thebardchat/TrojanHorseAreana/blueprints/phase2/out/pdf/P2-A-301_RevD.pdf

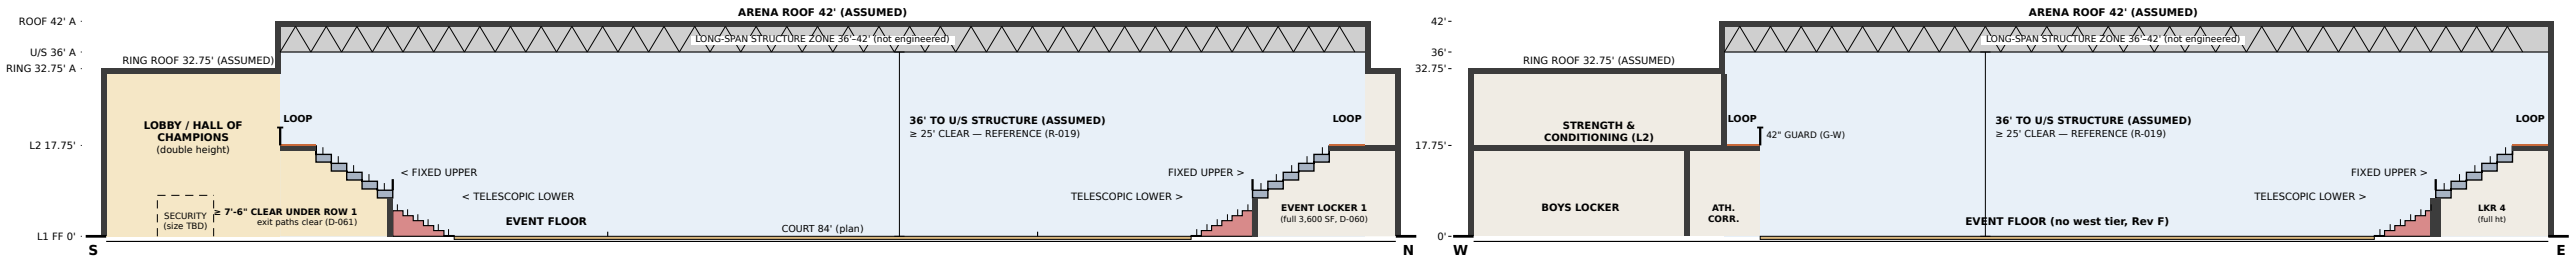
[picture p2: figure]
COURT 84' (plan) EVENT FLOOR; LOBBY / HALL OF CHAMPIONS (double height); SECURITY (size TBD); < TELESCOPIC LOWER; < FIXED UPPER; TELESCOPIC LOWER >; FIXED UPPER >; LOOP; EVENT LOCKER 1 (full 3,600 SF, D-060); ≥ 7'-6" CLEAR; UNDER ROW 1; exit paths clear (D-061); ARENA ROOF 42' (ASSUMED); RING ROOF 32.75' (ASSUMED); 36' TO U/S STRUCTURE (ASSUMED) ≥ 25' CLEAR — REFERENCE (R-019); RING 32.75' A; ROOF 42' A; EVENT FLOOR (no west tier, Rev F); BOYS LOCKER; ATH.; CORR.; STRENGTH & CONDITIONING (L2); LKR 4 (full ht); 42" GUARD (G-W)

# PRELIMINARY — CONCEPTUAL DESIGN — NOT FOR CONSTRUCTION

PROJECT

# Hazel Green Regional Athletic Complex Trojan Horse Arena · Hazel Green area, Madison County, Alabama (site TBD, D-006)

PHASE

# PHASE 2

SHEET TITLE

# BUILDING SECTIONS SCHEMATIC · COLOR

SCALE
AS

# NOTED

DATE

# October

2026

REV
D

DRAWN BY

## Drawn by KEYSTONE (AI) for Shane Brazelton

SHEET
P2-A-301

LONG-SPAN STRUCTURE ZONE 36'–42' (not engineered)

### 1 SECTION A-A (NORTH-SOUTH) — looking west

1/32" = 1'-0" · x = 100 (see key plan)

LONG-SPAN STRUCTURE ZONE 36'–42' (not engineered)

### 2 SECTION B-B (EAST-WEST) — looking north

1/32" = 1'-0" · y = 150 (see key plan)

L1 FF 0'

L2 17.75'

RING 32.75' A

U/S 36' A

ROOF 42' A

TELESCOPIC LOWER TIER (extended)

6 rows × 24" = 12' band (R-008 / plan)
rise 11⅝"/row — Hussey MAXAM option (CITED); choice of 11⅝" ASSUMED

top seat 6'-3⅛" (Hussey, 6 rows @ 11⅝")

closed 3'-6" (Hussey, 6 rows)

FIXED UPPER TIER (ASSUMED rake)

5 rows × 36" = 15' band (plan)
21"/row = 3 aisle risers × 7", 12" treads (IBC 1030.14.2: 4–8" risers, ≥ 11" treads) steps DOWN from the loop; front row 9.00'

≥ 26" fascia (1030.17.3)

LOOP 7'

2 × 42" lanes

top cross aisle

STRETCH
6' (L2)

NO LOW BAND (D-061, Option B): row 1 clear 7.5' = 7'-6" (1003.2,
no margin; 1.5' structure A)
rows 2–5 9.25'–14.5'

EVENT LOCKER 1 (full, D-060) from y 224 (tier line), A-101 Rev F

SIGHT LINES: P2-A-302 Rev C — 21"/row, L2 17'-9"

seated C min 149 mm N/S, 101 mm E (≥ 90 target)

EXIT (N) x 123.85–131.85: clear ≥ 7'-6" under row 1 (D-061)

1030.6.2.2 (only if smoke-protected): roof ≥ 15' above

highest aisle (loop 17.75') → ≥ 32.75'; 36' drawn

### 3 NORTH BOWL EDGE (ENLARGED PART OF A-A)

3/32" = 1'-0" · y 196–252 at x = 100

16 R @ 6.87" = 9.16'
15 T @ 11" = 13.75'

76" mid
landing

= width

(1011.6)

48" floor

landing

INTERMEDIATE HANDRAIL (C-7)

on the 76" centerline, 1014.9

— architect to confirm

L2 FF 17'-9"

+ flight 2: 15 R

L1 FF 0'

flight 2 beyond

(dashed)

31 risers total

76" clear width

(not visible in section)

### 4 TYPICAL EXIT STAIR — 76" CLEAR, 31 R

3/32" = 1'-0" · 76" mid landing · 12.67' × 24.08' plan (D-061)

A

A

B B

N

### 5 KEY PLAN — CUTS

1" = 128' · north up

CUT: slab / wall / roof (graphic) | ARENA VOLUME | EVENT FLOOR
TELESCOPIC LOWER TIER | FIXED UPPER TIER | LOOP (L2)
LOBBY | ROOMS / SUPPORT | LONG-SPAN STRUCTURE ZONE

HEIGHTS USED (ft above L1 FF 0'-0")
- L2 FF 17'-9" (D-061 DECIDED, Option B). Ring roof 32.75' = L2 + 15' — ASSUMED. Arena structure underside 36', roof 42' — ASSUMED (court clear unchanged).
- Arena clear ≥ 25' — REFERENCE (NFHS court specs via Draper; LA RAP gym standard; R-019), not a code minimum (C-5). 36' drawn = 11' over it.
- Slabs, walls, roof graphic only. Upper-tier deck structure 1.5' under each tread — ASSUMED.
SEATING (P2-A-101 Rev F)
- Lower: telescopic, 6 rows × 24", 11⅝" rise (Hussey MAXAM option, CITED; choice ASSUMED); east front 16' from the nearest mat (D-053); building 210' wide.
- Upper: fixed, 15' band, 5 rows × 36", 21"/row (D-061) = 3 aisle risers × 7", 12" treads (1030.14.2: 4–8", ≥ 11"); steps DOWN from the loop (D-049) to a 9.0' front row.
- UNDER THE UPPER TIER: row 1 clear 7.5' = 7'-6" (1003.2 minimum, no margin), rows 2–5 9.25'–14.5'. No low band: EXIT (N), EXIT (E), SE concourse, lobby / portal / athlete route are clear. Event lockers run to the tier line (3,600 SF, D-060).
- SIGHT LINES: P2-A-302 Rev C (21"/row, L2 17'-9"): seated C min 149 mm N/S, 101 mm E; standing 127 / 72 mm (lower tier governs).

GUARDS
- Loop open edges G-W (x = 56) and G-S (y = 34): 42" (IBC 2021 1015.2 / 1015.3). Upper-tier front fascia ≥ 26" (1030.17.3), 36" at aisle feet (1030.17.4).
STAIRS (ST-1..ST-4)
- 76" clear (D-052). 31 R @ 6.87" (213" ÷ 31, ≤ 7", 1011.5.2), flights 16 + 15, 15 treads × 11" = 13.75'; 76" intermediate landing = width (1011.6, D-051); 48" floor landings. Per stair 12.67' × 24.08' = 305.1 SF per level (Rev C 270.2).
- Intermediate handrail on the centerline of each 76" stair so all width is within 30" of a rail (IBC 2021 1014.9; D-052 'with intermediate handrails') — shown in detail 4; architect to confirm (C-7).
ROOF HEIGHT (1030.6.2.2, if smoke-protected)
- Lowest roof deck ≥ 15' above the highest aisle: loop 17.75' → ≥ 32.75'. Arena U/S structure 36' drawn = 3.25' margin (deck higher). Ring roof 32.75' is over the perimeter rooms, not the seating.
ELEVATOR
- EL-1 travel 17'-9" (was 15'); hoistway / pit / overrun by the elevator supplier (not drawn).
CUTS
- A-A: x = 100, looking west. B-B: y = 150, looking north. Geometry from P2-A-101/102 Rev F. Colors graphic only; 'A' = ASSUMED.
