thebardchat/TrojanHorseAreana/blueprints/DECISIONS.md

# DECISIONS — KEYSTONE

Status values: **OPEN** / **DECIDED** / **PARKED**.
When Shane answers, KEYSTONE records `DECIDED 2026-MM-DD — <answer> — "Shane, <channel>"` and updates the params file first.
Source for D-001…D-012: KEYSTONE_ARCHITECT_PROMPT.md v1.1 Section 5. D-013…D-015 logged by KEYSTONE at bootstrap, 2026-10-03. D-016…D-017 logged at the reference plan intake, 2026-10-03. D-009 DECIDED 2026-10-04 4:30 AM CT (Shane review of P2-A-101/102 Rev A).

## Phase 1 — existing wrestling room remodel

| ID | Question | Status | Notes / feeds |
|---|---|---|---|
| D-001 | Existing room dimensions, ceiling height, door locations, wall material (needs Shane's tape measure + photos) | OPEN | phase1.yaml `existing.*`. Checklist: phase1/MEASUREMENT_CHECKLIST.md. **Partial 2026-10-03:** wrestling room MEASURED: 55'-0" N-S × 45'-0" E-W inside, wall to wall, rectangle ("Shane tape, inside wall-to-wall, 2026-10-03") → `existing.wrestling_room.length_ft/width_ft`, drawn on P1-A-101 Rev A. The aerial estimate (≈55.1 × 46.9 ft exterior) agreed and stays a cross-check only. Door locations are APPROX. from the sketch only. **Still TBD:** support wing dims, door positions/widths, ceiling, wall material/thickness, photos. **10:12 PM CT (Shane):** ceiling 10'-0"; CMU building (8" walls ASSUMED unless noted); 4 doors ASSUMED standard 3'-0" × 7'-0" single HM, VERIFY (locations still APPROX.; south exit may be a pair). Dr. Headen has taken photos (copies requested) |
| D-002 | Where the plumbing fails, what fixtures exist, where water/drain lines run | OPEN | phase1.yaml `existing.plumbing`, work item W2. **Update 2026-10-03 (Shane, firsthand):** no running water to the area; all fixtures out of service; cause unknown. Still needed: plumber visit to diagnose (shutoff, supply line, or other), plus photos. **10:06 PM CT (Shane):** fixtures = 2 showers, 1 private toilet, 2 toilets, 1 urinal, sinks (count TBD), water fountain/sink, all out of service; problem spots = entire support wing (showers broken before the water loss); where = support wing east of the wrestling room, along the open hallway. Still TBD: cause, sink count, water/drain lines. **2026-10-04:** P1-P-001 Rev A shipped (scope narrative + fixture list only); does not close D-002 |
| D-003 | Which walls get pads, pad height, and whether pads are bought by the school, donated, or fundraised | DECIDED | DECIDED 2026-10-03 — Pad height 6 ft — "Shane, chat". This matches the R-001 guidance. Applied in phase1.yaml W1 `pad_height: 6 ft`. Earlier the same day the template came back unfilled, so 6 ft had only been proposed. **Which walls and who supplies the pads are not decided; they moved to D-021 (OPEN)** |
| D-004 | Who must approve work on school property (principal → district facilities → anyone else) | OPEN | phase1.yaml `approvals`. Legal/procurement advice is out of scope for KEYSTONE. **2026-10-03: R-002 + R-004 done.** Sources point to principal → MCSS Operations & Facilities → Board of Education (building/land improvements) → Alabama DCM review + inspections (any cost, any funding). Donated work: bid law may not apply to entirely private funds (AG opinions, via Examiners), but DCM review still does. **Needs district confirmation** before DECIDED |
| D-005 | Principal's name spelling (Headen or Hedden) | DECIDED | DECIDED 2026-10-03 — "Dr. Headen" — "Shane, firsthand 2026-10-03 10:12 PM CT". Stored in phase1.yaml `contacts.principal` (name, display_name). Used on P1-G-001 Rev D. Frozen Revs A/B/C unchanged |

## Phase 2 — new building + campus

| ID | Question | Status | Notes / feeds |
|---|---|---|---|
| D-006 | Site / parcel / address | OPEN | Campus drawn as SITE TBD diagram until decided |
| D-007 | Owner of record for the new building: Shane / Hazel Green Trojan Youth Wrestling / partnership | OPEN | Drives D-008 and R-006. **Updated 2026-10-03 10:45 PM CT (Shane):** Phase 2 is Shane's build, not a school project (D-028), so the school-system/county/town options were dropped from this question. phase2.yaml `open_items.owner_of_record` |
| D-008 | Authority Having Jurisdiction for permitting | OPEN | R-006. **R-006 done 2026-10-04 7:44 AM CT:** Hazel Green is unincorporated → Madison County Inspection Department (if the parcel stays outside city limits); county enforces 2018 IBC / IFC / NFPA 101 (no change planned within 12 months), State Fire Marshal 2021 IFC; DCM (State Building Code, 2021 IBC) covers private buildings only if 25+ persons regularly gather "for instruction" — ask DCM / county; assembly needs a registered architect. Still OPEN (site D-006 + pre-application meeting). **Note 2026-10-03 (P2-T-003b):** Madison County's Building Codes page lists the 2018 IBC/IPC (effective Jan 2021) for county permits; Shane said 2021. The test-fit used 2021; its fixture table reads the same in 2018. Depends on the site (D-006). **10:15 AM CT (reviewer C-6):** edition conflict still OPEN — county on 2018 codes vs State Fire Marshal 2021 (R-006). P1-G-001 Rev E prints '2021 ASSUMED, verify with AHJ' (plain words, no codes); Phase 2 sheets keep 2021 as ASSUMED until the AHJ answers |
| D-009 | Seating type (fixed, telescopic) and final count | DECIDED | DECIDED 2026-10-04 — MIX: telescopic lower tier, fixed upper tier — "Shane, firsthand, 4:30 AM CT". Total stays 2,200 (locked; D-016 label question still OPEN), seats on N, S, E only (west = lockers + athlete corridor), 50/50 tier split ASSUMED (1,100 + 1,100). phase2.yaml `spaces.seating.type` MIX, `lower_tier_type: telescopic`, `upper_tier_type: fixed` (locked in validate.py). P2-G-003 Rev E (Rev D frozen): telescopic 3.38 SF/seat lower, fixed 6.0 SF/seat upper, same 1.25 gross-up → L1 gross 51,108, L2 gross 25,981, footprint 51,130 (arena volume + L2 governs) = 3,870 SF under 55,000 (target ≥ 2,000 met); 77,089 GSF. Block box shrinks 250 × 220 → 204 × 252 ft = 51,408 SF (3,592 under the cap). Seats by side: N 353 + 308 = 661, S 341 + 308 = 649, E 406 + 484 = 890 (lower 1,100 + upper 1,100 = 2,200). Earlier note: concept sheet shows 2,200; diorama text "Permanent stadium seating" not treated as a decision; Rev D compared fixed 54,949 vs telescopic 50,868 |
| D-010 | Locker room parity (equal SF?) | OPEN | See D-013 |
| D-011 | Concessions scope | OPEN | |
| D-012 | Any budget target for Phase 2 | OPEN | Do not reuse the superseded Feb 2026 concept budget |

## Logged at bootstrap (2026-10-03)

| ID | Question | Status | Notes / feeds |
|---|---|---|---|
| D-013 | Girls locker 3,503 SF vs boys 3,500 SF. Real difference, or a drawing-tag slip? | OPEN | Prompt §3 says this is likely a tag slip. **Draw both lockers equal until Shane decides.** Also, the intake says AI renders show girls as 3,500 |
| D-014 | Mat size check: concept notes say "four 42-foot mats ≈ 7,000 SF." Check against current NFHS rules (mat, circle, safety area, spacing) before laying out mats | DECIDED | DECIDED 2026-10-03 — mats are 42' × 42' — "Shane, 10:45 PM CT". R-005: meets the NFHS 28 ft minimum circle + ~5 ft safety area. Applied in phase2.yaml `spaces.arena.mat_size`. Design events → D-029 |
| D-015 | The intake file `KEYSTONE_INTAKE_2026-10-03.md` starts with "MOVIE MAKER INTAKE," but everything in it is for KEYSTONE. Label slip? | OPEN | KEYSTONE treated the content as its own intake. Shane, please confirm |

## Logged at reference plan intake (2026-10-03)

| ID | Question | Status | Notes / feeds |
|---|---|---|---|
| D-016 | Reference plan seating labels: north bank 3,200, south bank 2,200. Locked: 2,200 total (Shane 2026-10-03). Which label is wrong, and is 2,200 the total or per bank? | OPEN | phase2.yaml `spaces.seating`. The reference plan legend also says "Arena Capacity: 2,200 Spectators." The tabletop render swaps the two labels. Keep 2,200 total until Shane answers |
| D-017 | Which image is the Phase 2 reference plan, and what may be taken from it? | DECIDED | DECIDED 2026-10-03 — Phase 2 reference plan = Phase2-floor-plan-flat.png; use zones, adjacencies, 5 SF tags, room list; ignore dimension strings, scale bar, garbled text, green/gold legend — "Shane, chat". Diorama demoted to secondary; `Phase2-floor-plan.jpeg` is presentation only, not a source |
| D-018 | Promote rooftop solar + stormwater storage into Phase 2? Retractable roof? | DECIDED | DECIDED 2026-10-03 — Solar + stormwater storage promoted to Phase 2 as design intent only (no sizes, panel counts, or gallons until a cited R-file sizes them for this building). Retractable roof CUT. — "CHANGE APPROVED", Shane, chat. Applied in phase2.yaml `sustainability` |

## Logged at R-001/R-003 approval (2026-10-03)

| ID | Question | Status | Notes / feeds |
|---|---|---|---|
| D-019 | Must both new athlete restrooms (1 male + 1 female, single-user) meet full 2010 ADA, or only some (2010 ADA 213.2 Exception 4)? | DECIDED | DECIDED 2026-10-03 — Full 2010 ADA compliance on BOTH new restrooms — "Shane, chat". Resolves the R-003 Exception 4 question. Applied in phase1.yaml W3 + `standards.ada_single_user_restroom.both_rooms_comply` |
| D-020 | Wall pad fire-test wording on the scope sheet | DECIDED | DECIDED 2026-10-03 — Scope sheet must include, verbatim: "Wall pads must have an NFPA 286 assembly test report — not a foam-only rating. Ask the vendor before purchase." — "Shane, chat". Applied in phase1.yaml W1 `purchase_note` (basis: R-001) |
| D-021 | Which walls get pads, and whether pads are bought by the school, donated, or fundraised (the rest of D-003 after pad height was decided) | OPEN | Split from D-003 on 2026-10-03. phase1.yaml W1 `walls`, `supplied_by`, `funding.pad_funding`. Walls need Shane's measurements + photos (D-001). 2026-10-03: Shane's pad estimate (revised 10:12 PM CT: ~188 LF after 4 doors, ~94 panels at 2×6 ft) assumes all 4 walls; which walls is still OPEN |
| D-022 | Split Phase 1 into 1A (wall pads — may be maintenance, ask facilities) and 1B (plumbing + restrooms — licensed designer + DCM review likely)? | OPEN | Logged 2026-10-03 at Shane's request ("Shane, chat"). Do NOT restructure backlog, params, or sheets until Shane decides. Feeds from R-002/R-004 |
| D-023 | Is P1-G-001 Rev B approved for the principal, and does Shane's contact info stay on it in the public repo? | DECIDED | DECIDED 2026-10-03 — Rev B approved as-is; contact info stays (already public); no history rewrite — "Shane, chat" |
| D-024 | Priority order of the three Phase 1 work items | DECIDED | DECIDED 2026-10-03 — W2 (restore water) first → W3 (restroom split) second → W1 (wall pads) third; W1 can run in parallel because it doesn't depend on water — "Shane, firsthand 2026-10-03". Applied as phase1.yaml `work_items[].priority` and on P1-G-001 Rev C. Does not decide D-022 (1A/1B split) |
| D-025 | Is P1-G-001 Rev D (principal version) approved? | DECIDED | DECIDED 2026-10-03 — Rev D approved — "Shane, 10:29 PM CT". Frozen (`frozen: true`); committed PDF/DXF unchanged. Bundled first in Phase1_Package_for_Dr_Headen.pdf |
| D-026 | Is P1-A-101 Rev A (existing conditions, room outline) approved, and are the door marks right? | DECIDED | DECIDED 2026-10-03 — Rev A approved; door locations match Shane's markup; exits swing out (correct) — "Shane, 10:29 PM CT". Hallway door swing and south exit single/pair were left unfilled → stay "assumed, verify" (no sheet change). Frozen; committed PDF/DXF unchanged |

## Logged 2026-10-03 10:45 PM CT (Phase 2 active)

| ID | Question | Status | Notes / feeds |
|---|---|---|---|
| D-027 | Does Phase 2 wait for Phase 1 to finish? | DECIDED | DECIDED 2026-10-03 — Phase 2 is ACTIVE now, in parallel with Phase 1. Phase 1 package delivered; Phase 1 waits on Dr. Headen. When Shane brings Phase 1 data, Phase 1 tickets jump the line (Phase 1 still outranks when its data exists) — "Shane, 10:45 PM CT". Applied in BACKLOG priority note, STATUS, README, phase2.yaml meta |
| D-028 | Is Phase 2 a school project? | DECIDED | DECIDED 2026-10-03 — No. Phase 2 is Shane's build; it may not involve Dr. Headen. No school ownership, district approval, school review or school bidding is assumed for Phase 2 — "Shane, 10:45 PM CT". Owner of record stays OPEN (D-007). phase2.yaml had no school-derived entries to remove; locked facts kept |
| D-029 | What events is the Phase 2 arena designed for? | DECIDED | DECIDED 2026-10-03 — home duals + AHSAA / regional tournaments — "Shane, 10:45 PM CT". phase2.yaml `spaces.arena.design_events` |
| D-030 | Program direction (two levels, footprint cap D-031). Shane's direction under study (11:26 PM CT): keep ≈ 2,200 spectators with rentable suites just above the top seats. P2-G-003 Rev C (base inputs): at the locked 22,000 SF floor, suites cannot reach 2,200 inside 55,000 (most that fits ≈ 1,640 = 1,180 bowl + 23 suites × 20); an 18,000 SF floor fits 1,940 bowl + 13-22 suites (12-20 guests) ≈ 2,200, footprint ≈ 54,994, ≈ 92,300-92,900 GSF, 3 levels (suite level). Which way: a) 18,000 SF floor + suites (3 levels), b) 16,400 SF floor, all 2,200 in the bowl, no suites (2 levels), c) keep 22,000 SF on lean inputs (telescopic lower tier), no suites (2 levels), or d) another mix? | DECIDED | DECIDED 2026-10-03 — 16,400 SF event floor, all 2,200 seats in the bowl, 2 levels, no suites — "Shane, firsthand, 11:39 PM CT". Suites → PARKING_LOT (future add-on, study after attendance is proven). Seating type (fixed vs telescopic) stays OPEN (D-009); plans show both as an overlay. phase2.yaml locked: `spaces.arena.event_floor_sf: 16400` (drawn 114 × 144 ft = 16,416), 4 × 42 ft mats 2 × 2 (`mat_ft`, `mat_layout`), `seating.bowl: 2200`, `building.levels: 2`, S&C + cross-training `level: 2` over the lockers; the 22,000 SF tag is SUPERSEDED for the event floor and kept as history (`sf_tagged_superseded`). P2-G-003 Rev D = LOCKED PROGRAM sheet (Rev C frozen). Feeds P2-T-004 (P2-A-101 Level 1, P2-A-102 Level 2) |

## Logged 2026-10-03 11:09 PM CT

| ID | Question | Status | Notes / feeds |
|---|---|---|---|
| D-031 | Is the 55,000 SF a cap on total floor area or on the building footprint? | SUPERSEDED | **RETIRED 2026-10-04 by D-056 — there is NO 55,000 SF cap (footprint or total); 55,000 SF was an early rough estimate, not a limit ("Shane, Grok chat", 8:36 AM CT).** History: DECIDED 2026-10-03 — 55,000 SF is a FOOTPRINT cap that could allow two levels; it is not a total floor area cap — "Shane, firsthand, 11:09 PM CT". phase2.yaml `building.footprint_cap_sf: 55000`, `levels: up to 2`, `total_gsf_cap: none` (locked `total_sf: 55000` kept, meaning noted). Test-fit redone as P2-G-003 Rev B; Rev A frozen. D-030 stays OPEN |

## Logged 2026-10-03 11:26 PM CT

| ID | Question | Status | Notes / feeds |
|---|---|---|---|
| D-032 | Keep the 22,000 SF floor and drop to ≈ 1,370 seats (P2-G-003 Rev B option)? | DECIDED | DECIDED 2026-10-03 — No. Shane rejects the ≈ 1,370-seat option ("not enough") — "Shane, firsthand, 11:26 PM CT". His direction (suites just above the top seats to keep ≈ 2,200 spectators) is recorded under D-030, which stays OPEN until he picks. phase2.yaml `spaces.seating.rejected_option`, `suites_direction` |

## Logged 2026-10-04 4:43 AM CT

| ID | Question | Status | Notes / feeds |
|---|---|---|---|
| D-033 | Access control: how do people (public, teams, staff) enter the arena? | DECIDED | DECIDED 2026-10-04 — single controlled entry point for all people (public, teams, staff): "Everyone passes through the grand entrance; it will serve as a checkpoint, a security feature." — "Shane, firsthand, 4:43 AM CT". phase2.yaml `spaces.entry.access_control` (v7). P2-A-101/102 Rev C (Rev B frozen): SW team / service entry removed; SECURITY CHECKPOINT (size TBD, ASSUMED) between the vestibule and lobby; CD-1 controlled door off the lobby → athlete route → team assembly / athlete corridor / lockers; all other perimeter doors X1-X10 EXIT ONLY — alarmed, no exterior entry hardware (IBC 2021 1010.2, 1010.2.7 exc. 1, 1010.2.9; 2018 1010.1.9, 1010.1.10; no delayed egress in Group A, 1010.2.13). Exits kept per R-015 / R-015.6: 4 per story (T1006.3.3), main exit ≥ 1/2 occupant load (1030.2), other exits ≥ 1/2 (1030.3); checkpoint may not narrow the main exit (1003.6, 1010.5). Program unchanged (P2-G-003 Rev E stands) |
| D-034 | Deliveries and team buses under the single-entry rule (D-033): where do trucks unload mats / equipment and concessions, and where do team buses drop athletes and gear? Rev C shows S1 SERVICE / LOADING at equipment storage (north wall) — staff-controlled, not a people entrance — and teams walking in through the grand entrance. Options: a) staff-only service door as drawn, deliveries scheduled outside event hours; b) a screened service / loading entrance with its own checkpoint; c) other | DECIDED | **DECIDED 2026-10-04 (default, refine on the site plan)** — service / deliveries at the **north door S1** (staff-controlled service door, option a); **team / bus drop loop on the SOUTH**, offset **east or west** of the entry axis so it does not block the view of the Grand Entrance Portal — "Shane, firsthand, 6:45 AM CT". Side (E or W), loop size and lanes TBD on the site plan (C-101, P2-T-006; site TBD, D-006). Logged in `phase2.yaml approach.site_access`. Earlier note: no sizes set (dock, door, apron, bus lane all TBD; site TBD, D-006). Feeds P2-A-101 (S1), C-101 campus diagram (P2-T-006), D-011 concessions scope |

## Logged 2026-10-04 4:55 AM CT

| ID | Question | Status | Notes / feeds |
|---|---|---|---|
| D-035 | Should Level 2 have a complete, continuous walkway / running-training loop around the top, and what gives up space for it? | DECIDED | DECIDED 2026-10-04 — continuous L2 running / training loop joining the rear walkway (N), walkway (E) and upper concourse / hall of champions balcony (S); S&C and cross-training reduced to fit — "Shane, firsthand, 4:55 AM CT". Shane wrote "eastside", but rooms 17 and 18 sit on the west, so the new leg runs along their arena-side (east) edge. phase2.yaml v8: `spaces.strength_conditioning.sf` 6,000 → **5,224**, `spaces.cross_training.sf` 4,000 → **3,500** (old values kept as `sf_tagged_superseded` for frozen revisions), new `spaces.training_loop`. Loop = 2 lanes x 42 in = 7 ft all around (lane width UFC 4-740-02N 4.1.7 / Athletic Business, R-017; 2 lanes ASSUMED, guides prefer 3), squared corners, 706 ft centerline, 7.48 laps/mile, 4,942 SF. 42 in guards at open edges (IBC 2021 1015.2, 1015.3). Event days: upper concourse (spectators cross at tier entries). P2-A-101/102 Rev D (ST-1 3.55 ft W, ST-2 into a 19 x 5 ft NE stair tower, elevator 1 ft S); P2-G-003 Rev F footprint 52,738, margin 2,262, 78,784 GSF |

## Logged 2026-10-04 5:27 AM CT

| ID | Question | Status | Notes / feeds |
|---|---|---|---|
| D-036 | Are P2-A-101/102 Rev D and P2-G-003 Rev F approved as the Phase 2 schematic baseline? | DECIDED | DECIDED 2026-10-04 — "P2-A-101/102 Rev D + P2-G-003 Rev F approved. Entry south-center, mech off the public side, mixed seating, 2,262 margin — all good." — "Shane, firsthand, 5:27 AM CT". Frozen as **Phase 2 Schematic Set Rev A** (phase2.yaml `sets.phase2_schematic_set_rev_a`; bundle `phase2/out/pdf/Phase2_Schematic_Set_RevA.pdf`, `p2_set.py`; git tag `p2-schematic-revA`). P2-A-101 Rev D was re-issued label-only for D-039 before the freeze. Confirms D-009 (MIX), D-033 (south-center entry), footprint margin 2,262 SF (P2-G-003 Rev F). |
| D-037 | Level 2 running / training loop width | DECIDED | DECIDED 2026-10-04 "for now" — 2 lanes x 42 in = 7 ft (D-035 geometry unchanged) — "Shane, firsthand, 5:27 AM CT". Revisit only through D-038. |
| D-038 | Upper concourse width vs egress calc — if code requires wider, go to 3 lanes (10.5 ft). | DECIDED | **CLOSED 2026-10-04 — exit stairs 70 in clear** (each of ST-1..ST-4) — "Shane, firsthand, 6:45 AM CT". R-018.8 recheck at 70 in: 4 x 70 = 280 in vs 255.8 in base (+24.2), 275.6 in with the loop counted (+4.4), 272.6 in with rail standing (+7.4); both together 292.4 in (12.4 in short — AHJ / architect). Loop stays 7 ft (2 lanes, D-037). Affects **P2-A-101 / P2-A-102 at their next revision** (stair ≈ 11.67 x 19 ft, ≈ +16.5 SF per stair per level); the frozen Phase 2 Schematic Set Rev A stays frozen. Shown on P2-A-301 Rev A (typical stair). Earlier note: opened by Shane 2026-10-04 5:27 AM CT. R-018 (IBC 2021 Ch. 10 via UpCodes; 2018 = 1029.x, UNVERIFIED): L2 load 1,279; loop at 0.2 in/occupant needs 64 in (balanced, 1030.9.2) / 79.2 in (unbalanced check) vs 84 in drawn → **code does not require > 7 ft on KEYSTONE's calc**; 10.5 ft (126 in) would also satisfy it. Thin margin: keep the 7 ft clear, recess room doors. Stairs 4 x 64 in = zero slack (≈ 68-69 in if the AHJ counts the loop or rail standing). Needs architect egress model + AHJ (D-008). Frozen set unchanged. |
| D-039 | West unprogrammed space on Level 1 (team assembly ≈ 2,072 SF, storage SW 1,011 SF): keep or change? | DECIDED | DECIDED 2026-10-04 — keep as-is, labeled FLEX — "Shane, 5:27 AM CT". His message left the template bracket "keep as-is, labeled flex — [or: change to ___]"; KEYSTONE took the stated default (KEEP AS-IS) and did not invent a change. Labels: "FLEX / TEAM ASSEMBLY", "FLEX / STORAGE" (P2-A-101 Rev D label-only re-issue before the freeze; geometry, areas and DXF non-text entities unchanged). |
| D-040 | Brand / signage on the south portal and arena faces: does the Hazel Green High School (HGHS) badge belong, or Shane's own complex brand? | DECIDED | Opened by KEYSTONE 2026-10-04 for P2-A-201. Phase 2 is Shane's build, not a school project (D-028), so no school logo is drawn; placeholder "BRAND / SIGNAGE — TBD" in brand red / black. Portal look (limestone arch, crimson inside the arch, gold soffit) from Shane's MOVIE MAKER arch render (`/workspace/trojan-horse-arena/assets/arch_src.png`, box only). Needs Shane. **CLOSED 2026-10-04 6:16 AM CT by D-041:** the portal carries the official Trojan Horse Arena mark, not the HGHS badge (Shane, firsthand). |

## Logged 2026-10-04 6:16 AM CT

| ID | Question | Status | Notes / feeds |
|---|---|---|---|
| D-041 | What is the official Trojan Horse Arena mark? | DECIDED | DECIDED 2026-10-04 — "OFFICIAL MARK — circular horse-head badge with Greek key border." — "Shane, firsthand, 6:16 AM CT". Files: `brand/THA_logo_black.svg` (#1A1A1A), `brand/THA_logo_red.svg` (#CC0000), `brand/THA_logo_white.svg` (#FFFFFF) — copies of his Desktop\ARENA THA_logo_*.svg, colour identified by fill; sha256 in ASSETS. **Supersedes logo Concepts 01 / 02** (kept as history, marked SUPERSEDED, nothing deleted; those concept files are not in the repo or on the KEYSTONE box). Closes D-040: the portal carries this mark, not the HGHS badge. phase2.yaml `brand.official_mark` (v10). P2-A-201 Rev B (Rev A frozen): mark Ø 6 ft above the arch + TROJAN HORSE ARENA wordmark + side panel "Hazel Green Regional Athletic Complex" (sizes ASSUMED). |
| D-042 | Trademark search before signage / apparel. | OPEN | Opened by Shane 2026-10-04 6:16 AM CT. Clearance search for the Trojan Horse Arena name and mark before any signage, apparel or merchandise is produced (Shane / his attorney; KEYSTONE gives no legal advice). Feeds P2-A-201 signage, any brand use. |

## Logged 2026-10-04 6:22 AM CT

| ID | Question | Status | Notes / feeds |
|---|---|---|---|
| D-043 | Is the Grand Entrance Portal attached to the building, and what is the approach? | DECIDED | DECIDED 2026-10-04 — the Grand Entrance Portal is a **FREESTANDING** structure, not attached to the building; it sits just before the south entrance, on the way in, straddling the **Champion Walk** walkway; the walkway is **brick** so sponsors / donors can have their names on engraved bricks — "Shane, firsthand, 6:22 AM CT". Reference photo `references/portal_freestanding_champion_walk_ref.png` (freestanding limestone arch, crimson soffit, paved promenade, low walls / planters; sha256 in ASSETS). P2-A-201 Rev B: portal drawn free in front of the south entrance (gap 30 ft and depth 6 ft ASSUMED, labeled), Champion Walk brick paving + key plan, note "Engraved donor / sponsor bricks". **Next A-101 revision must add the portal + Champion Walk to the site / Level 1 plan** — not done now: P2-A-101 Rev D stays frozen in Phase 2 Schematic Set Rev A. |
| D-044 | Champion Walk: length, width, and donor-brick program details (brick sizes, engraving, pricing tiers, who administers, layout). | OPEN | **Narrowed 2026-10-04 6:45 AM CT to PRICING (and who administers / engraving):** dimensions and brick tiers are DECIDED in D-046 (28 x 30 ft, 4x8 single name / 8x8 family-business). Pricing TBD (Shane). Earlier note: opened 2026-10-04 6:22 AM CT (Shane's instruction). Drawn width 28 ft (= arch opening) is ASSUMED; length TBD; portal setback TBD (30 ft ASSUMED on P2-A-201 Rev B). Needs Shane; then the site plan (next A-101 revision). **Input 2026-10-04 7:24 AM CT:** Shane's vendor cost sheet (PDF "Champion_Walk_Brick_Pricing", 2026 prices incl. engraving + shipping, pulled 2026-10-04; not re-verified by KEYSTONE): average **$19.17 per 4x8** (Fundraising Brick $19.00, Polar Engraving $19.50, That's My Brick $19.00 at 101+) and **$29.50 per 8x8** ($30.00 / $27.50 / $31.00); logo +$6. KEYSTONE arithmetic: ~3,700 x $19.17 ≈ **$70.9k** vendor cost if all 4x8 — excludes install and the sand / concrete base (Phase 2 site work). Donor pricing still OPEN. **10:18 AM CT: R-023** vendor cost only (Shane's sheet, REFERENCE): all 4x8 3,780 = $71,820–$73,710; all 8x8 1,890 = $51,975–$58,590; 80/20 by area (ASSUMED) 3,402 = $68,796–$69,363; logo +$6 each. Break-even 4x8 $19.00–$19.50, 8x8 $27.50–$31.00 (vendor cost only). Install, base, border not included / not estimated. Pricing stays OPEN |

## Logged 2026-10-04 6:45 AM CT

| ID | Question | Status | Notes / feeds |
|---|---|---|---|
| D-045 | Grand Entrance Portal arch underside: crimson or gold? | DECIDED | DECIDED 2026-10-04 — **arch underside crimson + gold trim, as drawn** on P2-A-201 Rev B — "Shane, firsthand, 6:45 AM CT". Kept on Rev C. Finish / material TBD. |
| D-046 | Champion Walk size and brick tiers | DECIDED | DECIDED 2026-10-04 "for now" — **28 ft wide x 30 ft long (portal to the E1 doors) = 840 SF**; brick tiers **4x8 = single name**, **8x8 = family / business**; pricing TBD (D-044) — "Shane, firsthand, 6:45 AM CT". Capacity ≈ **3,700 4x8 bricks**: basis 840 SF ÷ 0.222 SF (4 x 8 in = 32 sq in) = 3,780 gross, less border / edging and joints (nominal face size; no border width set — about 2 % off gives ~3,700; ASSUMED). Any 8x8 brick takes the place of two 4x8. Option to **extend the walk to the parking later** (dashed on the key plan). Portal stands 30 ft in front of the doors (= walk length). Shown on P2-A-201 Rev C key plan + notes. **Next A-101 revision adds the walk + portal to the site / Level 1 plan.** |
| D-047 | Portal badge size (Shane picked from the 10-12 ft range) | DECIDED | DECIDED 2026-10-04 — **official mark 11 ft diameter** on the portal, wordmark to match, nothing may overflow — "Shane, firsthand, 6:45 AM CT". KEYSTONE fit (P2-A-201 Rev C): badge 40.4-51.4 ft above grade; to fit it with the wordmark above it inside the 44 ft wide portal, the **portal / attic was raised 50 → 56 ft (ASSUMED)** [superseded 7:24 AM CT by D-050: portal ≤ 50 ft, crown lowered to 34 ft] (attic band 42-56 ft; width 44, opening 28, springline 26, crown 40 unchanged). Wordmark caps 27 in (was 18 in): proportional scaling (2.75 ft caps) would make the line 47.9 ft, wider than the 44 ft portal, so caps are held at 27 in (39.1 ft line). Confirm the 56 ft height. |
| D-048 | Arch reference photo (`portal_freestanding_champion_walk_ref.png`): AI-made (keep in the repo) or from the internet (remove)? | DECIDED | **CLOSED 2026-10-04 7:24 AM CT — Shane made the image himself (rights clear); the removal stands, no history rewrite; kept off-repo by choice** — "Shane, firsthand, 7:24 AM CT". ASSETS: "Shane's own image; held off-repo by choice" (box copy unchanged, same sha256). Earlier note: Opened 2026-10-04 6:45 AM CT — Shane's answer came back as the unfilled template bracket. Safe default applied: **removed from the repo** (`git rm`, history not rewritten — the file stays in earlier commits of this public repo) and **held off-repo pending rights confirmation from Shane** (box copy `/workspace/keystone_previews/refs/`, sha256 in ASSETS). If AI-made → restore to `references/`; if from the internet → stays off-repo (rights / licence needed before any use). |

## Logged 2026-10-04 7:24 AM CT

| ID | Question | Status | Notes / feeds |
|---|---|---|---|
| D-049 | Upper tier rake direction and the use of the space under it | DECIDED | DECIDED 2026-10-04 — **the upper tier steps DOWN from the L2 loop toward the court, as drawn** (P2-A-301). **Under its low front edge: telescopic stack, storage, mechanical. Lockers only where headroom is full** — "Shane, firsthand, 7:24 AM CT". KEYSTONE reading (ASSUMED): "full headroom" = under the flat L2 slab behind the tier back line. Frozen Rev D plan overlaps under the tier (SF under tier / full-height SF): Event Lockers 1–2 482 / 418 each, 3–4 614 / 286 each; Mech E 1,173, Mech N 315, Equip storage 375, Equip room 161 (fine); lobby 870, concession 225, women's RR 207, athlete route 224, Conc W 196, Conc E 480; EXIT N and EXIT E passages 120 each (need ≥ 7'-6", 1003.2 → front structure ≤ 20 in at 9.17 ft, or a local raise). **Event lockers re-planned at the next A-101/A-102 revision.** Stack check (P2-A-302, R-020): a closed stack recessed under the front fits only if the structure is ≤ 32.6 in, and when open its rear rows sit under the overhang with < 7'-6" → **keep the stack in front of the tier face**; the low zone = storage / mech. |
| D-050 | Portal height cap and arch | DECIDED | DECIDED 2026-10-04 — **portal must NOT exceed 50 ft** (arena roof 42 ft); lower the arch crown 40 → ~34 ft, springline proportional (ASSUMED) so the 11 ft badge + wordmark fit — "Shane, firsthand, 7:24 AM CT". Supersedes D-047's 56 ft raise (badge stays 11 ft). P2-A-201 Rev D: **portal 50 ft**, crown **34 ft**, springline **22.1 ft** (26 x 34/40), semi-elliptical arch rise 11.9 ft over the 28 ft opening (ASSUMED; a semicircle with a 34 ft crown would need a 20 ft springline), attic band 36–50 ft, **badge 34.4–45.4 ft**, wordmark 27 in caps **baseline 46.1 ft, caps top 48.35 ft**, under the 48.8–50 ft cornice. |
| D-051 | Switchback stair intermediate landing depth | DECIDED | DECIDED 2026-10-04 — **intermediate landing ≥ stair width = 70 in** (IBC 2021 1011.6) — "Shane, firsthand, 7:24 AM CT". Floor landings 48 in. Per stair per level (clear): **11.67 ft x 20.83 ft = 243.1 SF** (2 x 70 in by 48 + 132 + 70 in; Shane's estimate ~11.67 x ~21 ft) vs **205.2 SF** in the frozen A-101/A-102 (10.8 x 19 ft) → **+37.9 SF per stair per level, +151.4 SF per level, ≈ +303 GSF** (4 stairs x 2 levels) — **apply at the next A-101/A-102 revision**. P2-A-301 Rev B detail 4. Supersedes the 221.7 SF estimate in R-018.8 (48 in landing). |
| D-052 | Egress worst case (loop counted + rail standing, 1,462 occupants → 292.4 in at 0.2 in/occ., IBC 2021 1005.3.1 exc. 1): how to add 12.4 in? | DECIDED | **DECIDED 2026-10-04 7:49 AM CT — 4 exit stairs at 76 in clear with intermediate handrails** (worst case passes: 304 in vs 292.4, ≈ 11.6 in spare; ≈ 12.67 x 21.33 ft per stair per level) — "Shane, firsthand, 7:49 AM CT". **Applies at the next A-101/A-102/A-301 revision** (frozen sheets stay frozen); shown on P2-C-101 Rev A. Earlier note: **PROPOSED by KEYSTONE 2026-10-04 7:24 AM CT (Shane asked for a recommendation, R-018.9): four stairs at 76 in clear** with intermediate handrails (1014.9) → 304 in (+11.6 in spare, serves 1,520); each ≈ 12.67 x 21.33 ft = 270.2 SF per level, **+217.8 GSF vs 70 in** (≈ +520 GSF vs the frozen plan). Alternatives: 74 in (296 in, +3.6 in, +144 GSF); 78 in (312 in, +291 GSF); a **5th stair** at 44 in (324 in, +273.8 GSF plus a new core, exit door, discharge, separation / travel checks; at 70 in +486 GSF); operational (no rail standing: 275.6 in, passes by 4.4 in — not worst case). Plans not redrawn. Needs Shane; architect / AHJ confirm. |
| D-053 | Sight lines: upper tier fails (14 in risers) and the east side fails (10 ft focal) — which fix? | DECIDED | **DECIDED 2026-10-04 7:44 AM CT — APPROVED: upper-tier risers 19 in (front row 7.08 ft) AND east seats moved 6 ft further from the mats (+≈1,512 SF)** — "Shane, firsthand, 7:44 AM CT". **Applies at the next A-101/A-102/A-301 revision** (frozen sheets stay frozen). Size with the shift + 76 in stairs (D-052), drawn basis: **L1 footprint 53,026.7 / L2 28,878.7 / TOTAL GSF 81,905.3 SF** (R-021); program-basis estimate 54,588.9 SF footprint. (Margin language retired by D-056.) Earlier note: **PROPOSED by KEYSTONE 2026-10-04 7:24 AM CT (P2-A-302 Rev A, R-020): upper riser 19 in per row** (3 aisle risers of 6⅓ in; front row drops 9.17 → 7.08 ft, back stays at the loop) **+ move the east tier 6 ft further from the mats (10 → 16 ft clear)** → every seated row ≥ 101 mm (PASS ≥ 90), standing ≥ 72 (east marginal). As drawn: upper seated 40–49 mm N/S, negative east; east lower 46–74 seated. Cost: +6 ft east-west ≈ +1,512 SF footprint (still < 55,000) or take 6 ft from the east support zone; the lower front makes exits under the tier front harder (7'-6", D-049). Alternatives: accept lower C on the east side; 16 in upper (passes N/S only). Needs Shane before more seating detail. |

## Logged 2026-10-04 7:44 AM CT

| ID | Question | Status | Notes / feeds |
|---|---|---|---|
| D-054 | Event floor uses beyond sports (concerts, graduations, expos with floor chairs or standing)? | DECIDED | Opened by KEYSTONE 2026-10-04 (R-007.2). The floor (114 x 144 ft = 16,416 SF) is counted at 50 gross ("exercise rooms", ASSUMED) → 329 occupants. IBC 2021 Table 1004.5 if used otherwise: unconcentrated 15 net → 1,095; chairs only 7 net → 2,346; standing 5 net → 3,284. Changes Level 1 exits / main exit (1030.2) and fixtures, not the L2 stairs (D-052). Needs Shane (intended uses); the building official assigns the load. **2026-10-04 10:48 AM CT (Shane): design L1 exits to PASS the worst case (standing), other cases shown alongside.** P2-G-002 Rev A finding: with door widths ASSUMED (11 pairs × 64 in = 704 in), the worst case is SHORT (total 933.0 in, main exit E1 466.5 in vs 64 in). Options 1 (E1 bank of 8 pairs) / 2 (distributed exits, +4 pairs) in G-002 §10. L1 fixtures in the standing case: 26 men's / 50 women's WC (vs 10 / 18). Still OPEN. **2026-10-04 11:07 AM CT (Shane): DECIDED — Level 1 exits Option 1: an 8-pair door bank at E1 across the lobby's 58 ft south wall (512 in clear, 64 in per pair ASSUMED); keep the single controlled entry (D-033).** Exits are sized for the standing worst case: P2-A-111 Rev A — total 1,152 in vs 933.0 needed, E1 512 vs 466.5 (1030.2), other L1 exits 420.7 vs 356.8 (1030.3), lose E1 640 vs 466.5 (1005.5): all PASS; whole drawn floor zone 17,280 SF standing also passes (E1 479.4). Drawn on P2-A-101 Rev G (vestibule widened, first aid moved, ASSUMED). Floor use itself stays OPEN; findings D-064 (restrooms) and D-065 (checkpoint). **2026-10-04 1:22 PM CT (Shane): DECIDED — event floor = CHAIRS-ONLY (7 net, 16,416 SF → 2,346 on the floor): graduations, banquets, expos yes; no standing-concert design. Keep the L1 exits as drawn for standing (extra margin, no change).** Design case = chairs (L1 3,827 incl. the 7-occupant storage annex + L2 1,462 = 5,289; E1 needs 396.7 in vs 512; standing margin case 6,227 → 467.0 in). Post the occupant load per configuration (IBC 2021 1004.9): sports 329 / tables 1,095 / chairs 2,346 on the floor. P2-G-002 Rev B, P2-A-111 Rev B, P2-A-103 Rev B. |

## Logged 2026-10-04 8:14 AM CT

| ID | Question | Status | Notes / feeds |
|---|---|---|---|
| D-055 | KEYSTONE prompt v1.3 (8:13 AM CT) text vs today's decisions — which wins? | DECIDED | **DECIDED 2026-10-04 — "Shane, Grok chat" (CHANGE APPROVED 8:14 AM CT): today's decisions win over v1.3 text:** 76 in stairs (D-052); 50 ft portal (D-050); upper tier steps down (D-049); D-048 closed; D-053 applied; ~~the 55,000 SF cap applies to the footprint only, total GSF uncapped (D-031)~~ **[clause superseded 8:36 AM CT by D-056: there is no 55,000 SF cap at all]**. Also under v1.3: ARENA (`C:\Users\Hubby\Desktop\ARENA`) is the master, repo `blueprints/` mirrors it; reviewer correction orders C-0..C-12 come first; stop after each report for Shane's GO + option number. |

## Logged 2026-10-04 8:36 AM CT

| ID | Question | Status | Notes / feeds |
|---|---|---|---|
| D-056 | Is 55,000 SF a limit? | DECIDED | **DECIDED 2026-10-04 — "Shane, Grok chat" (8:36 AM CT correction, supersedes his 8:35 message): "55,000 SF = early rough estimate, not a limit."** There is NO 55,000 SF cap — not footprint, not total. **D-031 retired**; D-055's "cap is footprint only" clause superseded. The ≥ 2,000 SF margin target is gone with it. Margin language removed from params / STATUS / notes; frozen sheets are not edited (they still show margins as history); future revisions drop it. Params keys `building.total_sf`, `building.footprint_cap_sf`, `locked_program.target_margin_sf` and `phase2_site.yaml footprint_check.cap_sf` stay only so frozen / issued sheets regenerate byte-identical (marked RETIRED). |
| D-057 | What does every area table report? | DECIDED | **DECIDED 2026-10-04 — "Shane, Grok chat" (8:36 AM CT): every area table reports L1 footprint, L2 area, TOTAL GSF, and change vs the last revision. Size is controlled by budget and parcel** (D-012 budget, D-006 site). First table in this form: R-021. |

## Logged 2026-10-04 9:10 AM CT

| ID | Question | Status | Notes / feeds |
|---|---|---|---|
| D-058 | Keep stopping for Shane's GO + "next build options" after each report (v1.3 §11 / §14)? | DECIDED | **DECIDED 2026-10-04 — "Shane, Grok chat" (9:10 AM CT): no more "next build options" or waiting for GO — proceed with the standard next step and keep going. Overrides the v1.3 §11 / §14 GO rule.** Same repo / ARENA rules otherwise. Same message: the **v1.3.1 ERRATA block (E-1..E-11) is ACCEPTED** as drafted and saved as a NEW file `ARENA\_KEYSTONE\KEYSTONE_PROMPT_v1.3.1_ERRATA.md` (repo mirror `blueprints/KEYSTONE_PROMPT_v1.3.1_ERRATA.md`); Shane's prompt files are never overwritten. New sheet revisions go to the ARENA root as NEW files `<sheet>_Rev<X>.pdf` — naming **ASSUMED**, Shane to confirm (STATUS). |
| D-060 | D-049 "lockers only where headroom is full": which reading? | DECIDED | **SETTLED 2026-10-04 — "Shane, Grok chat" (10:27 AM CT): "event lockers back to full 3,600 SF behind the tier."** With D-061 Option B there is no low band, so event lockers 1-4 run to the tier lines = 4 x 900 = 3,600 SF on P2-A-101 Rev F. History: Opened by KEYSTONE 2026-10-04 (P2-A-101 Rev E). The D-049 note recorded "full headroom = under the flat L2 slab behind the tier back line" (ASSUMED); that would leave event lockers 1-2 at 418 SF and 3-4 at 286 SF each. **Rev E draws the code-headroom reading (ASSUMED):** upper-tier rows 1-2 (front 6 ft; treads 7.08 / 8.67 ft less ≈ 1'-6" structure) leave < 7'-6" clear (IBC 2021 1003.2) → storage / mech only (hatched); rows 3-5 clear ≥ 8.7 ft → lockers OK. Event lockers 1-4 start behind the 6 ft band: 707 / 707 / 655 / 655 = 2,723 SF vs 3,600 program (−877 SF). Also found: EXIT (N), EXIT (E), the SE concourse and the lobby / portal / athlete-route edge pass under rows 1-2 → need ≥ 7'-6" (omit or raise rows 1-2 there). Needs Shane: confirm the reading, and whether to win back the 877 SF (e.g. lockers 3-4 longer into Mech E). |

## Logged 2026-10-04 9:35 AM CT

| ID | Question | Status | Notes / feeds |
|---|---|---|---|
| D-059 | How is the ARENA master folder backed up? | DECIDED | **DECIDED 2026-10-04 — "Shane, Grok chat" (9:35 AM CT): ARENA backup is LIVE.** `C:\Users\Hubby\Desktop\ARENA` → `shanebrain:/tank/backups/ARENA` nightly at 11:00 PM CT (pulsar Task Scheduler, scp; test run Last Result 0) + ZFS snapshot 11:30 PM CT, 30-day retention. First snapshot `tank/backups@first` verified by Shane. Clears the 8:45 AM CT "no backup found" flag (ASSETS). **bullfrog is RETIRED; tank now lives on the shanebrain Pi.** KEYSTONE did not set up or test the job (Shane's report). |

## Logged 2026-10-04 9:47 AM CT

| ID | Question | Status | Notes / feeds |
|---|---|---|---|
| D-061 | Exit paths under the upper tier's 6 ft low band (clear 5.6' / 7.2' < 7'-6", IBC 2021 1003.2): Option A (omit rows 1-2 over the paths) or Option B (raise L2 / upper tier)? | DECIDED | **DECIDED 2026-10-04 — "Shane, Grok chat" (10:27 AM CT): "OPTION B: raise Level 2 to 17'-9\" with 21 in upper risers. No seats lost; upper-tier front row ≥ 7'-6\" clear over ALL exit paths."** Drawn on P2-A-101/102 Rev F, A-301 Rev D, A-302 Rev C, A-201 Rev G, C-101 Rev C, G-003 Rev I. History: Opened by KEYSTONE 2026-10-04 (Shane 9:47 AM CT: do not redesign silently; two options with numbers). Paths under rows 1-2 on P2-A-101 Rev E: Exit N 8 ft, Exit E 8 ft, SE concourse 38 ft (23 S + 15 E), lobby / portal / athlete-route edge 71 ft (x 56-127) = 125 ft. **A:** omit rows 1-2 over them = −125 upper seats (1,155 → 1,030, 70 short of 1,100); A-min with rails on the non-path strips = −56 (Exit N 8, Exit E 8, portal 12, athlete route 28) → 1,099 (1 short). **B:** L2 FF 15'-0" → 17'-9" with 21 in upper risers (front row 9.0', 7'-6" clear): 0 seats lost, lockers back to 3,600 SF (D-060 moot), stairs 31 risers +34.8 SF each per level (≈ +279 SF, +0.13 SF/seat), ring roof 32.75', sight lines unchanged (C min 149 / 101 seated). Shown red on P2-A-301 Rev C; details research/R-022. Feeds P2-A-101/102/201/301 next revisions. |

## Logged 2026-10-04 10:27 AM CT

| ID | Question | Status | Notes / feeds |
|---|---|---|---|
| D-062 | Are P2-A-201 Rev F, P2-G-003 Rev H, P1-G-001 Rev E and R-023 approved? | DECIDED | **DECIDED 2026-10-04 — "Shane, Grok chat" (10:27 AM CT): "APPROVED: A-201 Rev F, G-003 Rev H, P1-G-001 Rev E, R-023 (log approvals; freeze those revs)."** Frozen (phase2.yaml / phase1.yaml `frozen: true` + `approved`); PDFs stay byte-identical. R-023 (Champion Walk brick budget, D-044) approved as research; no sheet. Same message decided D-061 (Option B) and settled D-060. |

## Logged 2026-10-04 10:48 AM CT

| ID | Question | Status | Notes / feeds |
|---|---|---|---|
| D-063 | RULE (reviewer C-12, prompt v1.3 §15): may the distance labels on Shane's Google measure markup be used as dimensions? | DECIDED | **DECIDED 2026-10-04 — "Shane, Grok chat" (10:48 AM CT), quoting v1.3 §15: "Ignore the 250 / 150 / 50 / 276.85 ft labels on Shane's Google measure markup; never use them as dimensions."** Applies to `wrestle-room-measure.png` (ASSETS #11, §1c). Phase 1 dimensions come only from Shane's tape (inside 55'-0" x 45'-0", D-001 inputs). phase1.yaml `existing.wrestling_room.estimate_aerial` is kept as history / cross-check only and is marked with the rule. `shared/validate.py` check 8 fails if 276.85 appears as a numeric params value, or if 250 / 150 / 50 / 276.85 appear as a dimension value under phase1.yaml `existing`. **C-12 CLOSED.** |

## Logged 2026-10-04 11:07 AM CT

| ID | Question | Status | Notes / feeds |
|---|---|---|---|
| D-064 | FINDING (Shane 11:07 AM CT): L1 restrooms at the worst case (standing floor) — size for it, or limit the events? | DECIDED | Standing floor 3,284 + lower seats 1,100 = 4,384 → IBC 2021 T2902.1 (R-009): 26 men's / 50 women's WC, lav 11 / 15, DF 5 vs 10 / 18 WC (lav 4 / 5, DF 2) drawn on P2-A-101 Rev G (P2-G-003 Rev I basis 1,428). Shortfall +16 M / +32 W WC, +7 / +10 lav. **Option 1:** size the L1 restrooms for the worst case (about +65 fixtures ≈ +3,250 SF at 50 SF per fixture, phase2_program.yaml ASSUMED). **Option 2:** limit standing / large floor events by a posted occupant load, or bring temporary facilities for them (AHJ acceptance NOT researched). Not redesigned. Follows D-054. Shown on P2-A-111 Rev A. **2026-10-04 1:22 PM CT (Shane): DECIDED — Option 2: size the L1 restrooms to the CHAIRS-ONLY case; post the occupant load per configuration (IBC 1004.9); temporary units for anything larger.** Chairs-only L1 restroom load = 2,346 floor + 1,100 lower seats = 3,446 → IBC 2021 Table 2902.1 (same table as IPC 2021 Table 403.1; R-009): 22 men's / 42 women's WC, lav 9 / 12, DF 4 vs 10 / 18 WC, lav 4 / 5, DF 2 drawn → SHORT +12 M / +24 W WC, +5 / +7 lav, +2 DF (+48 fixtures in rooms ≈ +2,400 SF at 50 SF per fixture, phase2_program.yaml ASSUMED). Where the space comes from is finding **D-069** (options; not redesigned). Fixture set drawn as a core test-fit on P2-A-401 Rev B. |
| D-065 | FINDING (Shane 11:07 AM CT): security checkpoint vs main-exit egress — where does screening go? | DECIDED | Plan Rev G: the 32 ft checkpoint zone [97-129 ft] stands directly inside the E1 bank; clear lobby width beside it 58 − 32 = 26 ft = 312 in < 466.5 in the main exit needs. Exits must not pass through the checkpoint in the egress direction; the required width may not be obstructed or narrowed (IBC 2021 1003.6, 1010.5, 1030.2). **Option 1:** move screening into a side bay of the lobby (e.g. west side by CD-1), off the egress path, keeping ≥ 466.5 in (38.9 ft) clear from the portal / lobby to the bank, free of lanes, stanchions and queues. **Option 2:** screen outdoors on the entry plaza with temporary lanes beside a clear discharge path ≥ 466.5 in to the public way; plaza paving wider than the 28 ft Champion Walk (site D-006, P2-C-101). Related TBD: exit discharge width from E1 ≥ 466.5 in (1028.3); the 28 ft walk / portal opening alone is 336 in. Flagged on P2-A-101 Rev G and P2-A-111 Rev A; not redesigned. **2026-10-04 1:21 PM CT (Shane): DECIDED — Option 1: security screening in a side bay of the lobby, off the egress path, keeping ≥ 466.5 in (38.9 ft) clear to the E1 bank.** Drawn on P2-A-101 Rev H (ASSUMED layout): bay [123, 24, 142, 50] = 19 x 26 ft on the lobby's east side, 3 lanes ASSUMED (CEIA HI-PE wide WTMD 935 mm wide x 660 mm deep, 820 mm passage, vendor brochure); clear lobby beside it 84 → 123 = 39 ft = 468 in ≥ 466.5 in (Rev G standing basis; 467.0 with the annex) and ≥ 396.7 (chairs design case); 14 ft cross aisle kept in front of the inner bank. First aid and concession moved off the lobby's east side into the east concourse (areas unchanged). Checked on P2-A-111 Rev B. |

## Logged 2026-10-04 11:24 AM CT

| ID | Question | Status | Notes / feeds |
|---|---|---|---|
| D-066 | FINDING (Shane 11:24 AM CT): exit discharge from E1 is narrower than the main exit's required capacity — widen the walk / plaza, or add a parallel discharge path? | DECIDED | IBC 2021 1028.3: "The minimum width or required capacity of the exit discharge shall be not less than the minimum width or required capacity of the exits being served." E1 needs 466.5 in (38.9 ft) at the standing worst case (P2-A-111 Rev A; 1030.2). The Champion Walk is 28 ft = 336 in (D-046), short by 130.5 in. The freestanding portal's arch opening is also 28 ft (D-043, D-050), so the discharge has to bypass the arch as well (1028.5: direct and unobstructed access to a public way). **Option 1:** widen the walk / plaza to ≥ 39 ft clear at the discharge, from the E1 bank to the public way, with the portal piers outside that width. **Option 2:** keep the 28 ft walk and add a parallel paved discharge path (or paths) beside the walk / portal, ≥ 130.5 in (≈ 11 ft) combined, running past the portal to the public way. No redesign. Site TBD (D-006); drawn later on P2-C-101 / P2-A-201. Related: D-065 Option 2 (outdoor screening) would also sit on this plaza. **2026-10-04 1:22 PM CT (Shane): DECIDED — walk widened to 40 ft at the doors = 28 ft brick center + 6 ft paved bands each side; egress flows around both portal piers.** Note: the side bands could be brick later for more donor bricks (pricing OPEN, D-044). Check (KEYSTONE geometry, portal 44 ft wide / 28 ft arch → piers 8 ft each, ASSUMED): at the doors 40 ft = 480 in ≥ 466.5; at the portal the bands jog out around the piers (6 ft clear outside each pier) → 28 + 6 + 6 = 40 ft = 480 in ≥ 466.5 (IBC 2021 1028.3); south of the portal to the public way 40 ft (site TBD, D-006). P2-C-101 Rev D, P2-A-901 Rev B. |

## Logged 2026-10-04 1:21 PM CT

| ID | Question | Status | Notes / feeds |
|---|---|---|---|
| D-067 | NEW PROGRAM ITEM (Shane 1:22 PM CT): chair / table / stage storage room for about 2,350 stacked chairs, tables and a portable stage, near the event floor and S1 — how big and where? | DECIDED | **DECIDED 2026-10-04 — "Shane, Grok chat" (1:22 PM CT): add the room, sized for ~2,350 chairs, tables, portable stage, near the event floor + S1.** Sizing basis (KEYSTONE, ASSUMED except the cart data): National Public Seating 42-8 chair / table truck holds 42 folding chairs + 8-10 folding tables, 67 x 33.25 in (vendor listing, Home Depot / GovernmentFurniture2Go, retrieved 2026-10-04) → 2,350 / 42 = 56 trucks (holds up to 448 tables; banquet case 1,095 at 8 per table ≈ 137) = 866 SF; portable stage 24 decks 4 x 8 ft on 5 carts ≈ 170 SF (ASSUMED, vendor TBD); net 1,036 SF x 2.0 for aisles / turning (ASSUMED) = 2,072 SF → drawn 70 x 30 ft = 2,100 SF one-storey annex on the north wall between X4 and X5, opening to equipment storage and the athlete corridor (floor), S1 moved to the annex north wall (ASSUMED). +2,100 SF L1 footprint / GSF. P2-A-101 Rev H, P2-G-003 Rev J, P2-C-101 Rev D, P2-A-901 Rev B; north elevation (P2-A-201) not yet revised (follow-up). |
| D-068 | Are P2-A-111 Rev A, P2-A-401 Rev A, P2-A-103 Rev A and P2-G-002 Rev A approved? | DECIDED | **DECIDED 2026-10-04 — "Shane, Grok chat" (1:22 PM CT): "Approved: A-111 Rev A, A-401 Rev A, A-103 Rev A, G-002 Rev A (log approvals)."** Frozen (phase2.yaml `frozen: true` + `approved`); PDFs stay byte-identical. New revisions G-002 Rev B, A-111 Rev B, A-401 Rev B, A-103 Rev B carry the 1:21-1:22 PM CT decisions. |
| D-069 | FINDING (from D-064, 1:22 PM CT): the chairs-only L1 restrooms need +48 fixtures and about +535 to +2,400 SF that the Rev H plan does not have — where does it come from? | DECIDED | Chairs-only L1 restroom load 3,446 → 22 M / 42 W WC, lav 9 / 12, DF 4 (IBC 2021 T2902.1 = IPC T403.1, R-009) vs 10 / 18, lav 4 / 5, DF 2 drawn; men's room 700 SF → about 1,550; women's 1,150 → about 2,700 (50 SF per fixture, ASSUMED). Tight test-fit on P2-A-401 Rev B (stalls 36 x 60 in, 6 ft aisles, +10 % walls / chases, ASSUMED): men 34 x 23 ft = 782 net / 860 SF, women 41 x 33 ft = 1,353 net / 1,488 SF, + 2 fountain alcoves 36 SF → about +535 SF; the architect's layout lands between +535 and +2,400; rooms NOT redrawn on P2-A-101 Rev H (Shane: report with options, no silent redesign). **Option 1:** grow inside the building — women east into the east concourse (about +340 to +1,550 SF; X8 kept reachable), men west into the SW FLEX / STORAGE (about +160 to +850 SF of its 975; changes D-039 flex). **Option 2:** a second L1 restroom pair in a one-storey bump-out (about +535 to +2,400 SF GSF; location TBD, east side by the concourse is the closest). **Option 3:** Option 1 for the men's room + Option 2 for the women's. Until decided, chairs-only events beyond the drawn fixtures need temporary units (D-064 Option 2 rule). **DECIDED 2026-10-04 — Shane 3:31 PM CT: Option 2 (he wrote 'Option B') — second restroom pair (core 2) in a one-storey bump-out opposite the lobby core; east concourse width and SW FLEX unchanged (D-039 unchanged).** KEYSTONE placed it EAST, centred on V2 / EXIT (E): bump-out x 210-240, y 161.09-217.09 = 30 x 56 ft = 1,680 SF, 16 ft ASSUMED; the 8 ft EXIT (E) passage continues 30 ft east as the core corridor, X7 moves to the bump-out east face (x 240). Why east, not north: the north side is the back-of-house yard (service drive, S1 apron, storage annex x 52-122, X4 / X5 / ST-2 discharges), so public restrooms there would sit in the loading zone; the east side is open, and the public reaches it straight from the floor and east lower tier through V2 and EXIT (E). Fixtures (chairs-only, load 3,446): lobby core 10 M / 18 W WC, lav 4 / 5, DF 2 (as drawn) + core 2 men 5 WC + 7 urinals (12; urinals ≤ 67 % of the required WC, IPC 2021 424.2, R-009), lav 5; women 24 WC, lav 7; DF 2 (hi-lo, ADA 211.2) = 22 / 42, 9 / 12, 4. Areas: L1 55,181 → 56,861, L2 28,933, total 84,113 → 85,793 (+1,680). Sheets: G-003 K, A-101 I, A-111 C, A-401 C, C-101 E, A-901 C, A-201 H. |
