thebardchat/TrojanHorseAreana/blueprints/STATUS.md

# KEYSTONE — 2026-10-05 6:12 AM CT
HEALTH: YELLOW · P1 50% · P2 85% · Ticket P2-T-012
WHAT CHANGED: Daily 6 AM check: no new answers or data since Oct 4 4:03 PM. Nothing drawn (work PAUSED per Shane). Validate PASSED. Pulsar00100 offline, so _KEYSTONE copy skipped; GitHub mirror refreshed.
WHAT TO VERIFY: East location (vs north) and 16 ft height ASSUMED; X7 moved 30 ft east, discharge to a public way TBD (D-006); floor chair layouts keep an aisle to V2; core-2 plumbing = MEP; G-002 Rev B still shows D-069 open. ARENA naming ASSUMED.
NEXT ACTION: PAUSED per Shane. Waiting on his review of the 7 Oct 4 revisions; then P2-T-012 G-001 cover + combined set + draft PR when he says go. P1-T-005 to 007 jump the line when Dr. Headen's support-wing data arrives.
QUESTION FOR SHANE: Core 2 on the EAST wall at V2 (30x56 ft, X7 moved to its east face) OK, or do you want it on the north side? And should G-002 get a Rev C so its D-069 note reads closed?
