thebardchat/TrojanHorseAreana/blueprints/research/R-003-ada-single-user-restroom.md

# R-003 — 2010 ADA Standards: single-user toilet room minimums (Phase 1, work item W3)

Researched by KEYSTONE 2026-10-03 for P1-T-003. All sources retrieved 2026-10-03.
Status: research note for drawing P1-A-102 later. **PRELIMINARY — CONCEPTUAL DESIGN — NOT FOR CONSTRUCTION.**

## Sources (primary)

- **S1** — U.S. Access Board, "ADA Accessibility Standards" (2010 ADA Standards + DOJ Title II/III regulation text, with 2004 ADAAG Chapters 1–10) — https://www.access-board.gov/ada/ — retrieved 2026-10-03
- **S2** — U.S. DOJ, "2010 ADA Standards for Accessible Design" — https://www.ada.gov/law-and-regs/design-standards/2010-stds/ — retrieved 2026-10-03. Spot-checked against S1 for 304.3.1, 404.2.3, 603.2.3, 604.3.1, 604.4, 606.3. The text is identical.
- **S3** — Alabama DCM, "State Building Code" — https://dcm.alabama.gov/bldg_code.aspx — retrieved 2026-10-03. It lists "2010 – ADA Standards for Accessible Design" (adopted April 18, 2011), noting "The requirements of the 2010 ADA Standards for Accessible Design supersede the accessibility requirements contained in the International Building Code and ANSI A117.1."

---

## R-003.1 — Which rules apply to the Phase 1 restroom split?

QUESTION: Does the 2010 ADA Standards govern new single-user restrooms built in an existing Madison County public high school?

ANSWER (one paragraph): **Yes, as an alteration by a public (Title II) entity.**
- 28 CFR 35.151(b)(1): an altered part of a facility must, "to the maximum extent feasible," be made readily accessible. Work starting on or after March 15, 2012 must comply with the 2010 Standards (35.151(c)(3)).
- 2010 Standards 202.3: each altered element or space must comply with Chapter 2. 213.2: "Where toilet rooms are provided, each toilet room shall comply with 603."
- In Alabama, DCM applies the 2010 ADA Standards to K-12 school work and says they supersede the IBC/A117.1 accessibility provisions (S3).
- Exceptions to watch:
  - **213.2 Exception 4:** in a cluster of single-user toilet rooms, "no more than 50 percent of the single user toilet rooms for each use at each cluster" must comply. With one male room and one female room, each "use" has only one room. **The conservative read is that both rooms must comply.** Needs confirmation.
  - **202.3 Exception 2:** technical infeasibility allows "maximum extent feasible."
- **Path of travel:** 35.151(b)(4) applies to alterations of a *primary function* area. Restrooms are not primary function areas by themselves. The wrestling room work (W1) could count as primary-function work, and that would bring in the path of travel and the restrooms serving it, subject to the 20% disproportionality rule (35.151(b)(4)(iii)).

SOURCE: S1 (28 CFR 35.151(b)(1), (b)(4), (c)(3); 2010 Standards 202.3, 202.4, 213.2, 213.2.1); S3.

EDITION / SECTION: 2010 ADA Standards (DOJ, eff. March 15, 2012); 28 CFR 35.151; Alabama DCM adoption April 18, 2011.

CONFIDENCE: HIGH that 2010 ADA/603 governs the new restrooms. MEDIUM on how Exception 4 and path of travel apply here.

NEEDS ARCHITECT CONFIRMATION: YES. That includes whether W1 is a primary-function alteration that triggers path-of-travel obligations.

---

## R-003.2 — Technical minimums for a single-user toilet room

QUESTION: What are the 2010 ADA Standards minimums for a single-user toilet room: turning space, water closet, grab bars, lavatory, door, mirror, accessories, signage?

ANSWER (one paragraph): The room needs:
- **Turning space:** a 60 in circle or a T-shape in a 60 in square (304.3, 603.2.1).
- **Water closet:** clearance of 60 in from the side wall by 56 in from the rear wall (604.3.1). Centerline 16–18 in from the side wall (604.2). Seat height 17–19 in to the top of the seat (604.4).
- **Grab bars:** side bar 42 in long minimum, starting 12 in max from the rear wall and extending to 54 in min from it (604.5.1). Rear bar 36 in min, extending 12 in to one side of the centerline and 24 in to the other (604.5.2). Both mounted horizontally, 33–36 in to the top of the gripping surface (609.4).
- **Lavatory:** rim 34 in max (606.3), forward approach with knee and toe clearance (606.2, 305, 306), insulated pipes (606.5).
- **Door:** 32 in min clear width (404.2.3), maneuvering clearances per Table 404.2.4.1, hardware 34–48 in AFF with no tight grasping (404.2.7, 309.4), 5 lbf max opening force (404.2.9).
- **Door swing:** the door may not swing into any fixture's clear floor space or clearance, but may swing into the turning space (603.2.3). Exception 2: a door to a room for individual use may swing over a fixture clearance if a 30 × 48 in clear floor space (305.3) is provided inside the room beyond the door swing.
- **Clearance overlaps** are allowed (603.2.2, 604.3.2), but no other fixture may sit inside the water closet clearance (604.3.2).
- **Mirror** over a lavatory: bottom edge of the reflecting surface 40 in max (603.3).
- **Toilet paper dispenser:** 7–9 in in front of the water closet, outlet 15–48 in AFF (604.7). Flush control on the open side (604.6). Coat hooks within reach range, shelves 40–48 in (603.4).
- **Signage:** room ID signs comply with 703.1/703.2/703.5 (216.2). Tactile characters 48–60 in AFF to baseline, on the latch side, with an 18 × 18 in clear floor space beyond the door swing (703.4.1, 703.4.2).
- If the rooms are designated unisex, 213.2.1 requires privacy latches.

SOURCE: S1 (2004 ADAAG chapters as adopted in the 2010 Standards), cross-checked with S2.

EDITION / SECTION: 2010 ADA Standards §§213.2, 213.2.1, 216.2, 304.3, 305.3, 306, 308.2.1, 309.4, 404.2.3, 404.2.4.1, 404.2.5, 404.2.7, 404.2.8.1, 404.2.9, 603.2.1–603.2.3, 603.3, 603.4, 604.2–604.7, 606.2–606.5, 609.2–609.8, 703.4.1, 703.4.2.

CONFIDENCE: HIGH. Read directly from the Access Board's 2010 Standards text and spot-checked against ada.gov.

NEEDS ARCHITECT CONFIRMATION: YES, for the final layout (normal practice). The numbers themselves are not in doubt.

### Key numbers table (drives P1-A-102)

| Item | Requirement | Section |
|---|---|---|
| Turning space | 60 in diameter circle min, OR T-shape within 60 in square (arms/base 36 in wide min) | 304.3.1 / 304.3.2; required in room by 603.2.1 |
| Door may swing into turning space | Permitted | 603.2.3, 304.4 |
| Door may NOT swing into fixture clear floor space/clearance | Except individual-use room with 30 × 48 in clear floor space beyond the door arc (Exc. 2) | 603.2.3 |
| Overlap of clearances | Clear floor spaces, fixture clearances, turning space may overlap | 603.2.2 |
| Water closet clearance | 60 in min (perpendicular from side wall) × 56 in min (perpendicular from rear wall) | 604.3.1 |
| Nothing else in WC clearance | No other fixtures/obstructions (grab bars, dispensers, hooks, shelves, accessible route, other fixtures' clear floor space, turning space may overlap) | 604.3.2 |
| WC centerline from side wall | 16 in min – 18 in max | 604.2 |
| WC seat height | 17 in min – 19 in max to top of seat; not sprung to lifted | 604.4 |
| Flush control | Hand-operated (per 309) or automatic; on open side | 604.6 |
| Side-wall grab bar | 42 in long min; 12 in max from rear wall; extends 54 in min from rear wall | 604.5.1 |
| Rear-wall grab bar | 36 in long min; 12 in min one side of WC centerline, 24 in min other side (24 in centered allowed only for recessed-fixture conflict) | 604.5.2 |
| Grab bar height | 33 in min – 36 in max AFF to top of gripping surface, horizontal | 609.4 |
| Grab bar size / spacing / strength | Round OD 1-1/4 in – 2 in; 1-1/2 in from wall; 12 in min clear above; 250 lbf | 609.2.1, 609.3, 609.8 |
| Toilet paper dispenser | 7 in – 9 in in front of WC (to dispenser centerline); outlet 15 in – 48 in AFF; not behind grab bars; continuous flow | 604.7 |
| Lavatory clear floor space | 30 in × 48 in min, forward approach, with knee/toe clearance | 606.2, 305.3, 306 |
| Knee clearance under lavatory | Zone 9 in – 27 in AFF; 11 in deep min at 9 in, 8 in deep min at 27 in; 30 in wide min | 306.3 |
| Toe clearance under lavatory | 0 in – 9 in AFF; 17 in deep min (25 in max counted); 30 in wide min | 306.2 |
| Lavatory height | Front of rim/counter 34 in max AFF | 606.3 |
| Faucets | Operable per 309 (one hand, no tight grasp/twist, 5 lbf max); metering faucets open 10 s min | 606.4, 309.4 |
| Pipes under lavatory | Insulated or configured to protect against contact; no sharp surfaces | 606.5 |
| Mirror over lavatory | Bottom of reflecting surface 40 in max AFF (35 in max if not over lav/counter) | 603.3 |
| Coat hooks / shelves | Hooks within reach range of 308 (unobstructed forward reach 15 in – 48 in, 308.2.1); shelves 40 in – 48 in AFF | 603.4, 308.2.1 |
| Door clear width | 32 in min (door open 90°, face of door to stop) | 404.2.3 |
| Door maneuvering clearance (manual swinging) | Front approach, pull side: 60 in perpendicular + 18 in beyond latch. Front approach, push side: 48 in perpendicular + 0 in (add 12 in beyond latch if closer AND latch). Other approaches per table | Table 404.2.4.1 |
| Threshold | 1/2 in max (3/4 in beveled allowed for existing/altered) | 404.2.5 |
| Door hardware | 34 in – 48 in AFF; operable one hand without tight grasp/pinch/twist | 404.2.7, 309.4 |
| Door opening force | Interior hinged: 5 lbf max (fire doors per AHJ) | 404.2.9 |
| Door closer speed | 90° → 12° in 5 s min | 404.2.8.1 |
| Unisex/single-use rooms | ≤1 lavatory; 2 WC (no urinal) or 1 WC + 1 urinal; privacy latch | 213.2.1 |
| Room ID sign | Comply with 703.1, 703.2, 703.5 (pictograms per 703.6 with text descriptors, if used) | 216.2 |
| Tactile sign height / location | 48 in min (lowest baseline) – 60 in max (highest baseline) AFF; latch side; 18 × 18 in clear floor space beyond door arc (closed → 45°) | 703.4.1, 703.4.2 |

---

## Could not verify / not researched

1. Section 703.6 (pictograms) and the 703.2/703.5 character details were not pulled. They will matter for the sign schedule, not the plan.
2. Whether the district or DCM applies 213.2 Exception 4 (50% of a cluster) to one male + one female room. The conservative assumption is that both rooms comply.
3. IPC 2021 (adopted by DCM) fixture-count requirements for the school were **not** researched here. That is plumbing (BY LICENSED PLUMBER / ENGINEER OF RECORD) and goes in the P1-P-001 narrative.

## Conflicts / flags

- **IBC Ch. 11 / ICC A117.1 vs 2010 ADA.** Alabama DCM says the 2010 ADA Standards **supersede** the IBC/A117.1 accessibility provisions (S3). KEYSTONE will use 2010 ADA numbers only. Other A117.1 editions may set different minimums. They were **not researched** and are not used.

## What this means for Phase 1 (scope notes; no design decided)

- Each new restroom must fit, at minimum: the 60 × 56 in water closet clearance, a lavatory with a 30 × 48 in forward-approach space outside that clearance, and a 60 in turning space (overlaps allowed). The door may not swing over fixture clearances unless Exception 2's 30 × 48 in space is met. **Room size can't be judged until the walk-through room is measured (D-001).** KEYSTONE will compute fit in `calcs.py` at P1-A-102, not guess it now.
- Plan for blocking in the walls for grab bars (250 lbf, 609.8), a 32 in clear door, and lever-type hardware.
- Path of travel to the restrooms (35.151(b)(4)) may become part of the scope review. The approval path (R-002) should ask the district.
