thebardchat/TrojanHorseAreana/blueprints/research/R-006-code-edition-and-ahj.md

# R-006 — Code edition and Authority Having Jurisdiction for a new building in Hazel Green / Madison County (Phase 2)

Researched by KEYSTONE 2026-10-04 (Shane 7:44 AM CT: "proceed with the queued R-006/R-007"). All sources retrieved 2026-10-04. Feeds D-006 (site), D-007 (owner), D-008 (AHJ).
Status: research note, not legal advice. The AHJ confirms at a pre-application meeting; the parcel (D-006) and the owner (D-007) can change the answer.

## Sources
- **S1** — Madison County, AL, Inspection Department, "Building Codes" — https://www.madisoncountyal.gov/departments/inspection/building-codes — PRIMARY (county).
- **S2** — Madison County Building Inspection Department, code-update notice (enforcement from 2021-01-01) — https://www.madisoncountyal.gov/home/showpublisheddocument/7358/637438987031630000 — PRIMARY.
- **S3** — Madison County, "Commercial Inspection FAQ" — https://www.madisoncountyal.gov/departments/commercial-inspection-faq — PRIMARY.
- **S4** — Madison County Inspection Department permit portal (Tyler eSuite): "permit … for parcels or projects within the unincorporated areas of Madison County" — https://esuite-madisonco-al.tylertech.com/nwprod/esuite.permits/ — PRIMARY.
- **S5** — CityRuleLookup, "Hazel Green, AL" (Hazel Green is unincorporated; county rules apply) — https://cityrulelookup.com/hazel-green-al — SECONDARY (not an official source; consistent with S4).
- **S6** — Alabama Administrative Code r. 482-2-101-.02, State Fire Marshal, "Adoption of International Fire Code (2021 Ed.); Exceptions" — https://admincode.legislature.state.al.us/api/filing/670000f339953c06d5abb830/filing — PRIMARY (state rule).
- **S7** — Alabama Division of Construction Management (DCM), "About" (State Building Code jurisdiction) — https://dcm.alabama.gov/about.aspx — and Ala. Admin. Code ch. 355-12-1 (State Building Code = 2021 IBC; 355-12-1-.04 applicability) — https://admincode.legislature.state.al.us/api/chapter/355-12-1 — PRIMARY.
- **S8** — Ala. Admin. Code r. 100-X-4-.03 (Board for Registration of Architects): assembly buildings need a registered architect regardless of size — https://admincode.legislature.state.al.us/administrative-code/100-X-4-.03 — PRIMARY.

## R-006.1 — Who is the AHJ?
QUESTION: Which office permits and inspects a privately built arena in Hazel Green?

ANSWER: Hazel Green is **unincorporated** (S5), and the county permit portal covers "the unincorporated areas of Madison County" (S4), so on a Hazel Green parcel outside any city limits the building AHJ is the **Madison County Inspection Department** (266-A Shields Road, Huntsville; commercial permits under the county's Commercial Construction Resolution, S1/S3). The county states there are **no zoning limits** on construction projects or signs, but the building, fire and trade codes apply (S3). If the parcel (D-006) falls inside a city (e.g. annexed land), that city becomes the AHJ — not researched. Separately: **DCM's State Building Code does not cover private commercial buildings** except hotels/motels, movie theaters and **schools**, and DCM's "schoolhouse" definition includes "any private building in which 25 or more persons are congregated regularly for the purpose of instruction in any branch of knowledge" (S7, 355-12-1-.04(1)(b)). Whether regular youth-wrestling practice / clinics count as "instruction" is **not settled here → ask DCM and the county** (it would add DCM plan review under the 2021 IBC). An assembly building also **requires a registered architect regardless of size** (S8).

SOURCE: S1, S3, S4, S5, S7, S8 — retrieved 2026-10-04
EDITION / SECTION: Ala. Admin. Code 355-12-1-.04; 100-X-4-.03.
CONFIDENCE: MEDIUM (unincorporated status from a secondary source + the county portal scope; DCM "instruction" reading untested)
NEEDS ARCHITECT CONFIRMATION: YES (pre-application meeting with Madison County; DCM inquiry on the schoolhouse definition)

## R-006.2 — Which code editions?
QUESTION: Which code editions apply to the Phase 2 building?

ANSWER: **Madison County enforces (since 2021-01-01): 2018 IBC, IRC, IEBC, IPC, IMC, IFGC, ISPSC; 2018 IFC; 2018 NFPA 101 Life Safety Code; 2017 NEC; 2015 IECC (state mandate)**, with local amendments in its resolution of 2020-09-02, and says **no code changes are planned in the next 12 months** (S1, S2, S3). The **State Fire Marshal** has adopted the **2021 IFC** (Appendices B, C, D, E, M; D107 and M recommended only) for projects whose architectural services contract is dated on or after the rule's effective date (S6) — so the fire code edition can differ from the county's building code edition. **KEYSTONE has been designing to IBC 2021 (Shane; UpCodes Alabama text).** Conflict flagged: county building code = 2018 IBC + 2018 NFPA 101; state fire code = 2021 IFC. Recommendation: keep designing to IBC 2021 (the newer text), check every egress / fixture / seating number against the 2018 IBC and NFPA 101 (2018) chapter 12 (new assembly) before the permit set, and confirm the editions at the pre-application meeting (D-008). Factors KEYSTONE has used so far (Table 1004.5, 1005.3.1, 1011, 1030) were read in the 2021 text only; 2018 equivalence is NOT verified, and NFPA 101 can be more restrictive for large assembly occupancies (not reviewed).

SOURCE: S1, S2, S3, S6 — retrieved 2026-10-04
EDITION / SECTION: Madison County resolution 2020-09-02 (not read in full); Ala. Admin. Code 482-2-101-.02.
CONFIDENCE: HIGH for the county list (two county pages agree) / MEDIUM for how the 2021 IFC and 2018 IBC interact on one project
NEEDS ARCHITECT CONFIRMATION: YES

## What changes for KEYSTONE
- D-008 (AHJ): Madison County Inspection Department if the parcel is unincorporated; editions as above; DCM question added. D-008 stays OPEN (needs the site, D-006, and a pre-application meeting).
- Phase 2 sheets keep citing IBC 2021; G-002 (code analysis) will carry a 2018 IBC / NFPA 101 column.
- Fire apparatus access and water supply: the state adopted IFC Appendices B, C and D (S6) — fire flow, hydrants and fire apparatus access roads apply to the site plan (P2-C-101 notes them as TBD).
- **2026-10-04 10:15 AM CT (reviewer C-6):** P1-G-001 Rev E (principal, Phase 1) prints "2021 ASSUMED, verify with AHJ" on its code lines and "Edition still open: county lists 2018 codes; State Fire Marshal uses 2021." The edition conflict stays OPEN under D-008.
