thebardchat/TrojanHorseAreana/blueprints/research/R-012-court-dimensions.md

# R-012 — Court dimensions and clearances: basketball (partial; volleyball not done) (Phase 2)

Researched by KEYSTONE 2026-10-03 for P2-T-003b option B (shrink the event floor). Retrieved 2026-10-03.
Status: **partial.** Basketball only. Volleyball and the "2nd court only after clear span" question stay open. **PRELIMINARY — CONCEPTUAL DESIGN — NOT FOR CONSTRUCTION.**

## Sources
- **S1** — NFHS Basketball Rules Book 2012-13, as hosted by the Iowa High School Athletic Association — https://ihsaa-static.s3.amazonaws.com/basketball/2012-13%20BKB%20Rules%20for%20IA.pdf — retrieved 2026-10-03 (search-index text). PRIMARY text, **old edition**.
- **S2** — IAABO Board 36, "Class 1 Court and Equipment" (training handout quoting Rule 1) — https://www.iaaboboard36.org/wp-content/uploads/2015/10/Class-1-Court-and-Equipment.pdf — retrieved 2026-10-03. SECONDARY.

## R-012.1 — High school basketball court size and runout

QUESTION: What court size and clear space does NFHS give?

ANSWER (one paragraph): NFHS Basketball Rule 1-1: "The playing court shall be a rectangular surface free from obstructions and with dimensions not greater than 94 feet in length by 50 feet in width. IDEAL MEASUREMENTS ARE: High School Age – **84 by 50 feet**." Rule 1-2-1: "There shall be at least **3 feet (and preferably 10 feet)** of unobstructed space outside boundaries." (S1; S2 agrees.) With the preferred 10 ft: (84 + 20) × (50 + 20) = **104 × 70 ft = 7,280 SF**; with the 3 ft minimum: 90 × 56 ft = 5,040 SF (arithmetic). Table 1-1 of the same book recommends planning "a court with ideal measurements … ample out-of-bounds area and necessary seating space."

SOURCE: S1, S2.

EDITION / SECTION: NFHS Basketball Rule 1-1, 1-2-1 (2012-13 text). **Current edition paywalled; UNVERIFIED** (court size rules have long been stable, but not checked).

CONFIDENCE: MEDIUM (old edition).

NEEDS ARCHITECT CONFIRMATION: YES.

## Not done
- Volleyball court count and clearances; 2nd basketball court; ceiling clear height for play.
