thebardchat/TrojanHorseAreana/blueprints/research/R-023-champion-walk-brick-budget.md

# R-023 — Champion Walk engraved-brick budget: vendor cost by scenario (Phase 2)

Written 2026-10-04 by KEYSTONE (Shane 10:17 AM CT: "Champion Walk brick budget R-file (v1.3 backlog)"). **APPROVED by Shane 2026-10-04 10:27 AM CT (D-062).** This note is arithmetic on Shane's vendor price sheet. **It is not a final cost estimate (prompt v1.3 §2).** It covers what the vendors charge for the engraved bricks only. Donor pricing stays OPEN (D-044).

## Sources

- **S1**: Shane's vendor price sheet, "Engraved Donor Brick — Vendor Cost (2026, engraving + shipping included)". It is a Google Sheets export: `ARENA\Champion_Walk_Brick_Pricing - Vendor Prices.pdf`, with a box copy at `/workspace/research_src/Champion_Walk_Brick_Pricing_Shane_2026-10-04.pdf` (sha256 `13fcc39c5fc6d5b3…`). Prices were pulled from the vendor sites on 2026-10-04. The sheet itself says: "Installation and the sand/concrete base are NOT included — budget those in the Phase 2 site work." **Vendor prices = REFERENCE.** KEYSTONE did not re-check the vendor sites.

  | Vendor (S1) | 4x8 | 8x8 | Terms (S1 notes) | URL (S1) |
  |---|---:|---:|---|---|
  | Fundraising Brick | $19.00 | $30.00 | price for 1–1,499 bricks; bulk discount at 1,500+ (amount not stated); price-match guarantee | https://www.fundraisingbrick.com/pricing/ |
  | Polar Engraving | $19.50 | $27.50 | 5-brick minimum per size; logo / clip art +$6 each | https://polarengraving.com/engraved-brick-tile-pricing/ |
  | That's My Brick (101+ tier) | $19.00 | $31.00 | tiered: 4x8 $27 / $22 / $19, 8x8 $47 / $35 / $31 (10 / 11–100 / 101+) | https://www.thatsmybrick.com/info/pricing.php |
  | Average (S1) | $19.17 | $29.50 | | |
  | Logo engraving add-on (each) | $6.00 | $6.00 | S1 lists it as a general add-on; the vendor note is Polar's | |

- **S2**: D-046 (DECIDED "for now", Shane 6:45 AM CT): walk **28 ft × 30 ft = 840 SF**. Tiers: 4x8 = single name, 8x8 = family / business. Capacity ≈ 3,700 4x8, based on 840 ÷ 0.222 = 3,780 less border and joints.
- **S3**: HomeGuide, "How Much Does a Brick Walkway Cost? (2026)", https://homeguide.com/costs/brick-walkway-cost, retrieved 2026-10-04. This is a residential cost guide. **REFERENCE, confidence LOW.**

## QUESTION

How many engraved bricks fit the 840 SF Champion Walk, and what would the vendors charge for them under a few size mixes, with and without the $6 logo?

## ANSWER

**Counting basis.** Bricks are counted at their nominal face size: 4x8 = 32 sq in = 0.2222 SF and 8x8 = 64 sq in = 0.4444 SF. That is the D-046 basis. The full 840 SF is engraved brick, with no deduction for a border course, joints, cuts or waste. These counts are therefore an **upper bound**. Shane's own allowance for border and joints is ≈ 3,700 4x8 (S2). The border width, layout and joint size are TBD.

**Scenarios.** Vendor cost includes engraving and shipping (S1).

| Scenario | 4x8 | 8x8 | Bricks | Fundraising Brick | Polar | That's My Brick | Average (S1) | Logo on every brick (+$6 each) | Average + logo on all |
|---|---:|---:|---:|---:|---:|---:|---:|---:|---:|
| **S1 all 4x8** | 3,780 | 0 | 3,780 | $71,820 | $73,710 | $71,820 | $72,450 | +$22,680 | $95,130 |
| **S2 all 8x8** | 0 | 1,890 | 1,890 | $56,700 | $51,975 | $58,590 | $55,755 | +$11,340 | $67,095 |
| **S3 mix 80/20 by area (ASSUMED)** | 3,024 | 378 | 3,402 | $68,796 | $69,363 | $69,174 | $69,111 | +$20,412 | $89,523 |

- S3 puts 80% of the area (672 SF) in 4x8 and 20% (168 SF) in 8x8. The **80/20 split is ASSUMED**, as an example only. By count it is 89% 4x8.
- The "Average" column uses S1's averages: $57.50 ÷ 3 = $19.1667 for 4x8 and $29.50 for 8x8. S1 rounds the 4x8 average to $19.17.
- Range per scenario, across the three vendors:
  - S1: $71,820–$73,710
  - S2: $51,975–$58,590
  - S3: $68,796–$69,363
- Logo: the true share of bricks with a logo is unknown. Each logo adds $6.00. The "logo on every brick" column is the most it can add.
- Tier and minimum effects are not applied:
  - Fundraising Brick has a bulk discount at 1,500+ bricks, amount not stated. Every scenario passes 1,500 bricks, so its real price may be lower.
  - That's My Brick's 101+ tier applies to all scenarios.
  - Polar's 5-brick minimum per size does not bind.
  - Taxes and price changes after 2026-10-04 are not included.

**Break-even donor price per brick (vendor cost only).** This is what a donation must at least cover so the bricks pay for themselves. It is not a recommended price; donor pricing stays **OPEN (D-044)**.

| Brick | No logo | With logo (+$6) |
|---|---:|---:|
| 4x8 | $19.00–$19.50 (avg $19.17) | $25.00–$25.50 (avg $25.17) |
| 8x8 | $27.50–$31.00 (avg $29.50) | $33.50–$37.00 (avg $35.50) |
| S3 blended (per brick, avg vendor) | $20.31 | $26.31 |

These break-even figures cover the vendor cost only. They do not cover installation, base, border, admin or payment-processing fees, or unsold-brick risk.

**NOT included, and NOT estimated here:**
- **Installation labor** (layout, setting, cutting, compaction, joint sand): TBD. For scale only, S3 publishes residential brick-walkway labor of "$8 to $16 per square foot" (includes light site prep). Applied to 840 SF that is $6,720–$13,440. This is **REFERENCE, confidence LOW**: residential, not a commercial plaza, not local, not a quote. It is not added to any total above.
- **Base / sub-base** (excavation, compacted aggregate, sand or concrete setting bed, drainage): TBD, sized by the civil / landscape designer for the site soils. S1 itself says to budget it in the Phase 2 site work. No number is given.
- **Border / edge restraint** (material and labor): TBD. Border width and material are not chosen. S3 lists residential "edging and borders" at $5–$25 per linear foot (REFERENCE, LOW). No total is given because the edge length and layout are TBD.
- **Engraving labor beyond the vendor price**: S1 says its vendor prices *include* engraving, so the standard engraving of each brick is in the table. Anything beyond that is not included and not estimated: extra lines or characters past a vendor's standard, on-site or replacement engraving, order handling and data entry, or a program administrator.
- Also not included: sales tax, contingency, permits, site lighting, sealing, maintenance, replacement bricks, and the cost of running the donor program.

## EDITION

Vendor prices as listed in S1, pulled 2026-10-04 (2026 price lists). S3 is HomeGuide's 2026 page, retrieved 2026-10-04 (page dated December 10, 2025).

## CONFIDENCE

- Brick counts: **MEDIUM** (simple area arithmetic). They are an upper bound until the border, joints and layout are set.
- Vendor costs: **MEDIUM** as REFERENCE (S1 values, not re-checked; tiers and discounts can change).
- Installation, base and border figures: **LOW / TBD** (residential guide only).

## NEEDS ARCHITECT CONFIRMATION

**YES.** The landscape architect or civil engineer must confirm:
- the paving section (base / sub-base, setting bed, drainage, slopes, accessible-route cross slope)
- the border and edge restraint
- the joint size and the brick layout, which sets the final engraved-brick count
- installation by a local contractor quote

The donor program (prices, who administers it, engraving rules) stays with Shane: **D-044 OPEN.**
