thebardchat/TrojanHorseAreana/blueprints/phase2/out/pdf/Phase2_Schematic_Set_RevD.pdf

# PRELIMINARY — CONCEPTUAL DESIGN — NOT FOR CONSTRUCTION

PROJECT

# Hazel Green Regional Athletic Complex Trojan Horse Arena · Hazel Green area, Madison County, Alabama (site TBD, D-006)

PHASE

# PHASE 2

SHEET TITLE

# COVER SHEET SHEET INDEX + DECISIONS

SCALE

# NTS

DATE

# October

2026

REV
C

DRAWN BY

## Drawn by Claude (AI) for Shane Brazelton

SHEET
P2-G-001

# TROJAN HORSE ARENA

# Hazel Green Regional Athletic Complex

## Hazel Green area, Madison County, Alabama (site TBD, D-006)

# PHASE 2 — SCHEMATIC DESIGN SET · REV D

### Program package for the Alabama-registered architect of record · October 2026

### PROJECT

Building | Indoor athletic arena, 2 levels; 210 x 252 ft + NE stair tower, + storage annex (north) + restroom bump-out (east)
Owner / client | Shane Brazelton (owner of record OPEN, D-007)
Site | TBD — unincorporated Hazel Green, Madison County, AL (D-006)
Code basis | IBC 2021 ASSUMED; county on 2018, State Fire Marshal on 2021 — AHJ to confirm (D-008)
Occupancy | A-4 main (arena), nonseparated mixed, fully sprinklered (ASSUMED, P2-G-002)
Construction type | TBD (architect)

### GENERAL NOTES

- PRELIMINARY — CONCEPTUAL DESIGN — NOT FOR CONSTRUCTION. Schematic program package only; not a code review, not sealed.
- Alabama requires a registered architect for this assembly building (Ala. Admin. Code 100-X-4-.03). This set is the program for that architect, who sets door widths, construction type, structure and MEP.
- Labels on every sheet: DECIDED = Shane's decision (D-###); ASSUMED = KEYSTONE / Claude placeholder; CITED = code or source reference.
- Drawn by AI (KEYSTONE / Claude) for Shane Brazelton. Older revisions are frozen history; new revisions are new files.

### SHEET INDEX — PHASE 2 SCHEMATIC SET REV D (sheet-number order)

SHEET | TITLE | REV STATUS
P2-G-001 | Cover sheet — sheet index + decisions | C | NEW (this sheet)
P2-G-002 | Code analysis (schematic) | D | IN REVIEW (last approved Rev C)
P2-G-003 | Program test-fit — program + loop + storage + | K | APPROVED
restrooms
P2-C-101 | Site plan — campus diagram (site TBD) | F | IN REVIEW (last approved Rev E)
P2-A-101 | Overall floor plan — Level 1 (block plan) | J | IN REVIEW (last approved Rev I)
P2-A-102 | Overall floor plan — Level 2 (block plan) | F | APPROVED
P2-A-103 | Floor overlays — mats, seating + conversions (V2 | D | IN REVIEW (last approved Rev A)
egress aisle)
P2-A-111 | Life safety plan — Levels 1 + 2 | D | IN REVIEW (last approved Rev C)
P2-A-201 | Exterior elevations | I | IN REVIEW (last approved Rev H)
P2-A-301 | Building sections | D | APPROVED
P2-A-302 | Sight-line study | C | APPROVED
P2-A-401 | Enlarged plans — locker rooms + core 2 + public | D | IN REVIEW (last approved Rev A)
corridor
P2-A-901 | 3D massing model — views | D | IN REVIEW (last approved Rev C)
D-071: Set Rev B approved (G-001 A, G-002 C, G-003 K, C-101 E, A-101 I, A-102 F, A-111 C, A-201 H, A-301 D,
A-302 C, A-901 C; frozen). Rev D sheets carry D-072 (core 2 off the public corridor (E), X11; GSF unchanged) and
are IN REVIEW. Set Rev A / B / C kept unchanged.

### SIZE — D-057 (drawn, R-021 method; no SF cap, D-056)

| SET REV D | REV H | CHANGE | SET REV A | CHANGE
Level 1 footprint | 56,861 | 55,181 | +1,680 | 51,503 | +5,358
Level 2 area | 28,933 | 28,933 | 0 | 28,363 | +570
TOTAL GSF | 85,793 | 84,113 | +1,680 | 79,866 | +5,927
Rev H = plan before the D-069 bump-out (+1,680 SF, L1 only). Set Rev A = plan Rev D (frozen baseline, D-036). Program total on P2-G-003 Rev K: 86,381 GSF (drawn − program = −588).

### KEY FACTS (as drawn)

- Event floor 120 x 144 ft drawn (16,400 SF program, D-030); 4 x 42 ft mats, 2 x 2 (D-014).
- 2,200 seats = 1,100 telescopic lower + 1,100 fixed upper; upper tier steps down from the L2 loop, 21 in risers (D-009, D-049, D-061); east seats 16 ft from the mats (D-053).
- Level 2 FF 17'-9" (D-061); 2-lane running / training loop (D-035, D-037); roofs: ring 32.75 ft, arena 42 ft, structure underside 36 ft (ASSUMED).
- Exits: E1 main = 8-pair door bank, 512 in clear, single controlled entry (D-033, Option 1 11:07 AM CT); 4 stairs x 76 in, 31 risers (D-051, D-052). 7'-6" clear under the upper-tier front, zero margin (structure ≤ 1'-6" ASSUMED).
- Restrooms (chairs-only case, load 3,446): lobby core + core 2 = 22 men's / 42 women's WC, 9 / 12 lav, 4 DF (D-064, D-069, D-070).
- Event lockers 4 x 900 = 3,600 SF (D-060); chair / table / stage storage annex 2,100 SF on the north wall with S1 (D-067).

### DECISIONS SUMMARY (DECIDED — Shane; full log: DECISIONS.md)

D-### | DECISION
D-030 | Two-level program around a 16,400 SF event floor; 2,200 seats (with D-009, D-032).
D-033 | Single controlled public entry at E1; E1 = 8-pair door bank (Option 1, 11:07 AM CT).
D-034 | Deliveries at north door S1 (staff only); bus loop south, offset from the portal view.
D-035/037 | Continuous Level 2 running / training loop, 2 lanes x 42 in.
D-039 | SW flex / storage and team assembly kept as drawn.
D-041 | Official mark = Shane's circular horse-head badge; red #CC0000 / black.
D-043/050 | Grand Entrance Portal freestanding over the Champion Walk; ≤ 50 ft, arch crown 34 ft (structural engineer required).
D-045/047 | Portal arch underside crimson, gold trim; badge 11 ft dia + 27 in wordmark.
D-046/066 | Champion Walk 28 ft brick, widened to 40 ft at the doors (6 ft paved bands); 4x8 / 8x8 donor bricks.
D-049/053/061 | Upper tier steps down from the L2 loop; east seats 16 ft from mats; L2 FF 17'-9", 21 in risers.
D-051/052 | 4 exit stairs x 76 in clear, intermediate handrails; landing ≥ stair width.
D-054 | Floor uses: sports + chairs-only events (graduations, banquets, expos). No standing-concert design.
D-056/057 | No SF cap — size set by budget + parcel; every area table shows L1, L2, total, change.
D-060 | Event lockers back to full 3,600 SF behind the tier.
D-064 | L1 restrooms sized to the chairs-only case; posted loads per configuration; temp units beyond.
D-065 | Security screening in a side bay of the lobby, off the egress path.
D-067 | Chair / table / stage storage (~2,350 chairs + tables + stage) near the floor and S1.
D-069/070 | Second restroom pair (core 2) in a one-storey 30 x 56 ft bump-out on the EAST wall.
D-072 | Bump-out south of EXIT (E); 8 ft public corridor from Concourse (E); X7 on the wall, X11 new; Mech
(E) 675 SF.

### OPEN — OWNER / ARCHITECT / ENGINEER

- D-006: Site / parcel (drives X7 discharge, bus loop, utilities, site work)
- D-007: Owner of record
- D-008: Code edition + AHJ pre-application (Madison County)
- D-012: Phase 2 budget target (ROM R-025: ~$39M mid, $28M-$57M, excl. land)
- D-042: Trademark search before signage / apparel
- D-044: Donor-brick program + pricing
- D-010/011/013: Locker parity, concessions scope, girls 3,503 SF tag
- Structural: Upper-tier structure depth ≤ 1'-6" (7'-6" clear, zero margin); portal + arch
- MEP: Total mech ≈ 4.1 % vs 5 % (D-072; annex can absorb ~800 SF); core-2 plumbing
- Architect: Door widths + hardware, construction type, allowable area, smoke-protected seating Red = owner decisions (Shane). Others go to the architect of record / engineers.

# PRELIMINARY — CONCEPTUAL DESIGN — NOT FOR CONSTRUCTION

PROJECT

# Hazel Green Regional Athletic Complex

PHASE

# PHASE 2

SHEET TITLE

# CODE ANALYSIS SCHEMATIC

SCALE

# NTS

DATE

# October

REV
D

DRAWN BY

## Drawn by Claude (AI) for

SHEET
P2-G-002

CODE ANALYSIS — SCHEMATIC (REV D) · P2-A-101 REV J / A-102 REV F · P2-G-003 REV K · D-072 PUBLIC CORRIDOR (E)

Design basis for the architect of record and the AHJ. Not a code review and no statement of approval: every line needs architect + AHJ confirmation (D-008). Values from KEYSTONE research notes; IBC 2021 text read on UpCodes (Alabama).

## 1 CODE BASIS + EDITIONS (R-006)

CODE | DESIGNED TO | COUNTY 2018 / STATE
Building | IBC 2021 (ASSUMED, Shane) | IBC 2018 (Madison County, since 2021-01-01)
Fire | IFC 2021 (State Fire Marshal; App. B, C, D) IFC 2018 (county)
Life safety | not reviewed | NFPA 101 2018 (county); ch. 12 new assembly
Plumbing | IPC 2021 / IBC 2021 ch. 29 (ASSUMED) | IPC 2018; arena row of T2902.1 reads the same
(R-009)
Assembly egress | IBC 2021 §1030.x | IBC 2018 §1029.x (same subsections; excerpts only,
UNVERIFIED)
Energy / electrical | not checked | IECC 2015 (state) / NEC 2017
STATUS of every edition line: 2021 ASSUMED (Shane) — verify with AHJ (D-008 OPEN). Factors read in the 2021 text only; 2018 / NFPA 101 equivalence NOT verified (R-006.2). AHJ: Madison County Inspection Department if the parcel is unincorporated (Hazel Green is; R-006.1, MEDIUM). DCM 'schoolhouse' review question OPEN. Assembly building needs a registered architect (Ala. Admin. Code 100-X-4-.03).

## 2 OCCUPANCY (R-007.1)

SPACE | GROUP | CITE (IBC 2021) / CONFIDENCE
Bowl + event floor | A-4 | 303.5 ('arenas'); HIGH
S&C, cross-training | A-3 or B | 303.4 / 304.1 (training); MEDIUM
Admin, first aid | B | 304.1
Storage, equipment, mech | S-1 | R-007.1 (likely group)
Locker rooms, event lockers | A-4 or B | R-007.1
Mixed occupancy: nonseparated (508.3.1) with A-4 as the main occupancy, fully sprinklered — KEYSTONE recommendation, architect chooses (accessory 508.2 or separated 508.4 also possible).

## 3 CONSTRUCTION TYPE

Construction type TBD (architect). Allowable height / area (IBC Tables 504.3, 504.4, 506.2) NOT checked. Inputs for that check: 2 stories, L2 FF 17'-9" (D-061), arena roof 42' ASSUMED, fully sprinklered. Drawn size (D-057, P2-A-101 Rev J incl. the 2,100 SF storage annex + 1,680 SF restroom bump-out (moved 42 ft south, D-072) / A-102 Rev F): L1 56,860.6 / L2 28,932.6 / TOTAL 85,793.1 GSF (R-021 method).

## 4 FIRE PROTECTION + SYSTEMS (ASSUMED)

- Automatic sprinklers throughout (903.3.1.1, ASSUMED): 903.2.1.4 triggers for A-4 — fire area > 12,000 SF, occupant load >= 300, floor other than exit discharge; all three met (R-015.5).
- Emergency voice/alarm (907.2.1.1: Group A, occupant load >= 1,000; 907.5.2.2) ASSUMED (R-015.5).
- Sprinklers + voice alarm allow 0.2 in/occupant for stairs (1005.3.1 exc. 1) and 0.15 in for doors and other components (1005.3.2 exc.) (R-018.2, R-015.6).
- Smoke-protected seating NOT assumed (1030.6.2 needs smoke control per 909 + a life safety evaluation; NFPA 101 not reviewed). If used: 1030.6.2.2 roof >= 15' above the highest aisle (loop 17.75') = 32.75'; arena U/S structure 36' drawn (R-022 §5).
- Group A: post the occupant load (1004.9); fire safety + evacuation plan with a seating plan (IFC 403.2.1); telescopic seating per ICC 300 (1030.1.1) (R-007.2).

## 5 TRAVEL DISTANCE + COMMON PATH

- Exit access travel (T1017.2, A sprinklered): 250 ft. L2 worst ≈ 141 ft (R-018.4). L1 (P2-A-111 Rev D, plan Rev J): event floor centre → V2 → EXIT (E) → X7 (back on the wall) ≈ 133 ft; women's room (2) far corner → public corridor → X11 ≈ 78 ft (rectilinear diagram measurements, UNVERIFIED).
- Common path (T1006.2.1, Group A, 75 ft): core 2 → public corridor (two ways: X11 / Concourse (E)) ≈ 61 ft; without X11 ≈ 130 ft (FAIL) — X11 added (D-072). Seats 30 ft (1030.8; rows TBD). Locker rooms 2 exits; event lockers one door if <= 75 ft (TBD).
- Stepped aisles, handrails, guards (1030.9, 1030.16, 1030.17): TBD with the seating layout (R-018.4-5).

## 6 OCCUPANT LOAD BY SPACE (IBC 2021 T1004.5 / 1004.6; R-007.2)

SPACE (drawn: A-101 Rev J, A-102 Rev F) | AREA SF | FACTOR | LOAD
LEVEL 1
Lower tier seats (telescopic) | seats | 1,100
Boys locker | 3,507 | 50 gross | 71
Girls locker | 3,507 | 50 gross | 71
Event lockers 1-4 | 3,600 | 50 gross | 72
Flex / team assembly | 2,008 | 15 net | 134
Flex / storage (SW) | 975 | 300 gross | 4
Equipment storage + room | 1,000 | 300 gross | 4
Mech / elec (5 rooms) | 3,496 | 300 gross | 15
First aid | 120 | 150 gross | 1
Concession | 275 | 200 gross | 2
Chair / table / stage storage (annex, D-067) | 2,100 | 300 gross | 7
L1 without the event floor | 1,481
Event floor — DESIGN: chairs only (D-054) | 16,416 | 7 net | 2,346
L1 TOTAL, design case (all cases: table 7) | 3,827
LEVEL 2
Upper tier seats (fixed) | seats | 1,100
Strength & conditioning | 5,124 | 50 gross | 103
Cross-training | 3,500 | 50 gross | 70
Admin | 470 | 150 gross | 4
L2 BASE | 1,277
+ loop counted as exercise (R-018 a) | 5,026 | 50 gross | 101
+ standing at the W rail (R-018 b) | 420 | 5 net | 84
L2 WORST CASE (design, D-052) | 1,462
Not added (same occupants moving through; R-018.1 method): lobby, concourses, athlete corridor /
route, vestibule, restrooms, stairs. The AHJ may count waiting / standing space. Telescopic tier: number
of seats (1004.6); if benches: 1 per 18 in of seat length (row lengths not drawn — may raise the count). Higher posted load by approval up to 1 per 7 SF with a seating diagram (1004.5.1). Event floor area 114 x 144 ft (R-007.2 / D-054; the locked program value is 16,400 SF, D-030).

## 7 FLOOR CASES — CHAIRS-ONLY (D-054) · POSTED (1004.9)

CASE (T1004.5) | FLOOR | L1 | BLDG | POSTED SIGN
Sports (exercise 50 gross, | 329 | 1,810 | 3,272 | POST
ASSUMED)
Tables + chairs (15 net) | 1,095 | 2,576 | 4,038 | POST
Chairs only (7 net) | 2,346 | 3,827 | 5,289 | POST (design)
Standing (5 net) | 3,284 | 4,765 | 6,227 | not a use (exit margin)
D-054 DECIDED (Shane 1:22 PM CT): event floor = CHAIRS-ONLY (7 net): graduations, banquets, expos; no standing-concert design. L1 exits stay as drawn for standing (extra margin, no change). IBC 2021 1004.9: the occupant load of a Group A room or space shall be posted in a conspicuous place near the main exit or exit access doorway; one sign per configuration (D-064 Option 2). Not permitted: standing (not a design use, D-054); anything larger than chairs-only needs temporary restroom units (D-064). L2 at its worst case (1,462, D-052).

## 8 PLUMBING FIXTURE BASIS (R-009)

IPC 2021 ASSUMED (IBC 2021 T2902.1 assembly — arenas; 50/50 split 2902.1.1; urinals <= 67% of
male WC, IPC 424.2). 2018 arena row reads the same (R-009). Fixture loads = P2-G-003 Rev I (seats
+ event floor at 50 gross).
LEVEL (FIXTURE LOAD) | WC M | WC F | LAV M | LAV F | DF | SS
L1 lobby core (rooms 4 + 5) | 10 | 18 | 4 | 5 | 2 | 1
L1 core 2, east (incl. 7 urinals) | 12 | 24 | 5 | 7 | 2 | 1
L1 REQUIRED, chairs (3,446) | 22 | 42 | 9 | 12 | 4 | 1
L1 DRAWN — MEETS (D-069) | 22 | 42 | 9 | 12 | 4 | 2
L2 drawn (upper seats 1,100) | 8 | 14 | 3 | 4 | 2 | 1
Core 2 (D-069 / D-070 / D-072): one-storey 30 x 56 ft bump-out on the east wall, south of EXIT (E);
reached by the 8 ft public corridor from Concourse (E), never through EXIT (E). Urinals 7 ≤ 14 (IPC
424.2). Larger events: temporary units (D-064).

## 9 LEVEL 1 EXIT CAPACITY — E1 BANK 512 in (doors 0.15 in/occ.)

Doors and other components 0.15 in per occupant (1005.3.2 exc.: sprinklers 903.3.1.1 + voice alarm 907.5.2.2). E1 = 8-pair bank, 512 in clear (Option 1 DECIDED, 64 in per pair ASSUMED); X1–X11 = 11 x
64 in. Provided 1,216 in. Stair discharge doors carry the L2 worst case first (54.8 in each).
CHECK (in) | 329 | 1,095 | 2,346 | | 3,284 | PROV.
Total at grade (L1 + L2) | 490.8 | 605.7 | 793.4 | | 934.0 | 1,216.0
Main exit E1 >= 1/2 (1030.2) | 245.4 | 302.8 | 396.7 | | 467.0 | 512.0
Other L1 exits >= 1/2 L1 (1030.3) | 135.8 | 193.2 | 287.0 | | 357.4 | 484.7
Lose E1 >= 50% (1005.5) | 245.4 | 302.8 | 396.7 | | 467.0 | 704.0
Design case = chairs (2,346 on the floor; building 5,289): E1 needs 396.7 in vs 512 (PASS). Standing (6,227) is kept as margin only: E1 467.0 in, total 934.0 vs 1,216 in (PASS). Exits
stay as drawn (D-054).

## 10 SCREENING BAY + DISCHARGE (D-065, D-066 DECIDED)

- Screening in a side bay of the lobby (P2-A-101 Rev J): clear lobby beside it 39 ft = 468 in ≥ 396.7 (chairs) and ≥ 467.0 (standing margin): PASS; lanes, tables and queues stay in the bay (1003.6, 1010.5). Accessible screening by wand beside the lanes (WTMD passage 32.3 in x 26 in deep vs ADA 403.5.1).
- Exit discharge (1028.3): walk 40 ft at the doors = 28 ft brick + 2 x 6 ft = 480 in ≥ 467.0; bands pass outside both portal piers (28 + 6 + 6 = 40 ft at the portal). P2-C-101 Rev F; public way TBD (site, D-006).

## 11 LEVEL 2 EGRESS (R-018, D-052)

Stairs 0.2 in per occupant (1005.3.1 exc. 1): 4 stairs x 76 in = 304 in. Worst 1,462 x 0.2 = 292.4 in → spare 11.6 in. Lose one stair: 228 in ≥ 146.2 in (1005.5). 4 exits (T1006.3.3). Unchanged from Rev A.

## 12 OPEN ITEMS FOR THE ARCHITECT / AHJ

- Code editions + AHJ (D-008): 2021 vs 2018 / NFPA 101 — pre-application meeting with Madison County.
- Core 2 (D-072): total mech ≈ 4.1 % of GSF vs 5 % planning (MEP engineer; annex can absorb ~800 SF later); plumbing + 16 ft bump-out ASSUMED; X7 / X11 discharge TBD (1028, D-006).
- Door widths, hardware, main-exit frontage (1030.2: street or 10 ft open space) — architect.
- Construction type + allowable area (ch. 5 / 6) — architect.
- Smoke-protected seating or not (1030.6.2) — architect / AHJ.
- Upper-tier structure 1'-6" ASSUMED (structural engineer): front-row clear is exactly 7'-6" (1003.2), zero margin.
- Seat type on the telescopic tier (benches: 1 per 18 in) and the seating layout (aisles, rails, guards).

# PRELIMINARY — CONCEPTUAL DESIGN — NOT FOR CONSTRUCTION

PROJECT

# Hazel Green Regional Athletic Complex

PHASE

# PHASE 2

SHEET TITLE

# PROGRAM + LOOP + STORAGE + RESTROOMS REV I PLAN · D-069 · D-057

SCALE

# NTS

DATE

# October

REV
K

DRAWN BY

## Drawn by KEYSTONE (AI) for

SHEET
P2-G-003

# 1 AREA BY LEVEL — 2,200 SEATS, L2 LOOP, ANNEX + BUMP-OUT (D-069)

SPACE | REV K | REV J | BASIS

### LEVEL 1 (net SF)

Event floor 16,400 + 864 east clear zone | 17,264 | 17,264 | D-030 · D-053 east tier 16 ft
Lower tier seats (1,100), TELESCOPIC | 3,719 | 3,719 | 3.38 SF/seat (R-008) · fixed col. 6.0
Boys Locker Room | 3,500 | 3,500 | phase2.yaml tag
Girls Locker Room (D-013) | 3,503 | 3,503 | phase2.yaml tag; D-013 open
Event / visitor locker rooms | 3,600 | 3,600 | 4 x (14 wrestlers + 4 staff) x 50 SF
Foyer / trophy lobby (hall of champions) | 800 | 800 | 200 + 400 + 200 (Loudoun 2014)
Lower concourse | 1,375 | 1,375 | 25% of seats x 5 SF standing (T1004.5)
Public restrooms L1 (37 WC + lav) | 1,850 | 1,850 | T2902.1 WC+lav x 50 SF (R-009)
Concession stand | 275 | 275 | Loudoun kitchen proxy; D-011
First aid | 120 | 120 | Loudoun 2014; 1 room counted
Equipment storage (mats + floor covers) | 700 | 700 | Loudoun gym storage proxy
Equipment room | 300 | 300 | Loudoun equip./maint. proxy
Stairs (4 x 76 in, 31 risers) + elevator | 1,284 | 1,284 | D-061 17'-9" · D-052 · D-051
L1 net | | | 38,290 | | 38,290
Mechanical (5% of total gross, at grade) | 4,056 | 4,056 | R-014 · LOW
L1 GROSS (x 1.25) | 52,933 | 52,933 | R-014 gross-up
+ Chair / table / stage storage annex (gross) | 2,100 | 2,100 | D-067 · 2.0 aisle factor, no x1.25
+ Restroom bump-out, core 2 (gross) | 1,680 | — | D-069 · drawn 30 x 56 ft, no x1.25
L1 GROSS incl. annex + bump-out | 56,713 | 55,033 | both one storey (A-101 I)

### LEVEL 2 (net SF)

Upper tier seats (1,100), FIXED | 6,600 | 6,600 | 6.0 SF/seat (R-008)
Strength & Conditioning | 5,224 | 5,224 | D-035 (as Rev F)
Cross-Training Mat Area | 3,500 | 3,500 | D-035 (as Rev F)
Administrative office | 470 | 470 | 150 + 120 + 200 (Loudoun 2014)
Upper concourse / balcony | — | — | the loop replaces it (D-035)
Public restrooms L2 (29 WC + lav) | 1,450 | 1,450 | T2902.1 WC+lav x 50 SF (R-009)
Stairs (4 x 76 in, 31 risers) + elevator | 1,284 | 1,284 | D-061 17'-9" · D-052 · D-051
L2 net rooms (without the loop) | 18,528 | 18,528
Running / training loop (drawn, not grossed up) | 5,026 | 5,026 | A-102 Rev F (= Rev E) · no x1.25
L2 GROSS (x 1.25 rooms + loop) | 28,186 | 28,186
Arena volume gross (floor + east zone + lower tier) | 26,229 | 26,229
Arena volume + L2 gross | 54,415 | 54,415 | L2 sits over the L1 ring
PROGRAM FOOTPRINT = max + annex + bump-out | 58,195 | 56,515 | max(L1, AV + L2): arena volume + L2 + 2,…
PROGRAM TOTAL GSF (L1 gross + L2 gross) | 84,899 | 83,219 | no cap (D-056)

### SIZE — D-057: L1 FOOTPRINT · L2 AREA · TOTAL GSF · CHANGE vs LAST REV (no cap, no margin)

| DRAWN | REV H | CHANGE | PROGRAM | REV J | CHANGE | DRAWN − PROG.
| A-101 I / 102 F | drawn | vs Rev H | G-003 K | program | vs Rev J | (C-3)
L1 FOOTPRINT | 56,861 | 55,181 | +1,680 | 58,195 | 56,515 | +1,680 | −1,335
L2 AREA | 28,933 | 28,933 | ±0 | 28,186 | 28,186 | ±0 | +746
TOTAL GSF | 85,793 | 84,113 | +1,680 | 86,381 | 84,701 | +1,680 | −588
Program TOTAL here = program footprint + L2 gross (86,381); L1 + L2 gross = 84,899 (+1,680 vs Rev J). REV K = Rev J + the D-069 restroom bump-out (Option 2, Shane 3:31 PM CT): core 2, 1,680 SF one storey on the east wall at V2 / EXIT (E), added gross like the annex (its 30 x 56 ft is the drawn test-fit incl. +10 % walls / chases and the corridor; ASSUMED; 50 SF / fixture would be 2,400). Drawn sizes are measured on P2-A-101 Rev I / A-102 Rev F: L1 grows by the bump-out only, L2 unchanged. The program footprint carries 1,482 SF of L1 ring that no program line counts (R-021).

## 2 SEATS BY SIDE AND TIER = 2,200 (REV I PLAN)

SIDE | LOWER (TELE.) | UPPER (FIXED) | TOTAL
North | | | 359 | | 314 | | 673
South | | | 347 | | 314 | | 661
East | | | 394 | | 472 | | 866
TOTAL | 1,100 | 1,100 | 2,200
capacity drawn | 1,349 | 1,155 | 2,504
No west tier (OK'd). Lower: 6 rows x 24 in = 12 ft extended (R-008), less the 12 ft portal and two 8 ft vomitories. Upper: 15 ft, 5 rows x 36 in at 21 in risers from the L2 loop at 17'-9" down to a 9.0 ft front row = 7'-6" clear under row 1 (D-061), 6.0 SF/seat. Each tier = 1,100, split by side in proportion to drawn capacity (P2-A-101/102 Rev F). Split unchanged from Rev G/H; no seats lost. Upper spare 55.

## 3 LEVEL 2 RUNNING / TRAINING LOOP (D-035)

2 lanes x 42 in = 7 ft all around, squared corners. Centerline 154 x 205 ft: 2 x (154 + 205) = 718 ft; 5,280 / 718 = 7.35 laps/mile. Area 5,026 SF. Lanes: UFC 4-740-02N 4.1.7 (42 in, min 3 lanes), Athletic Business (36-42 in; max 12 laps/mile, 8-10 preferred). 2 lanes is ASSUMED: 3 lanes (10.5 ft) does not fit without moving the upper tier. Event days: upper concourse, spectators cross it at the tier entries; non-event days: training. 42 in guards at open edges (IBC 1015.2, 1015.3). East leg 6 ft further east (D-053).

## 4 FIXTURES BY LEVEL (IBC 2021 T2902.1)

LEVEL | LOAD WC M WC W LAV M LAV W DF WC+LAV | SUM
SUM incl. 4 drinking fountains
L1 | 1,428 | 10 | 18 | 4 | 5 | 2 | 37 | 39
L2 | 1,100 | 8 | 14 | 3 | 4 | 2 | 29 | 31
TOTAL 2,528 | 18 | 32 | 7 | 9 | 4 | 66 | 70
L1 req. 3,446 | 22 | 42 | 9 | 12 | 4 | 85 | 89
- lobby core | 10 | 18 | 4 | 5 | 2 | 37 | 39
- core 2 (E) | 5+7u | 24 | 5 | 7 | 2 | 48 | 50
L1 / L2 rows = the Rev I set the program lines carry (L1 = lower seats + 328 floor at 50 SF). D-069 DECIDED Option 2: L1 chairs-only (3,446) = lobby core (rooms 4 + 5, as drawn) + core 2 in the east bump-out (rooms 25-27): 22 / 42 WC, 9 / 12 lav, 4 DF — PASS. Core-2 urinals 7 ≤ 8 (67 % of 12, IPC 2021 424.2). Larger events: posted loads (1004.9), temporary units.
SUM incl. 4 drinking fountains (2 per level, T2902.1). Restroom SF uses WC+LAV only (66 x 50 SF, ASSUMED); fountains sit outside the rooms. Rev G's SUM column was WC+LAV (66). 1 service sink per level (not counted).

## 5 STAIRS, ELEVATOR, WHEELCHAIR

4 stairs (T1006.3.3) x 76 in (D-052: worst case 1,462 x 0.2 in = 292.4 in ≤ 4 x 76 = 304 in). 17'-9" floor-to-floor (D-061): 31 risers of 6.87 in (≤ 7 in, 1011.5.2), 2 flights (16 + 15), 165 in run, intermediate landing = width (D-051): 12.67 x 24.08 ft ≈ 305 SF each per level + 1 elevator (1104.4) = 1,284 SF per level, aligned on both levels. 18 wheelchair spaces + companions (IBC T1109.2.2.1, ADA 221.3), dispersed (ADA 221.2.3), architect to place. NE stair tower 24.08 x 6.67 ft (was 21.33 x 6.67).

## 6 RESULT

## DRAWN SIZE (A-101/102 REV I)

## L1 56,861 · L2 28,933 SF

## TOTAL 85,793 GSF (+1,680 vs Rev H)

## 2,200 seats · loop 718 ft · 7.35 laps/mi

## No SF cap (D-056) · size = budget + parcel

Drawn building = 210 x 252 ft + 24.08 x 6.67 ft NE stair tower = 53,081 SF. Program footprint 58,195 (+5,115 vs drawn): the program grosses up the open arena box; the drawing absorbs the 31-riser stairs in the box and draws the lobby void (R-021). Event floor drawn 120 x 144 = 17,280 SF. + annex 2,100 + bump-out

1,680 SF.

## 7 LOCKED IN phase2.yaml

- Event floor 16,400 SF; 4 x 42 ft mats, 2 x 2 (D-030).

### - 2,200 seats in the bowl, N, S and E sides; 2 levels; no SF cap

(D-056, D-031 retired).

### - Seating MIX: telescopic lower tier, fixed upper tier (D-009, Shane

4:30 AM CT).

### - S&C 5,224 + cross-training 3,500 SF on Level 2 (D-035; were

6,000 / 4,000).

### - Continuous L2 loop, 2 x 42 in (D-035). 76 in stairs (D-052); east

tier 16 ft (D-053). L2 17'-9", 21 in upper risers (D-061).

### - Chairs floor 2,346 (D-054); annex 2,100 (D-067); 2 restroom

cores (D-069).

## 8 STILL OPEN

- X7 discharge east to a public way; core-2 plumbing (D-006, MEP).

### - Loop lane count (2 ASSUMED; 3 preferred); 50/50 tier split and 6

telescopic rows (ASSUMED).
- Front row 7'-6" clear assumes ≈ 1'-6" deck structure (no margin, IBC 1003.2): structural engineer to confirm.

### - AHJ / code edition (D-008); girls locker size (D-013); concession

scope (D-011); owner (D-007); site (D-006).
- Suites PARKED (future add-on).

## 9 CITED vs ASSUMED

CITED: seat SF and row depth (R-008), fixtures, egress and wheelchair tables (R-009, R-015, R-016), gross-up and mechanical share (R-014), lane width (UFC 4-740-02N, Athletic Business), guards (IBC 1015). ASSUMED: 2 lanes, loop not grossed up, east zone grossed up like the floor, 50/50 tiers, 6 rows, 50 SF/fixture, box shape.

## 10 SOURCES (retrieved 2026-10-04)

- Shane 2026-10-04 3:31 PM CT (Rev K: D-069 CLOSED = Option 2, east restroom bump-out, fixture split)
- R-008, R-009, R-014-R-016, R-020; IPC 2021 424.2; IBC 2021 T2902.1, 2902.3.3, 1004.9
- Revs F-I frozen; Rev J in review; history in Revs A-J

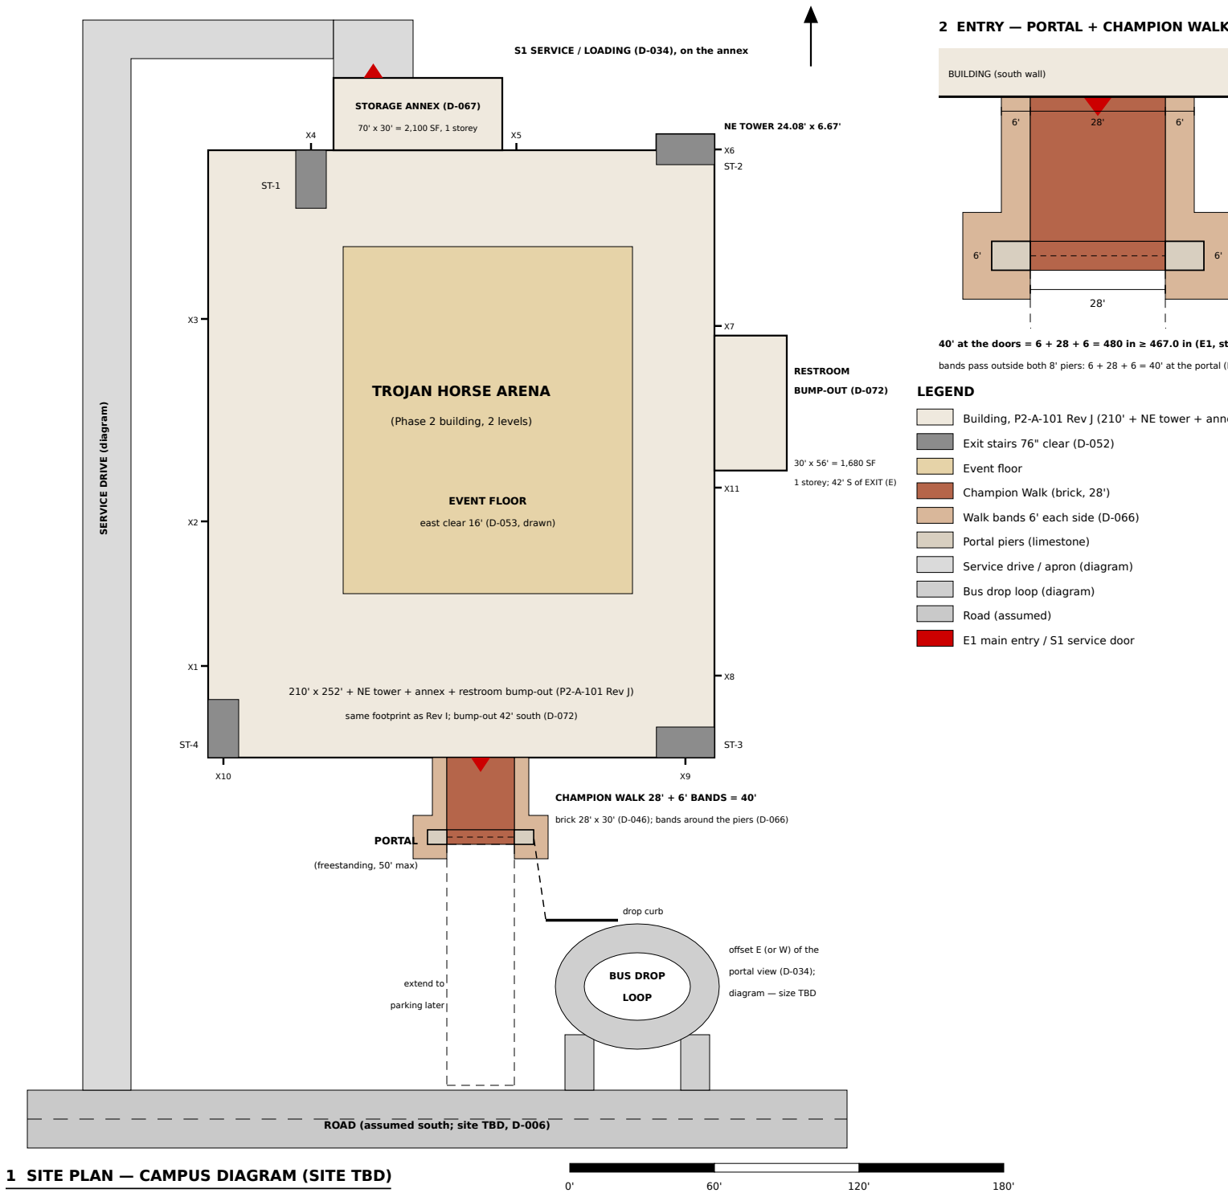
[picture p7: figure]
TROJAN HORSE ARENA; (Phase 2 building, 2 levels); EVENT FLOOR; east clear 16' (D-053, drawn); RESTROOM; BUMP-OUT (D-072); 1 storey; 42' S of EXIT (E); NE TOWER 24.08' x 6.67'; STORAGE ANNEX (D-067); 70' x 30' = 2,100 SF, 1 storey; PORTAL; (freestanding, 50' max); CHAMPION WALK 28' + 6' BANDS = 40'; extend to; parking later; BUS DROP; LOOP; offset E (or W) of the; portal view (D-034);; diagram — size TBD; drop curb; SERVICE DRIVE (diagram); ROAD (assumed south; site TBD, D-006); 1 SITE PLAN — CAMPUS DIAGRAM (SITE TBD); BUILDING (south wall); LEGEND; Exit stairs 76" clear (D-052); Event floor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

# PRELIMINARY — CONCEPTUAL DESIGN — NOT FOR CONSTRUCTION

PROJECT

# Hazel Green Regional Athletic Complex

PHASE

# PHASE 2

SHEET TITLE

# SITE PLAN — CAMPUS DIAGRAM SITE TBD · SCHEMATIC

SCALE
AS

# NOTED

DATE

# October

REV
F

DRAWN BY

## Drawn by Claude (AI) for

SHEET
P2-C-101

210' x 252' + NE tower + annex + restroom bump-out (P2-A-101 Rev J)

same footprint as Rev I; bump-out 42' south (D-072)

brick 28' x 30' (D-046); bands around the piers (D-066)

S1 SERVICE / LOADING (D-034), on the annex

PARCEL / PROPERTY LINES, SETBACKS, PARKING, UTILITIES, STORMWATER: TBD (D-006) | N

1" = 60'-0" · north approximate · road assumed south · diagram only (no surveyed dimensions)

40' at the doors = 6 + 28 + 6 = 480 in ≥ 467.0 in (E1, standing margin)

bands pass outside both 8' piers: 6 + 28 + 6 = 40' at the portal (D-066)

30'

### 2 ENTRY — PORTAL + CHAMPION WALK — 1" = 30'

Building, P2-A-101 Rev J (210' + NE tower + annex + bump-out)

SIZE — D-057 (no cap, no margin; D-056)

| DRAWN Rev J | REV I drawn | CHANGE | PROGRAM K | DRAWN − PROG.
L1 FOOTPRINT | 56,860.6 | 56,860.6 | ±0.0 | 58,195.1 | −1,334.5
L2 AREA | 28,932.6 | 28,932.6 | ±0.0 | 28,186.3 | +746.3
TOTAL GSF | 85,793.1 | 85,793.1 | ±0.0 | 86,381.4 | −588.2

Drawn = P2-A-101 Rev J / A-102 Rev F. Program = P2-G-003 Rev K (unchanged). No change vs Rev I: the 30' x 56' bump-out (1,680 SF) slid 42'
south and the public corridor came out of Mech (E) (D-072). Size is set by budget and parcel (D-012, D-006).

STATUS
- SITE TBD (D-006): this is a layout diagram, not a site plan for permit. Parcel, property lines, setbacks, grading, parking count, utilities and stormwater are TBD. AHJ (R-006): Madison County Inspection Department if the parcel is unincorporated (Hazel Green is); the county states no zoning limits on construction; county codes 2018 IBC / IFC / NFPA 101; State Fire Marshal 2021 IFC.

ENTRY + EXIT DISCHARGE (D-066 DECIDED, Shane 1:22 PM CT)
- Freestanding limestone portal over the walk (D-043), 50' max (D-050), 44' wide x 6' deep with 8' piers and a 28' arch (ASSUMED), 30' south of the E1 doors (D-046). Champion Walk 28' x 30' brick (D-046) + a 6' band each side = 40' at the doors = 480 in ≥ 467.0 in (E1 at the standing margin, P2-G-002 Rev B; IBC 2021 1028.3). At the portal the bands pass outside both piers: 6 + 28 + 6 = 40'. Bands paved now, could be brick later (D-044). Band shape between doors and portal ASSUMED. Dashed: later extension to parking.

BUS + SERVICE (D-034 DECIDED defaults)
- South bus drop loop offset EAST so it does not block the portal view (west is equally allowed). Drop curb links to the walk's south end. Service / deliveries at S1, now on the storage annex's north wall (same x, 30' further north); the west-side drive and apron move north with it. Loop, drive and apron are diagrams: lane widths, turning templates and apron size TBD (civil).

BUILDING (AS DRAWN ON P2-A-101 REV J)
- 210' x 252' (unchanged) + NE stair tower + storage annex 70' x 30' (D-067) + restroom bump-out 30' x 56' on the east wall, now 42' further south and entirely south of EXIT (E) (D-072), one storey. X7 is back on the building wall; new exit X11 off the public corridor, just south of the bump-out. X7 / X11 discharge paths to a public way TBD with the parcel (D-006).

FIRE ACCESS / WATER (TBD)
- Fire apparatus access roads, hydrants and fire flow per IFC Appendices B, C, D (State Fire Marshal, 2021 IFC; D107 recommended) and the county's 2018 IFC. Exit discharge from X1-X11 to a public way (IBC 1028) TBD with the parcel.

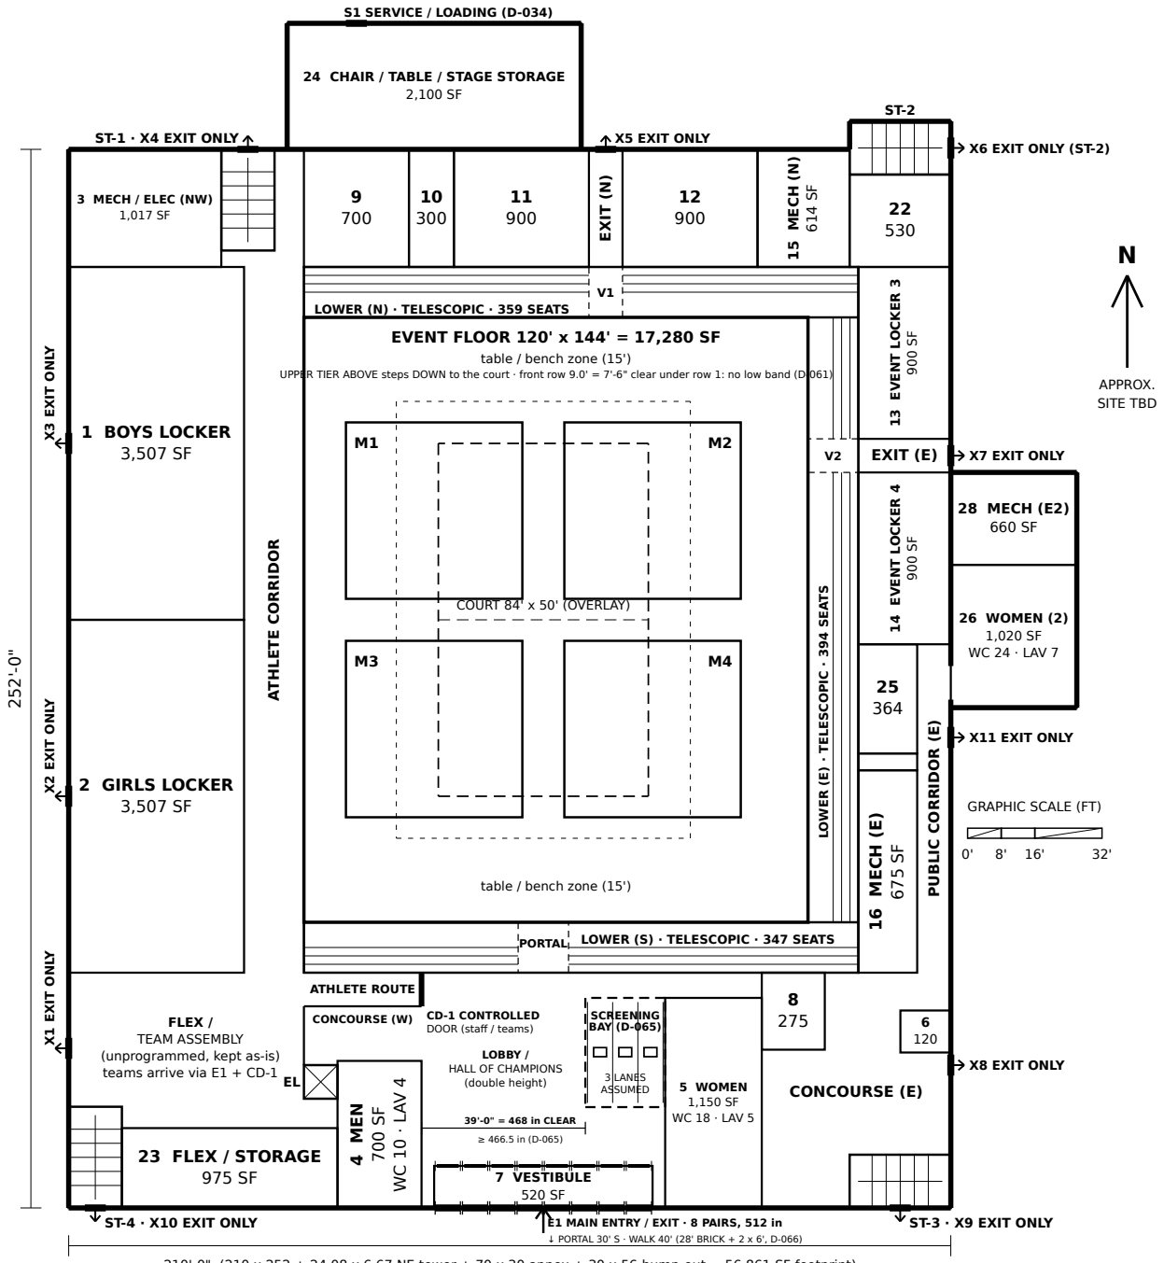
[picture p8: figure]
LOWER (N) · TELESCOPIC · 359 SEATS; PORTAL; EVENT FLOOR 120' x 144' = 17,280 SF; table / bench zone (15'); COURT 84' x 50' (OVERLAY); E1 MAIN ENTRY / EXIT · 8 PAIRS, 512 in; SCREENING BAY (D-065); 3 LANES ASSUMED; 39'-0" = 468 in CLEAR; CD-1 CONTROLLED DOOR (staff / teams); X1 EXIT ONLY X2 EXIT ONLY X3 EXIT ONLY; X5 EXIT ONLY; X7 EXIT ONLY; X11 EXIT ONLY; X8 EXIT ONLY; S1 SERVICE / LOADING (D-034); 1 BOYS LOCKER 3,507 SF; 2 GIRLS LOCKER 3,507 SF; 3 MECH / ELEC (NW) 1,017 SF; 4 MEN; WC 10 · LAV 4; 5 WOMEN 1,150 SF WC 18 · LAV 5; 7 VESTIBULE 520 SF; 13 EVENT LOCKER 3; 14 EVENT LOCKER 4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

# PRELIMINARY — CONCEPTUAL DESIGN — NOT FOR CONSTRUCTION

PROJECT

# Hazel Green Regional Athletic Complex

PHASE

# PHASE 2

SHEET TITLE

# OVERALL FLOOR PLAN LEVEL 1 · BLOCK PLAN

SCALE
1" =
40'-0"

DATE

# October

REV
J

DRAWN BY

## Drawn by Claude (AI) for

SHEET
P2-A-101

210'-0" (210 x 252 + 24.08 x 6.67 NE tower + 70 x 30 annex + 30 x 56 bump-out = 56,861 SF footprint)

LOWER (S) · TELESCOPIC · 347 SEATSLOWER ⁽E⁾ · TELESCOPIC · 394 SEATS

UPPER TIER ABOVE steps DOWN to the court · front row 9.0' = 7'-6" clear under row 1: no low band (D-061)

↓ PORTAL 30' S · WALK 40' (28' BRICK + 2 x 6', D-066)

# SCHEMATIC — BLOCK PLAN

# LEVEL 1 — OVERALL FLOOR PLAN (REV J)

### scale 1" = 40'-0" on 17 x 11 in · north approximate, road assumed south, site TBD

## LEGEND

Lower tier, TELESCOPIC (extended, 6 rows x 24 in; 3.38 SF/seat) — D-009 42' wrestling mat (4, 2 x 2)
84' x 50' court + 10' runout (overlay)
Portal / vomitory through the telescopic tier (V1, V2)
X# = EXIT ONLY — alarmed, no exterior entry hardware (symbol; width not drawn) S1 = SERVICE / LOADING door (staff-controlled, not a people entrance; D-034) Upper tier above: front row 9.0' = 7'-6" clear, no low band (D-061)
Security screening bay, 3 lanes ASSUMED (D-065 Option 1) · CD-1 controlled door Room block (tag number + drawn SF)
Stair (4) / elevator (X), same position on both levels

## ROOM SCHEDULE — LEVEL 1 (DRAWN vs PROGRAM side by side, P2-G-003 Rev K; C-3)

TAG | ROOM | DRAWN SF | PROGRAM | NOTE
— | Event floor + east zone (D-053) | 17,280 | 17,264 | 120' x 144'; east tier 16 ft from mats
— | Lower tier, telescopic (1,100 seats) | 4,896 | 3,719 | 6 rows; N 359 / S 347 / E 394
1 | Boys Locker | 3,507 | 3,500
2 | Girls Locker | 3,507 | 3,503 | drawn equal to boys (D-013)
3 | Mech / Elec (NW) | 1,017 | 1,180
4 | Men | 700 | 700 | lobby core: 14 fixtures (D-069 split)
5 | Women | 1,150 | 1,150 | lobby core: 23 fixtures (D-069 split)
6 | First Aid | 120 | 120 | Rev H: moved off the lobby's east side for the screening bay (D-065); east…
7 | Vestibule | 520 | 200 | Rev G: widened to the 52 ft E1 bank (outer + inner bank, 8 pairs each, AS…
8 | Concession | 275 | 275 | Rev H: moved off the lobby's east side for the screening bay (D-065) into t…
9 | Equip. Storage | 700 | 700
10 | Equip. Room | 300 | 300
11 | Event Locker 1 | 900 | 900 | to the tier line, full 3,600 (D-060): −0
12 | Event Locker 2 | 900 | 900 | to the tier line, full 3,600 (D-060): −0
13 | Event Locker 3 | 900 | 900 | to the tier line, full 3,600 (D-060): +0
14 | Event Locker 4 | 900 | 900 | to the tier line, full 3,600 (D-060): +0
15 | Mech (N) | 614 | 712
16 | Mech (E) | 675 | 783 | Rev J: was 1,720 SF (D-072, MEP OPEN)
22 | Mech (NE) | 530 | 615 | NE pocket, up to ST-2 (Rev F: west edge with ST-2, D-061)
24 | Chair / Table / Stage Storage | 2,100 | 2,100 | Rev H NEW (D-067): 2,100 SF one-storey annex; 56 chair / table trucks +…
23 | Flex / Storage | 975 | — | FLEX, unprogrammed, label kept (D-039, C-1)
25 | Men (2) | 364 | — | core 2: 5 WC + 7 urinals, 5 lav (D-069)
26 | Women (2) | 1,020 | — | core 2: 24 WC, 7 lav (D-069)
27 | Df / Jan. | 56 | — | core 2: 2 DF (hi-lo) + janitor sink (D-069)
28 | Mech (E2) | 660 | 766 | in the bump-out (D-072, MEP OPEN)

## AREA CHECK — D-057 (no SF cap, D-056)

| DRAWN REV J | REV I | CHANGE | PROGRAM G-003 K | DRAWN − PROG.
L1 FOOTPRINT | 56,861 | 56,861 | ±0 | 58,195 | −1,335
L2 AREA | 28,933 | 28,933 | ±0 | 28,186 | +746
TOTAL GSF | 85,793 | 85,793 | ±0 | 86,381 | −588
Floor 120 x 144, east tier 16 ft from the mats. Program = footprint / L2 gross (R-021). Seats N 673 / S 661 / E 866 (Rev F 673 / 661 / 866). Mech 3,496 vs 4,056. Event lockers 3,600 SF (D-060). FLEX kept: team assembly ≈ 2,072, FLEX / STORAGE 975 SF.

## ACCESS CONTROL + EGRESS (D-033 DECIDED; layout ASSUMED)

- ONE WAY IN (D-033): E1 → vestibule → SCREENING BAY, lobby east side (D-065 Option 1; 3 lanes ASSUMED) → lobby. 39 ft = 468 in clear beside the bay ≥ 466.5 in standing (IBC 1003.6, 1010.5). First aid + concession in the E concourse.
- CORE 2 (D-069 / D-070 / D-072): 30 x 56 bump-out slid 42 ft south of EXIT (E). PUBLIC CORRIDOR (E) 8 ft from CONCOURSE (E): rooms 25 / 26 / 27 open only onto it; X11 off it. EXIT (E) clear, X7 on the wall. MECH (E) 675 + (E2) 660 SF (MEP OPEN). Fixtures 22 / 42 WC with the lobby core. Checks: A-111 D, A-401 D.
- D-061 (Option B): Level 2 at 17'-9", 21 in upper risers, front row 9.0 ft: 7'-6" clear under row 1 (≈ 1'-6" structure ASSUMED; IBC 1003.2 minimum, no margin). Exit paths under the tier are clear; no low band, no seats lost.
Sources: phase2.yaml (D-033-D-069); DECISIONS_ARENA D-070-D-072; P2-G-003 K, A-111 D, A-401 D; IBC 2021 1003.6, 1006.2.1, 1020.3, T2902.1. Geometry: params/phase2_plan_rev_j.yaml.

# PRELIMINARY — CONCEPTUAL DESIGN — NOT FOR CONSTRUCTION

PROJECT

# Hazel Green Regional Athletic Complex

PHASE

# PHASE 2

SHEET TITLE

# OVERALL FLOOR PLAN LEVEL 2 · BLOCK PLAN

SCALE
1/32" =
1'-0"

DATE

# October

REV
F

DRAWN BY

## Drawn by KEYSTONE (AI) for

SHEET
P2-A-102

210'-0" (building 210 x 252 ft + 24.08 x 6.67 ft NE stair tower = 53,081 SF footprint)

252'-0"

UPPER (N) · FIXED · 314 SEATS

UPPER (S) · FIXED · 314 SEATS

UPPER (E) · FIXED · 472 SEATS

### OPEN TO ARENA BELOW

(event floor + telescopic lower tier, double height)

OPEN TO LOBBY BELOW
(hall of champions,
double height)

LOOP (S) · UPPER CONCOURSE / HALL OF CHAMPIONS BALCONY · 2 LANES x 42 IN = 7 FT

LOOP (N) · REAR CONCOURSE ON EVENT DAYS · 2 LANES x 42 IN

LOOP (E) · 2 LANES x 42 IN = 7 FT

LOOP (W) · NEW LEG (D-035)

### 42 IN GUARD (IBC 1015.2, 1015.3)

### 42 IN GUARD (IBC 1015)

event-day crossing (typ.)

STRETCH / WARM-UP STRIP (N) · 6 FT · ASSUMED

CONTINUOUS RUNNING / TRAINING LOOP (D-035) centerline 154' x 205' = 718 FT · 5,280 / 718 = 7.35 LAPS / MILE
2 lanes x 42 in = 7 ft all around · squared corners · 5,026 SF
non-event days: training · event days: upper concourse (spectators cross at tier entries)

### 17 STRENGTH & CONDITIONING

5,124 SF

### 18 CROSS-TRAINING MAT

3,500 SF

### 19 MEN

550 SF
WC 8 · LAV 3

### 20 WOMEN

900 SF
21 ADMIN | WC 14 · LAV 4
470 SF

L2 CORRIDOR

UPPER CONCOURSE (E)

ST-1

ST-2

ST-4 | ST-3

EL

N

APPROX.
SITE TBD
0' | 8' | 16' | 32'

GRAPHIC SCALE (FT)

# SCHEMATIC — BLOCK PLAN

# LEVEL 2 — OVERALL FLOOR PLAN (REV F)

### scale 1/32" = 1'-0" on 17 x 11 in · north approximate, road assumed south, site TBD

## LEGEND

Upper tier, FIXED (6.0 SF/seat) on the Level 2 deck — D-009
Open to below (arena; lobby double height)
Running / training loop, 2 lanes x 42 in (dashed = lane line) — D-035 42 in guard at an open edge (IBC 2021 1015.2, 1015.3)
Room block (tag number + drawn SF)
Stair (4) / elevator (X), same position on both levels

## ROOM SCHEDULE — LEVEL 2 (DRAWN vs PROGRAM side by side, P2-G-003 Rev I; C-3)

TAG | ROOM | DRAWN SF | PROGRAM | NOTE
— | Upper tier, fixed (1,100 seats) | 6,930 | 6,600 | N 314 / S 314 / E 472
— | Running / training loop | 5,026 | 5,026 | 2 x 42 in; 718 ft CL; 7.35 laps/mi
17 | Strength & Conditioning | 5,124 | 5,224 | ST-1 (31 risers) inside: −100 vs program
18 | Cross-Training Mat Area | 3,500 | 3,500 | trimmed 7 ft for the loop (D-035)
19 | Men | 550 | 550 | 11 fixtures (WC 8, LAV 3; urinals ≤ 5 of the WCs)
20 | Women | 900 | 900 | 18 fixtures (WC 14, LAV 4)
21 | Admin | 470 | 470

## AREA CHECK — D-057 (no SF cap, D-056)

| DRAWN REV F | REV E | CHANGE | PROGRAM G-003 I | DRAWN − PROG.
L1 FOOTPRINT | 53,081 | 53,062 | +18 | 54,415 | −1,335
L2 AREA | 28,933 | 28,914 | +18 | 28,186 | +746
TOTAL GSF | 82,013 | 81,976 | +37 | 82,601 | −588
L2 = footprint minus open-to-below (arena 132 x 168, lobby 58 x 34). S&C 5,224 program vs 5,124 drawn: the 31-riser ST-1 takes 35 SF more than Rev E.

## LEVEL 2 LOOP (D-035 DECIDED; geometry ASSUMED) + EGRESS

- LOOP (D-035, Shane 4:55 AM CT): continuous around the top of Level 2 — rear walkway (N), walkway (E), upper concourse / balcony (S) and a new west leg cut from S&C + cross-training. 2 lanes x 42 in = 7 ft everywhere, squared corners; 718 ft centerline = 7.35 laps/mile.
- Lane width: UFC 4-740-02N 4.1.7 (indoor track ≥ 12 ft, 3 lanes x 42 in); Athletic Business (3 lanes of 36-42 in; max 12 laps/mile, 8-10 preferred). 2 lanes ASSUMED (3 would need 10.5 ft; the upper tier would move).
- Event days the loop is the upper concourse: spectators cross it at the upper-tier entries (marked, locations ASSUMED) and at the stairs / elevator, which open onto it. Training on non-event days; crossing users are a known track hazard (Athletic Business).
- Guards 42 in min. where the loop is open more than 30 in above the floor below (IBC 2021 1015.2, 1015.3; 4 in sphere 1015.4): west edge over the arena, south edge over the lobby. Tier backs: rail / guard per 1030.17 (architect).
- Stairs 76 in, 31 risers of 6.87 in for the 17'-9" floor-to-floor (D-061), 76 in intermediate landings = 12.67 x 24.08 ft, same spot both levels. The NE stair tower grows 2.75 ft west to 24.08 x 6.67 ft (Rev E 21.33 x 6.67), still clear of the loop's north leg. Egress: 4 stairs discharge at L1 through EXIT ONLY doors X4, X6, X9, X10 (D-033).

## LAYOUT NOTES (KEYSTONE, ASSUMED — architect to confirm)

- Upper tier 15 ft deep: 5 rows x 36 in, 21 in risers (D-061; section P2-A-301 / A-302), stepping DOWN from the loop (L2 FF 17'-9") to the court (D-049). Seat split by side unchanged, totals 1,100 + 1,100.
- 6 ft stretch strip on the N side. Exit separation, travel distance, structure NOT checked. Floor-to-floor 17'-9" (D-061 DECIDED).
Sources: phase2.yaml (D-009, D-030, D-033-D-035, D-049, D-051-D-053, D-056, D-057, D-060, D-061); Shane 2026-10-04 9:10 + 10:27 AM CT; P2-G-003 Rev I; R-008, R-009, R-014, R-015, R-020-R-022; IBC 2021 Ch. 10 (UpCodes, Alabama); UFC 4-740-02N (retrieved 2026-10-04). Geometry: params/phase2_plan_rev_f.yaml.

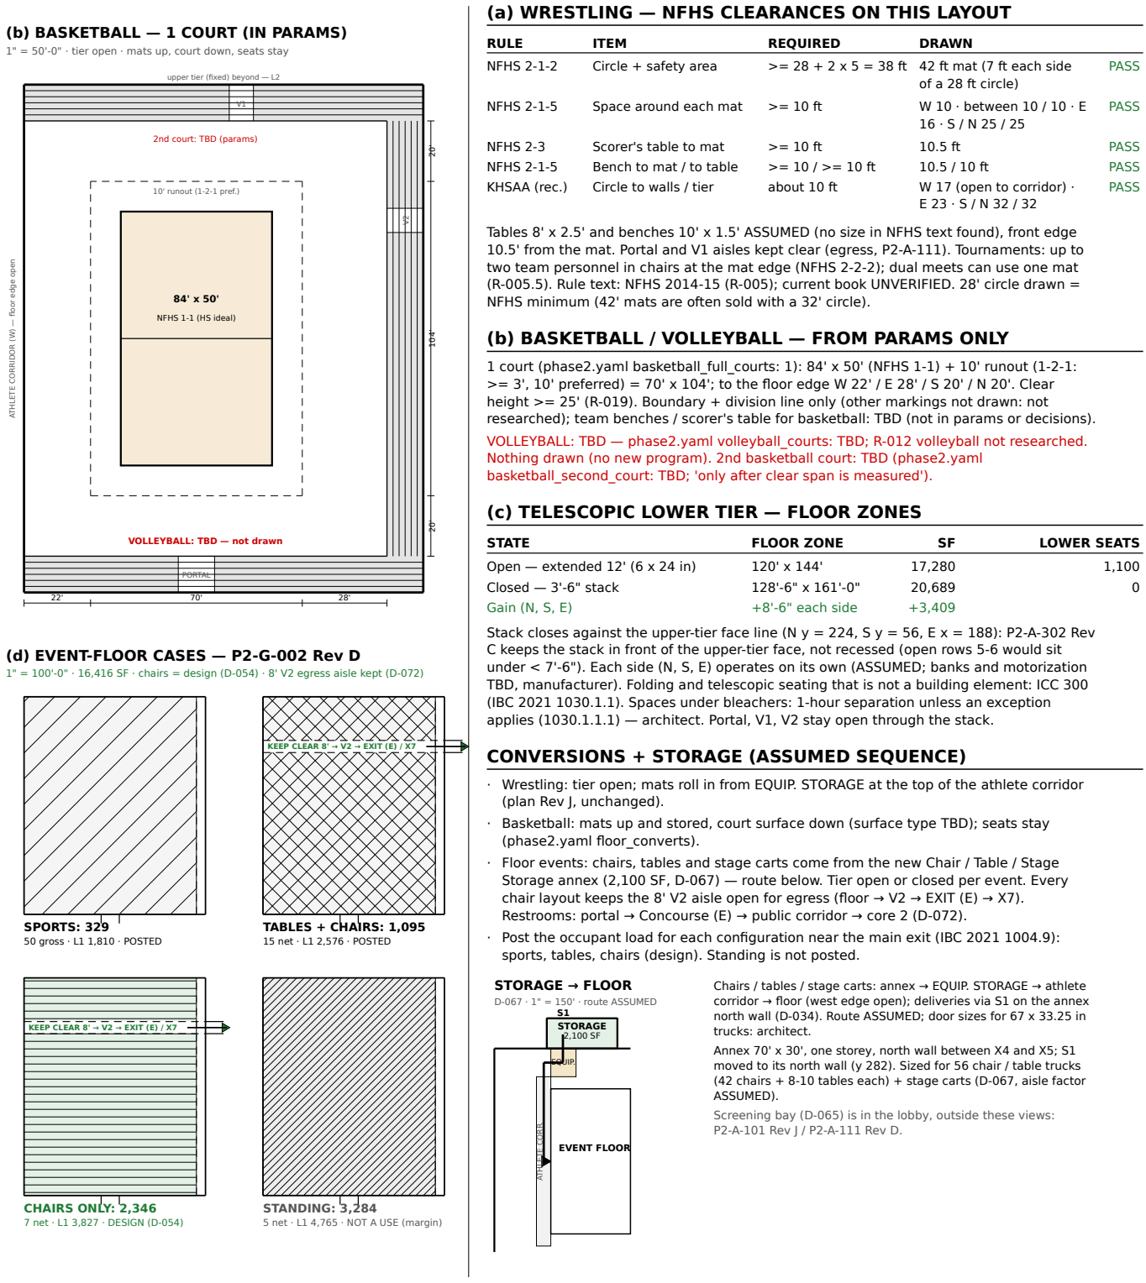
[picture p9: figure]
PORTAL; ATHLETE CORRIDOR (W) — floor edge open; upper tier (fixed) beyond — L2; NFHS 1-1 (HS ideal); 10' runout (1-2-1 pref.); VOLLEYBALL: TBD — not drawn; 2nd court: TBD (params); (b) BASKETBALL — 1 COURT (IN PARAMS); SPORTS: 329; 50 gross · L1 1,810 · POSTED; KEEP CLEAR 8' → V2 → EXIT (E) / X7; TABLES + CHAIRS: 1,095; 15 net · L1 2,576 · POSTED; CHAIRS ONLY: 2,346; 7 net · L1 3,827 · DESIGN (D-054); STANDING: 3,284; 5 net · L1 4,765 · NOT A USE (margin); (d) EVENT-FLOOR CASES — P2-G-002 Rev D; RULE; ITEM; REQUIRED; DRAWN; of a 28 ft circle); NFHS 2-3; Scorer's table to mat; PASS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

# PRELIMINARY — CONCEPTUAL DESIGN — NOT FOR CONSTRUCTION

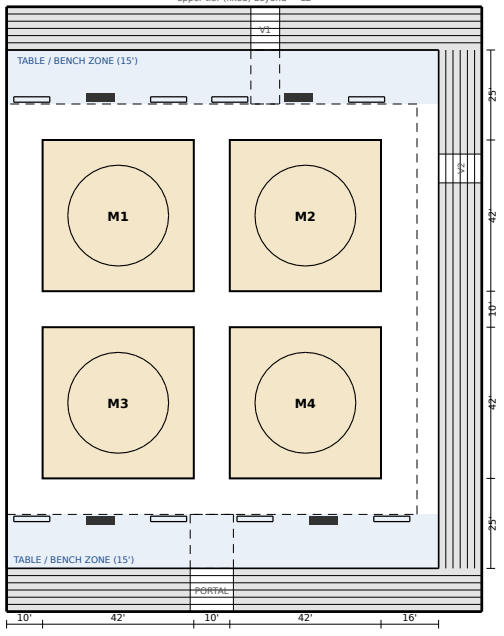
[picture p10: figure]
PORTAL; TABLE / BENCH ZONE (15')
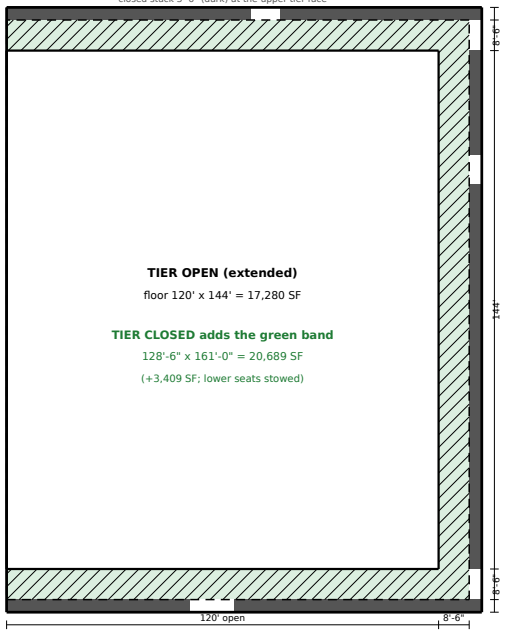
[picture p11: figure]
TIER OPEN (extended); floor 120' x 144' = 17,280 SF; TIER CLOSED adds the green band; (+3,409 SF; lower seats stowed); 120' open

PROJECT

# Hazel Green Regional Athletic Complex

PHASE

# PHASE 2

SHEET TITLE

# FLOOR OVERLAYS MATS, SEATING + CONVERSIONS

SCALE
AS

DATE

# October

REV
D

DRAWN BY

## Drawn by Claude (AI) for

SHEET
P2-A-103

ATHLETE CORRIDOR (W) — floor edge open upper tier (fixed) beyond — L2

(a) WRESTLING — 4 x 42' MATS, 2 x 2

1" = 50'-0" · tier open · NFHS clearances all PASS (table at right)

1" = 50'-0" · tier open · mats up, court down, seats stay

ATHLETE CORRIDOR (W) — floor edge open closed stack 3'-6" (dark) at the upper-tier face

(c) TELESCOPIC LOWER TIER — OPEN vs CLOSED

1" = 50'-0" · 6 rows x 24 in = 12' open; 3'-6" closed (Hussey)

1" = 100'-0" · 16,416 SF · chairs = design (D-054) · 8' V2 egress aisle kept (D-072)

### (a) WRESTLING — NFHS CLEARANCES ON THIS LAYOUT

NFHS 2-1-2 | Circle + safety area | >= 28 + 2 x 5 = 38 ft 42 ft mat (7 ft each side | PASS
NFHS 2-1-5 | Space around each mat | >= 10 ft | W 10 · between 10 / 10 · E | PASS
NFHS 2-1-5 | Bench to mat / to table | >= 10 / >= 10 ft | 10.5 / 10 ft | PASS
KHSAA (rec.) | Circle to walls / tier | about 10 ft | W 17 (open to corridor) · | PASS

Tables 8' x 2.5' and benches 10' x 1.5' ASSUMED (no size in NFHS text found), front edge
10.5' from the mat. Portal and V1 aisles kept clear (egress, P2-A-111). Tournaments: up to
two team personnel in chairs at the mat edge (NFHS 2-2-2); dual meets can use one mat (R-005.5). Rule text: NFHS 2014-15 (R-005); current book UNVERIFIED. 28' circle drawn = NFHS minimum (42' mats are often sold with a 32' circle).

### (b) BASKETBALL / VOLLEYBALL — FROM PARAMS ONLY

1 court (phase2.yaml basketball_full_courts: 1): 84' x 50' (NFHS 1-1) + 10' runout (1-2-1: >= 3', 10' preferred) = 70' x 104'; to the floor edge W 22' / E 28' / S 20' / N 20'. Clear height >= 25' (R-019). Boundary + division line only (other markings not drawn: not researched); team benches / scorer's table for basketball: TBD (not in params or decisions). VOLLEYBALL: TBD — phase2.yaml volleyball_courts: TBD; R-012 volleyball not researched. Nothing drawn (no new program). 2nd basketball court: TBD (phase2.yaml basketball_second_court: TBD; 'only after clear span is measured').

Open — extended 12' (6 x 24 in) | 120' x 144' | 17,280 | 1,100

Stack closes against the upper-tier face line (N y = 224, S y = 56, E x = 188): P2-A-302 Rev
C keeps the stack in front of the upper-tier face, not recessed (open rows 5-6 would sit under < 7'-6"). Each side (N, S, E) operates on its own (ASSUMED; banks and motorization TBD, manufacturer). Folding and telescopic seating that is not a building element: ICC 300 (IBC 2021 1030.1.1). Spaces under bleachers: 1-hour separation unless an exception applies (1030.1.1.1) — architect. Portal, V1, V2 stay open through the stack.

### CONVERSIONS + STORAGE (ASSUMED SEQUENCE)

- Wrestling: tier open; mats roll in from EQUIP. STORAGE at the top of the athlete corridor
- Basketball: mats up and stored, court surface down (surface type TBD); seats stay
- Floor events: chairs, tables and stage carts come from the new Chair / Table / Stage Storage annex (2,100 SF, D-067) — route below. Tier open or closed per event. Every chair layout keeps the 8' V2 aisle open for egress (floor → V2 → EXIT (E) → X7). Restrooms: portal → Concourse (E) → public corridor → core 2 (D-072).
- Post the occupant load for each configuration near the main exit (IBC 2021 1004.9): sports, tables, chairs (design). Standing is not posted.

Chairs / tables / stage carts: annex → EQUIP. STORAGE → athlete corridor → floor (west edge open); deliveries via S1 on the annex north wall (D-034). Route ASSUMED; door sizes for 67 x 33.25 in

Annex 70' x 30', one storey, north wall between X4 and X5; S1 moved to its north wall (y 282). Sized for 56 chair / table trucks (42 chairs + 8-10 tables each) + stage carts (D-067, aisle factor

Screening bay (D-065) is in the lobby, outside these views:

Schematic overlays for the owner, the architect of record and the AHJ. Not a code review and no statement of approval (D-008). Sports rules quoted from older NFHS editions (current books paywalled): UNVERIFIED against the current edition. Furniture positions ASSUMED.

### (d) EVENT-FLOOR CASES — POSTED LOADS (1004.9)

CASE | FACTOR | FLOOR | L1 LAYOUT NOTE
Sports | 50 gross | 329 | 1,810 POST the sports load. Mats (a) or court (b); tier open. Exercise 50 gross ASSUMED (AHJ assigns).
Tables + Chairs | 15 net | 1,095 | 2,576 POST. Keep the 8 ft V2 egress aisle clear. Aisles measured 19 in from the table edge (1030.13.1); level aisles 42 / 36 in (1030.9.1). Layout TBD.
Chairs Only | 7 net | 2,346 | 3,827 POST — DESIGN CASE (D-054). Keep the 8 ft V2 egress aisle clear. Rows: >= 12 in clear up to 14 seats, + 0.3 in per seat beyond, <= 100 per row, aisles both ends (1030.13.2).
Standing | 5 net | 3,284 | 4,765 NOT A USE: no standing-floor events (D-054). Kept only as exit margin: L1 exits stay as drawn (E1 467.0 in vs 468 in clear).

Floor = 16,416 SF (G-002 Rev D, 114' x 144'; the east 6' strip, D-053, unhatched); L1 = floor +
1,100 lower seats + 381 other L1 rooms (incl. the storage annex, 300 gross). Design case = chairs: L1 3,827. Tier CLOSED, chairs: 2,956 on 20,689 SF with no lower seats → L1 3,337, below the design case; restroom load 2,956 < 3,446 (net = gross ASSUMED). Whole drawn zone standing (17,280 SF = 3,456) would need E1 479.9 in vs 468 in clear beside the screening bay: not permitted (standing is not a use).

### CHAIR LAYOUTS — V2 EGRESS AISLE (D-072)

8 ft (96 in) EGRESS cross-aisle on the V2 line (y 175.09-183.09), full floor width: west edge (athlete corridor, open) -> east 6 ft strip -> V2 -> EXIT (E) -> X7 (clear, D-072). Restroom traffic goes out the portal to Concourse (E) and the public corridor, not this way. Width = V2 / EXIT (E) width (ASSUMED); >= 36 / 42 in level-aisle minimum (IBC 2021 1030.9.1). Lies inside the 16,416 SF floor: posted loads unchanged (net floor area basis ASSUMED, AHJ). No chairs, tables or stage in it.

### DECISIONS — SHANE 1:21 / 1:22 / 3:31 PM CT + D-070 / D-072

- D-054 DECIDED: chairs-only floor (7 net -> 2,346) is the design case; exits stay as drawn for standing (margin).
- D-064 DECIDED: restrooms sized to chairs-only; posted loads; temporary units above that.
- D-065 DECIDED: screening in a side bay of the lobby, 468 in clear kept beside it (P2-A-101 Rev J, P2-A-111 Rev D; outside these views).
- D-066 DECIDED: 40 ft walk at the doors (28 ft brick + 6 ft bands), flows around both portal piers (P2-C-101 Rev E).
- D-067 DECIDED: 2,100 SF chair / table / stage storage annex at the north wall, S1 on it (route: STORAGE → FLOOR on this sheet).
- D-069 DECIDED: core 2 (second restroom pair) in a one-storey 30 x 56 ft bump-out now reached from Concourse (E) by the public corridor (P2-A-101 Rev J, P2-A-401 Rev D).
- D-070 DECIDED: core 2 stays on the EAST wall.
- D-072 DECIDED: public corridor (E) from Concourse (E) to core 2, bump-out 42 ft south of EXIT (E), X11; restroom traffic never crosses the floor — the V2 aisle stays for egress.

### LEGEND

Grey band = telescopic lower tier open (thin lines = 24 in rows) · dark band = closed stack · tan = mat (circle = 28' NFHS minimum) · black bar = scorer's table · open bar = team bench · blue = table / bench zone · dashed = 10' mat area / keep-clear aisle / runout · green hatch = floor gained when closed · (d): green = design case, grey = not a use · route: green = storage annex, tan = equipment storage, line = cart route. (d): white band + arrow = 8' keep-clear aisle to V2. Sources: params/phase2_overlays.yaml, phase2_overlays_rev_d.yaml; phase2_plan_rev_j.yaml; phase2_code_rev_d.yaml; R-005 (NFHS Wrestling 2-1-2, 2-1-5, 2-2-1, 2-2-2, 2-3; KHSAA); R-012; R-019; R-008 / Hussey MAXAM; R-007.2 (IBC 2021 T1004.5); IBC 2021 1004.9, 1030.1.1, 1030.9.1, 1030.13.1, 1030.13.2 (UpCodes, retrieved 2026-10-04); P2-G-002 Rev D; P2-A-111 Rev D; P2-A-401 Rev D; D-053, D-054, D-064 to D-072; Shane 2026-10-04 evening.

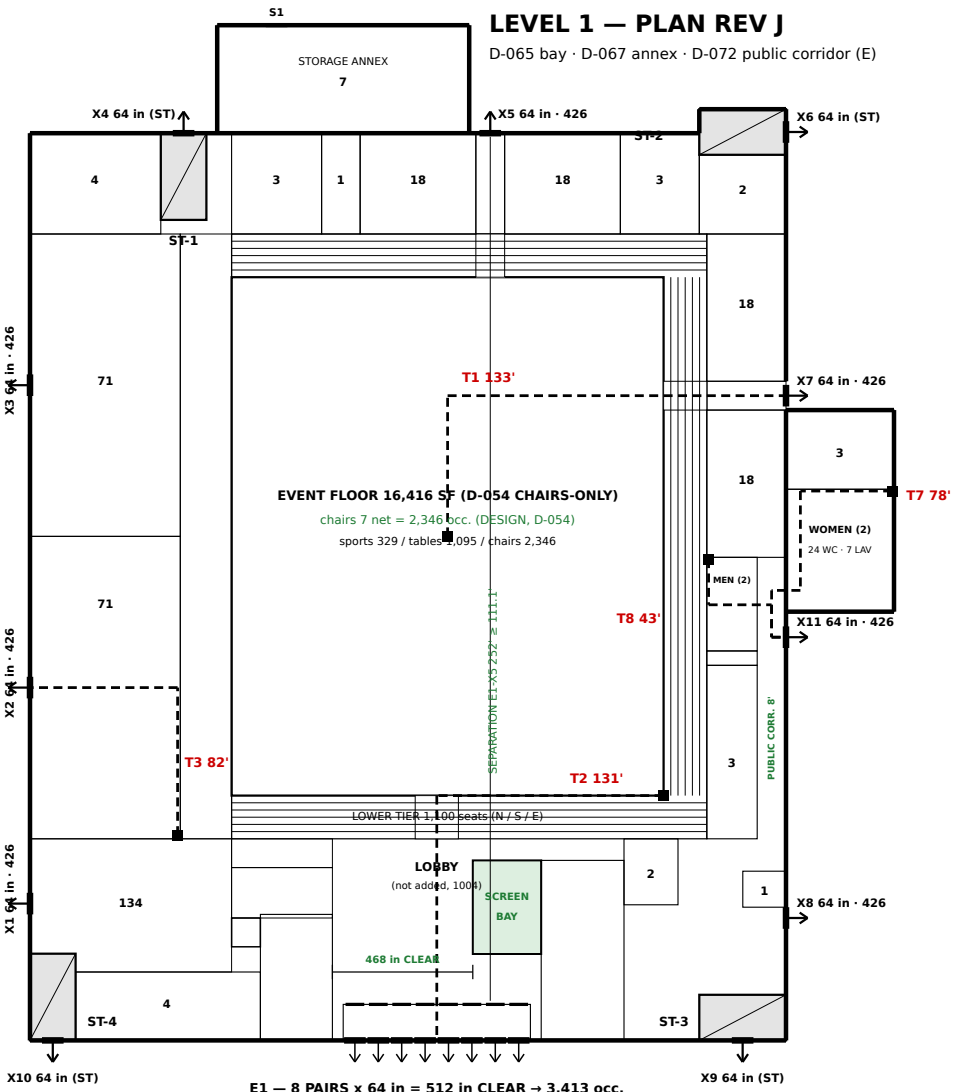
[picture p12: figure]
LEVEL 1 — PLAN REV J; SCREEN; BAY; 468 in CLEAR; STORAGE ANNEX; WOMEN (2); 24 WC · 7 LAV; MEN (2); PUBLIC CORR. 8'; LOWER TIER 1,100 seats (N / S / E); LOBBY; (not added, 1004); SEPARATION E1-X5 252' ≥ 111.1'

# PRELIMINARY — CONCEPTUAL DESIGN — NOT FOR CONSTRUCTION

PROJECT

# Hazel Green Regional Athletic Complex

PHASE

# PHASE 2

SHEET TITLE

# LIFE SAFETY PLAN LEVELS 1 + 2 · SCHEMATIC

SCALE
1" =
50'-0"

DATE

# October

REV
D

DRAWN BY

## Drawn by Claude (AI) for

SHEET
P2-A-111

D-065 bay · D-067 annex · D-072 public corridor (E)

E1 — 8 PAIRS x 64 in = 512 in CLEAR → 3,413 occ.
main exit (1030.2) · vestibule inner bank the same (1003.6) · 64 in / pair ASSUMED

X1 64 in · 426 X2 64 in · 426 X3 64 in · 426

EVENT FLOOR 16,416 SF (D-054 CHAIRS-ONLY)

chairs 7 net = 2,346 occ. (DESIGN, D-054)

sports 329 / tables 1,095 / chairs 2,346

## LEVEL 2 — LIFE SAFETY (PLAN REV F, UNCHANGED)

1" = 50'-0" · 4 stairs 76 in (D-052) = the L2 exits · loop = upper concourse on event days

ST-1

ST-2

ST-4 | ST-3

76 in · 380 occ.

76 in · 380 occ.

76 in · 380 occ.

76 in · 380 occ.

S&C 103

X-TRAIN 70

ADMIN 4

UPPER TIER 1,100 seats (N / S / E) + loop 101 + rail 84 (R-018) → L2 1,462 occ.

OPEN TO ARENA BELOW

T4 124'

T5 123'

T6 128'

ST-1-ST-3 255' · ST-2-ST-4 282' ≥ 111.1'

L1 EXITS — CAPACITY (0.15 in / occ., 1005.3.2 exc.)

EXIT / CHECK | CLEAR in | CAPACITY | SERVES / RESULT
E1 main (bank) | 512 | 3,413 | lobby, portal, south tier, concourses
X1-X3, X5, X7, X8, X11 | 7 x 64 = 448 | 426 each | exit-only doors (64 in pair ASSUMED)
X4, X6, X9, X10 | 4 x 64 = 256 | 4 x 9.2 in left | stair discharge: L2 uses 54.8 in each
Total, building worst 5,289 | need 793.4 | have 1,216.0 | PASS
Main exit ≥ 1/2 (1030.2) | need 396.7 | have 512.0 | PASS
Other L1 exits ≥ 1/2 of L1 3,827 (1030.3) | need 287.0 | have 484.7 | PASS
Lose E1, ≥ 50 % (1005.5) | need 396.7 | have 704.0 | PASS
Standing margin 6,227: E1 (exits as drawn) | need 467.0 | have 512.0 | PASS
Lobby beside the screening bay (1003.6) | need 467.0 | have 468.0 | PASS

L2 EXITS — STAIRS (0.2 in / occ., 1005.3.1 exc. 1)

EXIT / CHECK | CLEAR in | CAPACITY SERVES / RESULT
ST-1 … ST-4 | 4 x 76 = 304 | 380 each one per corner, discharge X4 / X6 / X9 / X10
Total, L2 worst 1,462 | need 292.4 | have 304.0 PASS (+11.6)
Lose one stair, ≥ 50 % (1005.5) | need 146.2 | have 228.0 PASS (+81.8)
Loop at the worst corner (R-018.3, 0.2) | need 78.6 | have 84.0 PASS (+5.4)
4 exits from L2 (T1006.3.3, > 1,000) | | 4 stairs PASS

Schematic life safety diagram for the architect of record and the AHJ. Not a code review and no statement of approval; every line needs architect + AHJ confirmation (D-008). Door widths ASSUMED, travel paths measured on the diagram.

LEGEND

Heavy bar + arrow = exit door (clear in · occupants); E1 = 8 pair bars, outer + inner (vestibule) bank. Grey box = stair. Red dashed + dot = travel path (dot = remote point; feet, rectilinear). Green line = exit separation. Green zone = screening bay (D-065). Numbers in rooms = occupant load (P2-G-002).

OCCUPANT LOADS (P2-G-002 REV D, IBC T1004.5)

CASE | FLOOR | L1 | BLDG | E1 NEED
Sports (50 gross) | 329 | 1,810 | 3,272 | 245.4
Tables + chairs (15 net) | 1,095 | 2,576 | 4,038 | 302.8
Chairs only (7 net) | 2,346 | 3,827 | 5,289 | 396.7
Standing (5 net) (WORST) | 3,284 | 4,765 | 6,227 | 467.0
Whole floor zone 17,280 SF standing | 2,469 | 3,950 | 5,412 | 405.9

L1 without the floor 1,481 (seats 1,100); L2 1,277 base, 1,462 worst. All cases pass with the 512 in bank; the whole-floor sensitivity still passes (E1 405.9 ≤ 512 in, total 811.8 ≤ 1,216 in).

EXIT SEPARATION (1007.1.1 exc. 2, sprinklered)

Max overall diagonal 333.2 ft (SW corner to NE stair tower) → 1/3 = 111.1 ft (1/2 = 166.6 ft unsprinklered). Measured to any point of a doorway / closest riser (1007.1.1.1). All outline corners checked: bump-out NE 297.1 ft, annex NE 307.3 ft (shorter).
- L1 E1 ↔ X5: 252.0 ft ≥ 111.1 ft — PASS. E1 measured at the point of the bank (x 87.25-138.75) in line with X5.
- L2 ST-1 ↔ ST-3: 255.1 ft ≥ 111.1 ft — PASS. nearest corners of the stair rectangles (risers lie inside, so the riser distance is not shorter).
- L2 ST-2 ↔ ST-4: 281.5 ft ≥ 111.1 ft — PASS. nearest corners of the stair rectangles.
- Other exits a reasonable distance apart (1007.1.2): one stair per corner, exits on all four walls.

TRAVEL DISTANCE (Table 1017.2: 250 FT)

IBC 2021 Table 1017.2: Group A with sprinklers (903.3.1.1) 250 ft. 1017.3: from the most remote point along the natural and unobstructed path to the entrance to the nearest exit. Paths below are rectilinear along open floor on the diagram (walls / doors / aisles not drawn): UNVERIFIED.
- T1 L1 event floor center → V2 → EXIT (E) → X7 (back on the building wall): 133 ft — ≤ 250, PASS (UNVERIFIED)
- T2 L1 floor SE corner → portal → lobby → E1: 131 ft — ≤ 250, PASS (UNVERIFIED)
- T3 L1 girls locker far corner → X2: 82 ft — ≤ 250, PASS (UNVERIFIED)
- T4 L2 E upper tier, front row mid → aisle → loop → ST-2: 124 ft — ≤ 250, PASS (UNVERIFIED)
- T5 L2 S upper tier, front row mid → loop → upper concourse (E) → ST-3: 123 ft — ≤ 250, PASS (UNVERIFIED)
- T6 L2 S&C far corner → ST-1: 128 ft — ≤ 250, PASS (UNVERIFIED)
- T7 L1 women's room (2) far corner → door (east wall, y 125) → public corridor → X11: 78 ft — ≤ 250, PASS (UNVERIFIED)
- T8 L1 men's room (2) far corner → door → public corridor → X11: 43 ft — ≤ 250, PASS (UNVERIFIED)
L2 paths end at the stair. If the stairs are open exit access stairways rather than enclosed exit stairways (TBD, architect), travel continues down the stair (1017.3.1, along the nosings) to the L1 exit door: about +50 ft ASSUMED (2 flights + 76 in landings + 5 ft to the door) — still under 250 ft.

COMMON PATH (T1006.2.1, 1030.8)

- Restroom core 2 (D-072) (accessory): doors onto the public corridor, then X11 or Concourse (E): common path women 61 ft, men 30 ft (≤ 75); ≈ 130 ft without X11 — OK as planned (doors ASSUMED, UNVERIFIED).
- Storage annex (D-067) (7): <= 49 and 70 x 30 ft: S1 + the door to equipment storage = 2 ways out; farthest point <= 75 ft to either — OK as planned (doors ASSUMED).
- Event lockers 1-4 (18 each): one door OK if <= 75 ft: room 32 x 28 / 22 x 41 ft → <= 63 ft rectilinear to any wall point — LIKELY — door not located (UNVERIFIED).
- Boys / girls locker (71 each): > 49 → 2 exits: X2 / X3 + corridor door — OK as planned (corridor door ASSUMED).
- Flex / team assembly (134): > 49 → 2 exits: X1 + lobby side (CD-1 free egress, 1010.2) — OK as planned.
- S&C / cross-training (L2) (103 / 70): > 49 → 2 exit access doorways each (ST-1 / loop; corridor / loop) — ASSUMED doors (TBD).
- Seats (both tiers) (1,100 + 1,100): 30 ft to a choice of two paths: aisle 12-15 ft to the floor / loop, then two ways — TBD — aisles and row lengths not drawn.
Rules: one exit only if ≤ 49 occ. and ≤ 75 ft (T1006.2.1, Group A, sprinklered); seats 30 ft to a choice of two paths (1030.8); unoccupied mech rooms exempt (1006.2.1 exc. 3).

SCREENING BAY vs EGRESS (D-065 DECIDED) — CHECK

Bay x 123-142, y 24-50 (19 x 26 ft); lobby clear beside it 39 ft = 468 in, free of lanes, stanchions and queues; 14 ft cross aisle to the inner bank. Main exit need: chairs 396.7 in (design), standing 467.0 in (margin): both <= 468, PASS.
- Lanes, tables, queues and control lines stay out of the 468 in path (IBC 1003.6, 1010.5). Standing is not a design use (D-054, posted loads 1004.9): whole-floor standing would need 479.9 in here.

RESTROOMS — CORE 2 OFF THE PUBLIC CORRIDOR (D-072)

Core 2 (D-069 / D-070 / D-072): WOMEN (2) in the bump-out (south of EXIT (E)), MEN (2) + DF in the old Mech (E) strip, all off the public corridor. With the lobby core 22 / 42 WC, 9 / 12 lav, 4 DF = chairs-only 3,446 (T2902.1): PASS; one storey, < 500 ft (2902.3.3): PASS.
- Public reach: Concourse (E) → public corridor; never across the floor or through EXIT (E).

EXIT DISCHARGE — 40 FT WALK (D-066 DECIDED) — CHECK

Exit discharge (1028.3, D-066 DECIDED): walk 40 ft at the doors = 28 ft brick + 2 x 6 ft bands = 480 in >= 466.5 (standing margin 467.0); at the portal the bands pass outside both 8 ft piers (6 ft each) -> 28 + 6 + 6 = 40 ft = 480 in; south to the public way 40 ft (site TBD, D-006). P2-C-101 Rev F.

TBD

- Door widths + hardware, E1 frontage (1030.2): architect. Aisles, rails, smoke-protected seating: TBD. Structure 1'-6" ASSUMED.

PUBLIC CORRIDOR (E) + X11, EXIT (E) CLEAR (D-072) — CHECK

Corridor 96 in ≥ 44 in (T1020.3); restroom + DF doors only onto it; dead end ≈ 5 ft ≤ 20 ft (1020.5); X11 64 in off it. EXIT (E): no doors or queues (1003.6), X7 on the wall, T1 133 ft. X7 / X11 discharge TBD (1028, D-006). Sources: P2-G-002 Rev D; P2-A-101 Rev J / A-102 Rev F (params/phase2_plan_rev_j.yaml); params/phase2_life_safety_rev_d.yaml; IBC 2021 1003.6, 1006.2.1, 1007.1, 1017.2-3, T1020.3, 1020.5, 1028, 1030.2-3, 2902.3.3; Shane 3:31 PM CT + evening (D-072).

# PRELIMINARY — CONCEPTUAL DESIGN — NOT FOR CONSTRUCTION

PROJECT

# Hazel Green Regional Athletic Complex

PHASE

# PHASE 2

SHEET TITLE

# EXTERIOR ELEVATIONS SCHEMATIC · COLOR

SCALE
AS

DATE

# October

REV
I

DRAWN BY

## Drawn by Claude (AI) for

SHEET
P2-A-201
X10 | X9

SIGNAGE ZONE — CONTENT TBD

# TROJAN HORSE ARENA

E1 MAIN ENTRY (building, behind)

## HAZEL GREEN REGIONAL ATHLETIC COMPLEX

SIDE PANEL (size ASSUMED)

BUILDING — SOUTH WALL (P2-A-101 Rev J) | E1

GAP ≈ 30' (ASSUMED)

CHAMPION WALK 28' x 30' = 840 SF (portal → doors, for now) Engraved donor / sponsor bricks: 4x8 single name · 8x8 family / business ≈ 3,700 4x8 (840 SF ÷ 0.222 SF = 3,780, less border + joints) · pricing TBD FREESTANDING PORTAL (2 piers, depth 6' ASSUMED)

BUS DROP LOOP: south, offset E or W of the portal view (D-034; site plan) | OPTION: extend the walk to parking later

KEY PLAN — PORTAL + CHAMPION WALK — 1" = 60'

north up · site plan: P2-C-101 Rev F

# TROJAN HORSE ARENA

BRAND DETAIL
PORTAL ATTIC
3/32" = 1'-0"

WORDMARK
CAP 27"

MARK Ø 11'-0"
SIZES ASSUMED

CROWN 34'

0'-0"

17'-9"

32'-9"

36'-0"

42'-0"

RESTROOM BUMP-OUT

beyond, 119' back (D-072)

WALL MATERIAL TBD

PARAPET TBD

PARAPET TBD

WALL MATERIAL TBD

ARENA VOLUME BEHIND (set back 34')

GRAND ENTRANCE PORTAL (FREESTANDING)

30' in front of the E1 doors (D-046) · 50' max (D-050) · see key plan

CRIMSON underside (D-045)

GOLD trim (D-045)

E1 ENTRY GLAZING TBD (building face, behind)

STRUCTURAL ENGINEER REQUIRED (freestanding portal)

CHAMPION WALK — BRICK, in front · Engraved donor / sponsor bricks
SOUTH ELEVATION (PRIMARY) — SCALE 1/16" = 1'-0" | portal 44' w x 50' h, 28' arch, crown 34' (ASSUMED, render proportions) · W ← → E

W E

X5 | X4

S1 SERVICE · SIZE TBD

17'-9"

32'-9"

42'-0"

NE STAIR TOWER (+6.67')

NORTH ELEVATION — 1" = 40'-0" (E ← → W)

STORAGE ANNEX (D-067)
70' x 30' · 16' ASSUMED

RESTROOM
BUMP-OUT
X8 | X11 | X7 | X6

ARENA VOLUME (flush with the east wall)

RESTROOM BUMP-OUT 30' x 56' (D-072) in front · 16' ASSUMED · X11 S of it, X7 N of it
17'-9" | ANNEX (beyond)

32'-9"

42'-0"

EAST ELEVATION — 1" = 40'-0" (S ← → N)

X3 | X2 | X1

ARENA VOLUME BEHIND (set back 49')

17'-9"

32'-9"

42'-0"

WEST ELEVATION — 1" = 40'-0" (N ← → S)

ANNEX

### FINISHES

LIMESTONE (portal) — Shane (material) CRIMSON (inside the arch) — Shane (color) GOLD (arch soffit) — Shane (color)
BRAND RED — Shane (red/black brand) BRAND BLACK — as brand red
WALL MATERIAL TBD — TBD
ARENA VOLUME — WALL / ROOF TBD — TBD ENTRY GLAZING (TBD) — TBD
BRICK (Champion Walk) — Shane (material)

### NOTES

- HEIGHTS: L2 FF 17'-9" (D-061 DECIDED), ring roof 32.75' (L2 + 15') ASSUMED. Arena clear ≥ 25' REFERENCE (NFHS via Draper, LA RAP; R-019). U/S structure 36', roof 42' ASSUMED. Upper tier steps DOWN from the loop: 21" risers, front row 9.0' (7'-6" clear, D-061); highest aisle = loop 17.75' (1030.6.2.2 if smoke-protected: ≥ 32.75'; 36' U/S drawn).
- PORTAL: FREESTANDING limestone arch 30' in front of the E1 doors over Champion Walk (D-043, D-046); 50' max (D-050): crown 34', springline 22.1', depth 6' ASSUMED; underside crimson + gold trim (D-045). STRUCTURAL ENGINEER REQUIRED.
- BRAND: official mark Ø 11' (Shane, D-047) at 34.4'-45.4'; wordmark 27" caps, baseline 46.1' (inside the 44' x 50' portal) + side panel, ASSUMED sizes. Trademark search before signage / apparel OPEN (D-042).
- CHAMPION WALK: 28' x 30' brick (for now, D-046); 4x8 single name, 8x8 family / business; ≈ 3,700 4x8; pricing OPEN (D-044); may extend to parking. Bus drop: south, offset E or W (D-034).
- DOORS: symbols (6' x 8' ASSUMED) from P2-A-101 Rev J; X# EXIT ONLY (D-033); X7 on the wall, X11 off the public corridor, S1 on the annex, size TBD.
- OUTLINE (P2-A-101 Rev J): storage annex 70' x 30' on the north wall (D-067) + restroom bump-out 30' x 56' on the east wall, south of EXIT (E) (D-069 / D-072), one storey, 16' ASSUMED. X7 on the wall, X11 new. Roofs / finishes TBD.
- NOT SHOWN: rooftop units, grading, lighting.
- OPEN QUESTION: ETFE roof / solar (aspirations) — not designed, not in the SF or budget.

COURT 84' (plan) EVENT FLOOR; LOBBY / HALL OF CHAMPIONS (double height); SECURITY (size TBD); < TELESCOPIC LOWER; < FIXED UPPER; TELESCOPIC LOWER >; FIXED UPPER >; LOOP; EVENT LOCKER 1 (full 3,600 SF, D-060); ≥ 7'-6" CLEAR; UNDER ROW 1; exit paths clear (D-061); ARENA ROOF 42' (ASSUMED); RING ROOF 32.75' (ASSUMED); 36' TO U/S STRUCTURE (ASSUMED) ≥ 25' CLEAR — REFERENCE (R-019); RING 32.75' A; ROOF 42' A; EVENT FLOOR (no west tier, Rev F); BOYS LOCKER; ATH.; CORR.; STRENGTH & CONDITIONING (L2); LKR 4 (full ht); 42" GUARD (G-W)

# PRELIMINARY — CONCEPTUAL DESIGN — NOT FOR CONSTRUCTION

PROJECT

# Hazel Green Regional Athletic Complex

PHASE

# PHASE 2

SHEET TITLE

# BUILDING SECTIONS SCHEMATIC · COLOR

SCALE
AS

DATE

# October

REV
D

DRAWN BY

## Drawn by KEYSTONE (AI) for

SHEET
P2-A-301

LONG-SPAN STRUCTURE ZONE 36'–42' (not engineered)

### 1 SECTION A-A (NORTH-SOUTH) — looking west

1/32" = 1'-0" · x = 100 (see key plan)

LONG-SPAN STRUCTURE ZONE 36'–42' (not engineered)

### 2 SECTION B-B (EAST-WEST) — looking north

1/32" = 1'-0" · y = 150 (see key plan)

L1 FF 0'

L2 17.75'

RING 32.75' A

U/S 36' A

ROOF 42' A

TELESCOPIC LOWER TIER (extended)

6 rows × 24" = 12' band (R-008 / plan)
rise 11⅝"/row — Hussey MAXAM option (CITED); choice of 11⅝" ASSUMED

top seat 6'-3⅛" (Hussey, 6 rows @ 11⅝")

closed 3'-6" (Hussey, 6 rows)

FIXED UPPER TIER (ASSUMED rake)

5 rows × 36" = 15' band (plan)
21"/row = 3 aisle risers × 7", 12" treads (IBC 1030.14.2: 4–8" risers, ≥ 11" treads) steps DOWN from the loop; front row 9.00'

≥ 26" fascia (1030.17.3)

LOOP 7'

2 × 42" lanes

top cross aisle

STRETCH
6' (L2)

NO LOW BAND (D-061, Option B): row 1 clear 7.5' = 7'-6" (1003.2,
no margin; 1.5' structure A)
rows 2–5 9.25'–14.5'

EVENT LOCKER 1 (full, D-060) from y 224 (tier line), A-101 Rev F

SIGHT LINES: P2-A-302 Rev C — 21"/row, L2 17'-9"

seated C min 149 mm N/S, 101 mm E (≥ 90 target)

EXIT (N) x 123.85–131.85: clear ≥ 7'-6" under row 1 (D-061)

1030.6.2.2 (only if smoke-protected): roof ≥ 15' above

highest aisle (loop 17.75') → ≥ 32.75'; 36' drawn

### 3 NORTH BOWL EDGE (ENLARGED PART OF A-A)

3/32" = 1'-0" · y 196–252 at x = 100

16 R @ 6.87" = 9.16'
15 T @ 11" = 13.75'

76" mid
landing

= width

(1011.6)

48" floor

landing

INTERMEDIATE HANDRAIL (C-7)

on the 76" centerline, 1014.9

— architect to confirm

L2 FF 17'-9"

+ flight 2: 15 R

L1 FF 0'

flight 2 beyond

(dashed)

31 risers total

76" clear width

(not visible in section)

### 4 TYPICAL EXIT STAIR — 76" CLEAR, 31 R

3/32" = 1'-0" · 76" mid landing · 12.67' × 24.08' plan (D-061)

A

A

B B

N

### 5 KEY PLAN — CUTS

1" = 128' · north up

CUT: slab / wall / roof (graphic) | ARENA VOLUME | EVENT FLOOR
TELESCOPIC LOWER TIER | FIXED UPPER TIER | LOOP (L2)
LOBBY | ROOMS / SUPPORT | LONG-SPAN STRUCTURE ZONE

HEIGHTS USED (ft above L1 FF 0'-0")
- L2 FF 17'-9" (D-061 DECIDED, Option B). Ring roof 32.75' = L2 + 15' — ASSUMED. Arena structure underside 36', roof 42' — ASSUMED (court clear unchanged).
- Arena clear ≥ 25' — REFERENCE (NFHS court specs via Draper; LA RAP gym standard; R-019), not a code minimum (C-5). 36' drawn = 11' over it.
- Slabs, walls, roof graphic only. Upper-tier deck structure 1.5' under each tread — ASSUMED.
SEATING (P2-A-101 Rev F)
- Lower: telescopic, 6 rows × 24", 11⅝" rise (Hussey MAXAM option, CITED; choice ASSUMED); east front 16' from the nearest mat (D-053); building 210' wide.
- Upper: fixed, 15' band, 5 rows × 36", 21"/row (D-061) = 3 aisle risers × 7", 12" treads (1030.14.2: 4–8", ≥ 11"); steps DOWN from the loop (D-049) to a 9.0' front row.
- UNDER THE UPPER TIER: row 1 clear 7.5' = 7'-6" (1003.2 minimum, no margin), rows 2–5 9.25'–14.5'. No low band: EXIT (N), EXIT (E), SE concourse, lobby / portal / athlete route are clear. Event lockers run to the tier line (3,600 SF, D-060).
- SIGHT LINES: P2-A-302 Rev C (21"/row, L2 17'-9"): seated C min 149 mm N/S, 101 mm E; standing 127 / 72 mm (lower tier governs).

GUARDS
- Loop open edges G-W (x = 56) and G-S (y = 34): 42" (IBC 2021 1015.2 / 1015.3). Upper-tier front fascia ≥ 26" (1030.17.3), 36" at aisle feet (1030.17.4).
STAIRS (ST-1..ST-4)
- 76" clear (D-052). 31 R @ 6.87" (213" ÷ 31, ≤ 7", 1011.5.2), flights 16 + 15, 15 treads × 11" = 13.75'; 76" intermediate landing = width (1011.6, D-051); 48" floor landings. Per stair 12.67' × 24.08' = 305.1 SF per level (Rev C 270.2).
- Intermediate handrail on the centerline of each 76" stair so all width is within 30" of a rail (IBC 2021 1014.9; D-052 'with intermediate handrails') — shown in detail 4; architect to confirm (C-7).
ROOF HEIGHT (1030.6.2.2, if smoke-protected)
- Lowest roof deck ≥ 15' above the highest aisle: loop 17.75' → ≥ 32.75'. Arena U/S structure 36' drawn = 3.25' margin (deck higher). Ring roof 32.75' is over the perimeter rooms, not the seating.
ELEVATOR
- EL-1 travel 17'-9" (was 15'); hoistway / pit / overrun by the elevator supplier (not drawn).
CUTS
- A-A: x = 100, looking west. B-B: y = 150, looking north. Geometry from P2-A-101/102 Rev F. Colors graphic only; 'A' = ASSUMED.

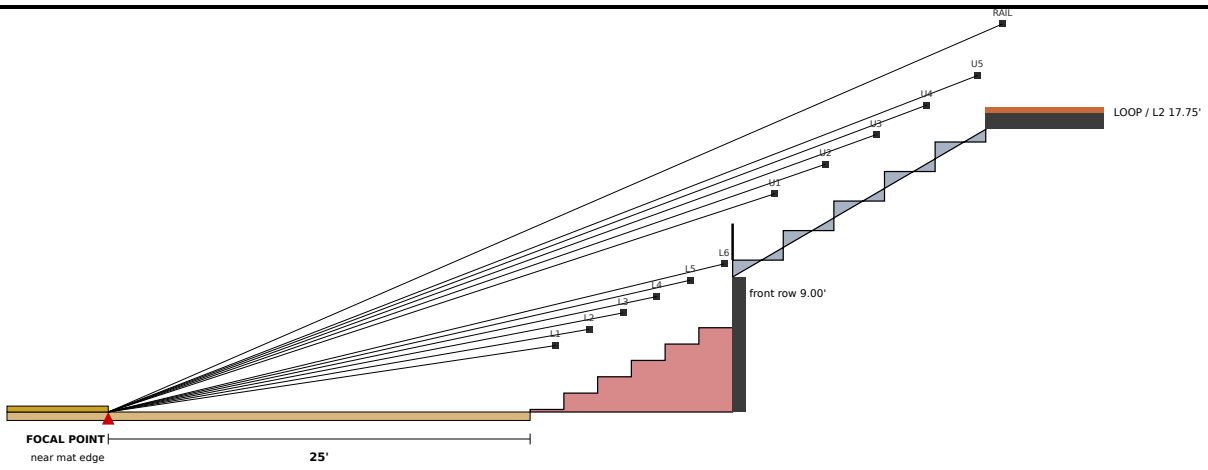
[picture p13: figure]
FOCAL POINT; near mat edge; RAIL; LOOP / L2 17.75'; front row 9.00'
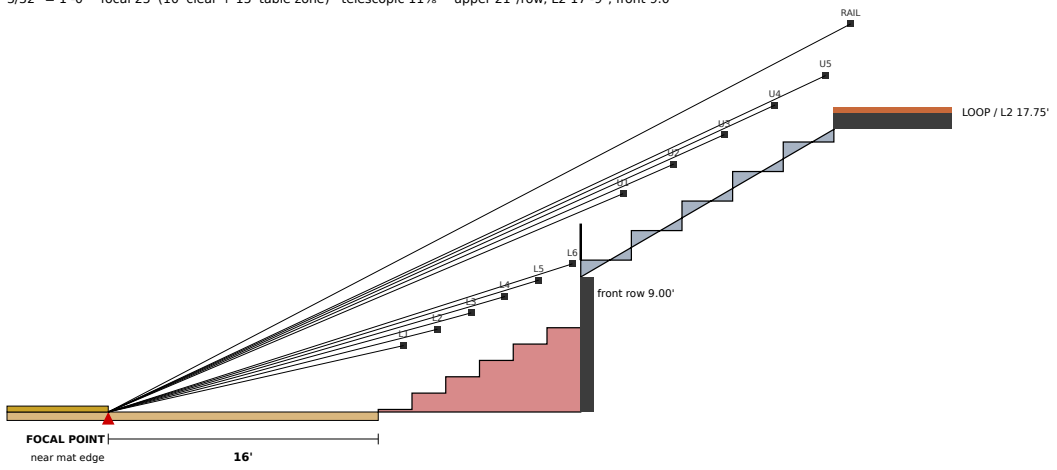
[picture p14: figure]
FOCAL POINT; near mat edge; RAIL; LOOP / L2 17.75'; front row 9.00'
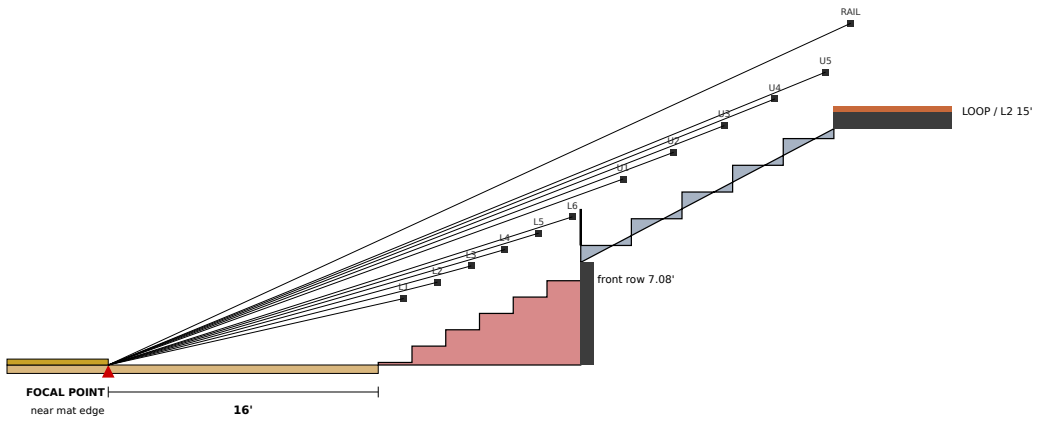
[picture p15: figure]
FOCAL POINT; near mat edge; RAIL; LOOP / L2 15'; front row 7.08'

# PRELIMINARY — CONCEPTUAL DESIGN — NOT FOR CONSTRUCTION

PROJECT

# Hazel Green Regional Athletic Complex

PHASE

# PHASE 2

SHEET TITLE

# SIGHT-LINE STUDY SCHEMATIC · COLOR

SCALE
AS

DATE

# October

REV
C

DRAWN BY

## Drawn by KEYSTONE (AI) for

SHEET
P2-A-302

### 1 AS DRAWN (REV F) — NORTH / SOUTH SIDE (seated eyes)

3/32" = 1'-0" · focal 25' (10' clear + 15' table zone) · telescopic 11⅝" · upper 21"/row, L2 17'-9", front 9.0'

### 2 AS DRAWN (REV F) — EAST SIDE (seated eyes)

3/32" = 1'-0" · focal 16' (D-053) · upper 21"/row, L2 17'-9" · worst side

### 3 REV E BASIS (SUPERSEDED) — EAST SIDE (seated eyes)

3/32" = 1'-0" · focal 16' · L2 15' · upper 19"/row, front 7.08' · P2-A-302 Rev B 'as drawn'

SIGHTLINE GRADE (C, mm)

≥ 90 PASS

60–90 MARGINAL

< 60 FAIL

Dots = eyes; label colour = C of that row over the row in front. Values: table.

upper-tier deck (front 9.00')

upper-tier face

CLOSED

STACK

front deck 9.00' − 77.4"

= 30.6" structure + finish

recess min 48" deep x

77.4" high (Hussey)

Rev E 7.08' front: 7.6" left

upper-tier deck (front 9.00')

upper-tier face

7'-6" ceiling over row 6 (1003.2) = 12.34'

deck at recess back 11.33' − structure

rows 5-6 stay in the recess

under the overhang when open

need

### 4 TELESCOPIC STACK UNDER THE UPPER-TIER FRONT

3/16" = 1'-0" · recessed (Hussey) · N/S as drawn 9.0' · dashed = Rev E 7.08'

(a) CLOSED — fits only if structure ≤ 30.6" (as drawn)
(b) OPEN — rows 5-6 under the overhang: CONFLICT
AS DRAWN (P2-A-101 Rev F / A-301 Rev D) | REV E BASIS (superseded)

N/S 25'
seated

N/S 25'
stand

E 16'
seated

E 16'
stand

N/S 25'
seated
| N/S 25' stand E 16' seated

E 16'
stand

ROW

L2 | 190 | 162 | 142 | 101 | 190 | 162 | 142 | 101
L3 | 178 | 152 | 129 | 92 | 178 | 152 | 129 | 92
L4 | 167 | 142 | 118 | 84 | 167 | 142 | 118 | 84
L5 | 157 | 134 | 109 | 77 | 157 | 134 | 109 | 77
L6 | 149 | 127 | 101 | 72 | 149 | 127 | 101 | 72
U1 | 967 | 937 | 879 | 840 | 428 | 397 | 352 | 313
U2 | 217 | 189 | 133 | 97 | 211 | 183 | 139 | 103
U3 | 203 | 177 | 122 | 89 | 198 | 171 | 127 | 94
U4 | 191 | 166 | 112 | 82 | 185 | 161 | 118 | 87
U5 | 179 | 156 | 105 | 76 | 175 | 151 | 109 | 81
RAIL (stands) | 736 | 336 | 696 | 296 | 709 | 309 | 673 | 273
fascia clr (U1) | 289 | 664 | 215 | 583 | 326 | 701 | 263 | 631
front row (ft) | 9.00 | 9.00 | 9.00 | 9.00 | 7.08 | 7.08 | 7.08 | 7.08

METHOD
- C = D(N + R)/(D + T) − R (Green Guide 12.3), computed from each actual eye position (also covers the step between tiers and the loop rail). Focal point = near edge of the nearest mat at floor level (Shane). Eyes: seated 1.2 m above the tread, 0.15 m forward of the row's rear edge; standing 1.6 m (5'-3") — secondary sources, see R-020. Grades: ≥ 90 mm PASS (FIFA preferred, CEN/TR 15913 new stands), 60–90 MARGINAL, < 60 FAIL (FIFA minimum 60).
- Focal distances from P2-A-101 Rev F: N and S tier fronts 25' from the nearest mat (10' clear + 15' table zone); E tier front 16' (D-053). No west tier. Section-only study (2D); corners and wheelchair positions TBD.
RESULTS — AS DRAWN (REV F, D-061 DECIDED)
- L2 FF 17'-9", upper 21" per 36" row (3 aisle risers of 7", 12" treads; IBC 1030.14.2), front row 9.0'. Every seated row PASSES: N/S ≥ 149 mm, E ≥ 101 (lower tier governs, same as Rev E). Upper tier seated N/S ≥ 179, E ≥ 105.
- Standing: N/S ≥ 127; E ≥ 72 (L4–L6 and U3–U5 MARGINAL, none FAIL). U1 clears the 26" fascia (289 mm N/S, 215 E seated).
REV E BASIS (SUPERSEDED, P2-A-302 Rev B 'as drawn')
- L2 15', 19"/row, front 7.08': same lower-tier minimums; upper seated N/S ≥ 175, E ≥ 109; standing E ≥ 81. Kept for comparison only.
TELESCOPIC STACK UNDER THE UPPER-TIER FRONT (D-049)
- Closed stack, recessed (Hussey min 4'-0" deep x 6'-5⅜" high) under the 9.0' front leaves 30.6" for structure + finish (1.5' = 18" ASSUMED) — FITS closed. Open: rows 5–6 still sit under the overhang (< 7'-6", 1003.2): keep the stack in front of the upper-tier face (as P2-A-301 Rev D).
EXIT PATHS (D-061 DECIDED, Option B)
- 1.5' tier structure (ASSUMED) leaves 7'-6" under row 1 (1003.2 minimum, no margin) and 9.25'+ under rows 2–5: no low band; Exit N, Exit E, SE concourse and the lobby / portal / athlete-route edge are clear. 0 seats lost.

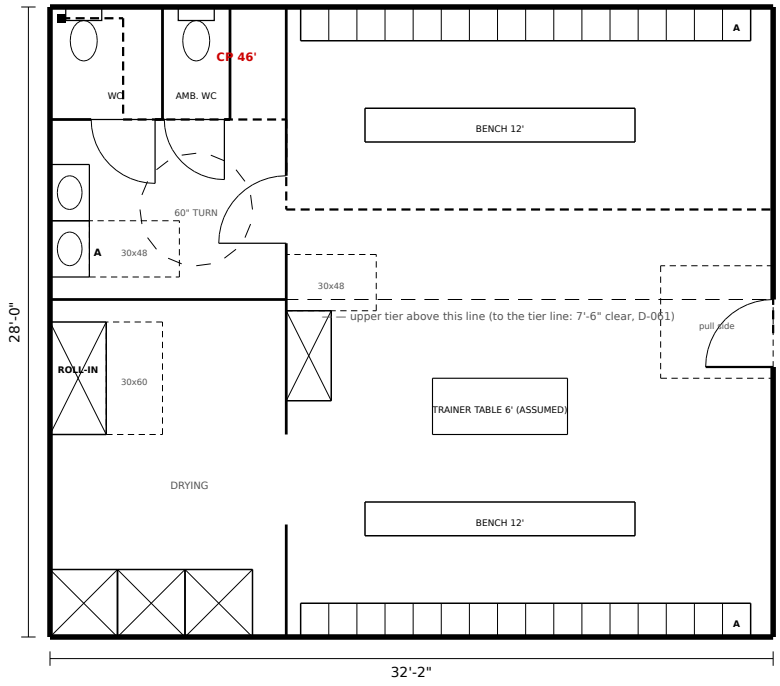
[picture p16: figure]
AMB. WC; 60" TURN; ROLL-IN; DRYING; BENCH 12'; TRAINER TABLE 6' (ASSUMED); pull side
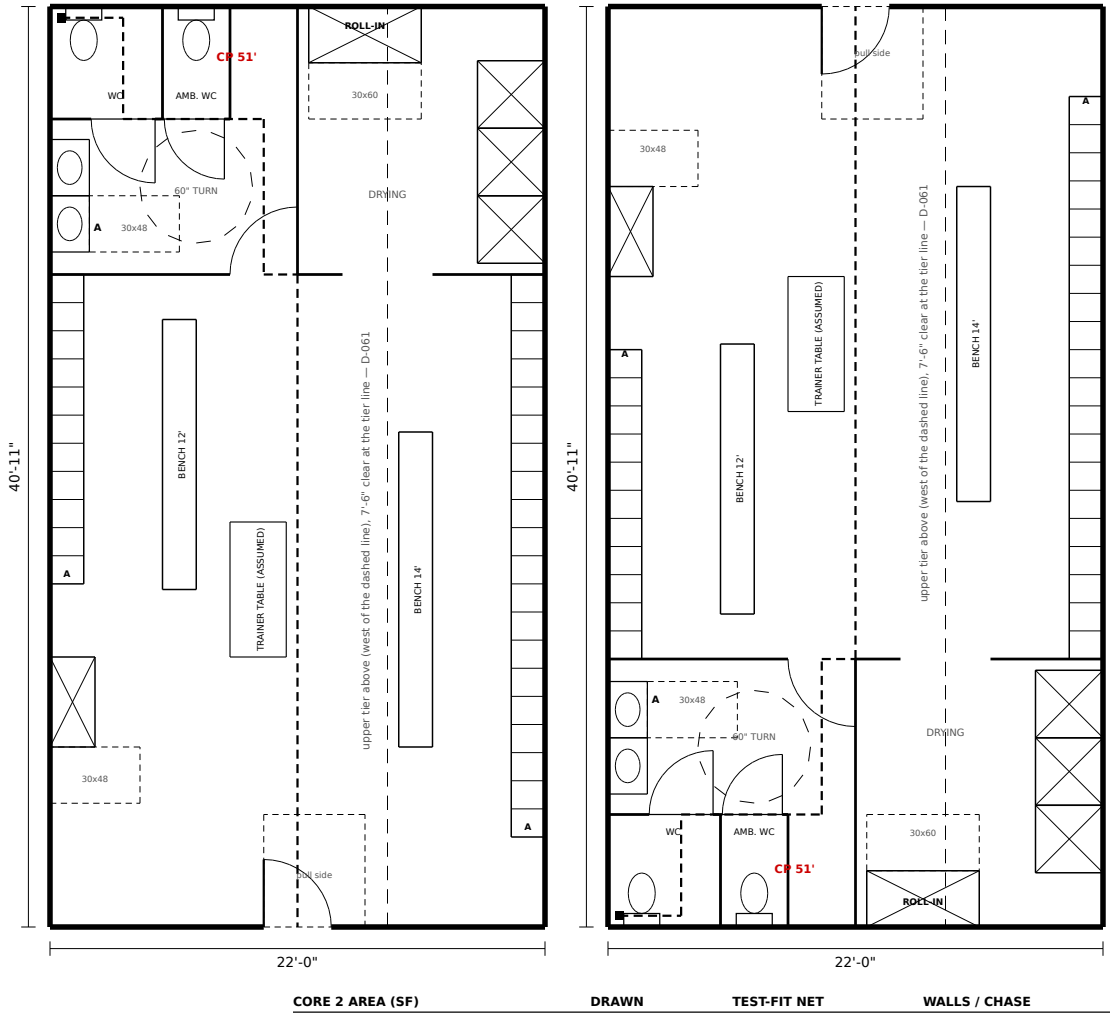
[picture p17: figure]
AMB. WC; 60" TURN; ROLL-IN; DRYING; BENCH 12'; BENCH 14'; TRAINER TABLE (ASSUMED); pull side; CORE 2 AREA (SF); DRAWN; TEST-FIT NET; WALLS / CHASE
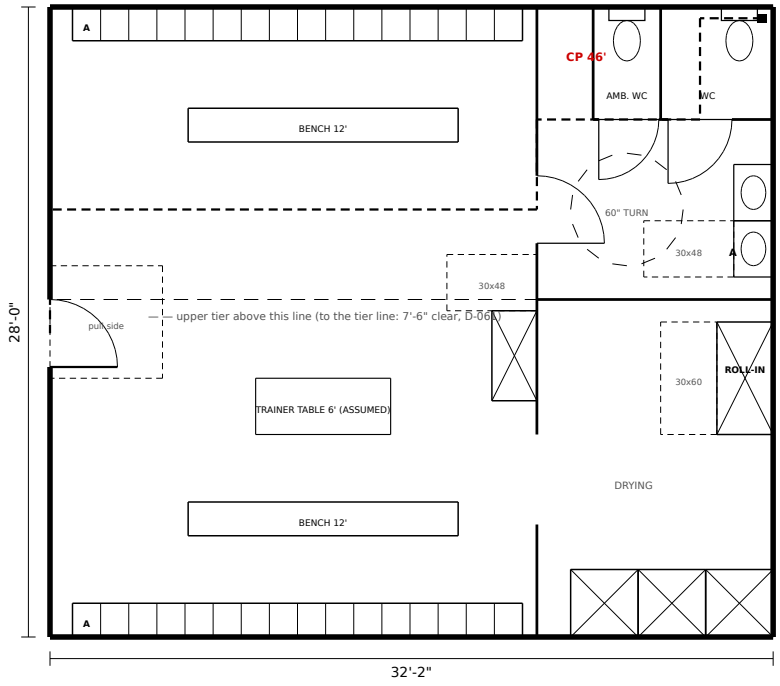
[picture p18: figure]
AMB. WC; 60" TURN; ROLL-IN; DRYING; BENCH 12'; TRAINER TABLE 6' (ASSUMED); pull side
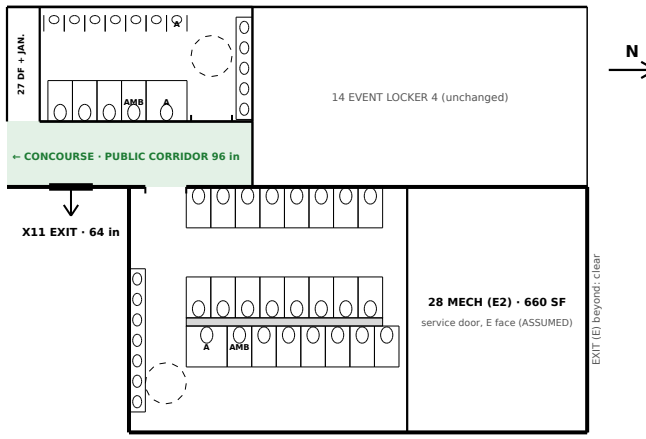
[picture p19: figure]
A AMB; AMB; X11 EXIT · 64 in; 14 EVENT LOCKER 4 (unchanged); EXIT (E) beyond: clear

# PRELIMINARY — CONCEPTUAL DESIGN — NOT FOR CONSTRUCTION

PROJECT

# Hazel Green Regional Athletic Complex

PHASE

# PHASE 2

SHEET TITLE

# ENLARGED PLANS LOCKER RMS + RESTROOM CORE 2

SCALE
AS

DATE

# October

REV
D

DRAWN BY

## Drawn by Claude (AI) for

SHEET
P2-A-401

— — upper tier above this line (to the tier line: 7'-6" clear, D-061)

EVENT LOCKER ROOM 1 — 900 SF · 18 occ.

1/8" = 1'-0" · door on the E wall → EXIT (N) passage · common path 46 ft ≤ 75 (PASS)

— — upper tier above this line (to the tier line: 7'-6" clear, D-061)

EVENT LOCKER ROOM 2 — 900 SF · 18 occ.

1/8" = 1'-0" · door on the W wall → EXIT (N) passage · common path 46 ft ≤ 75 (PASS) upper tier above (west of the dashed line), 7'-6" clear at the tier line — D-061

EVENT LOCKER ROOM 3 — 900 SF · 18 occ.

1/8" = 1'-0" · door on the S wall → EXIT (E) passage · common path 51 ft ≤ 75 (PASS)

upper tier above (west of the dashed line), 7'-6" clear at the tier line — D-061

EVENT LOCKER ROOM 4 — 900 SF · 18 occ.

1/8" = 1'-0" · door on the N wall → EXIT (E) passage · common path 51 ft ≤ 75 (PASS)

1 2

3

4

M W

CORE 2

KEY PLAN — L1 (A-101 J)
1" = 250' · grey = rooms 1-4

blue = restrooms · green = public corridor (E)

Schematic enlarged plans: fixture counts, benches, lockers and showers ASSUMED (KEYSTONE). Accessible fixture sizes are ADA 2010 minimums for the architect to develop; not a code review (D-008).

COMMON PATH — VERIFIED ON THIS LAYOUT (T1006.2.1)

One exit access doorway allowed when the space holds <= 49 occupants and the common path of egress travel is <= 75
ft (Group A, sprinklered) — IBC 2021 1006.2.1, Table 1006.2.1.
ROOM | OCC. | WORST POINT | CP ft | RESULT | + TO EXIT
1 | 18 | accessible WC far corner | 45.6 | ≤ 75 PASS | X5 64 ft
2 | 18 | accessible WC far corner | 45.6 | ≤ 75 PASS | X5 64 ft
3 | 18 | accessible WC far corner | 50.9 | ≤ 75 PASS | X7 66 ft
4 | 18 | accessible WC far corner | 50.9 | ≤ 75 PASS | X7 66 ft
Rooms 1-4 unchanged (Rev A approved, D-068). Rooms 3-4 reach X7 on the building wall again (EXIT (E) clear, D-072):
travel ≤ 66 ft vs 250 ft (T1017.2). Locker fixtures as Rev A (ADA 604.8, 606, 608, 803, 811, 903).

L1 PUBLIC RESTROOMS — CHAIRS-ONLY (D-064 · D-069 · D-072)

L1 load chairs-only 2,346 + 1,100 = 3,446 (IBC 2021 T2902.1, 50/50 split 2902.1.1). Lobby core = rooms 4 + 5; core 2 = women (2) in the bump-out + men (2) and DF in the old Mech (E) strip, all off the public corridor (E).
FIXTURE | REQ. | LOBBY | CORE 2 | TOTAL | RESULT
Men WC (incl. urinals) | 22 | 10 | 5 + 7 ur | 22 | PASS
Men lavatories | 9 | 4 | 5 | 9 | PASS
Women WC | 42 | 18 | 24 | 42 | PASS
Women lavatories | 12 | 5 | 7 | 12 | PASS
Drinking fountains | 4 | 2 | 2 (hi-lo) | 4 | PASS
Urinals: core 2 7 ≤ 8 = 67 % of its 12 (IPC 2021 424.2, R-009). 1 accessible urinal (ADA 213.3.3, 605); 1 wheelchair + 1 ambulatory compartment per room (213.3.1, 604.8); 1 accessible lav (606); 60 in turning space (304.3); hi-lo fountains (211.2, 602).

← CONCOURSE · PUBLIC CORRIDOR 96 in ²⁷ DF + JAN.

| 28 MECH (E2) · 660 SF service door, E face (ASSUMED)

### 26 WOMEN (2) · 1,020 SF · 24 WC · 7 LAV

### 25 MEN (2) · 364 SF · 5 WC + 7 UR · 5 LAV

bump-out 56'-0" (N-S) x 30'-0" (E-W) = 1,680 SF, one storey

RESTROOM CORE 2 + PUBLIC CORRIDOR (E) — D-072 · ENLARGED PLAN

1" = 22'-0" · plan turned: north → right, east → down · test-fits ASSUMED

A = accessible · AMB = ambulatory · dashed circle = 60 in turning space · grey = chase · ticks = room entry

Women (2), 30 x 34 (bump-out) | 1,020 | 957 | +6.6 %
Mech (E2), 30 x 22 (bump-out) | 660
BUMP-OUT 30 x 56 (A-101 J) | 1,680
Men (2), 14 x 26 (strip) | 364 | 331.5 | +9.8 %
DF alcove + janitor, 14 x 4 | 56
Public corridor (E), 8 x 78.18 | 625
Mech (E), 14 x 48.18 | 674.5 | | was 1,720
OLD MECH (E) STRIP 22 x 78.18 | 1,720 | | GSF ±0
WHY THE CORRIDOR (D-072): on plan Rev I the public reached core 2 only through V2 / EXIT (E) — across the event floor, with restroom queues in the exit passage. Rev J slides the bump-out 42 ft south (entirely south of EXIT (E)) and adds an 8 ft public corridor from Concourse (E), behind the tier line: restroom doors open only onto it, EXIT (E) stays clear, and X11 gives the corridor its own exit (common path 61 ft <= 75).
MEP (OPEN): Mech (E) 1,720 -> 674.5 SF + MECH (E2) 660 SF; total mech ≈ 3,496 SF = 4.1 % of 85,793 GSF vs 5 % planning (R-014). Engineer to confirm; the storage annex (north) can absorb ~800 SF later. Plumbing: men's (strip) and women's (bump-out) wet walls meet across the corridor; waste / vent under slab (ASSUMED).
Public toilets within one storey and 500 ft of every seat (IBC 2902.3.3): PASS. Dead end past the last door ≈ 5 ft ≤ 20 ft (1020.5).
Sources: params/phase2_enlarged.yaml, phase2_enlarged_rev_d.yaml, phase2_plan_rev_j.yaml, phase2_program.yaml (rev_k); IBC 2021 T2902.1, 2902.3.3, 1003.6, 1006.2.1, 1020.5, T1017.2; IPC 2021 405.3.1, 405.3.5, 424.2; ADA 2010 211.2, 213.3, 304.3, 602, 604.8, 605, 606; D-064, D-068, D-069, D-070, D-072; R-014; Shane 2026-10-04 evening.

service apron at S1 — diagram (D-034); ROAD assumed south (site TBD, D-006)
side panel (A-201 Rev G); arena volume flush with the east wall
NE STAIR TOWER
LOBBY — open to below; SCREENING BAY floor zone (D-065); storage annex, cut; restroom bump-out, cut (D-072)

# PRELIMINARY — CONCEPTUAL DESIGN — NOT FOR CONSTRUCTION

PROJECT

# Hazel Green Regional Athletic Complex

PHASE

# PHASE 2

SHEET TITLE

# 3D MASSING MODEL VIEWS

SCALE

# NTS

DATE

# October

REV
D

DRAWN BY

## Drawn by Claude (AI) for

SHEET
P2-A-901

V1 AERIAL FROM SOUTHWEST

axonometric · not to scale

ARENA VOLUME — roof 42' ASSUMED (wall / roof TBD)

RING — roof 32.75' ASSUMED · L2 FF 17.75' DECIDED

FREESTANDING PORTAL 50' max (D-043, D-050)

CHAMPION WALK 28' brick + 6' bands = 40' (D-066)

STORAGE ANNEX 70' x 30', 16' ASSUMED (D-067)

BUS DROP LOOP — diagram (D-034; C-101 Rev C)

N

V2 CUTAWAY AT L2 FF 17'-9" FROM SOUTHWEST — ROOFS REMOVED

axonometric · not to scale · roofs removed, L1 ring cut solid at L2 FF

EVENT FLOOR 120' x 144' + 4 x 42' mats (A-103 Rev A)

FIXED UPPER TIER — 5 rows, 21" risers, front row 9.0' (D-061)

TELESCOPIC LOWER TIER — extended, 6 rows (D-009)

L1 RING (rooms not modelled) CUT AT L2 FF 17.75'

V3 AERIAL FROM SOUTHEAST

axonometric · not to scale

RESTROOM BUMP-OUT 30' x 56', 16' ASSUMED (D-072) · X11 S, X7 N

N

V4 AERIAL FROM NORTHWEST (SERVICE SIDE, S1)

axonometric · not to scale

S1 SERVICE / LOADING (D-034) on the storage annex (D-067)

N

V5 PORTAL + CHAMPION WALK FROM SOUTH-SOUTHWEST

axonometric · not to scale

official mark Ø 11' (D-041, D-047)

50' max · crown 34' · springline 22.1' (D-050)

gold trim (D-045)

40' walk: 6' bands pass outside both piers (D-066)

E1 door bank, 30' behind the portal (D-046)

MASSING ONLY. Volumes from the current schematic params; materials, openings, parapets, roof equipment and structure are not designed. Every height not marked DECIDED is ASSUMED (P2-A-201 Rev G). Not a rendering of a final design.

HEIGHTS MODELLED

L2 FF 17.75' DECIDED (D-061) · ring roof 32.75' ASSUMED · arena roof 42' ASSUMED (P2-A-201 Rev
G) · portal 50' max, crown 34', springline 22.1' (D-050) · tiers per P2-A-301 Rev D / A-302 Rev C. Door symbols 6' x 8' ASSUMED.

DECISIONS MODELLED — SHANE 3:31 PM CT + EVENING (D-072)

- D-054 DECIDED: chairs-only floor is the design case — no stage / chairs modelled (layout TBD).
- D-065 DECIDED: screening bay in the lobby's east side, shown as a floor zone in the cutaway.
- D-066 DECIDED: 40 ft walk = 28 ft brick + 6 ft bands, around both portal piers.
- D-067 DECIDED: storage annex 70 x 30 ft on the north wall, one storey (16 ft ASSUMED), S1 on its north face.
- D-069 DECIDED: restroom core 2 in a one-storey bump-out 30 x 56 ft on the east wall (16 ft ASSUMED).
- D-072 DECIDED: bump-out slid 42 ft south, entirely south of EXIT (E); public corridor (E) inside (not modelled); X7 back on the wall, X11 new.

NOTES

- NOT MODELLED: parapets (TBD), rooftop units, structure, windows / cladding, grading, landscaping, lighting, parking (site TBD, D-006), signage content (signage zone TBD), interior rooms.
- Colours: limestone / crimson / gold / brick / brand red + black from P2-A-201 Rev G finishes (hex ASSUMED swatches); greys = material TBD. Arch drawn as a 56-segment polyline; the crimson underside faces down and does not show in views from above.
- Model file: phase2/out/3d/P2-A-901_RevD_massing.obj + .mtl (feet, Y-up export; exterior, cutaway and portal sets).
Sources: params/phase2_massing.yaml, phase2_massing_rev_d.yaml; phase2_plan_rev_j.yaml; phase2_elev_rev_g.yaml; phase2_elev.yaml; phase2_site.yaml (rev_f); phase2_sect.yaml; D-034, D-043, D-045, D-046, D-050, D-054, D-061, D-065 to D-067, D-069, D-072; Shane 2026-10-04 evening. P2-A-201 Rev I shows the annex + bump-out.
