thebardchat/TrojanHorseAreana/blueprints/phase2/out/pdf/P2-A-102_RevG.pdf

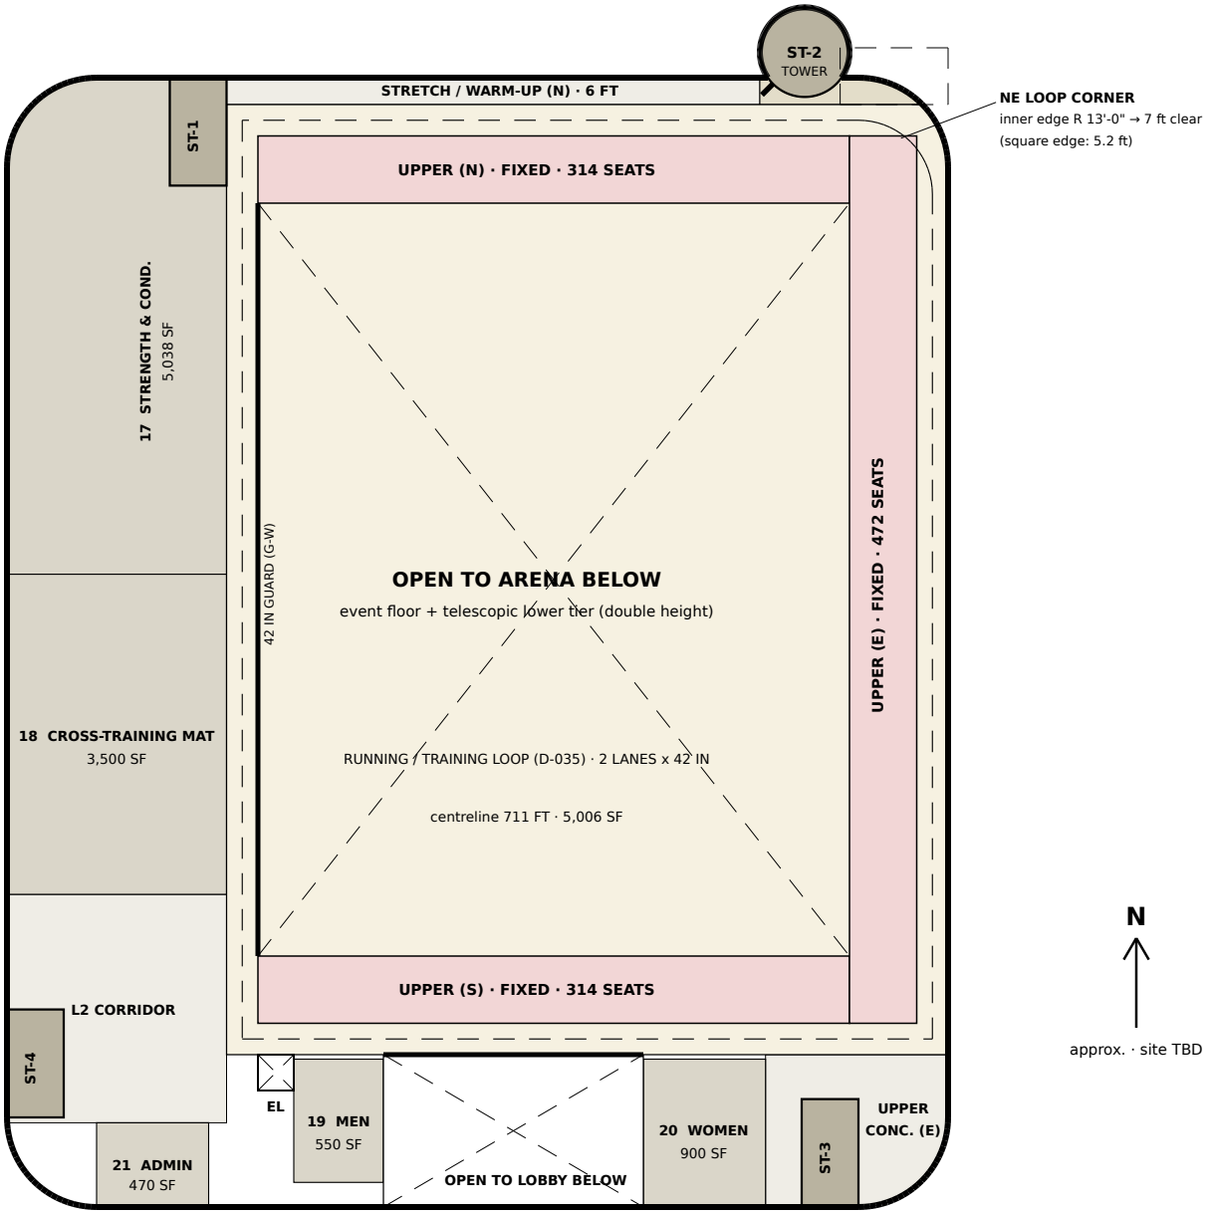
[picture p20: figure]
ST-2 TOWER; 17 STRENGTH & COND.; 18 CROSS-TRAINING MAT 3,500 SF; L2 CORRIDOR; 19 MEN 550 SF; 20 WOMEN 900 SF; 21 ADMIN 470 SF; UPPER CONC. (E); OPEN TO LOBBY BELOW; OPEN TO ARENA BELOW; STRETCH / WARM-UP (N) · 6 FT; UPPER (N) · FIXED · 314 SEATS; UPPER (S) · FIXED · 314 SEATS; UPPER (E) · FIXED · 472 SEATS; centreline 711 FT · 5,006 SF; 42 IN GUARD (G-W); NE LOOP CORNER inner edge R 13'-0" → 7 ft clear (square edge: 5.2 ft); approx. · site TBD

# PRELIMINARY — CONCEPTUAL DESIGN — NOT FOR CONSTRUCTION

PROJECT

## Hazel Green Regional Athletic Complex Trojan Horse Arena · Hazel Green area, Madison County, Alabama (site TBD, D-006)

PHASE

# PHASE 2

SHEET TITLE

## OVERALL FLOOR PLAN LEVEL 2 · BLOCK PLAN

SCALE
1" =
40'-0"

DATE

# October

2026

REV
G

DRAWN BY

## Drawn by Claude (AI) for Shane Brazelton

SHEET

P2-A-102

event floor + telescopic lower tier (double height)

RUNNING / TRAINING LOOP (D-035) · 2 LANES x 42 IN

210'-0" (box; R = 20'-0" corners; L2 FF 17'-9")

252'-0"

# SCHEMATIC — BLOCK PLAN, CONCEPT ENVELOPE

## LEVEL 2 — OVERALL FLOOR PLAN (REV G)

Rev F Level 2 (frozen) inside the Rev K envelope (R = 20 ft, D-077; P2-A-101 Rev K approved, D-079). Rooms, tiers, guards and seat counts are Rev F unless listed under CHANGES. Rev F dashed outline shows the old NE stair projection.

## CHANGES FROM REV F (all ASSUMED)

- Envelope: box with R = 20 ft corners; S&C (17) and the L2 corridor lose the NW / SW corner area; upper concourse (E) loses the SE corner.
- ST-2 is the 20 ft cylindrical tower (centre 178, 257.7). It replaces the 24.08 x 12.67 ft NE stair, so the north stretch strip now ends at x 168 and the tower is entered from the strip by a door on its SW face (no L2 door on the loop).
- ST-3 and ST-4 as Rev K (slid along their walls); same L2 position as L1, rooms trimmed around them.
- NE loop corner: the 20 ft arc cuts the loop's outer corner; with a square inner edge the clear width drops to 5.2 ft (7 ft = 2 lanes x 42 in needed). Inner edge rounded to R 13 ft keeps 7 ft; the tier corner loses 4.6 SF (under 1 seat).

## ROOM SCHEDULE — LEVEL 2 (SF net of stairs, inside the Rev G envelope)

TAG | ROOM | REV F | REV G | CHANGE
— | Upper tier, fixed (1,100 seats) | 6,930 | 6,930 | 0
— | Running / training loop | 5,026 | 5,006 | -20
17 | Strength & Conditioning | 5,124 | 5,038 | -86
18 | Cross-Training Mat | 3,500 | 3,500 | 0
19 | Men | 550 | 550 | 0
20 | Women | 900 | 900 | 0
21 | Admin | 470 | 470 | 0
— | L2 Corridor | | 2,192
— | Upper Concourse (E) | | 994
— | Stretch / Warm-up (N) | | 714
| ST-2 landing / NE corner (not programmed) | | 141

## AREA CHECK (no SF cap, D-056; L1, L2, total vs Rev J, D-057)

REV J | REV K/G | CHANGE
L1 footprint (P2-A-101 Rev K) | 56,861 | 57,520 | +659
L2 area (envelope - open-to-below) | 28,933 | 28,692 | -241
TOTAL GSF | 85,794 | 86,212 | +418

L2 = envelope 52,840 SF - open-to-below 24,148 SF (arena 132 x 168 + lobby 58 x 34), the Rev F method. This corrects the P2-A-101 Rev K sheet (L2 28,736, TOTAL 86,256): that figure kept the Rev J NE projection and did not count the tower floor; use 28,692 / 86,212. Carry to P2-G-003 Rev L.

## OPEN (not decided here)

- Exit capacity and travel distance with ST-2 as the only NE stair and X1, X6, X9, X10 moved: P2-G-002 recheck (Rev F).
- Tower floor-to-floor and the strip landing: 6 ft landing at a 76 in stair door needs architect confirmation (IBC 1010 not checked).
- Structure of the curved shell and tier depth of 1'-6" or less (D-061); seat counts re-verified after the corner cut.
- SRM / Summertown Metals roles are not agreed; names are descriptive, no marks used (D-042).

Sources: params/phase2_plan_rev_i.yaml (L2 as Rev F); phase2_plan_rev_k.yaml; phase2_plan_rev_g_l2.yaml; D-035, D-061, D-077..D-079.
