thebardchat/TrojanHorseAreana/blueprints/phase2/out/pdf/P2-A-101_RevK.pdf

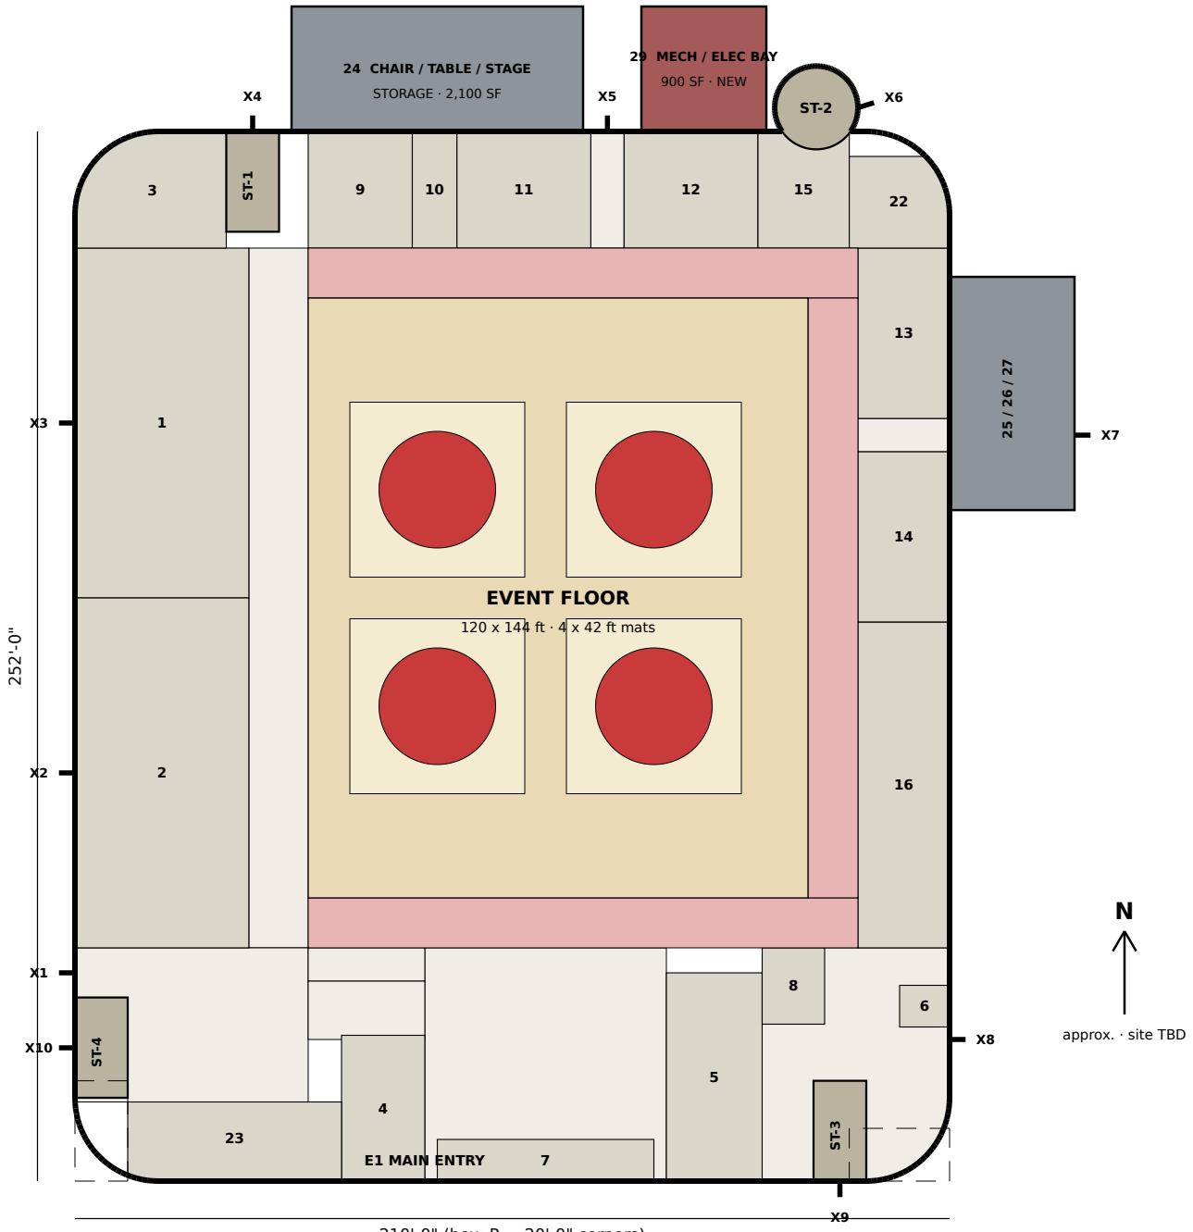
[picture p21: figure]
EVENT FLOOR; 120 x 144 ft · 4 x 42 ft mats; 24 CHAIR / TABLE / STAGE; STORAGE · 2,100 SF; 29 MECH / ELEC BAY; 900 SF · NEW; E1 MAIN ENTRY; approx. · site TBD

# PRELIMINARY — CONCEPTUAL DESIGN — NOT FOR CONSTRUCTION

PROJECT

## Hazel Green Regional Athletic Complex Trojan Horse Arena · Hazel Green area, Madison County, Alabama (site TBD, D-006)

PHASE

# PHASE 2

SHEET TITLE

## OVERALL FLOOR PLAN LEVEL 1 · BLOCK PLAN

SCALE
1" =
40'-0"

DATE

# October

2026

REV
K

DRAWN BY

### Drawn by Claude (AI) for Shane Brazelton

SHEET

P2-A-101

210'-0" (box; R = 20'-0" corners)

# SCHEMATIC — BLOCK PLAN, CONCEPT ENVELOPE

## LEVEL 1 — OVERALL FLOOR PLAN (REV K)

Rev J layout (frozen, D-073) inside the radiused SRM-language envelope approved at R = 20 ft (D-077). Rooms, tiers, mats, exits and areas are Rev J unless listed under CHANGES. Rev J dashed outlines show where the corner stairs were.

### CHANGES FROM REV J (all ASSUMED)

- Envelope: 210 x 252 ft box with R = 20 ft corners (removes about 344 SF per level at the four corners).
- ST-3 (SE) slides west along the south wall to x 177.3-190; same 12.667 x 24.083 ft, exit X9 to x 183.7. Clears L2 WOMEN (2).
- ST-4 (SW) slides north along the west wall into the FLEX / TEAM ASSEMBLY zone (no program); exit X10 on the west wall; exit X1 moves to y 50 beside it.
- ST-2 (NE) is a 20 ft diameter cylindrical tower INSIDE the building envelope: the outline wraps it, it lands on the L2 loop north leg, exit X6 on its east face. Replaces the 24.08 x 6.67 ft NE projection.
- NEW 29 MECH / ELEC BAY 30 x 30 ft (900 SF), one storey, metal-building pop-out 14 ft east of the storage annex so the EXIT (N) passage at X5 stays clear (D-074).
- MECH (NW) and MECH (NE) lose corner area to the radius (below); the bay makes it up.

### ROOMS CHANGED (SF drawn)

TAG | ROOM | REV J | REV K | CHANGE
3 | MECH / ELEC (NW) | 1,017 | 931 | -86
22 | MECH (NE) | 530 | 505 | -25
23 | FLEX / STORAGE | 975 | 972 | -3
29 | MECH / ELEC BAY (new) | 0 | 900 | +900

### AREA CHECK (no SF cap, D-056; L1, L2, total vs Rev J, D-057)

REV J | REV K | CHANGE
L1 footprint (envelope + annex + bay + bump-out) | 56,861 | 57,520 | +659
L2 area | 28,933 | 28,736 | -197
TOTAL GSF | 85,794 | 86,256 | +462

L1 = envelope polygon (box with R = 20 ft corners + tower) 52,840 SF + annex 2,100 + bay 900 + bump-out 1,680. L2 = Rev J 28,933 less 197 SF where Rev J L2 rooms and the loop fall outside the radius; the tower is not added to L2 (ASSUMED, as the Rev J projection). Recompute on P2-G-003 Rev L.

### ROOM SCHEDULE — LEVEL 1 (SF inside the Rev K envelope)

1 | BOYS LOCKER | 3,507
2 | GIRLS LOCKER | 3,507
3 | MECH / ELEC (NW) | 931
4 | MEN | 700
5 | WOMEN | 1,150
6 | FIRST AID | 120
7 | VESTIBULE | 520
8 | CONCESSION | 275
9 | EQUIP. STORAGE | 700
10 | EQUIP. ROOM | 300
11 | EVENT LOCKER 1 | 900
12 | EVENT LOCKER 2 | 900
13 | EVENT LOCKER 3 | 900
14 | EVENT LOCKER 4 | 900
15 | MECH (N) | 614
16 | MECH (E) | 1,720
22 | MECH (NE) | 505
23 | FLEX / STORAGE | 972
24 | CHAIR / TABLE / STAGE STORAGE | 2,100
25 | RESTROOM POP-OUT (25-27) | 1,680
29 | MECH / ELEC BAY (new) | 900

### OPEN (not decided here)

- Structure of the curved shell and the 120 ft roof span; tier depth still needs <= 1'-6" (D-061).
- Egress / exit capacity with X6, X9, X10 moved: recheck on P2-G-002 (Rev E).
- A-102 Level 2 needs a matching Rev (loop corners, ST-2 landing).
- SRM / Summertown Metals roles are not agreed; names are descriptive, no marks used (D-042).

Sources: params/phase2_plan_rev_i.yaml (Rev J); params/phase2_plan_rev_k.yaml; D-070..D-077 (DECISIONS_ARENA).
