thebardchat/TrojanHorseAreana/blueprints/phase1/out/pdf/P1-G-001_RevA_internal.pdf

## PRELIMINARY — CONCEPTUAL DESIGN — NOT FOR CONSTRUCTION

PROJECT
Hazel Green Regional Athletic Complex Hazel Green, Madison County, Alabama

PHASE

### PHASE 1 REMODEL

SHEET TITLE
SCOPE SHEET
PHASE 1 — REMODEL OF
EXISTING WRESTLING ROOM

SCALE

### NTS

DATE

### October

2026

REV
A

DRAWN BY
Drawn by KEYSTONE (AI) for Shane Brazelton

SHEET
P1-G-001

# HAZEL GREEN REGIONAL ATHLETIC COMPLEX

## PHASE 1 — REMODEL OF EXISTING WRESTLING ROOM

Location: Hazel Green, Madison County, Alabama Rooms: existing wrestling room + adjacent walk-through room For review by: principal + district facilities WHAT THIS PROJECT DOES — 3 WORK ITEMS

### W1 — WALL PADDING

Proper training wall pads on the wrestling room walls. Finish work, not new construction.
Walls to pad: TBD
Pad height: 6 ft proposed (R-001 guidance), coach to confirm
Pad thickness: TBD
Who buys or donates: TBD (school purchase, donation, or fundraiser)
Door hardware: Recess from wall surface where possible. Walls flat, no bump-outs.

FIRE SAFETY — BEFORE BUYING PADS Wall pads must have an NFPA 286 assembly test report — not a foam-only rating. Ask the vendor before purchase.

Basis: R-001: 2021 IBC 806.2 and 803.4 → 2603.9 (Alabama Building Code via DCM).

### W2 — PLUMBING REPAIR

Repair plumbing already failing in the existing building.
Where: TBD
Problem spots: TBD
Existing fixtures: TBD
Water / drain lines: TBD / TBD

WHO DESIGNS IT
BY LICENSED PLUMBER /
ENGINEER OF RECORD

This package gives: scope narrative + fixture list only (no plumbing design).
Plumbing code: 2021 IPC (Alabama).

### W3 — RESTROOM SPLIT

Why: The route to the training room is an open walk-through room. Result: 1 male + 1 female athlete restroom (single-user, one per sex). Accessibility: full 2010 ADA Standards, BOTH rooms.
Where / room sizes: TBD — waiting on measurements.

KEY 2010 ADA NUMBERS FOR EACH RESTROOM (from R-003)
Item | Requirement | 2010 ADA §
Turning space | 60 in circle (or T-shape) | 304.3
Clear space at toilet | 60 in wide × 56 in deep, min | 604.3.1
Toilet centerline to side wall | 16–18 in | 604.2
Toilet seat height | 17–19 in | 604.4
Side grab bar | 42 in long min; starts ≤ 12 in from rear wall | 604.5.1
Rear grab bar | 36 in long min | 604.5.2
Grab bar height (top) | 33–36 in | 609.4
Sink clear floor space | 30 × 48 in, forward | 305.3, 606.2
Sink rim height | 34 in max | 606.3
Mirror bottom edge | 40 in max above floor | 603.3
Door clear width | 32 in min | 404.2.3
Door handle height | 34–48 in | 404.2.7
Door swing | not over toilet/sink clear space unless a 30 × 48 in space is beyond the swing | 603.2.3
Room sign | tactile, 48–60 in high, latch side | 703.4
Planning numbers only. Final restroom layout comes on sheet P1-A-102 after the rooms are measured.

### NOT INCLUDED

✕ The Phase 2 new building complex (55,000 SF)
✕ Stadium seats
✕ Any new structure

Phase 1 is a remodel of existing rooms only.

### WHO APPROVES (DRAFT — TBD)

1. Principal (name spelling TBD)
2. District facilities (Madison County Schools)
3. TBD
Final approval path, and whether donated labor or materials are allowed: TBD (R-002 and R-004 research pending).
Scope confirmation expected: ~end of October 2026 (principal + facilities)

### WAITING ON

□ Room measurements + photos: wrestling room and walk-through room (Shane) — D-001
□ Pad height: 6 ft proposed, coach's call — D-003
□ Which walls get pads, and who buys or donates them — D-003 □ Where the plumbing fails + photos — D-002
□ Principal's name spelling — D-005
□ Approval path: who signs off, donated work allowed? — D-004 (R-002, R-004)

### PHOTOS

PHOTOS TBD

Wrestling room

PHOTOS TBD

Walk-through room
