thebardchat/TrojanHorseAreana/blueprints/phase1/out/pdf/P1-G-001_RevE_principal.pdf

# PRELIMINARY — CONCEPTUAL DESIGN — NOT FOR CONSTRUCTION

PROJECT

### Hazel Green Regional Athletic Complex Hazel Green, Madison County, Alabama

PHASE

## PHASE 1 REMODEL

SHEET TITLE

### SCOPE SHEET PHASE 1 — REMODEL OF EXISTING WRESTLING ROOM

SCALE

## NTS

DATE

## October

2026

REV
E

DRAWN BY
Drawn by KEYSTONE (AI) for Shane Brazelton

SHEET
P1-G-001

# HAZEL GREEN REGIONAL ATHLETIC COMPLEX

# PHASE 1 — REMODEL OF EXISTING WRESTLING ROOM

## Requested by: Shane Brazelton — 256-508-4608 / brazeltonshane@gmail.com

Location: Hazel Green, Madison County, Alabama Rooms: existing wrestling room + adjacent walk-through room For review by: Dr. Headen (principal) + district facilities

## WHAT THIS PROJECT DOES — 3 WORK ITEMS, IN PRIORITY ORDER

## W2 — RESTORE WATER / PLUMBING REPAIR

PRIORITY 1

No running water to the area. All fixtures out of service. Cause unknown.

Restore running water to the area and repair the plumbing so the fixtures work again.
Why: Athletes have no working restroom or handwashing during practice; hygiene matters in a contact sport.
Where: Support wing east of the wrestling room, along the open hallway. Problem spots: Entire support wing. Showers were already broken before the water loss.
Existing fixtures: 2 showers, 1 private toilet, 2 toilets, 1 urinal, sinks (count TBD), water fountain/sink — all out of service, no running water. Water / drain lines: TBD / TBD

WHO DESIGNS IT

### BY LICENSED PLUMBER / ENGINEER OF RECORD

This package gives: scope narrative + fixture list only (no plumbing design).
Plumbing code: 2021 IPC (Alabama) — 2021 ASSUMED, verify with AHJ. Edition still open: county lists 2018 codes; State Fire Marshal uses 2021.

## W3 — RESTROOM SPLIT

PRIORITY 2

Why: The route to the training room is an open walk-through room.
Result: 1 male + 1 female athlete restroom (single-user, one per sex). Accessibility: full 2010 ADA Standards, BOTH rooms.
Where / room sizes: Support wing — waiting on support wing measurements.

KEY 2010 ADA NUMBERS FOR EACH RESTROOM
Item | Requirement | 2010 ADA §
Turning space | 60 in circle (or T-shape) | 304.3
Clear space at toilet | 60 in wide × 56 in deep, min | 604.3.1
Toilet centerline to side wall | 16–18 in | 604.2
Toilet seat height | 17–19 in | 604.4
Side grab bar | 42 in long min; starts ≤ 12 in from rear wall | 604.5.1
Rear grab bar | 36 in long min | 604.5.2
Grab bar height (top) | 33–36 in | 609.4
Sink clear floor space | 30 × 48 in, forward | 305.3, 606.2
Sink rim height | 34 in max | 606.3
Mirror bottom edge | 40 in max above floor | 603.3
Door clear width | 32 in min | 404.2.3
Door handle height | 34–48 in | 404.2.7
Door swing | not over toilet/sink clear space unless a 30 × 48 in space is beyond the swing | 603.2.3
Room sign | tactile, 48–60 in high, latch side | 703.4
Planning numbers only. The final restroom layout comes after the rooms are measured.

## W1 — WALL PADDING

PRIORITY 3 — CAN RUN IN PARALLEL

Does not depend on water.
Proper training wall pads on the wrestling room walls. Finish work, not new construction.
Why: Wrestlers can get hurt when they are thrown or fall into bare, unpadded walls during practice. Proper wall pads lower that risk. Walls to pad: TBD
Pad height: 6 ft
Pad thickness: TBD
Estimate: ~188 LF of padded wall after 4 doors (~94 panels at 2 ft x 6 ft); 6'-0" pads under a 10'-0" ceiling. Estimate assumes all 4 walls. Who buys or donates: TBD (school purchase, donation, or fundraiser) Door hardware: Recess from wall surface where possible. Walls flat, no bump-outs.

FIRE SAFETY — BEFORE BUYING PADS

Wall pads must have an NFPA 286 assembly test report — not a foam-only rating. Ask the vendor before purchase.

Code basis: 2021 IBC 806.2 and 803.4 → 2603.9 (Alabama Building Code) — 2021 ASSUMED, verify with AHJ.

## NOT INCLUDED

### ✕ The Phase 2 new building complex ✕ Stadium seats ✕ Any new structure

Phase 1 is a remodel of existing rooms only.

## WHO APPROVES

### 1. Principal (Dr. Headen) 2. District facilities (MCSS Operations & Facilities) 3. Others as the district requires

District guidelines send campus building improvements to the Board of Education. State building review (Alabama DCM) may also apply.
Scope confirmation expected: ~end of October 2026 (principal + facilities)

## WHAT WE'RE ASKING THE SCHOOL FOR

1. Permission to measure and photograph the support wing and walk-through room
2. A district facilities contact
3. How approval works for this kind of work
4. A plumber visit to diagnose why there is no water (shutoff, supply line, or other)
5. Copies of the photos Dr. Headen took

## PHOTOS

### PHOTOS TBD

Wrestling room

### PHOTOS TBD

Walk-through room
