thebardchat/TrojanHorseAreana/blueprints/phase1/out/pdf/P1-P-001_RevA.pdf

# PRELIMINARY — CONCEPTUAL DESIGN — NOT FOR CONSTRUCTION

PROJECT

### Hazel Green Regional Athletic Complex Hazel Green, Madison County, Alabama

PHASE

## PHASE 1 REMODEL

SHEET TITLE

### PLUMBING / WATER RESTORE SCOPE PHASE 1 — WORK ITEM W2 (PRIORITY 1) — SCOPE NARRATIVE ONLY

SCALE

## NTS

DATE

## October

2026

REV
A

DRAWN BY
Drawn by KEYSTONE (AI) for Shane Brazelton

SHEET

P1-P-001

### BY LICENSED PLUMBER / ENGINEER OF RECORD

Plumbing work on this project is BY LICENSED PLUMBER / ENGINEER OF RECORD. Alabama requires a state plumbing certificate to engage in plumbing work except listed exemptions (owner; owner's regular maintenance employee). How those exemptions apply on public school property was not found — ask the district / PGFB / DCM inspector. KEYSTONE produces a scope narrative and fixture list only; no pipe sizing, no plumbing design.
Cite: R-004.3 (Ala. Code §§34-37-6(a), 34-37-15; PGFB FAQ); phase1.yaml standards.approvals_refs.plumbing_license; prompt §2. District confirmation still needed.

### SCOPE OF WORK (NARRATIVE — NOT A DESIGN)

Work item: W2 — Restore water / plumbing repair · PRIORITY 1
KEYSTONE role: scope narrative + fixture list only (no plumbing design)
Why: Athletes have no working restroom or handwashing during practice; hygiene matters in a contact sport. Plumber / EOR to:
1. Diagnose the cause of the water loss (shutoff, supply line, or other) — plumber to determine
2. Restore running water to the support wing / wrestling-room area
3. Repair or replace fixtures and piping as the licensed plumber directs after diagnosis
4. Do NOT size pipe, design layouts, or seal plumbing drawings on this sheet — BY LICENSED PLUMBER / ENGINEER OF RECORD

### EXISTING CONDITION (SOURCED)

Status: No running water to the area. All fixtures out of service. Cause unknown. Detail: Showers, toilets, and sinks are all non-functional, not just leaking.
Where: Support wing east of the wrestling room, along the open hallway.
Problem spots: Entire support wing; showers were already broken before the water loss. Cause: TBD — plumber to diagnose
Water lines: TBD
Drain lines: TBD
Before 2026-10-03: Plumbing already failing in the existing building.

PRIORITY 1 — RESTORE WATER · NO RUNNING WATER · ALL FIXTURES OUT OF SERVICE

### CROSS-REFERENCES (FROZEN — DO NOT REGENERATE)

- P1-G-001 Rev D (principal scope sheet) — Phase1_Package_for_Dr_Headen
- P1-A-101 Rev A (existing conditions — wrestling room outline; support wing not yet measured) Package: Phase1_Package_for_Dr_Headen. This sheet adds W2 detail only.

### OPEN ITEMS / ASKS

1. Licensed plumber visit to diagnose why there is no water
2. Photos of shutoff valves, supply / drain lines, and each fixture
3. Confirm sink count (still TBD)
4. Confirm water-line and drain-line routing (still TBD)
5. Copies of the photos Dr. Headen already took
6. District confirmation of approval path for this repair work (D-004)

### FIXTURE INVENTORY (ALL OUT OF SERVICE)

# | FIXTURE | QTY | STATUS | NOTE

1 | Shower | 2 | out of service | broken before the water loss
2 | Private toilet | 1 | out of service | —
3 | Toilet | 2 | out of service | —
4 | Urinal | 1 | out of service | —
5 | Sink | TBD | out of service | count TBD
6 | Water fountain / sink | 1 | out of service | marked near urinal / hallway on aerial sketch

Source: Shane, firsthand 2026-10-03. Sink count and line routing still TBD. No pipe sizes on this sheet.
