thebardchat/TrojanHorseAreana/blueprints/phase2/out/pdf/P2-A-101.pdf

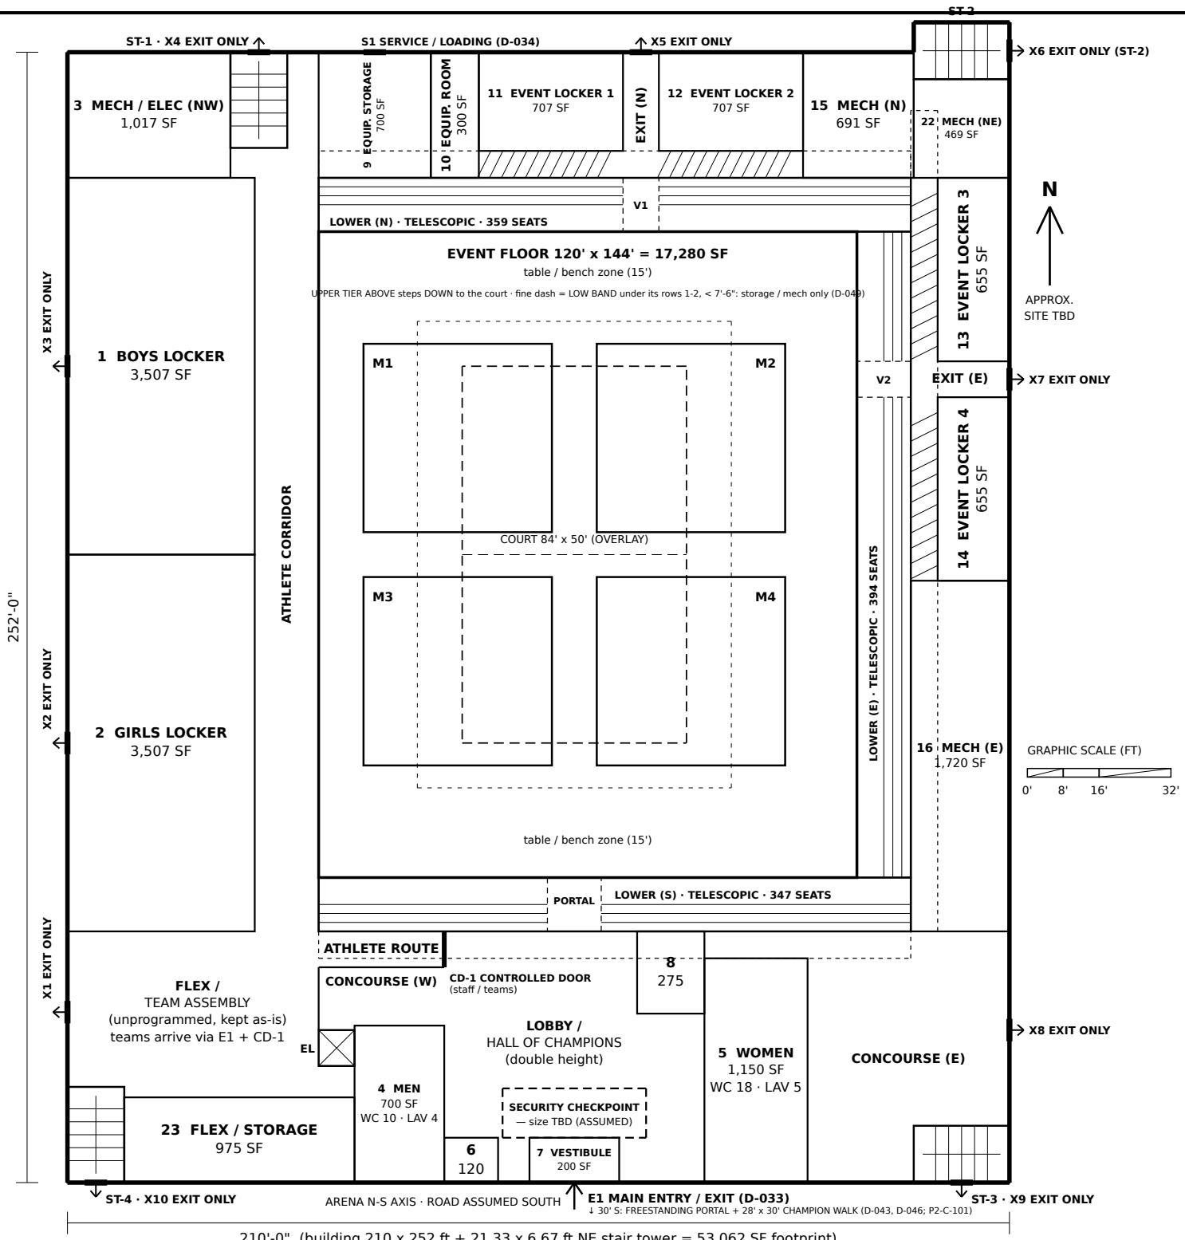
[picture p22: figure]
LOWER (N) · TELESCOPIC · 359 SEATS; LOWER (S) · TELESCOPIC · 347 SEATS; LOWER (E) · TELESCOPIC · 394 SEATS; PORTAL; EVENT FLOOR 120' x 144' = 17,280 SF; table / bench zone (15'); COURT 84' x 50' (OVERLAY); SECURITY CHECKPOINT — size TBD (ASSUMED); CD-1 CONTROLLED DOOR (staff / teams); X1 EXIT ONLY X2 EXIT ONLY X3 EXIT ONLY; X5 EXIT ONLY; X7 EXIT ONLY; X8 EXIT ONLY; S1 SERVICE / LOADING (D-034); 1 BOYS LOCKER 3,507 SF; 2 GIRLS LOCKER 3,507 SF; 3 MECH / ELEC (NW) 1,017 SF; 4 MEN 700 SF WC 10 · LAV 4; 5 WOMEN 1,150 SF WC 18 · LAV 5; 7 VESTIBULE 200 SF; 9 EQUIP. STORAGE; 10 EQUIP. ROOM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

# PRELIMINARY — CONCEPTUAL DESIGN — NOT FOR CONSTRUCTION

PROJECT

# Hazel Green Regional Athletic Complex Trojan Horse Arena · Hazel Green area, Madison County, Alabama (site TBD, D-006)

PHASE

# PHASE 2

SHEET TITLE

# OVERALL FLOOR PLAN LEVEL 1 · BLOCK PLAN

SCALE
1/32" =
1'-0"

DATE

# October

2026

REV
E

DRAWN BY

## Drawn by KEYSTONE (AI) for Shane Brazelton

SHEET
P2-A-101

210'-0" (building 210 x 252 ft + 21.33 x 6.67 ft NE stair tower = 53,062 SF footprint)

UPPER TIER ABOVE steps DOWN to the court · fine dash = LOW BAND under its rows 1-2, < 7'-6": storage / mech only (D-049)

ARENA N-S AXIS · ROAD ASSUMED SOUTH E1 MAIN ENTRY / EXIT (D-033) ↓ 30' S: FREESTANDING PORTAL + 28' x 30' CHAMPION WALK (D-043, D-046; P2-C-101)

# SCHEMATIC — BLOCK PLAN

# LEVEL 1 — OVERALL FLOOR PLAN (REV E)

### scale 1/32" = 1'-0" on 17 x 11 in · north approximate, road assumed south, site TBD

## LEGEND

Lower tier, TELESCOPIC (extended, 6 rows x 24 in; 3.38 SF/seat) — D-009 42' wrestling mat (4, 2 x 2)
84' x 50' court + 10' runout (overlay)
Portal / vomitory through the telescopic tier (V1, V2)
X# = EXIT ONLY — alarmed, no exterior entry hardware (symbol; width not drawn) S1 = SERVICE / LOADING door (staff-controlled, not a people entrance; D-034) Fine dash = low band under upper-tier rows 1-2 (D-049); hatch = under-tier storage Security checkpoint zone (size TBD) · CD-1 controlled door (staff / teams)
Room block (tag number + drawn SF)
Stair (4) / elevator (X), same position on both levels

## ROOM SCHEDULE — LEVEL 1 (DRAWN vs PROGRAM side by side, P2-G-003 Rev G; C-3)

TAG | ROOM | DRAWN SF | PROGRAM | NOTE
— | Event floor + east zone (D-053) | 17,280 | 17,264 | 120' x 144'; east tier 16 ft from mats
— | Lower tier, telescopic (1,100 seats) | 4,896 | 3,719 | 6 rows; N 359 / S 347 / E 394
— | Under-tier storage (hatched) | 877 | — | low band in front of event lockers 1-4 (D-049)
1 | Boys Locker | 3,507 | 3,500
2 | Girls Locker | 3,507 | 3,503 | drawn equal to boys (D-013)
3 | Mech / Elec (NW) | 1,017 | 1,054
4 | Men | 700 | 700 | 14 fixtures (WC 10, LAV 4; urinals ≤ 6 of the WCs)
5 | Women | 1,150 | 1,150 | 23 fixtures (WC 18, LAV 5)
6 | First Aid | 120 | 120
7 | Vestibule | 200 | 200 | 200 of the foyer parts; lobby 400 + desk 200 sit in the lobby
8 | Concession | 275 | 275
9 | Equip. Storage | 700 | 700
10 | Equip. Room | 300 | 300
11 | Event Locker 1 | 707 | 900 | behind the low band (D-049): −193
12 | Event Locker 2 | 707 | 900 | behind the low band (D-049): −193
13 | Event Locker 3 | 655 | 900 | behind the low band (D-049): −245
14 | Event Locker 4 | 655 | 900 | behind the low band (D-049): −245
15 | Mech (N) | 691 | 716
16 | Mech (E) | 1,720 | 1,782
22 | Mech (NE) | 469 | 486 | NE pocket, up to ST-2
23 | Flex / Storage | 975 | — | FLEX, unprogrammed, label kept (D-039, C-1)

## AREA CHECK — D-057 (no SF cap, D-056)

| DRAWN REV E | REV D | CHANGE | PROGRAM G-003 G | DRAWN − PROG.
L1 FOOTPRINT | 53,062 | 51,503 | +1,559 | 54,241 | −1,179
L2 AREA | 28,914 | 28,363 | +551 | 28,012 | +902
TOTAL GSF | 81,976 | 79,866 | +2,110 | 82,253 | −277
Floor 120 x 144, east tier 16 ft from the mats (D-053). Program = footprint / L2 gross (R-021). Seats N 673 / S 661 / E 866 (Rev D 661 / 649 / 890). Mech 3,898 vs 4,037. FLEX kept: team assembly ≈ 2,072, FLEX / STORAGE 975 SF.

## ACCESS CONTROL + EGRESS (D-033 DECIDED; layout ASSUMED)

- ONE WAY IN (D-033): E1 → security checkpoint (size TBD) → lobby; teams go west through CD-1 to team assembly, athlete corridor, lockers.
- X1-X10 EXIT ONLY: alarmed, no exterior entry hardware, free egress (IBC 2021 1010.2), panic hardware (1010.2.9), no delayed egress in Group A (1010.2.13). > 1,000 per story → 4 exits (T1006.3.3); main exit ≥ 1/2 the load (1030.2); checkpoint must not narrow it (R-015).
- S1 service / deliveries at the north door (D-034 DECIDED); team / bus drop loop south, offset E / W of E1. Freestanding portal 30 ft south of E1 over the 28 x 30 ft brick Champion Walk (D-043, D-046, D-050): outside, drawn on P2-C-101 / P2-A-201.
- D-049: rows 1-2 of the upper tier (front 6 ft) leave < 7'-6" clear (≈ 1'-6" structure ASSUMED): storage / mech only; event lockers start behind them. FINDING: EXIT (N), EXIT (E), SE concourse, lobby / portal / athlete-route edge also pass under rows 1-2; egress needs ≥ 7'-6" (IBC 1003.2): omit or raise rows 1-2 there. Travel distance NOT checked.
Sources: phase2.yaml (D-009, D-030, D-033, D-034, D-035, D-049, D-051-D-053, D-056, D-057); Shane 2026-10-04 9:10 AM CT; P2-G-003 Rev G; R-008, R-009, R-014, R-015, R-020, R-021; IBC 2021 Ch. 10 (UpCodes, Alabama); UFC 4-740-02N (retrieved 2026-10-04). Geometry: params/phase2_plan_rev_e.yaml.
