thebardchat/TrojanHorseAreana/blueprints/phase2/out/pdf/P2-A-101_RevH.pdf

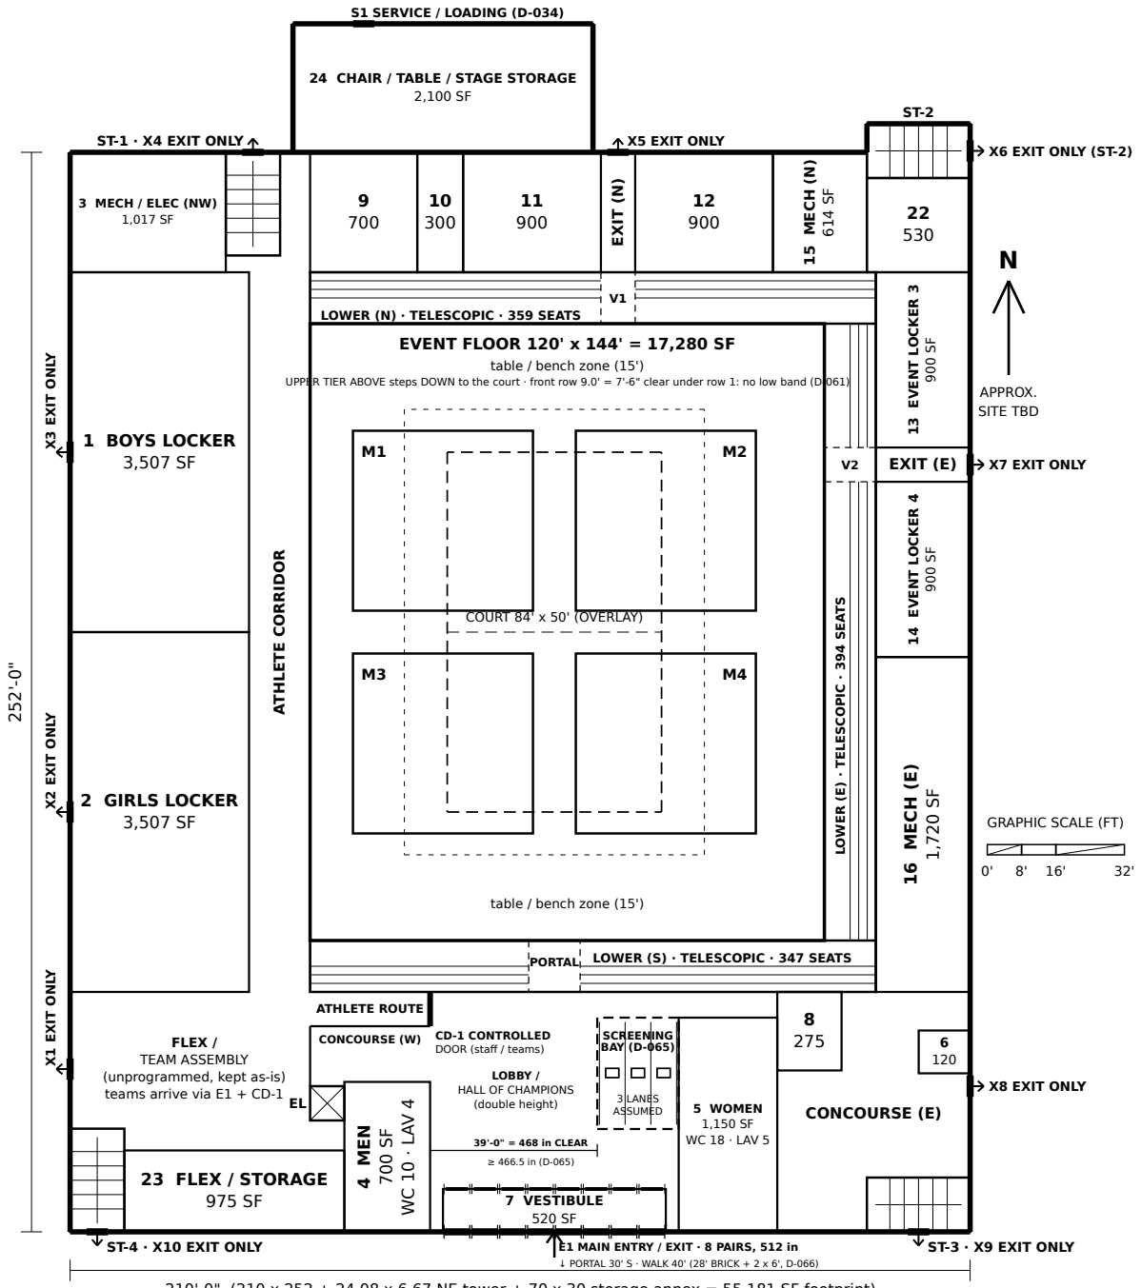
[picture p23: figure]
LOWER (N) · TELESCOPIC · 359 SEATS; PORTAL; EVENT FLOOR 120' x 144' = 17,280 SF; table / bench zone (15'); COURT 84' x 50' (OVERLAY); E1 MAIN ENTRY / EXIT · 8 PAIRS, 512 in; SCREENING BAY (D-065); 3 LANES ASSUMED; 39'-0" = 468 in CLEAR; CD-1 CONTROLLED DOOR (staff / teams); X1 EXIT ONLY X2 EXIT ONLY X3 EXIT ONLY; X5 EXIT ONLY; X7 EXIT ONLY; X8 EXIT ONLY; S1 SERVICE / LOADING (D-034); 1 BOYS LOCKER 3,507 SF; 2 GIRLS LOCKER 3,507 SF; 3 MECH / ELEC (NW) 1,017 SF; 4 MEN; WC 10 · LAV 4; 5 WOMEN 1,150 SF WC 18 · LAV 5; 7 VESTIBULE 520 SF; 13 EVENT LOCKER 3; 14 EVENT LOCKER 4; 15 MECH (N)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

# PRELIMINARY — CONCEPTUAL DESIGN — NOT FOR CONSTRUCTION

PROJECT

# Hazel Green Regional Athletic Complex Trojan Horse Arena · Hazel Green area, Madison County, Alabama (site TBD, D-006)

PHASE

# PHASE 2

SHEET TITLE

# OVERALL FLOOR PLAN LEVEL 1 · BLOCK PLAN

SCALE
1" =
40'-0"

DATE

# October

2026

REV
H

DRAWN BY

## Drawn by KEYSTONE (AI) for Shane Brazelton

SHEET
P2-A-101

210'-0" (210 x 252 + 24.08 x 6.67 NE tower + 70 x 30 storage annex = 55,181 SF footprint)

LOWER (S) · TELESCOPIC · 347 SEATSLOWER ⁽E⁾ · TELESCOPIC · 394 SEATS

UPPER TIER ABOVE steps DOWN to the court · front row 9.0' = 7'-6" clear under row 1: no low band (D-061)

↓ PORTAL 30' S · WALK 40' (28' BRICK + 2 x 6', D-066)

# SCHEMATIC — BLOCK PLAN

# LEVEL 1 — OVERALL FLOOR PLAN (REV H)

### scale 1" = 40'-0" on 17 x 11 in · north approximate, road assumed south, site TBD

## LEGEND

Lower tier, TELESCOPIC (extended, 6 rows x 24 in; 3.38 SF/seat) — D-009 42' wrestling mat (4, 2 x 2)
84' x 50' court + 10' runout (overlay)
Portal / vomitory through the telescopic tier (V1, V2)
X# = EXIT ONLY — alarmed, no exterior entry hardware (symbol; width not drawn) S1 = SERVICE / LOADING door (staff-controlled, not a people entrance; D-034) Upper tier above: front row 9.0' = 7'-6" clear, no low band (D-061)
Security screening bay, 3 lanes ASSUMED (D-065 Option 1) · CD-1 controlled door Room block (tag number + drawn SF)
Stair (4) / elevator (X), same position on both levels

## ROOM SCHEDULE — LEVEL 1 (DRAWN vs PROGRAM side by side, P2-G-003 Rev J; C-3)

TAG | ROOM | DRAWN SF | PROGRAM | NOTE
— | Event floor + east zone (D-053) | 17,280 | 17,264 | 120' x 144'; east tier 16 ft from mats
— | Lower tier, telescopic (1,100 seats) | 4,896 | 3,719 | 6 rows; N 359 / S 347 / E 394
1 | Boys Locker | 3,507 | 3,500
2 | Girls Locker | 3,507 | 3,503 | drawn equal to boys (D-013)
3 | Mech / Elec (NW) | 1,017 | 1,063
4 | Men | 700 | 700 | drawn 14 fixtures; chairs-only: D-069 OPEN
5 | Women | 1,150 | 1,150 | drawn 23 fixtures; chairs-only: D-069 OPEN
6 | First Aid | 120 | 120 | Rev H: moved off the lobby's east side for the screening bay (D-065); east…
7 | Vestibule | 520 | 200 | Rev G: widened to the 52 ft E1 bank (outer + inner bank, 8 pairs each, AS…
8 | Concession | 275 | 275 | Rev H: moved off the lobby's east side for the screening bay (D-065) into t…
9 | Equip. Storage | 700 | 700
10 | Equip. Room | 300 | 300
11 | Event Locker 1 | 900 | 900 | to the tier line, full 3,600 (D-060): −0
12 | Event Locker 2 | 900 | 900 | to the tier line, full 3,600 (D-060): −0
13 | Event Locker 3 | 900 | 900 | to the tier line, full 3,600 (D-060): +0
14 | Event Locker 4 | 900 | 900 | to the tier line, full 3,600 (D-060): +0
15 | Mech (N) | 614 | 642
16 | Mech (E) | 1,720 | 1,797
22 | Mech (NE) | 530 | 554 | NE pocket, up to ST-2 (Rev F: west edge with ST-2, D-061)
24 | Chair / Table / Stage Storage | 2,100 | 2,100 | Rev H NEW (D-067): 2,100 SF one-storey annex; 56 chair / table trucks +…
23 | Flex / Storage | 975 | — | FLEX, unprogrammed, label kept (D-039, C-1)

## AREA CHECK — D-057 (no SF cap, D-056)

| DRAWN REV H | REV G | CHANGE | PROGRAM G-003 J | DRAWN − PROG.
L1 FOOTPRINT | 55,181 | 53,081 | +2,100 | 56,515 | −1,335
L2 AREA | 28,933 | 28,933 | ±0 | 28,186 | +746
TOTAL GSF | 84,113 | 82,013 | +2,100 | 84,701 | −588
Floor 120 x 144, east tier 16 ft from the mats. Program = footprint / L2 gross (R-021). Seats N 673 / S 661 / E 866 (Rev F 673 / 661 / 866). Mech 3,881 vs 4,056. Event lockers 3,600 SF (D-060). FLEX kept: team assembly ≈ 2,072, FLEX / STORAGE 975 SF.

## ACCESS CONTROL + EGRESS (D-033 DECIDED; layout ASSUMED)

- ONE WAY IN (D-033): E1 → vestibule → cross aisle → SCREENING BAY, lobby east side (D-065 Option 1; 3 lanes, CEIA HI-PE wide WTMD, wand for accessible screening, ASSUMED) → lobby / portal. Clear beside the bay 39 ft = 468 in ≥ 466.5 (standing) / 396.7 (chairs, D-054); lanes and queues stay in the bay (IBC 1003.6, 1010.5). First aid + concession moved to the E concourse. Checks: P2-A-111 Rev B.
- STORAGE ANNEX (D-067) 70 x 30 = 2,100 SF, one storey, north wall between X4 and X5; S1 on its north wall (ASSUMED). Restrooms: chairs-only needs 22 / 42 WC (D-064); rooms NOT redrawn — D-069 OPEN (P2-A-401 Rev B). X1-X10 EXIT ONLY (IBC 1010.2).
- D-061 (Option B): Level 2 at 17'-9", 21 in upper risers, front row 9.0 ft: 7'-6" clear under row 1 (≈ 1'-6" structure ASSUMED; IBC 1003.2 minimum, no margin). Exit paths under the tier are clear; no low band, no seats lost.
Sources: phase2.yaml (D-033-D-035, D-054, D-060, D-061, D-064-D-067, D-069); Shane 2026-10-04 1:21-1:22 PM CT; P2-G-002 Rev B, P2-G-003 Rev J, P2-A-111 Rev B; IBC 2021 1003.6, 1010.5, 1030.2 (UpCodes); ADA 2010 403.5.1; CEIA HI-PE brochure; NPS 42-8 listing (retrieved 2026-10-04). Geometry: params/phase2_plan_rev_h.yaml.
