thebardchat/TrojanHorseAreana/blueprints/phase2/out/pdf/P2-A-201.pdf

# PRELIMINARY — CONCEPTUAL DESIGN — NOT FOR CONSTRUCTION

### PROJECT

# Hazel Green Regional Athletic Complex Trojan Horse Arena · Hazel Green area, Madison County, Alabama (site TBD, D-006)

### PHASE

# PHASE 2

### SHEET TITLE

# EXTERIOR ELEVATIONS SCHEMATIC · COLOR

### SCALE

AS

# NOTED

### DATE

# October

2026

### REV

D

### DRAWN BY

## Drawn by KEYSTONE (AI) for Shane Brazelton

### SHEET

P2-A-201

X10 | X9

SIGNAGE ZONE — CONTENT TBD

# TROJAN HORSE ARENA

E1 MAIN ENTRY (building, behind)

## HAZEL GREEN REGIONAL ATHLETIC COMPLEX

SIDE PANEL (size ASSUMED)

BUILDING — SOUTH WALL (P2-A-101 Rev D) | E1

GAP ≈ 30' (ASSUMED)

CHAMPION WALK 28' x 30' = 840 SF (portal → doors, for now) Engraved donor / sponsor bricks: 4x8 single name · 8x8 family / business ≈ 3,700 4x8 (840 SF ÷ 0.222 SF = 3,780, less border + joints) · pricing TBD FREESTANDING PORTAL (2 piers, depth 6' ASSUMED)

BUS DROP LOOP: south, offset E or W of the portal view (D-034; site plan) | OPTION: extend the walk to parking later

KEY PLAN — PORTAL + CHAMPION WALK — 1" = 60'

north up · site plan on the next A-101 revision

# TROJAN HORSE ARENA

BRAND DETAIL
PORTAL ATTIC
3/32" = 1'-0"

WORDMARK
CAP 27"

MARK Ø 11'-0"
SIZES ASSUMED

CROWN 34'

L1 FF 0'-0"

L2 FF 15'-0" (ASSUMED)

T.O. RING ROOF 30'-0" (ASSUMED)

U/S ARENA STRUCT. 36'-0" (ASSUMED)

T.O. ARENA ROOF 42'-0" (ASSUMED)

WALL MATERIAL TBD

PARAPET TBD

PARAPET TBD

WALL MATERIAL TBD

ARENA VOLUME BEHIND (set back 34')

### GRAND ENTRANCE PORTAL (FREESTANDING)

30' in front of the E1 doors (D-046) · 50' max (D-050) · see key plan

CRIMSON underside (D-045)

GOLD trim (D-045)

E1 ENTRY GLAZING TBD (building face, behind)

CHAMPION WALK — BRICK, in front · Engraved donor / sponsor bricks
SOUTH ELEVATION (PRIMARY) — SCALE 1/16" = 1'-0" | portal 44' w x 50' h, 28' arch, crown 34' (ASSUMED, render proportions) · W ← → E

W E

X5 | X4

S1 SERVICE · SIZE TBD

15'-0"

30'-0"

42'-0"

NE STAIR TOWER (+5')

## NORTH ELEVATION — 1/32" = 1'-0" (E ← → W)

X8 | X7 | X6

ARENA VOLUME (flush with the east wall)

15'-0"

30'-0"

42'-0"

## EAST ELEVATION — 1/32" = 1'-0" (S ← → N)

X3 | X2 | X1

ARENA VOLUME BEHIND (set back 49')

15'-0"

30'-0"

42'-0"

## WEST ELEVATION — 1/32" = 1'-0" (N ← → S)

## FINISHES

LIMESTONE (portal) — Shane (material) CRIMSON (inside the arch) — Shane (color) GOLD (arch soffit) — Shane (color)
BRAND RED — Shane (red/black brand) BRAND BLACK — as brand red
WALL MATERIAL TBD — TBD
ARENA VOLUME — WALL / ROOF TBD — TBD ENTRY GLAZING (TBD) — TBD
BRICK (Champion Walk) — Shane (material)

## NOTES

- HEIGHTS: L2 FF 15' (R-015) and ring roof 30' ASSUMED. Arena clear ≥ 25' over the court (R-019). U/S arena structure 36' and roof 42' ASSUMED; upper tier steps DOWN from the loop (D-049), so the highest aisle is the loop at 15' (IBC 1030.6.2.2 needs ≥ 30' only if smoke-protected). Parapet TBD.
- PORTAL: FREESTANDING limestone arch 30' in front of the E1 doors over Champion Walk (D-043, D-046); 50' max (D-050): crown 34', springline 22.1' (semi-elliptical, ASSUMED); depth 6' ASSUMED; underside crimson + gold trim (D-045).
- BRAND: official mark Ø 11' (Shane, D-047) at 34.4'-45.4'; wordmark 27" caps, baseline 46.1' (inside the 44' x 50' portal) + side panel, ASSUMED sizes. Trademark search before signage / apparel OPEN (D-042).
- CHAMPION WALK: 28' x 30' brick (for now, D-046); 4x8 single name, 8x8 family / business; ≈ 3,700 4x8; pricing OPEN (D-044); may extend to parking. Bus drop: south, offset E or W (D-034).
- DOORS: symbols (6' x 8' ASSUMED) from P2-A-101 Rev D; X# EXIT ONLY (D-033); S1 size TBD (D-034).
- NOT SHOWN: ETFE roof / solar (aspirations), rooftop units, grading, lighting.
