thebardchat/TrojanHorseAreana/blueprints/phase2/out/pdf/P2-A-301.pdf

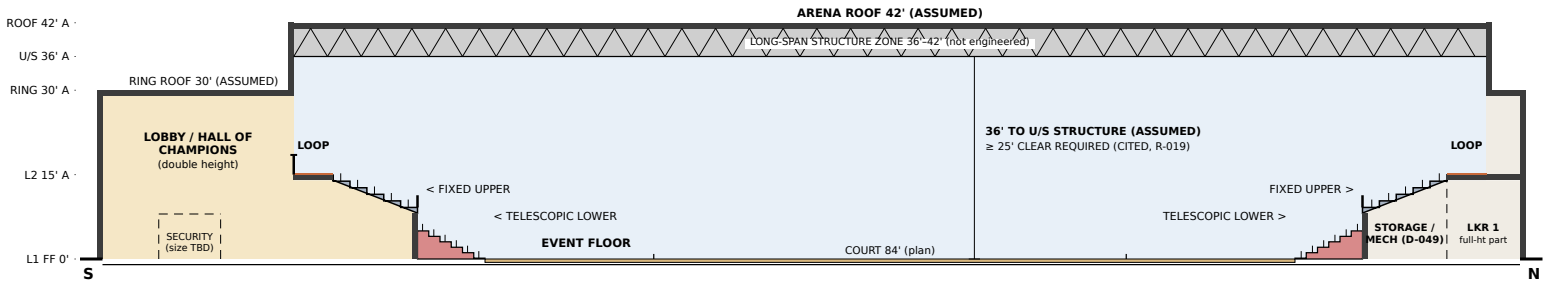
[picture p24: figure]
COURT 84' (plan) EVENT FLOOR; LOBBY / HALL OF CHAMPIONS (double height); SECURITY (size TBD); < TELESCOPIC LOWER; < FIXED UPPER; TELESCOPIC LOWER >; FIXED UPPER >; LOOP; STORAGE / MECH (D-049); LKR 1 full-ht part; ARENA ROOF 42' (ASSUMED); RING ROOF 30' (ASSUMED); 36' TO U/S STRUCTURE (ASSUMED) ≥ 25' CLEAR REQUIRED (CITED, R-019); RING 30' A; ROOF 42' A
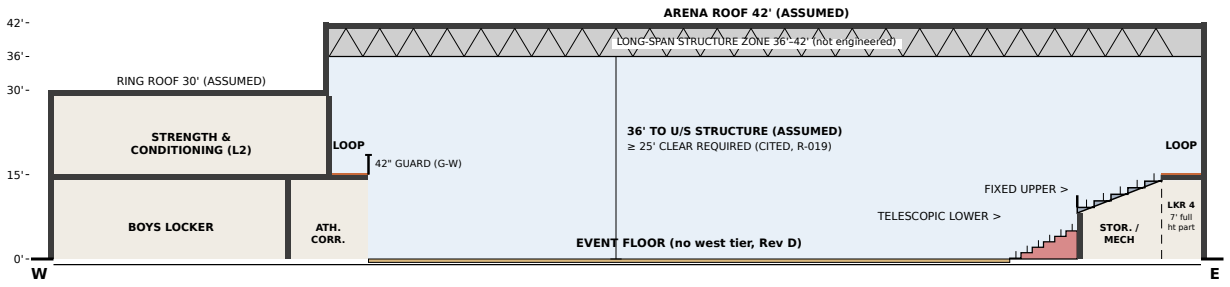
[picture p25: figure]
EVENT FLOOR (no west tier, Rev D); BOYS LOCKER; ATH.; CORR.; STRENGTH &; CONDITIONING (L2); LOOP; TELESCOPIC LOWER >; FIXED UPPER >; STOR. / MECH; LKR 4 7' full ht part; ARENA ROOF 42' (ASSUMED); RING ROOF 30' (ASSUMED); 42" GUARD (G-W); 36' TO U/S STRUCTURE (ASSUMED) ≥ 25' CLEAR REQUIRED (CITED, R-019)

# PRELIMINARY — CONCEPTUAL DESIGN — NOT FOR CONSTRUCTION

PROJECT

# Hazel Green Regional Athletic Complex Trojan Horse Arena · Hazel Green area, Madison County, Alabama (site TBD, D-006)

PHASE

# PHASE 2

SHEET TITLE

# BUILDING SECTIONS SCHEMATIC · COLOR

SCALE
AS

# NOTED

DATE

# October

2026

REV
B

DRAWN BY

## Drawn by KEYSTONE (AI) for Shane Brazelton

SHEET
P2-A-301

LONG-SPAN STRUCTURE ZONE 36'–42' (not engineered)

### 1 SECTION A-A (NORTH-SOUTH) — looking west

1/32" = 1'-0" · x = 100 (see key plan)

LONG-SPAN STRUCTURE ZONE 36'–42' (not engineered)

### 2 SECTION B-B (EAST-WEST) — looking north

1/32" = 1'-0" · y = 150 (see key plan)

L1 FF 0'

L2 15' A

RING 30' A

U/S 36' A

ROOF 42' A

TELESCOPIC LOWER TIER (extended)

6 rows × 24" = 12' band (R-008 / plan)
rise 11⅝"/row — Hussey MAXAM option (CITED); choice of 11⅝" ASSUMED

top seat 6'-3⅛" (Hussey, 6 rows @ 11⅝")

closed 3'-6" (Hussey, 6 rows)

FIXED UPPER TIER (ASSUMED rake)

5 rows × 36" = 15' band (plan)
14"/row = 2 aisle risers × 7", 18" treads (IBC 1030.14.2: 4–8" risers, ≥ 11" treads) steps DOWN from the loop; front row 9.17'

≥ 26" fascia (1030.17.3)

LOOP 7'

2 × 42" lanes

top cross aisle

STRETCH
6' (L2)

UNDER-TIER (D-049): STORAGE / MECH front 9.17' less structure; exits under it
need ≥ 7'-6" ceiling (1003.2)

LOCKER (full ht)

SIGHT LINES: see P2-A-302 — upper 14"/row FAILS

(C < 60 mm); proposed 19"/row, front 7.08' (D-053 OPEN)

1030.6.2.2 (only if smoke-protected): roof ≥ 15' above

highest aisle (loop 15') → ≥ 30'; 36' drawn

### 3 NORTH BOWL EDGE (ENLARGED PART OF A-A)

3/32" = 1'-0" · y 196–252 at x = 100

13 R @ 6.92" = 7.50'

12 T @ 11" = 11'

70" mid

landing

= width

(1011.6)

48" floor

landing

L2 FF 15' (A)

L1 FF 0'

flight 2 beyond

(dashed)

26 risers total

70" clear width

(not visible in section)

### 4 TYPICAL EXIT STAIR — 70" CLEAR

1/8" = 1'-0" · 70" mid landing (D-051) · 11.67' × 20.83' plan

A

A

B B

N

### 5 KEY PLAN — CUTS

1" = 128' · north up

CUT: slab / wall / roof (graphic) | ARENA VOLUME | EVENT FLOOR
TELESCOPIC LOWER TIER | FIXED UPPER TIER | LOOP (L2)
LOBBY | ROOMS / SUPPORT | LONG-SPAN STRUCTURE ZONE

HEIGHTS USED (ft above L1 FF 0'-0")
- L2 FF 15' — ASSUMED (R-015, 15 ft floor-to-floor).
- Ring roof 30' — ASSUMED (L2 + 15 ft).
- Arena structure underside 36' — ASSUMED; ≥ 25' clear over the floor is CITED (R-019: NFHS via Draper, LA RAP) → 11' margin.
- Arena roof top 42' — ASSUMED (36' + 6' long-span structure zone, not engineered).
- Slab, wall and roof thicknesses are graphic only (not designed). Parapets TBD.
SEATING
- Lower tier: telescopic, 6 rows × 24" (R-008, plan Rev D 12' band). Hussey MAXAM rises 9⅝", 11⅝", 16" (CITED); 11⅝" drawn (ASSUMED choice): top seat 6'-3⅛", closed 3'-6" (Hussey tables). Hussey open depth at 24" is 11'-3" vs the 12' band.
- Upper tier: fixed, 15' band (plan); 5 rows × 36", 14"/row (2 × 7" aisle risers, 18" treads) — ASSUMED, within IBC 2021 1030.14.2. Steps DOWN from the loop (L2 FF = top cross aisle) to a 9.17' front row. Not drawn: tier on the L2 deck rising to ≈ 21' (the 36' basis in phase2_elev.yaml).
- UNDER THE UPPER TIER (D-049 DECIDED): steps DOWN from the loop as drawn; under the low front edge: telescopic stack (at the tier face), storage, mechanical. Lockers only where headroom is full (under the flat L2 slab — ASSUMED reading). Front ≈ 9.2' less structure; exit passages under it need ≥ 7'-6" (1003.2). Event lockers 1–4 re-planned at the next A-101.
- SIGHT LINES: P2-A-302 Rev A. Rake unchanged here pending Shane: upper 14"/row fails (C < 60 mm); proposed 19"/row + east tier 6' further out (D-053 OPEN). Closed stack recessed under the tier front conflicts — keep it at the tier face.

GUARDS
- Loop open edges G-W (x = 56) and G-S (y = 34): 42" guards, IBC 2021 1015.2 / 1015.3.
- Upper-tier front: sightline-constrained fascia ≥ 26" (1030.17.3); 36" at the foot of aisles (1030.17.4). Type TBD. STAIRS (ST-1..ST-4)
- 70" clear — D-038 CLOSED (Shane 6:45 AM CT). Handrail projections ≤ 4½" each side (1014.8): architect to confirm how 'clear' is measured.
- 26 risers @ 6.92" (15' ÷ 26), 2 flights of 13, 11" treads (1011.5.2). Intermediate (switchback) landing 70" = stair width (1011.6 width rule at the 180° turn; 48" = straight-run depth) — D-051; floor landings 48". Typical shown (not on A-A / B-B).
- Per stair: 11.67' × 20.83' (2 × 70" by 48 + 132 + 70") = 243.1 SF per level, clear — +37.9 SF vs the frozen 10.8' × 19' (205.2); × 4 stairs × 2 levels ≈ +303 GSF at the next A-101/A-102 revision. Egress worst case still 12.4" short: proposed 4 × 76" stairs (D-052 OPEN, R-018.9) — not drawn. ROOF HEIGHT (IBC 2021 1030.6.2.2)
- Applies only if smoke-protected seating is used: lowest roof deck ≥ 15' above the highest aisle. Highest aisle = the loop at 15' → ≥ 30'; 36' drawn.
CUTS
- A-A: x = 100, looking west (south at left). B-B: y = 150, looking north (west at left). Geometry from P2-A-101/102 Rev D (frozen).
- Colors are graphic only; materials TBD. 'A' = ASSUMED.
