thebardchat/TrojanHorseAreana/blueprints/phase2/out/pdf/P2-A-302.pdf

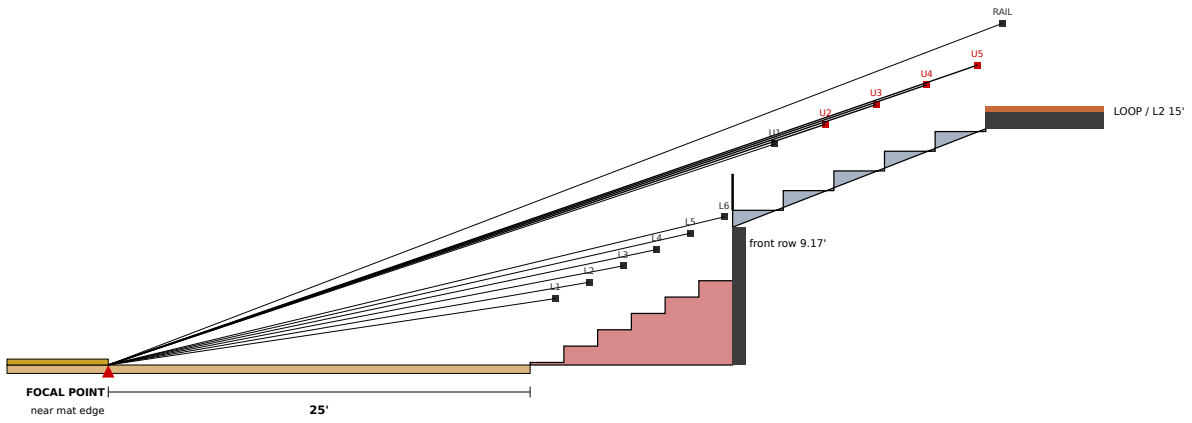
[picture p26: figure]
FOCAL POINT; near mat edge; RAIL; LOOP / L2 15'; front row 9.17'
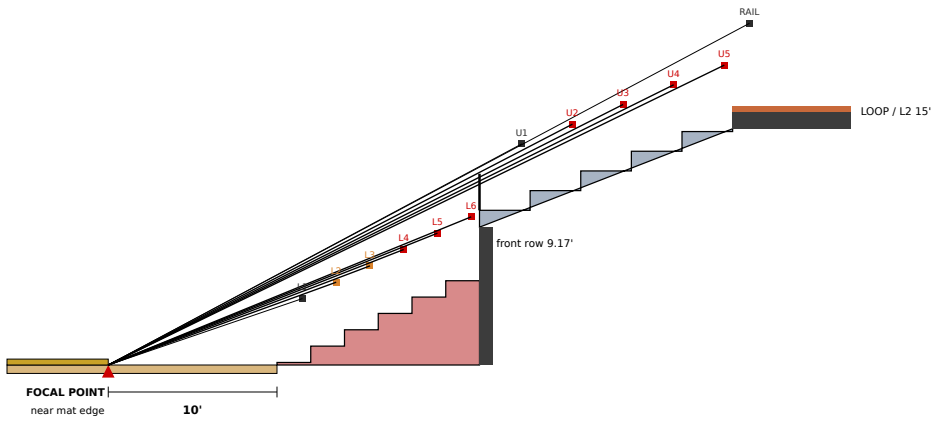
[picture p27: figure]
FOCAL POINT; near mat edge; RAIL; LOOP / L2 15'; front row 9.17'
FOCAL POINT; near mat edge; RAIL; LOOP / L2 15'; front row 7.08'

# PRELIMINARY — CONCEPTUAL DESIGN — NOT FOR CONSTRUCTION

### PROJECT

# Hazel Green Regional Athletic Complex Trojan Horse Arena · Hazel Green area, Madison County, Alabama (site TBD, D-006)

### PHASE

# PHASE 2

### SHEET TITLE

# SIGHT-LINE STUDY SCHEMATIC · COLOR

### SCALE

AS

# NOTED

### DATE

# October

2026

### REV

A

### DRAWN BY

## Drawn by KEYSTONE (AI) for Shane Brazelton

### SHEET

P2-A-302

### 1 AS DRAWN — NORTH / SOUTH SIDE (seated eyes)

3/32" = 1'-0" · focal 25' (10' clear + 15' table zone) · telescopic 11⅝" · upper 14"/row

### 2 AS DRAWN — EAST SIDE (seated eyes)

3/32" = 1'-0" · focal 10' (10' clear) · worst side

### 3 PROPOSED — EAST SIDE (seated eyes)

3/32" = 1'-0" · focal 16' (+6') · upper 19"/row, front 7.08' (D-053)

SIGHTLINE GRADE (C, mm)

≥ 90 PASS

60–90 MARGINAL

< 60 FAIL

Dots = eyes; label colour = C of that row over the row in front. Values: table.

upper-tier deck (front 9.17')

upper-tier face

CLOSED

STACK

front deck 9.17' − 77.4"

= 32.6" structure + finish

recess min 48" deep x

77.4" high (Hussey)

proposed 7.08' front: 7.6" left

upper-tier deck (front 9.17')

upper-tier face

7'-6" ceiling over row 6 (1003.2) = 12.34'

deck at recess back 10.72' − structure

rows 5-6 stay in the recess

under the overhang when open

need

### 4 TELESCOPIC STACK UNDER THE UPPER-TIER FRONT

3/16" = 1'-0" · recessed (Hussey) · N/S as drawn · dashed = proposed 7.08' front

(a) CLOSED — fits only if structure ≤ 32.6" (as drawn)
(b) OPEN — rows 5-6 under the overhang: CONFLICT
AS DRAWN (P2-A-301) | PROPOSED (D-053)

N/S 25'
seated

N/S 25'
stand

E 10'
seated

E 10'
stand

N/S 25'
seated
| N/S 25' stand E 16' seated

E 16'
stand

ROW

L2 | 190 | 162 | 74 | 15 | 190 | 162 | 142 | 101
L3 | 178 | 152 | 64 | 13 | 178 | 152 | 129 | 92
L4 | 167 | 142 | 57 | 11 | 167 | 142 | 118 | 84
L5 | 157 | 134 | 51 | 10 | 157 | 134 | 109 | 77
L6 | 149 | 127 | 46 | 9 | 149 | 127 | 101 | 72
U1 | 1014 | 984 | 829 | 780 | 428 | 397 | 352 | 313
U2 | 49 | 20 | -119 | -162 | 211 | 183 | 139 | 103
U3 | 45 | 19 | -107 | -146 | 198 | 171 | 127 | 94
U4 | 43 | 18 | -97 | -133 | 185 | 161 | 118 | 87
U5 | 40 | 17 | -89 | -122 | 175 | 151 | 109 | 81
RAIL (stands) | 582 | 182 | 513 | 113 | 709 | 309 | 673 | 273
fascia clr (U1) | 286 | 661 | 131 | 490 | 326 | 701 | 263 | 631
front row (ft) | 9.17 | 9.17 | 9.17 | 9.17 | 7.08 | 7.08 | 7.08 | 7.08

METHOD
- C = D(N + R)/(D + T) − R (Green Guide 12.3), computed from each actual eye position (also covers the step between tiers and the loop rail). Focal point = near edge of the nearest mat at floor level (Shane). Eyes: seated 1.2 m above the tread, 0.15 m forward of the row's rear edge; standing 1.6 m (5'-3") — secondary sources, see R-020. Grades: ≥ 90 mm PASS (FIFA preferred, CEN/TR 15913 new stands), 60–90 MARGINAL, < 60 FAIL (FIFA minimum 60).
- Focal distances from the frozen plan (Rev D): N and S tier fronts 25' from the nearest mat (10' clear + 15' table zone); E tier front 10' (10' clear only). No west tier. Section-only study (2D); corners and wheelchair positions TBD.
RESULTS — AS DRAWN
- Upper tier (14" per 36" row) FAILS on every side: N/S seated 40–49 mm, standing 17–20; E negative (rows hidden). Lower tier PASSES at N/S (149–190 seated) but at E (10' focal) is 46–74 seated (L4–L6 FAIL) and 9–15 standing. U1 sees well over the lower tier (≥ 780) and the 26" fascia. RISER CHANGES NEEDED (PROPOSED, D-053 OPEN)
- Upper riser 14" → 19" per row (3 aisle risers of 6⅓", 12" treads; IBC 1030.14.2) — front row drops 9.17' → 7.08' because the back stays at the loop (D-049). N/S then seated ≥ 149, standing ≥ 127.
- East side cannot reach 60 mm with the loop at 15' and a 10' focal distance (best ≈ 46 mm): move the E tier 6' further from the mats (10' → 16') → E seated ≥ 101, standing 72–103 (4 rows MARGINAL). A 16" Hussey rise fixes the E lower rows alone, but the stepped-down upper tier then collides with it.
- Lower tier stays at the Hussey 11⅝" rise (9⅝" would also pass at N/S: 112–143 seated).
TELESCOPIC STACK UNDER THE UPPER-TIER FRONT (D-049)
- Closed stack, recessed: Hussey min recess 4'-0" deep x 6'-5⅜" high. As drawn (front 9.17') it fits only if the tier structure + finish at the front edge is ≤ 32.6". With the proposed 7.08' front only 7.6" remain — does not fit.
- Open: in a recessed stack the rear rows stay in the recess, so rows 5–6 would sit under the overhang with < 7'-6" ceiling (1003.2) — CONFLICT either way. Recommendation: keep the stack in front of the upper-tier face (as P2-A-301); use the low zone under the tier for storage / mechanical only.
- Under-tier front also limits exits: EXIT (N) / (E) passages under the tier need a 7'-6" ceiling (1003.2) — local raise / vomitory cut at the next A-101/A-102 revision.
