thebardchat/TrojanHorseAreana/blueprints/phase2/out/pdf/P2-C-101.pdf

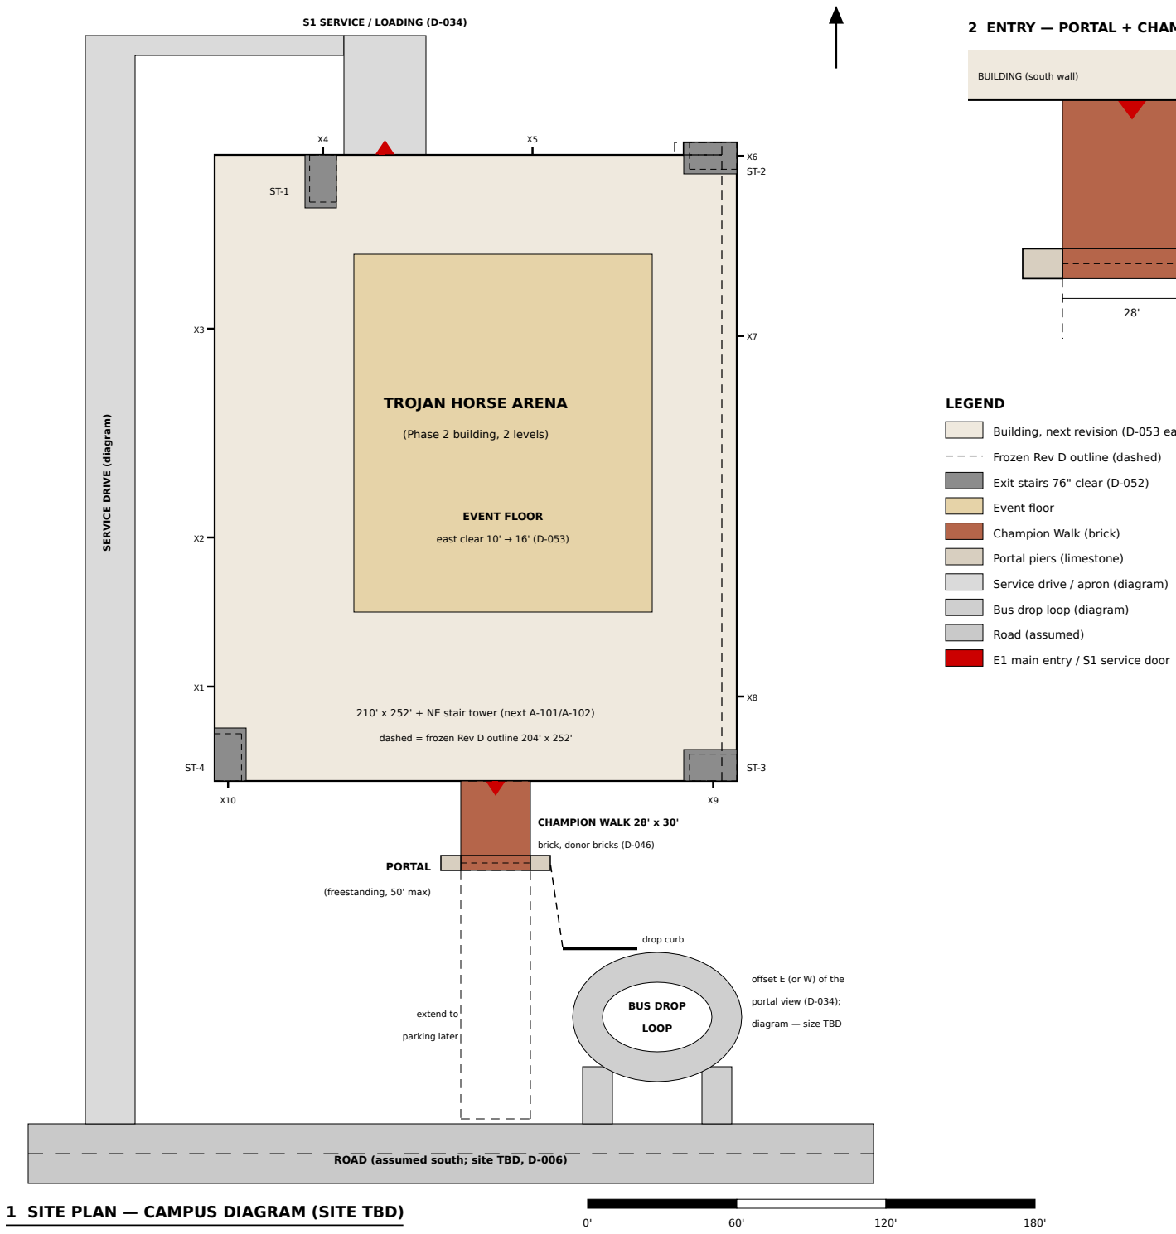
[picture p28: figure]
TROJAN HORSE ARENA; (Phase 2 building, 2 levels); EVENT FLOOR; east clear 10' → 16' (D-053); PORTAL; (freestanding, 50' max); CHAMPION WALK 28' x 30'; brick, donor bricks (D-046); extend to; parking later; BUS DROP; LOOP; offset E (or W) of the; portal view (D-034);; diagram — size TBD; drop curb; SERVICE DRIVE (diagram); S1 SERVICE / LOADING (D-034); ROAD (assumed south; site TBD, D-006); 1 SITE PLAN — CAMPUS DIAGRAM (SITE TBD); BUILDING (south wall); LEGEND; Frozen Rev D outline (dashed); Exit stairs 76" clear (D-052); Event floor; Champion Walk (brick); Portal piers (limestone)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

# PRELIMINARY — CONCEPTUAL DESIGN — NOT FOR CONSTRUCTION

PROJECT

# Hazel Green Regional Athletic Complex Trojan Horse Arena · Hazel Green area, Madison County, Alabama (site TBD, D-006)

PHASE

# PHASE 2

SHEET TITLE

# SITE PLAN — CAMPUS DIAGRAM SITE TBD · SCHEMATIC

SCALE
AS

# NOTED

DATE

# October

2026

REV
A

DRAWN BY

## Drawn by KEYSTONE (AI) for Shane Brazelton

SHEET
P2-C-101

210' x 252' + NE stair tower (next A-101/A-102)

dashed = frozen Rev D outline 204' x 252'

PARCEL / PROPERTY LINES, SETBACKS, PARKING, UTILITIES, STORMWATER: TBD (D-006) | N

1" = 60'-0" · north approximate · road assumed south · diagram only (no surveyed dimensions)

30'

### 2 ENTRY — PORTAL + CHAMPION WALK — 1" = 30'

Building, next revision (D-053 east shift)

FOOTPRINT vs 55,000 SF CAP (D-031)

| footprint SF | margin SF
Frozen Rev D drawn footprint (204 x 252 + tower) | 51,503.0 | 3,497.0
+ east shift 6' x 252' (D-053 DECIDED) | 53,015.0 | 1,985.0
+ NE tower widened for 76" ST-2 (D-052 DECIDED) | 53,026.7 | 1,973.3
Bound: all 4 stairs grow outward at 76" | 53,275.1 | 1,724.9
Program basis (G-003 Rev F method), 76" stairs + shift | 54,588.9 | 411.1

STATUS
- SITE TBD (D-006): this is a layout diagram, not a site plan for permit. Parcel, property lines, setbacks, grading, parking count, utilities and stormwater are TBD. AHJ (R-006): Madison County Inspection Department if the parcel is unincorporated (Hazel Green is); the county states no zoning limits on construction; county codes 2018 IBC / IFC / NFPA 101; State Fire Marshal 2021 IFC.

ENTRY (DECIDED)
- Freestanding limestone portal over the walk (D-043), 50' max (D-050), 44' wide x 6' deep (ASSUMED), 30' south of the E1 doors (D-046). Champion Walk 28' x 30' = 840 SF brick, ≈ 3,700 4x8 donor bricks; vendor cost ≈ $70.9k if all 4x8 (Shane's sheet, D-044 input; install + base not included). Dashed: later extension to parking.

BUS + SERVICE (D-034 DECIDED defaults)
- South bus drop loop offset EAST so it does not block the portal view (west is equally allowed; the SW FLEX / team assembly room would favor west). Drop curb links to the walk's south end. Service / deliveries at the north door S1 by a west-side drive (alignment TBD). Loop, drive and apron are diagrams: lane widths, bus turning template and apron size TBD (civil).

BUILDING CHANGES FOR THE NEXT A-101 / A-102 / A-301 REVISION (frozen sheets stay frozen)
- East seats 6' further from the mats (D-053 DECIDED): east wall + exits X6-X9 move 6' east → 210' x 252'. Upper-tier risers 19" (front row 7.08') — section only.
- Exit stairs 76" clear with intermediate handrails (D-052 DECIDED, 7:49 AM CT; worst-case egress 304" vs 292.4" required) and a mid landing = width (D-051): 12.67' x 21.33' each, grown inward from their corners; frozen 10.8' x 19' dashed. ST-2's NE tower widens to 21.33' x 5'.
- Event lockers re-planned to full-height zones (D-049); exits under the tier front need ≥ 7'-6".

FIRE ACCESS / WATER (TBD)
- Fire apparatus access roads, hydrants and fire flow per IFC Appendices B, C, D (State Fire Marshal, 2021 IFC; D107 recommended) and the county's 2018 IFC. Exit discharge from X1-X10 to a public way (IBC 1028) TBD with the parcel.
