thebardchat/TrojanHorseAreana/blueprints/phase2/out/pdf/P2-G-003.pdf

# PRELIMINARY — CONCEPTUAL DESIGN — NOT FOR CONSTRUCTION

PROJECT

## Hazel Green Regional Athletic Complex Trojan Horse Arena · Hazel Green area, Madison County, Alabama (site TBD, D-006)

PHASE

## PHASE 2

SHEET TITLE

## LOCKED PROGRAM + LOOP D-035 · AREA BY LEVEL ONLY

SCALE

## NTS

DATE

## October

2026

REV
F

DRAWN BY

### Drawn by KEYSTONE (AI) for Shane Brazelton

SHEET
P2-G-003

## 1 AREA BY LEVEL — 2,200 SEATS, MIX (D-009), L2 LOOP (D-035)

SPACE | REV F LOOP | REV E | BASIS
LEVEL 1 (net SF)
Event floor (D-030, locked) | 16,400 | 16,400 | phase2.yaml · D-030
Lower tier seats (1,100), TELESCOPIC | 3,719 | 3,719 | 3.38 SF/seat (R-008) · fixed col. 6.0
Boys Locker Room | 3,500 | 3,500 | phase2.yaml tag
Girls Locker Room (D-013) | 3,503 | 3,503 | phase2.yaml tag; D-013 open
Event / visitor locker rooms | 3,600 | 3,600 | 4 x (14 wrestlers + 4 staff) x 50 SF
Foyer / trophy lobby (hall of champions) | 800 | 800 | 200 + 400 + 200 (Loudoun 2014)
Lower concourse | 1,375 | 1,375 | 25% of seats x 5 SF standing (T1004.5)
Public restrooms L1 (37 fixtures) | 1,850 | 1,850 | T2902.1 x 50 SF (R-009)
Concession stand | 275 | 275 | Loudoun kitchen proxy; D-011
First aid | 120 | 120 | Loudoun 2014; 1 room counted
Equipment storage (mats + floor covers) | 700 | 700 | Loudoun gym storage proxy
Equipment room | 300 | 300 | Loudoun equip./maint. proxy
Stairs (4) + elevator | 874 | 890 | R-015
L1 net | 37,016 | 37,032
Mechanical (5% of total gross, at grade) | 3,939 | 3,854 | R-014 · LOW
L1 GROSS (x 1.25) | 51,194 | 51,108 | R-014 gross-up
LEVEL 2 (net SF)
Upper tier seats (1,100), FIXED | 6,600 | 6,600 | 6.0 SF/seat (R-008)
Strength & Conditioning | 5,224 | 6,000 | D-035: was 6,000 (trimmed for the loop)
Cross-Training Mat Area | 3,500 | 4,000 | D-035: was 4,000 (trimmed for the loop)
Administrative office | 470 | 470 | 150 + 120 + 200 (Loudoun 2014)
Upper concourse / balcony | — | 1,375 | Rev E only; the loop replaces it
Public restrooms L2 (29 fixtures) | 1,450 | 1,450 | T2902.1 x 50 SF (R-009)
Stairs (4) + elevator | 874 | 890 | R-015
L2 net rooms (without the loop) | 18,118 | 20,785
Running / training loop (drawn, not grossed up) | 4,942 | — | P2-A-102 Rev D · ASSUMED no x1.25
L2 GROSS (x 1.25 rooms + loop) | 27,590 | 25,981
FIT CHECK
Arena volume gross (floor + lower tier, double height) | 25,149 | 25,149
Arena volume + L2 gross | 52,738 | 51,130 | L2 sits over the L1 ring
FOOTPRINT = max(L1, arena volume + L2) | 52,738 | 51,130 | mix: set by arena volume + L2
MARGIN under the 55,000 SF cap (D-031) | 2,262 | 3,870 | target ≥ 2,000 (Shane)
if the loop were grossed up x1.25: footprint / margin 53,974 / 1,026 | — | would miss the target
Meets the ≥ 2,000 SF target? | YES | YES
TOTAL GSF (2 levels) | 78,784 | 77,089 | not capped (D-031)
REV F = Rev E (MIX, D-009) with S&C 5,224 and cross-training 3,500 SF (D-035) and the loop in place of the upper concourse. Loads, stairs and fixtures recomputed (stair width 64.0 in). The loop is circulation drawn at full size, so it is added to L2 gross as drawn (ASSUMED). The arena volume + L2 (52,738) sets the footprint.

## 2 SEATS BY SIDE AND TIER = 2,200 (= REV E)

SIDE | LOWER (TELE.) | UPPER (FIXED) | TOTAL
North | 353 | 308 | 661
South | 341 | 308 | 649
East | 406 | 484 | 890
TOTAL | 1,100 | 1,100 | 2,200
capacity drawn | 1,306 | 1,125 | 2,431
No west tier (OK'd). Lower: 6 rows x 24 in = 12 ft extended (R-008), less the 12 ft portal and two 8 ft vomitories. Upper: 15 ft at 6.0 SF/seat. Each tier = 1,100, split by side in proportion to drawn capacity (P2-A-101/102 Rev B). Spare capacity is left for wheelchair spaces and aisles; the upper tier has only 25 spare. Tiers unchanged in Rev D.

## 3 LEVEL 2 RUNNING / TRAINING LOOP (D-035)

2 lanes x 42 in = 7 ft all around, squared corners. Centerline 148 x 205 ft: 2 x (148 + 205) = 706 ft; 5,280 / 706 = 7.48 laps/mile. Area 4,942 SF. Lanes: UFC 4-740-02N 4.1.7 (42 in, min 3 lanes), Athletic Business (36-42 in; max 12 laps/mile, 8-10 preferred). 2 lanes is ASSUMED: 3 lanes (10.5 ft) does not fit without moving the upper tier. Event days: upper concourse, spectators cross it at the tier entries; non-event days: training. 42 in guards at open edges (IBC 1015.2, 1015.3).

## 4 FIXTURES BY LEVEL (IBC 2021 T2902.1)

LEVEL | LOAD | WC M | WC W | LAV M | LAV W | DF | SUM
L1 | 1,428 | 10 | 18 | 4 | 5 | 2 | 37
L2 | 1,100 | 8 | 14 | 3 | 4 | 2 | 29
TOTAL | 2,528 | 18 | 32 | 7 | 9 | 4 | 66
L1 = lower seats + 328 floor occupants (50 SF each); L2 = upper seats. Unchanged from Rev D (load follows seats). Restrooms flank the lobby, L2 stacked over L1.

## 5 STAIRS, ELEVATOR, WHEELCHAIR

L2 load 1,279 → 4 stairs (T1006.3.3) x 64 in (0.2 in/occ., 1005.3.1), ≈ 203 SF each per level + 1 elevator (1104.4) = 874 SF per level, aligned on both levels. 18 wheelchair spaces + companions (IBC T1109.2.2.1, ADA 221.3), dispersed (ADA 221.2.3) — placement in the telescopic and fixed tiers is an architect task. Rev D moves ST-1, ST-2 and the elevator clear of the loop.

## 6 RESULT

### LOCKED PROGRAM + LOOP

16,400 SF floor · 2,200 seats · 2 levels L2 loop 706 ft · 7.48 laps/mile Footprint 52,738 · margin 2,262 Target ≥ 2,000 SF: MET

Total 78,784 GSF (Rev E: 77,089). Drawn building (P2-A-101/102 Rev D) = 204 x 252 ft + 19 x 5 ft NE stair tower = 51,503 SF, 3,497 under the cap. NOTE: the program footprint is 1,235 SF MORE than the drawn building: the drawn plan fits, but the x 1.25 gross-up allowance no longer fully fits inside it.

## 7 LOCKED IN phase2.yaml

- Event floor 16,400 SF; 4 x 42 ft mats, 2 x 2 (D-030).
- 2,200 seats in the bowl, N, S and E sides; 2 levels; footprint cap 55,000 SF (D-031).
- Seating MIX: telescopic lower tier, fixed upper tier (D-009, Shane 4:30 AM CT).
- S&C 5,224 + cross-training 3,500 SF on Level 2 (D-035; were 6,000 / 4,000).
- Continuous L2 loop, 2 x 42 in (D-035, Shane 4:55 AM CT). Changes only on CHANGE APPROVED.

## 8 STILL OPEN

- Loop lane count (2 ASSUMED; 3 preferred); 50/50 tier split and 6 telescopic rows (ASSUMED).
- AHJ / code edition (D-008); girls locker size (D-013); concession scope (D-011); owner (D-007); site (D-006).
- Suites PARKED (future add-on).

## 9 CITED vs ASSUMED

CITED: seat SF and row depth (R-008), fixtures, egress and wheelchair tables (R-009, R-015, R-016), gross-up and mechanical share (R-014), lane width (UFC 4-740-02N, Athletic Business), guards (IBC 1015). ASSUMED: 2 lanes, loop not grossed up, 50/50 tiers, 6 rows, 50 SF/fixture, box shape.

### 10 SOURCES (retrieved 2026-10-04)

- Shane 2026-10-04 4:55 AM CT (D-035 loop, Rev F); 4:30 AM CT (D-009 mix, margin target)
- R-008, R-009, R-014, R-015, R-016; UFC 4-740-02N; Athletic Business; IBC 2021 1015
- Rev E (mix, no loop) frozen; history in Revs A-E
