thebardchat/TrojanHorseAreana/blueprints/phase2/out/pdf/P2-G-003_RevH.pdf

# PRELIMINARY — CONCEPTUAL DESIGN — NOT FOR CONSTRUCTION

PROJECT

## Hazel Green Regional Athletic Complex Trojan Horse Arena · Hazel Green area, Madison County, Alabama (site TBD, D-006)

PHASE

# PHASE 2

SHEET TITLE

## LOCKED PROGRAM + LOOP REV E PLAN · D-057 SIZES

SCALE

# NTS

DATE

# October

2026

REV
H

DRAWN BY

### Drawn by KEYSTONE (AI) for Shane Brazelton

SHEET
P2-G-003

## 1 AREA BY LEVEL — 2,200 SEATS, MIX, L2 LOOP, 76 IN STAIRS (D-052)

SPACE | REV G/H | REV F | BASIS
LEVEL 1 (net SF)
Event floor 16,400 + 864 east clear zone | 17,264 | 16,400 | D-030 · D-053 east tier 16 ft
Lower tier seats (1,100), TELESCOPIC | 3,719 | 3,719 | 3.38 SF/seat (R-008) · fixed col. 6.0
Boys Locker Room | 3,500 | 3,500 | phase2.yaml tag
Girls Locker Room (D-013) | 3,503 | 3,503 | phase2.yaml tag; D-013 open
Event / visitor locker rooms | 3,600 | 3,600 | 4 x (14 wrestlers + 4 staff) x 50 SF
Foyer / trophy lobby (hall of champions) | 800 | 800 | 200 + 400 + 200 (Loudoun 2014)
Lower concourse | 1,375 | 1,375 | 25% of seats x 5 SF standing (T1004.5)
Public restrooms L1 (37 WC + lav) | 1,850 | 1,850 | T2902.1 WC+lav x 50 SF (R-009)
Concession stand | 275 | 275 | Loudoun kitchen proxy; D-011
First aid | 120 | 120 | Loudoun 2014; 1 room counted
Equipment storage (mats + floor covers) | 700 | 700 | Loudoun gym storage proxy
Equipment room | 300 | 300 | Loudoun equip./maint. proxy
Stairs (4 x 76 in) + elevator | 1,145 | 874 | D-052 · landing = width (D-051)
L1 net | | | 38,151 | | 37,016
Mechanical (5% of total gross, at grade) | 4,037 | 3,939 | R-014 · LOW
L1 GROSS (x 1.25) | 52,735 | 51,194 | R-014 gross-up
LEVEL 2 (net SF)
Upper tier seats (1,100), FIXED | 6,600 | 6,600 | 6.0 SF/seat (R-008)
Strength & Conditioning | 5,224 | 5,224 | D-035 (as Rev F)
Cross-Training Mat Area | 3,500 | 3,500 | D-035 (as Rev F)
Administrative office | 470 | 470 | 150 + 120 + 200 (Loudoun 2014)
Upper concourse / balcony | — | — | the loop replaces it (D-035)
Public restrooms L2 (29 WC + lav) | 1,450 | 1,450 | T2902.1 WC+lav x 50 SF (R-009)
Stairs (4 x 76 in) + elevator | 1,145 | 874 | D-052 · landing = width (D-051)
L2 net rooms (without the loop) | 18,389 | 18,118
Running / training loop (drawn, not grossed up) | 5,026 | 4,942 | A-102 Rev E (Rev F: Rev D) · no x1.25
L2 GROSS (x 1.25 rooms + loop) | 28,012 | 27,590
Arena volume gross (floor + east zone + lower tier) | 26,229 | 25,149
Arena volume + L2 gross | 54,241 | 52,738 | L2 sits over the L1 ring
PROGRAM FOOTPRINT = max(L1, arena volume + L2)54,241 | 52,738 | set by arena volume + L2
PROGRAM TOTAL GSF (L1 gross + L2 gross) | 80,748 | 78,784 | no cap (D-056)
SIZE — D-057: L1 FOOTPRINT · L2 AREA · TOTAL GSF · CHANGE vs LAST REV (no cap, no margin)
| DRAWN | REV D | CHANGE | PROGRAM | REV F | CHANGE | DRAWN − PROG.
| A-101/102 E | drawn | vs Rev D | G-003 G/H | program | vs Rev F | (C-3)
L1 FOOTPRINT | 53,062 | 51,503 | +1,559 | 54,241 | 52,738 | +1,503 | −1,179
L2 AREA | 28,914 | 28,363 | +551 | 28,012 | 27,590 | +423 | +902
TOTAL GSF | 81,976 | 79,866 | +2,110 | 82,253 | 80,328 | +1,925 | −277
Program TOTAL here = program footprint + L2 gross (82,253), to compare like with like; L1 + L2 gross = 80,748. REV G = Rev F with 76 in stairs and 76 in intermediate landings (D-052, D-051; 270 SF each per level), the 864 SF east clear zone (D-053) in L1 and the arena volume, and the Rev E loop (5,026 SF). Drawn sizes are measured on P2-A-101/102 Rev E. The program footprint carries 1,506 SF of L1 ring that no program line counts; R-021 explains drawn vs program line by line. R-021's flat-add estimate (54,589 / 28,432) is replaced by this method.

## 2 SEATS BY SIDE AND TIER = 2,200 (REV E PLAN)

SIDE | LOWER (TELE.) | UPPER (FIXED) | TOTAL
North | | | 359 | | 314 | | 673
South | | | 347 | | 314 | | 661
East | | | 394 | | 472 | | 866
TOTAL | 1,100 | 1,100 | 2,200
capacity drawn | 1,349 | 1,155 | 2,504
No west tier (OK'd). Lower: 6 rows x 24 in = 12 ft extended (R-008), less the 12 ft portal and two 8 ft vomitories. Upper: 15 ft, 5 rows x 36 in at 19 in risers (D-053), stepping down to the court (D-049), 6.0 SF/seat. Each tier = 1,100, split by side in proportion to drawn capacity (P2-A-101/102 Rev E). The 6 ft east shift makes the N / S bands 132 ft: split was N 661 / S 649 / E 890 (Rev F); totals unchanged. Upper spare 55.

## 3 LEVEL 2 RUNNING / TRAINING LOOP (D-035)

2 lanes x 42 in = 7 ft all around, squared corners. Centerline 154 x 205 ft: 2 x (154 + 205) = 718 ft; 5,280 / 718 = 7.35 laps/mile. Area 5,026 SF. Lanes: UFC 4-740-02N 4.1.7 (42 in, min 3 lanes), Athletic Business (36-42 in; max 12 laps/mile, 8-10 preferred). 2 lanes is ASSUMED: 3 lanes (10.5 ft) does not fit without moving the upper tier. Event days: upper concourse, spectators cross it at the tier entries; non-event days: training. 42 in guards at open edges (IBC 1015.2, 1015.3). East leg 6 ft further east (D-053).

## 4 FIXTURES BY LEVEL (IBC 2021 T2902.1)

LEVEL | LOAD WC M WC W LAV M LAV W DF WC+LAV | SUM
SUM incl. 4 drinking fountains
L1 | 1,428 | 10 | 18 | 4 | 5 | 2 | 37 | 39
L2 | 1,100 | 8 | 14 | 3 | 4 | 2 | 29 | 31
TOTAL 2,528 | 18 | 32 | 7 | 9 | 4 | 66 | 70
L1 = lower seats + 328 floor occupants (50 SF each); L2 = upper seats. Unchanged from Rev F (load follows seats). Restrooms flank the lobby, L2 stacked over L1.
SUM incl. 4 drinking fountains (2 per level, T2902.1). Restroom SF uses WC+LAV only (66 x 50 SF, ASSUMED); fountains sit outside the rooms. Rev G's SUM column was WC+LAV (66). 1 service sink per level (not counted).

## 5 STAIRS, ELEVATOR, WHEELCHAIR

4 stairs (T1006.3.3) x 76 in (D-052: worst case 1,462 x 0.2 in = 292.4 in ≤ 4 x 76 = 304 in), intermediate landing = width (D-051): 12.67 x 21.33 ft ≈ 270 SF each per level + 1 elevator (1104.4) = 1,145 SF per level, aligned on both levels. 18 wheelchair spaces + companions (IBC T1109.2.2.1, ADA 221.3), dispersed (ADA 221.2.3) — placement in the telescopic and fixed tiers is an architect task. ST-2 needs a 6.67 ft NE stair tower to clear the loop (was 5 ft).

## 6 RESULT

### DRAWN SIZE (A-101/102 REV E)

### L1 53,062 · L2 28,914 SF

### TOTAL 81,976 GSF (+2,110 vs Rev D)

2,200 seats · loop 718 ft · 7.35 laps/mi No SF cap (D-056) · size = budget + parcel

Drawn building = 210 x 252 ft + 21.33 x 6.67 ft NE stair tower = 53,062 SF. Program footprint 54,241 (+1,179 vs drawn): the program grosses up the open arena box; the drawing absorbs the 76 in stairs in the box and draws the lobby void (R-021). Event floor drawn 120 x 144 = 17,280 SF.

## 7 LOCKED IN phase2.yaml

- Event floor 16,400 SF; 4 x 42 ft mats, 2 x 2 (D-030).
- 2,200 seats in the bowl, N, S and E sides; 2 levels; no SF cap (D-056, D-031 retired).
- Seating MIX: telescopic lower tier, fixed upper tier (D-009, Shane 4:30 AM CT).
- S&C 5,224 + cross-training 3,500 SF on Level 2 (D-035; were 6,000 / 4,000).
- Continuous L2 loop, 2 x 42 in (D-035). 76 in stairs (D-052); east tier 16 ft, 19 in upper risers (D-053).

## 8 STILL OPEN

- Loop lane count (2 ASSUMED; 3 preferred); 50/50 tier split and 6 telescopic rows (ASSUMED).
- Under-tier headroom reading (D-049): Rev E keeps rows 1-2 (< 7'-6" clear, ASSUMED) for storage / mech only.
- AHJ / code edition (D-008); girls locker size (D-013); concession scope (D-011); owner (D-007); site (D-006).
- Suites PARKED (future add-on).

## 9 CITED vs ASSUMED

CITED: seat SF and row depth (R-008), fixtures, egress and wheelchair tables (R-009, R-015, R-016), gross-up and mechanical share (R-014), lane width (UFC 4-740-02N, Athletic Business), guards (IBC 1015). ASSUMED: 2 lanes, loop not grossed up, east zone grossed up like the floor, 50/50 tiers, 6 rows, 50 SF/fixture, box shape.

## 10 SOURCES (retrieved 2026-10-04)

- Shane 2026-10-04 9:10 AM CT (Rev G); 10:03 AM CT (Rev H, reviewer C-11: fixture SUM label); D-051..D-053, D-056, D-057; R-021
- R-008, R-009, R-014, R-015, R-016, R-020; UFC 4-740-02N; Athletic Business; IBC 2021 1011.6, 1015
- Rev H = Rev G numbers; Revs F-G frozen; history in Revs A-G
