thebardchat/TrojanHorseAreana/blueprints/phase2/out/pdf/P2-A-901_RevC.pdf

service apron at S1 — diagram (D-034); ROAD assumed south (site TBD, D-006)
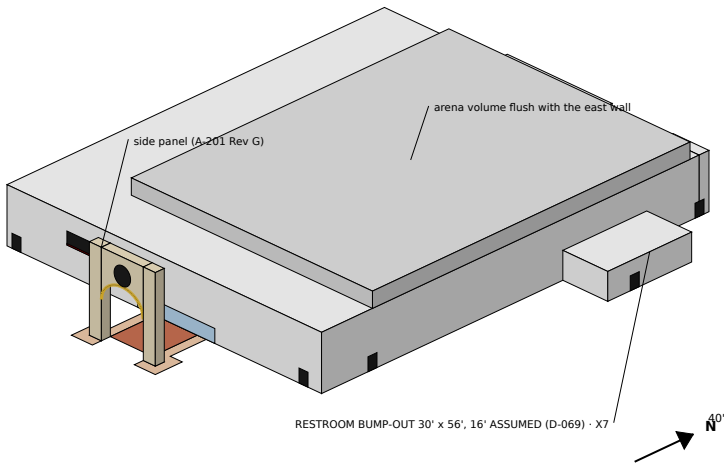
[picture p35: figure]
side panel (A-201 Rev G); arena volume flush with the east wall
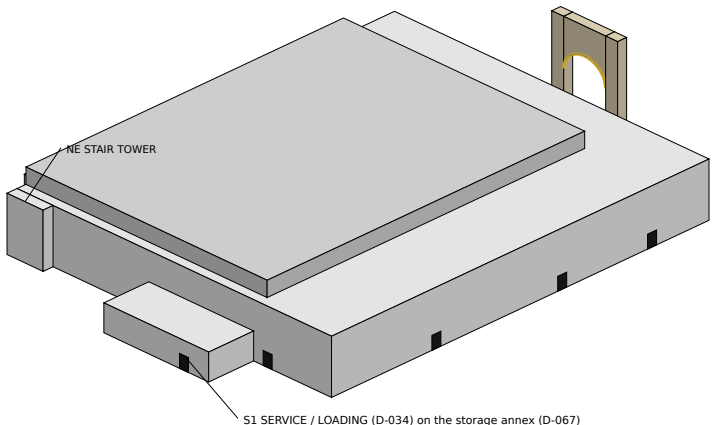
[picture p36: figure]
NE STAIR TOWER
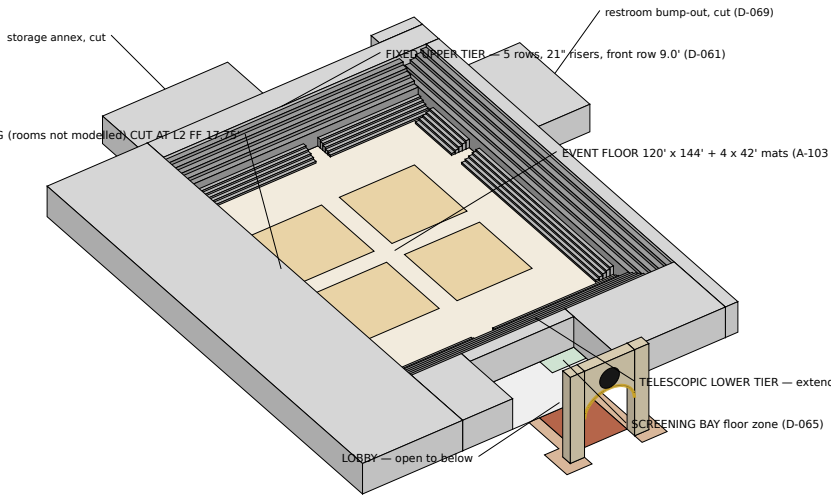
[picture p37: figure]
LOBBY — open to below; SCREENING BAY floor zone (D-065); storage annex, cut; restroom bump-out, cut (D-069)

# PRELIMINARY — CONCEPTUAL DESIGN — NOT FOR CONSTRUCTION

## PROJECT

# Hazel Green Regional Athletic Complex Trojan Horse Arena · Hazel Green area, Madison County, Alabama (site TBD, D-006)

## PHASE

# PHASE 2

## SHEET TITLE

# 3D MASSING MODEL VIEWS

## SCALE

# NTS

## DATE

# October

2026

## REV

C

## DRAWN BY

# Drawn by KEYSTONE (AI) for Shane Brazelton

## SHEET

P2-A-901

## V1 AERIAL FROM SOUTHWEST

axonometric · not to scale

ARENA VOLUME — roof 42' ASSUMED (wall / roof TBD)

RING — roof 32.75' ASSUMED · L2 FF 17.75' DECIDED

FREESTANDING PORTAL 50' max (D-043, D-050)

CHAMPION WALK 28' brick + 6' bands = 40' (D-066)

STORAGE ANNEX 70' x 30', 16' ASSUMED (D-067)

BUS DROP LOOP — diagram (D-034; C-101 Rev C)

N

## V2 CUTAWAY AT L2 FF 17'-9" FROM SOUTHWEST — ROOFS REMOVED

axonometric · not to scale · roofs removed, L1 ring cut solid at L2 FF

EVENT FLOOR 120' x 144' + 4 x 42' mats (A-103 Rev A)

FIXED UPPER TIER — 5 rows, 21" risers, front row 9.0' (D-061)

TELESCOPIC LOWER TIER — extended, 6 rows (D-009)

L1 RING (rooms not modelled) CUT AT L2 FF 17.75'

## V3 AERIAL FROM SOUTHEAST

axonometric · not to scale

RESTROOM BUMP-OUT 30' x 56', 16' ASSUMED (D-069) · X7

N

## V4 AERIAL FROM NORTHWEST (SERVICE SIDE, S1)

axonometric · not to scale

S1 SERVICE / LOADING (D-034) on the storage annex (D-067)

N

## V5 PORTAL + CHAMPION WALK FROM SOUTH-SOUTHWEST

axonometric · not to scale

official mark Ø 11' (D-041, D-047)

50' max · crown 34' · springline 22.1' (D-050)

gold trim (D-045)

40' walk: 6' bands pass outside both piers (D-066)

E1 door bank, 30' behind the portal (D-046)

MASSING ONLY. Volumes from the current schematic params; materials, openings, parapets, roof equipment and structure are not designed. Every height not marked DECIDED is ASSUMED (P2-A-201 Rev G). Not a rendering of a final design.

### HEIGHTS MODELLED

L2 FF 17.75' DECIDED (D-061) · ring roof 32.75' ASSUMED · arena roof 42' ASSUMED (P2-A-201 Rev
G) · portal 50' max, crown 34', springline 22.1' (D-050) · tiers per P2-A-301 Rev D / A-302 Rev C. Door symbols 6' x 8' ASSUMED.

### DECISIONS MODELLED — SHANE 3:31 PM CT

- D-054 DECIDED: chairs-only floor is the design case — no stage / chairs modelled (layout TBD).
- D-065 DECIDED: screening bay in the lobby's east side, shown as a floor zone in the cutaway.
- D-066 DECIDED: 40 ft walk = 28 ft brick + 6 ft bands, around both portal piers.
- D-067 DECIDED: storage annex 70 x 30 ft on the north wall, one storey (16 ft ASSUMED), S1 on its north face.
- D-069 DECIDED: restroom core 2 in a one-storey bump-out 30 x 56 ft on the east wall at V2 (16 ft ASSUMED), X7 on its east face.

### NOTES

- NOT MODELLED: parapets (TBD), rooftop units, structure, windows / cladding, grading, landscaping, lighting, parking (site TBD, D-006), signage content (signage zone TBD), interior rooms.
- Colours: limestone / crimson / gold / brick / brand red + black from P2-A-201 Rev G finishes (hex ASSUMED swatches); greys = material TBD. Arch drawn as a 56-segment polyline; the crimson underside faces down and does not show in views from above.
- Model file: phase2/out/3d/P2-A-901_RevC_massing.obj + .mtl (feet, Y-up export; exterior, cutaway and portal sets).
Sources: params/phase2_massing.yaml, phase2_massing_rev_c.yaml; phase2_plan_rev_i.yaml; phase2_elev_rev_g.yaml; phase2_elev.yaml; phase2_site.yaml (rev_e); phase2_sect.yaml; D-034, D-043, D-045, D-046, D-050, D-054, D-061, D-065 to D-067, D-069; Shane 2026-10-04 3:31 PM CT. P2-A-201 Rev H shows the annex + bump-out.
