thebardchat/TrojanHorseAreana/blueprints/phase2/out/pdf/P2-A-101_RevA.pdf

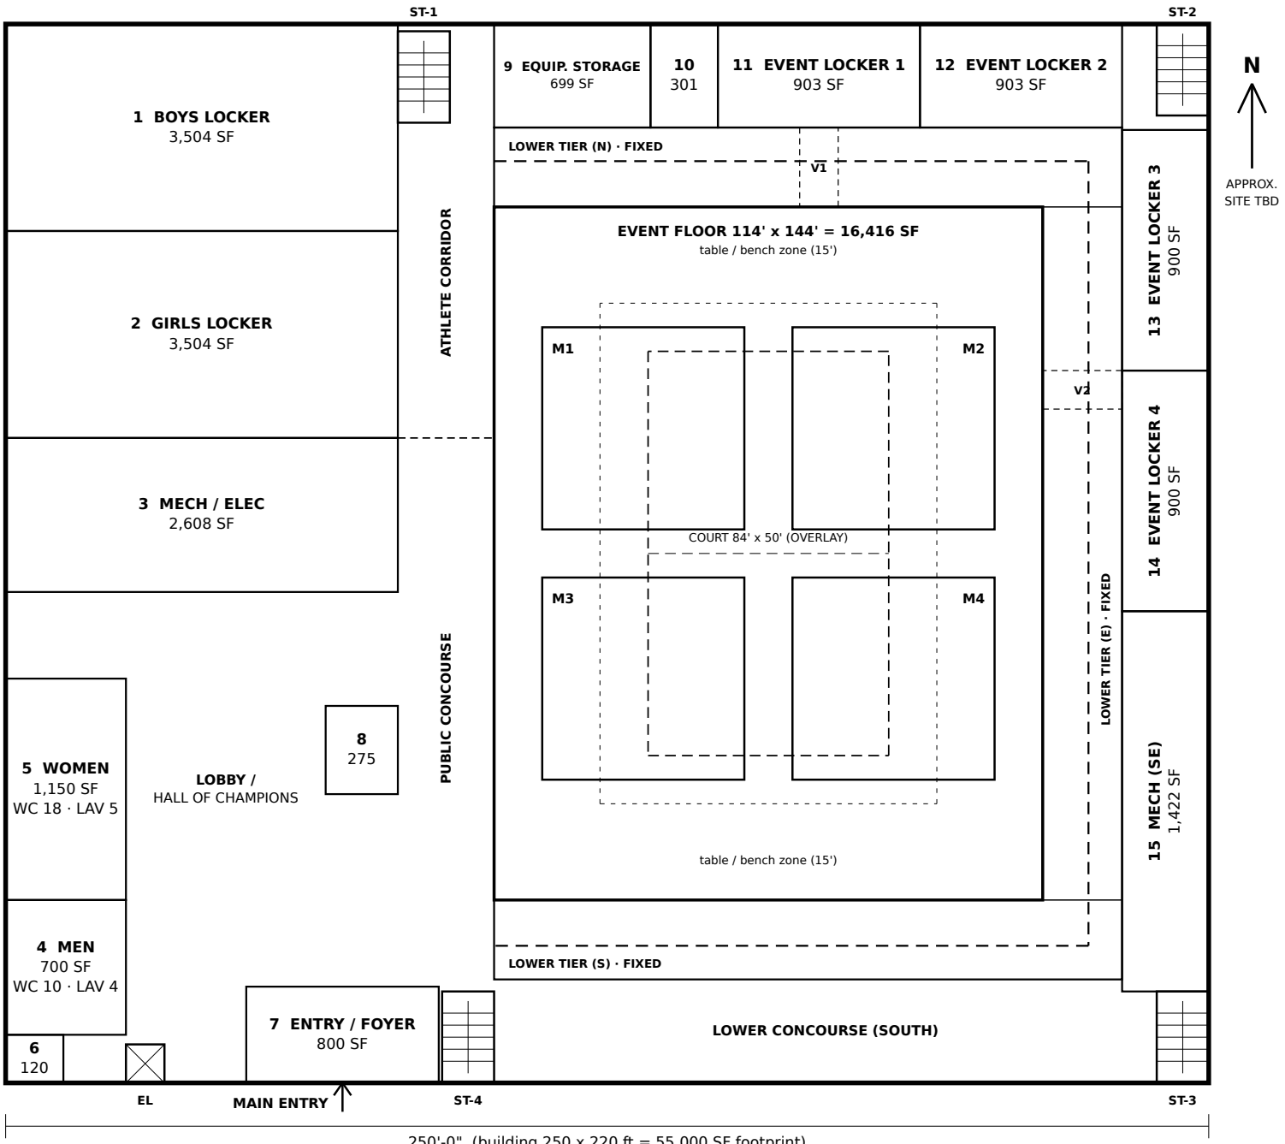
[picture p43: figure]
LOWER TIER (N) · FIXED; LOWER TIER (S) · FIXED; LOWER TIER (E) · FIXED; EVENT FLOOR 114' x 144' = 16,416 SF; table / bench zone (15'); COURT 84' x 50' (OVERLAY); MAIN ENTRY; 1 BOYS LOCKER 3,504 SF; 2 GIRLS LOCKER 3,504 SF; 3 MECH / ELEC 2,608 SF; 4 MEN 700 SF WC 10 · LAV 4; 5 WOMEN 1,150 SF WC 18 · LAV 5; 7 ENTRY / FOYER 800 SF; 9 EQUIP. STORAGE 699 SF; 11 EVENT LOCKER 1 903 SF; 12 EVENT LOCKER 2 903 SF; 13 EVENT LOCKER 3; 14 EVENT LOCKER 4; 15 MECH (SE); LOBBY / HALL OF CHAMPIONS; PUBLIC CONCOURSE ATHLETE CORRIDOR; LOWER CONCOURSE (SOUTH); APPROX. SITE TBD

# PRELIMINARY — CONCEPTUAL DESIGN — NOT FOR CONSTRUCTION

PROJECT

## Hazel Green Regional Athletic Complex Trojan Horse Arena · Hazel Green area, Madison County, Alabama (site TBD, D-006)

PHASE

# PHASE 2

SHEET TITLE

## OVERALL FLOOR PLAN LEVEL 1 · BLOCK PLAN

SCALE
1/32" =
1'-0"

DATE

# October

2026

REV
A

DRAWN BY

## Drawn by KEYSTONE (AI) for Shane Brazelton

SHEET
P2-A-101

# LEVEL 1 — OVERALL FLOOR PLAN

### SCHEMATIC — BLOCK PLAN · scale 1/32" = 1'-0" on 17 x 11 in · north approximate, site TBD

250'-0" (building 250 x 220 ft = 55,000 SF footprint)

220'-0"

0' | 16' | 32' | 64'

# SCHEMATIC — BLOCK PLAN

## LEGEND

Lower tier, FIXED seating (6.0 SF/seat) — base
TELESCOPIC overlay: tier depth if bleachers (3.38 SF/seat) — D-009 OPEN 42' wrestling mat (4, 2 x 2)
84' x 50' court + 10' runout (overlay)
Room block (tag number + drawn SF)
Stair (4) / elevator (X), aligned on both levels

## ROOM SCHEDULE — LEVEL 1 (drawn vs locked program, P2-G-003 Rev D, fixed)

TAG | ROOM | DRAWN SF | PROGRAM | NOTE
— | Event floor (D-030 locked) | 16,416 | 16,400 | 114' x 144'
— | Lower tier, fixed (~1,100 seats) | 6,682 | 6,600 | telescopic line 9.5' deep
1 | Boys Locker | 3,504 | 3,500
2 | Girls Locker | 3,504 | 3,503 | drawn equal to boys (D-013)
3 | Mech / Elec | 2,608 | 2,630
4 | Men | 700 | 700 | 14 fixtures (WC 10, LAV 4; urinals ≤ 6 of the WCs)
5 | Women | 1,150 | 1,150 | 23 fixtures (WC 18, LAV 5)
6 | First Aid | 120 | 120
7 | Entry / Foyer | 800 | 800
8 | Concession | 275 | 275
9 | Equip. Storage | 699 | 700
10 | Equip. Room | 301 | 300
11 | Event Locker 1 | 903 | 900
12 | Event Locker 2 | 903 | 900
13 | Event Locker 3 | 900 | 900
14 | Event Locker 4 | 900 | 900
15 | Mech (SE) | 1,422 | 1,416

## AREA CHECK

Drawn footprint 55,000 SF = cap 55,000 (D-031). Program L1 gross 54,949 fixed / 50,868 telescopic (P2-G-003 Rev D): the block uses all of it; space beyond the program is lobby and concourse. Mechanical drawn 4,030 vs 4,047 program. Fixtures: L1 load 1,428 → 37 in two rooms; 2 drinking fountains + 1 service sink in concourse alcoves (not drawn). 18 wheelchair spaces + companions across both tiers (not drawn).

## LAYOUT NOTES (KEYSTONE, ASSUMED — architect to confirm)

- Lockers west next to the floor via the athlete corridor, kept off the public concourse (DR1). Girls drawn equal to boys (D-013).
- Entry + foyer at the south end of the west wing (reference plan: south-center); concourse spine runs north along the floor.
- Event lockers split north (1-2) and east (3-4); vomitories V1/V2 through the tier are TBD. No tier on the west; stage TBD (no source).
- Table/bench zones 15 ft N and S; court overlay long axis N-S. Exit separation, travel distance and sightlines NOT checked. Sources: phase2.yaml (locked, D-030, D-031); P2-G-003 Rev D; R-005, R-008, R-009, R-012, R-014, R-015; reference plan (Shane). Geometry: params/phase2_plan.yaml.
