thebardchat/TrojanHorseAreana/blueprints/phase2/out/pdf/P2-A-102_RevA.pdf

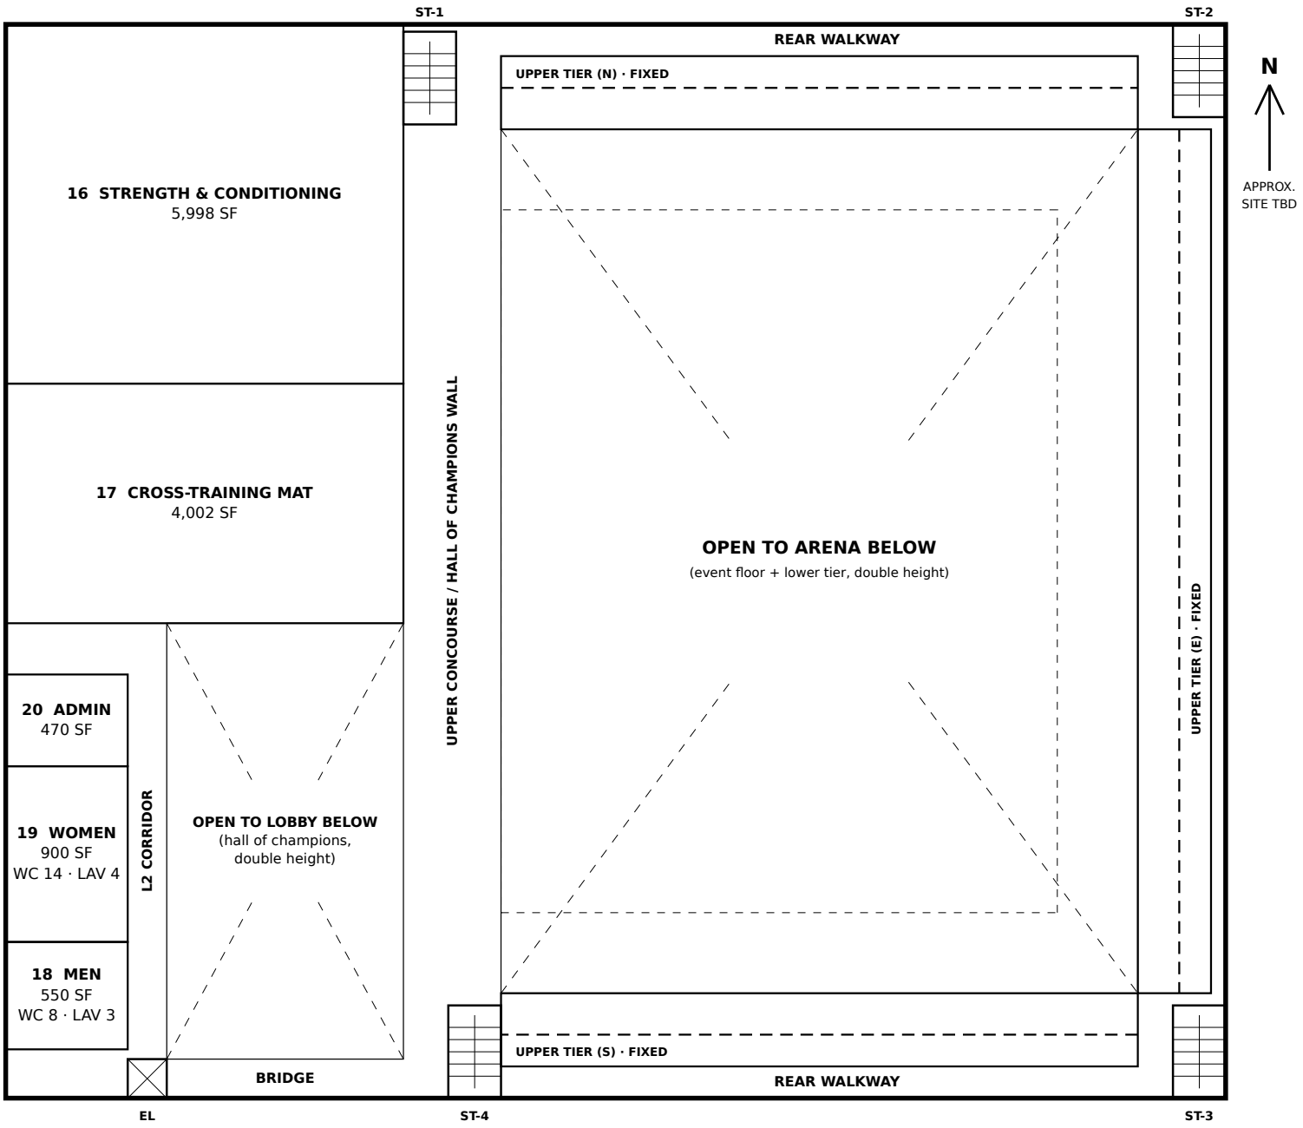
[picture p44: figure]
UPPER TIER (N) · FIXED; UPPER TIER (S) · FIXED; UPPER TIER (E) · FIXED; OPEN TO ARENA BELOW; OPEN TO LOBBY BELOW (hall of champions, double height); 16 STRENGTH & CONDITIONING 5,998 SF; 17 CROSS-TRAINING MAT 4,002 SF; 18 MEN 550 SF WC 8 · LAV 3; 19 WOMEN 900 SF WC 14 · LAV 4; 20 ADMIN 470 SF; L2 CORRIDOR; BRIDGE; REAR WALKWAY; APPROX. SITE TBD

# PRELIMINARY — CONCEPTUAL DESIGN — NOT FOR CONSTRUCTION

PROJECT

## Hazel Green Regional Athletic Complex Trojan Horse Arena · Hazel Green area, Madison County, Alabama (site TBD, D-006)

PHASE

# PHASE 2

SHEET TITLE

## OVERALL FLOOR PLAN LEVEL 2 · BLOCK PLAN

SCALE
1/32" =
1'-0"

DATE

# October

2026

REV
A

DRAWN BY

## Drawn by KEYSTONE (AI) for Shane Brazelton

SHEET
P2-A-102

# LEVEL 2 — OVERALL FLOOR PLAN

### SCHEMATIC — BLOCK PLAN · scale 1/32" = 1'-0" on 17 x 11 in · north approximate, site TBD

250'-0" (building 250 x 220 ft = 55,000 SF footprint)

220'-0"

(event floor + lower tier, double height)

UPPER CONCOURSE / HALL OF CHAMPIONS WALL

0' | 16' | 32' | 64'

# SCHEMATIC — BLOCK PLAN

## LEGEND

Upper tier, FIXED seating (6.0 SF/seat) — base
TELESCOPIC overlay: tier depth if bleachers (3.38 SF/seat) — D-009 OPEN Open to below
Room block (tag number + drawn SF)
Stair (4) / elevator (X), aligned on both levels

## ROOM SCHEDULE — LEVEL 2 (drawn vs locked program, P2-G-003 Rev D, fixed)

TAG | ROOM | DRAWN SF | PROGRAM | NOTE
— | Upper tier, fixed (~1,100 seats) | 6,570 | 6,600 | telescopic line 8.5' deep
16 | Strength & Conditioning | 5,998 | 6,000 | Level 2 over the lockers (D-030)
17 | Cross-Training Mat Area | 4,002 | 4,000 | Level 2 over girls locker + mech (D-030)
18 | Men | 550 | 550 | 11 fixtures (WC 8, LAV 3; urinals ≤ 5 of the WCs)
19 | Women | 900 | 900 | 18 fixtures (WC 14, LAV 4)
20 | Admin | 470 | 470

## AREA CHECK

Drawn L2 floor 27,570 SF (footprint minus open-to-below) vs program L2 gross 25,981 fixed / 22,380 telescopic; the extra is rear walkways and the upper concourse. Total drawn ≈ 82,570 vs 80,930 program GSF. L2 sits over the L1 ring, nothing over the arena volume. Fixtures: L2 load 1,100 → 29, stacked over L1 rooms. Stair widths: 65 in (R-015).

## LAYOUT NOTES (KEYSTONE, ASSUMED — architect to confirm)

- S&C + cross-training on Level 2 over the lockers (D-030); gym floor loads → structural engineer.
- Restrooms + admin stacked over L1 restrooms; L2 corridor + bridge connect the stairs, elevator and upper concourse.
- Upper tier 15 ft deep on N, S and E over the L1 ring; rear walkways N and S. Suites PARKED (none drawn).
- Exit separation, travel distance, sightlines and structure NOT checked. Floor-to-floor 15 ft ASSUMED.
Sources: phase2.yaml (locked, D-030, D-031); P2-G-003 Rev D; R-005, R-008, R-009, R-012, R-014, R-015; reference plan (Shane). Geometry: params/phase2_plan.yaml.
