thebardchat/TrojanHorseAreana/blueprints/phase2/out/pdf/P2-A-102_RevB.pdf

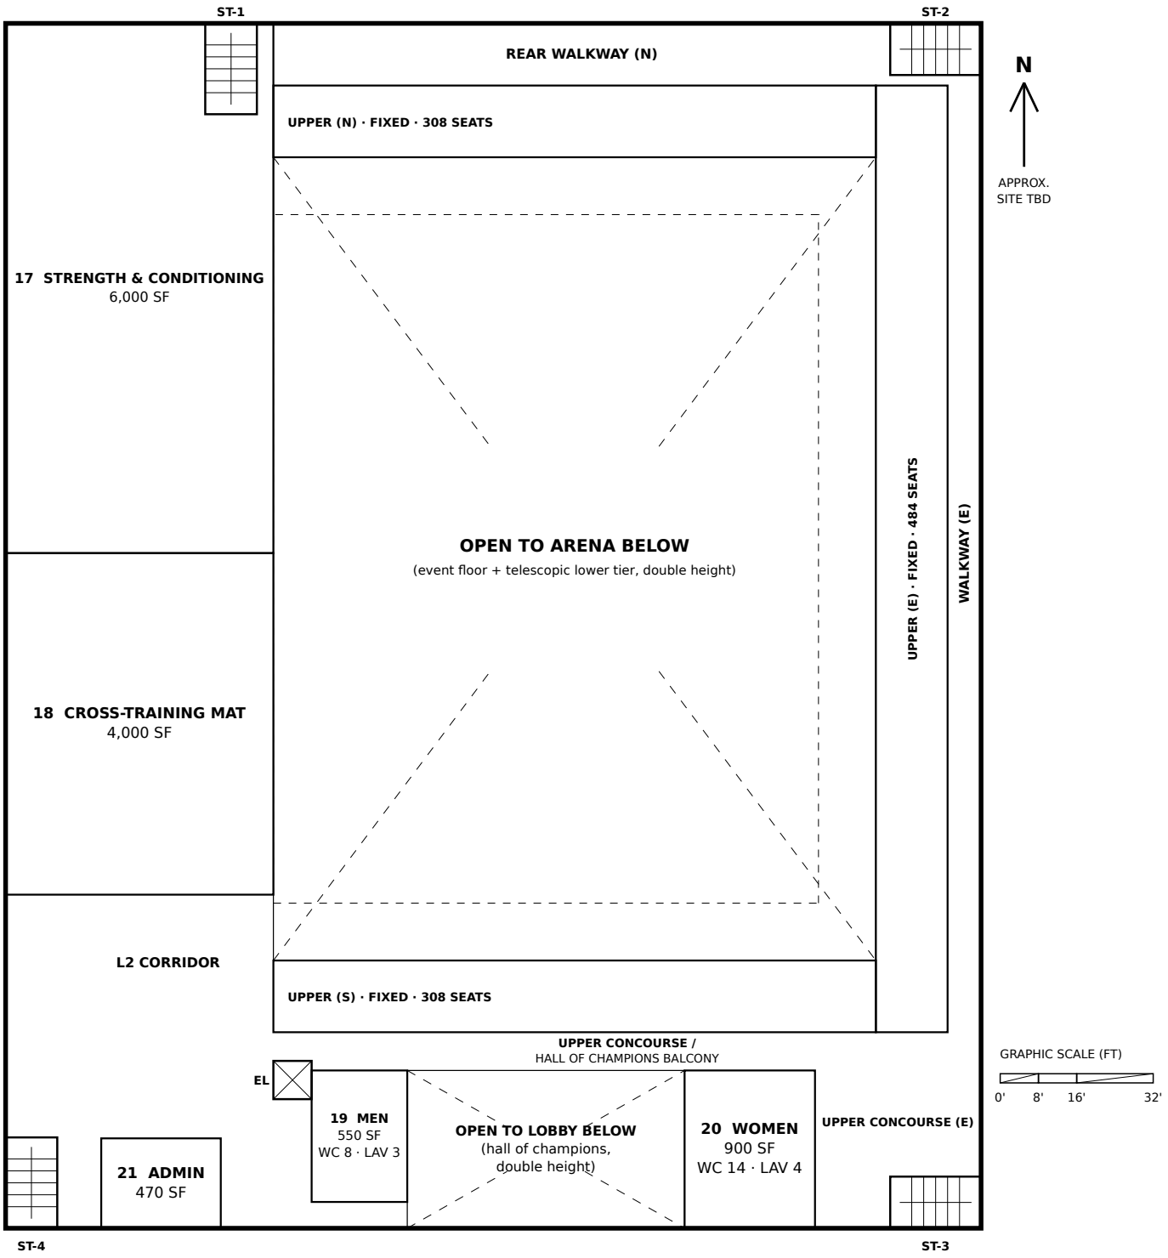
[picture p45: figure]
UPPER (N) · FIXED · 308 SEATS; UPPER (S) · FIXED · 308 SEATS; UPPER (E) · FIXED · 484 SEATS; OPEN TO ARENA BELOW; OPEN TO LOBBY BELOW (hall of champions, double height); 17 STRENGTH & CONDITIONING 6,000 SF; 18 CROSS-TRAINING MAT 4,000 SF; 19 MEN 550 SF WC 8 · LAV 3; 20 WOMEN 900 SF; 21 ADMIN; WC 14 · LAV 4; L2 CORRIDOR; UPPER CONCOURSE / HALL OF CHAMPIONS BALCONY; UPPER CONCOURSE (E); REAR WALKWAY (N); WALKWAY (E); APPROX. SITE TBD; GRAPHIC SCALE (FT)

# PRELIMINARY — CONCEPTUAL DESIGN — NOT FOR CONSTRUCTION

PROJECT

## Hazel Green Regional Athletic Complex Trojan Horse Arena · Hazel Green area, Madison County, Alabama (site TBD, D-006)

PHASE

# PHASE 2

SHEET TITLE

## OVERALL FLOOR PLAN LEVEL 2 · BLOCK PLAN

SCALE
1/32" =
1'-0"

DATE

# October

2026

REV
B

DRAWN BY

## Drawn by KEYSTONE (AI) for Shane Brazelton

SHEET
P2-A-102

204'-0" (building 204 x 252 ft = 51,408 SF footprint)

252'-0"

(event floor + telescopic lower tier, double height)

# SCHEMATIC — BLOCK PLAN

# LEVEL 2 — OVERALL FLOOR PLAN (REV B)

scale 1/32" = 1'-0" on 17 x 11 in · north approximate, road assumed south, site TBD

## LEGEND

Upper tier, FIXED (6.0 SF/seat) on the Level 2 deck — D-009 Open to below (arena; lobby double height)
Room block (tag number + drawn SF)
Stair (4) / elevator (X), same position on both levels

## ROOM SCHEDULE — LEVEL 2 (drawn vs locked program, P2-G-003 Rev E)

TAG | ROOM | DRAWN SF | PROGRAM | NOTE
— | Upper tier, fixed (1,100 seats) | 6,750 | 6,600 | N 308 / S 308 / E 484
17 | Strength & Conditioning | 6,000 | 6,000 | over boys locker + NW mech; ST-1 inside
18 | Cross-Training Mat Area | 4,000 | 4,000 | over girls locker (D-030)
19 | Men | 550 | 550 | 11 fixtures (WC 8, LAV 3; urinals ≤ 5 of the WCs)
20 | Women | 900 | 900 | 18 fixtures (WC 14, LAV 4)
21 | Admin | 470 | 470

## AREA CHECK

Drawn L2 floor 28,326 SF (box minus open-to-below) vs program L2 gross 25,981; the extra is the corridor, walkways and balcony. Total drawn ≈ 79,734 vs 77,089 program GSF. Upper tier sits over the L1 ring; L2 restrooms (29 fixtures) stack over L1's; balcony over the lobby carries the hall of champions wall.

## LAYOUT NOTES (KEYSTONE, ASSUMED — architect to confirm)

- S&C + cross-training on Level 2 over the lockers (D-030); gym floor loads → structural engineer.
- Restrooms stacked over L1's; admin over the team entry; balcony links west and east over the lobby.
- Upper tier 15 ft on N, S, E over the L1 ring; the south tier sits over the lobby. Suites PARKED.
- Exit separation, travel distance, sightlines and structure NOT checked. Floor-to-floor 15 ft ASSUMED.
Sources: phase2.yaml (D-009, D-030, D-031); Shane 2026-10-04 4:30 AM CT; P2-G-003 Rev E; R-005, R-008, R-009, R-012, R-014, R-015. Geometry: params/phase2_plan_rev_b.yaml.
