thebardchat/TrojanHorseAreana/blueprints/phase2/out/pdf/P2-A-302_RevB.pdf

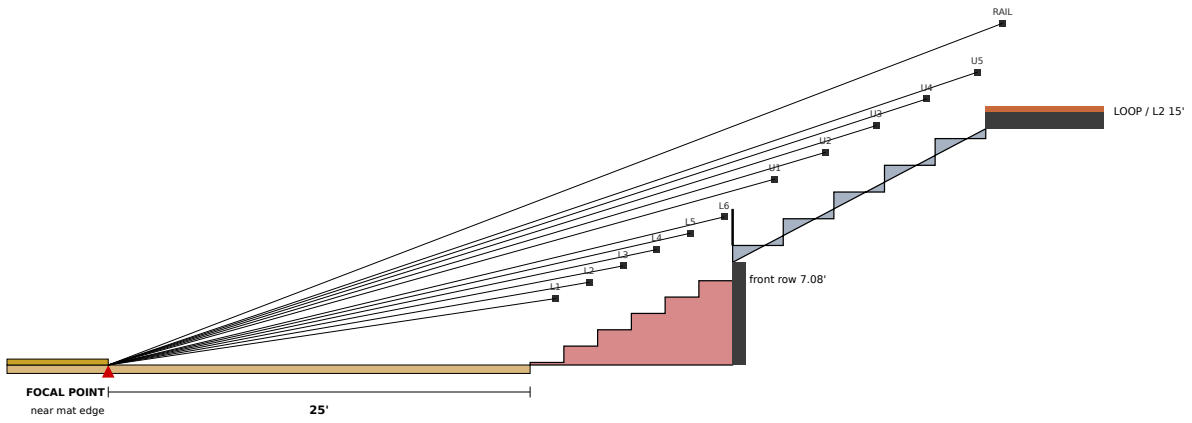
[picture p51: figure]
FOCAL POINT; near mat edge; RAIL; LOOP / L2 15'; front row 7.08'
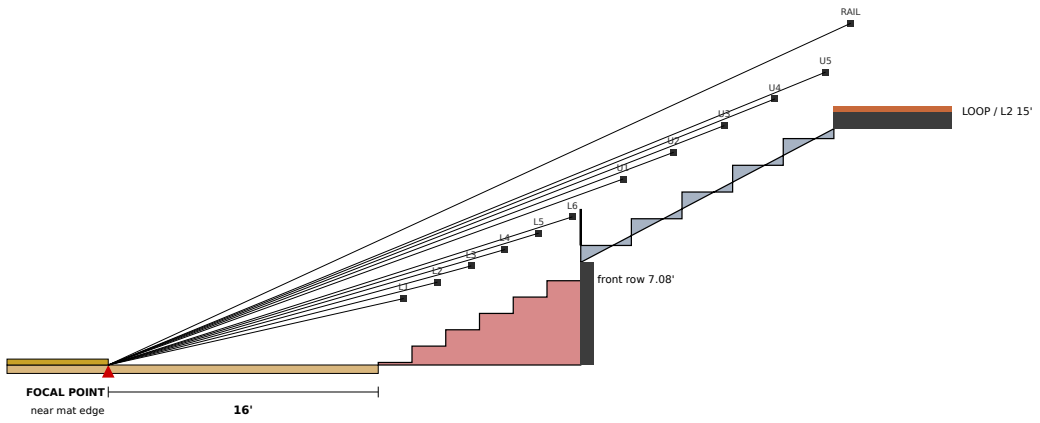
[picture p52: figure]
FOCAL POINT; near mat edge; RAIL; LOOP / L2 15'; front row 7.08'
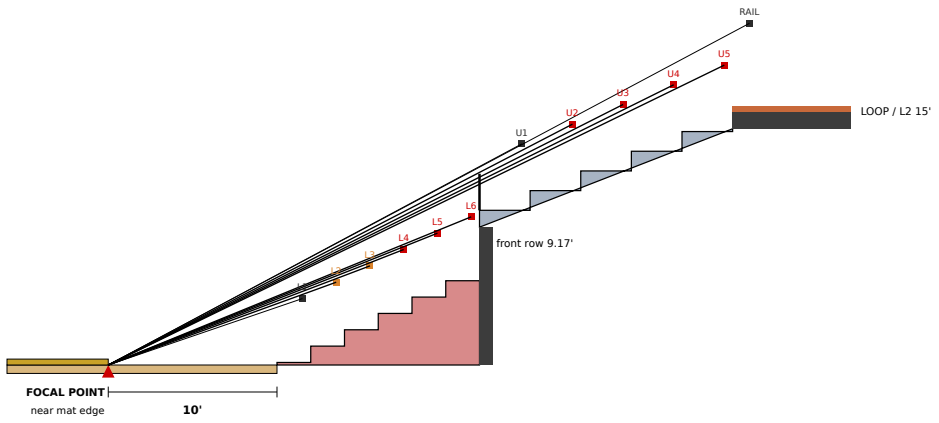
[picture p53: figure]
FOCAL POINT; near mat edge; RAIL; LOOP / L2 15'; front row 9.17'

# PRELIMINARY — CONCEPTUAL DESIGN — NOT FOR CONSTRUCTION

### PROJECT

# Hazel Green Regional Athletic Complex Trojan Horse Arena · Hazel Green area, Madison County, Alabama (site TBD, D-006)

### PHASE

# PHASE 2

### SHEET TITLE

# SIGHT-LINE STUDY SCHEMATIC · COLOR

### SCALE

AS

# NOTED

### DATE

# October

2026

### REV

B

### DRAWN BY

## Drawn by KEYSTONE (AI) for Shane Brazelton

### SHEET

P2-A-302

### 1 AS DRAWN (REV E) — NORTH / SOUTH SIDE (seated eyes)

3/32" = 1'-0" · focal 25' (10' clear + 15' table zone) · telescopic 11⅝" · upper 19"/row, front 7.08'

### 2 AS DRAWN (REV E) — EAST SIDE (seated eyes)

3/32" = 1'-0" · focal 16' (D-053) · upper 19"/row · worst side

### 3 REV D BASIS (SUPERSEDED) — EAST SIDE (seated eyes)

3/32" = 1'-0" · focal 10' · upper 14"/row, front 9.17' · P2-A-302 Rev A 'as drawn'

SIGHTLINE GRADE (C, mm)

≥ 90 PASS

60–90 MARGINAL

< 60 FAIL

Dots = eyes; label colour = C of that row over the row in front. Values: table.

upper-tier deck (front 7.08')

upper-tier face

CLOSED

STACK

front deck 7.08' − 77.4"

= 7.6" structure + finish

recess min 48" deep x

77.4" high (Hussey)

Rev D 9.17' front: 32.6" left

upper-tier deck (front 7.08')

upper-tier face

7'-6" ceiling over row 6 (1003.2) = 12.34'

deck at recess back 9.19' − structure

rows 5-6 stay in the recess

under the overhang when open

need

### 4 TELESCOPIC STACK UNDER THE UPPER-TIER FRONT

3/16" = 1'-0" · recessed (Hussey) · N/S as drawn · dashed = Rev D 9.17' front

(a) CLOSED — only 7.6" left for structure: DOES NOT FIT
(b) OPEN — rows 5-6 under the overhang: CONFLICT
AS DRAWN (P2-A-101 Rev E / A-301 Rev C) | REV D BASIS (superseded)

N/S 25'
seated

N/S 25'
stand

E 16'
seated

E 16'
stand

N/S 25'
seated
| N/S 25' stand E 10' seated

E 10'
stand

ROW

L2 | 190 | 162 | 142 | 101 | 190 | 162 | 74 | 15
L3 | 178 | 152 | 129 | 92 | 178 | 152 | 64 | 13
L4 | 167 | 142 | 118 | 84 | 167 | 142 | 57 | 11
L5 | 157 | 134 | 109 | 77 | 157 | 134 | 51 | 10
L6 | 149 | 127 | 101 | 72 | 149 | 127 | 46 | 9
U1 | 428 | 397 | 352 | 313 | 1014 | 984 | 829 | 780
U2 | 211 | 183 | 139 | 103 | 49 | 20 | -119 | -162
U3 | 198 | 171 | 127 | 94 | 45 | 19 | -107 | -146
U4 | 185 | 161 | 118 | 87 | 43 | 18 | -97 | -133
U5 | 175 | 151 | 109 | 81 | 40 | 17 | -89 | -122
RAIL (stands) | 709 | 309 | 673 | 273 | 582 | 182 | 513 | 113
fascia clr (U1) | 326 | 701 | 263 | 631 | 286 | 661 | 131 | 490
front row (ft) | 7.08 | 7.08 | 7.08 | 7.08 | 9.17 | 9.17 | 9.17 | 9.17

METHOD
- C = D(N + R)/(D + T) − R (Green Guide 12.3), computed from each actual eye position (also covers the step between tiers and the loop rail). Focal point = near edge of the nearest mat at floor level (Shane). Eyes: seated 1.2 m above the tread, 0.15 m forward of the row's rear edge; standing 1.6 m (5'-3") — secondary sources, see R-020. Grades: ≥ 90 mm PASS (FIFA preferred, CEN/TR 15913 new stands), 60–90 MARGINAL, < 60 FAIL (FIFA minimum 60).
- Focal distances from P2-A-101 Rev E: N and S tier fronts 25' from the nearest mat (10' clear + 15' table zone); E tier front 16' (D-053; building 210'). No west tier. Section-only study (2D); corners and wheelchair positions TBD.
RESULTS — AS DRAWN (REV E, D-053 DECIDED)
- Upper 19" per 36" row (3 aisle risers of 6⅓", 12" treads; IBC 1030.14.2), front row 7.08' (back stays at the loop, D-049). Every seated row PASSES: N/S ≥ 149 mm, E ≥ 101. Standing: N/S ≥ 127; E ≥ 72 (L4–L6, U4–U5 MARGINAL, none FAIL).
- Lower tier stays at the Hussey 11⅝" rise. U1 clears the 26" fascia (326 mm N/S, 263 E seated).
REV D BASIS (SUPERSEDED, P2-A-302 Rev A 'as drawn')
- 14"/row upper + 10' east focal: upper FAILS on every side (N/S seated 40–49, E negative); E lower L4–L6 FAIL. Kept for comparison only; fixed by D-053 on Plan Rev E.
TELESCOPIC STACK UNDER THE UPPER-TIER FRONT (D-049)
- Closed stack, recessed (Hussey min 4'-0" deep x 6'-5⅜" high) under the 7.08' front leaves 7.6" for structure + finish — DOES NOT FIT. Open: rows 5–6 would sit under the overhang (< 7'-6", 1003.2). Keep the stack in front of the upper-tier face (as P2-A-301 Rev C).
LOW BAND + EXIT PATHS (D-061 OPEN, R-022)
- 1.5' tier structure (ASSUMED) leaves 5.6' / 7.2' under rows 1–2 (6' low band). Exit N, Exit E, SE concourse and the lobby / portal / athlete-route edge run under it. Option A: omit rows 1–2 there (−125 seats; −56 with rails). Option B: L2 17'-9" + 21" risers (front 9.0'): C unchanged (149 / 101 seated).
