thebardchat/TrojanHorseAreana/blueprints/phase2/out/pdf/P2-A-401_RevA.pdf

AMB. WC; 60" TURN; ROLL-IN; DRYING; BENCH 12'; TRAINER TABLE 6' (ASSUMED); pull side
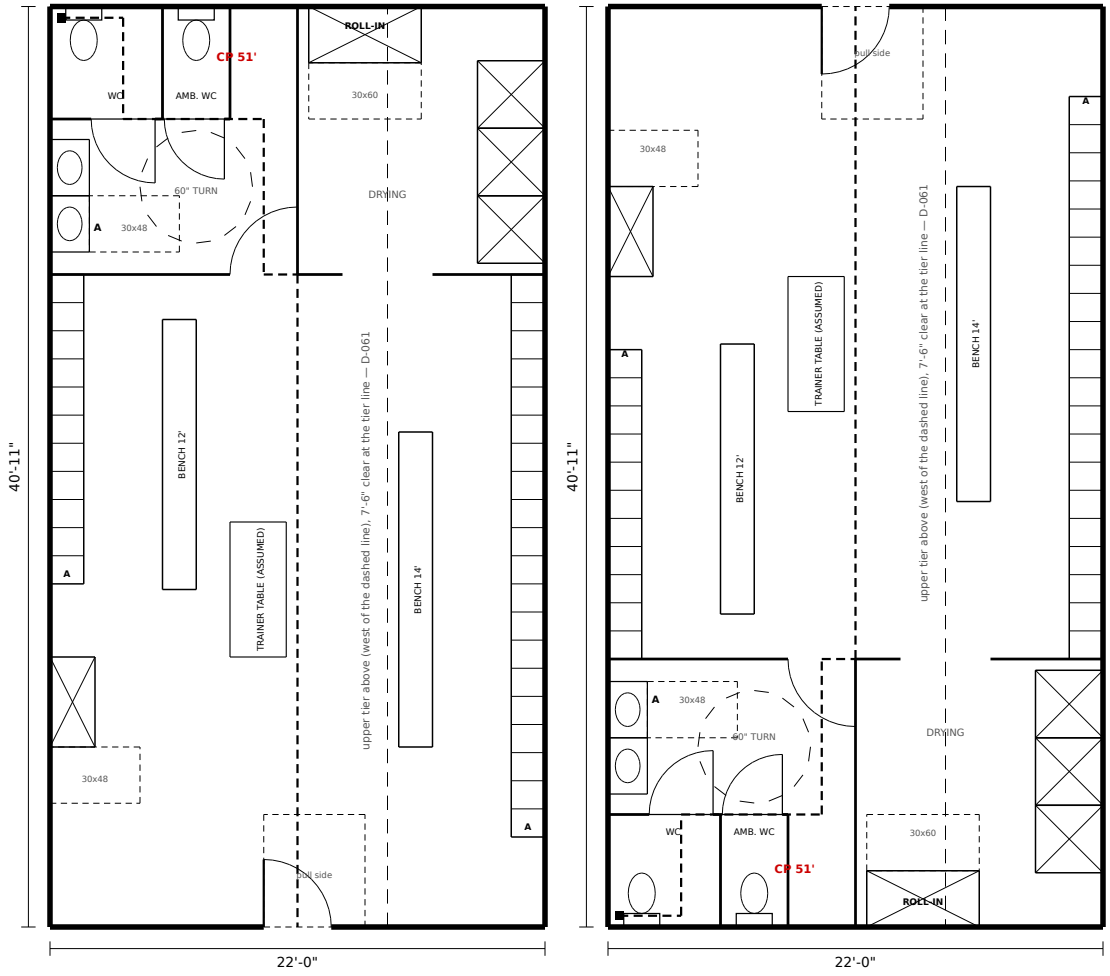
[picture p54: figure]
AMB. WC; 60" TURN; ROLL-IN; DRYING; BENCH 12'; BENCH 14'; TRAINER TABLE (ASSUMED); pull side
AMB. WC; 60" TURN; ROLL-IN; DRYING; BENCH 12'; TRAINER TABLE 6' (ASSUMED); pull side

# PRELIMINARY — CONCEPTUAL DESIGN — NOT FOR CONSTRUCTION

## PROJECT

# Hazel Green Regional Athletic Complex Trojan Horse Arena · Hazel Green area, Madison County, Alabama (site TBD, D-006)

## PHASE

# PHASE 2

## SHEET TITLE

# ENLARGED PLANS EVENT LOCKER ROOMS 1-4

## SCALE

1/8" =
1'-0"

## DATE

# October

2026

## REV

A

## DRAWN BY

# Drawn by KEYSTONE (AI) for Shane Brazelton

## SHEET

P2-A-401

— — upper tier above this line (to the tier line: 7'-6" clear, D-061)

EVENT LOCKER ROOM 1 — 900 SF · 18 occ.

1/8" = 1'-0" · door on the E wall → EXIT (N) passage · common path 46 ft ≤ 75 (PASS)

— — upper tier above this line (to the tier line: 7'-6" clear, D-061)

EVENT LOCKER ROOM 2 — 900 SF · 18 occ.

1/8" = 1'-0" · door on the W wall → EXIT (N) passage · common path 46 ft ≤ 75 (PASS) upper tier above (west of the dashed line), 7'-6" clear at the tier line — D-061

EVENT LOCKER ROOM 3 — 900 SF · 18 occ.

1/8" = 1'-0" · door on the S wall → EXIT (E) passage · common path 51 ft ≤ 75 (PASS)

upper tier above (west of the dashed line), 7'-6" clear at the tier line — D-061

EVENT LOCKER ROOM 4 — 900 SF · 18 occ.

1/8" = 1'-0" · door on the N wall → EXIT (E) passage · common path 51 ft ≤ 75 (PASS)

1 2

3

4

X5

X7

KEY PLAN — L1 (A-101 G) · 1" = 150'

grey = rooms 1-4 · green = EXIT (N) / (E) passages

### FIXTURES + FURNITURE PER ROOM (ASSUMED; ADA 2010 minimums)

ITEM | RM 1-2 | RM 3-4 | BASIS
Water closets | 2 | 2 | 1 wheelchair 60x60 (604.8.1) + 1 ambulatory 36x60 (604.8.2)
Lavatories | 2 | 2 | 1 accessible: 30x48 forward, rim ≤ 34 in (606)
Showers | 4 | 4 | 1 roll-in 30x60 + 30x60 clear (608.2.2) + 3 at 36x36
Lockers 15 in | 32 | 31 | 2 accessible ≥ 5 % = 2 / 2 (225.2.1, 811)
Benches | 2 + 1 | 2 + 1 | team benches + 1 accessible 24x48, wall-affixed (903)
Room door | 36 in | 36 in | 34 in clear (404.2.3), swings in (IBC 1010.1.2.1, < 50)
Occupant load | 18 | 18 | 900 SF / 50 gross (T1004.5) ≤ 49: one door OK

Schematic enlarged plans: fixture counts, benches, lockers and showers ASSUMED (KEYSTONE). Accessible fixture sizes are ADA 2010 minimums for the architect to develop; not a code review (D-008).

## COMMON PATH — VERIFIED ON THIS LAYOUT (T1006.2.1)

One exit access doorway allowed when the space holds <= 49 occupants and the common path of egress travel is <= 75 ft (Group A, sprinklered) — IBC 2021 1006.2.1, Table 1006.2.1. Measured rectilinear from the most remote
point, through the inner doorways, to the room door; the common path ends at the room door because the exit
passage offers two directions (exterior exit door, or vomitory to the event floor).
ROOM | OCC. WORST POINT | CP ft RESULT | + TO EXIT
1 | 18 accessible WC far corner | 45.6 ≤ 75 PASS | X5 64 ft
2 | 18 accessible WC far corner | 45.6 ≤ 75 PASS | X5 64 ft
3 | 18 accessible WC far corner | 50.9 ≤ 75 PASS | X7 66 ft
4 | 18 accessible WC far corner | 50.9 ≤ 75 PASS | X7 66 ft

Other points checked per room: shower far corner, locker aisle NW, locker aisle SW (rooms 1-2); all shorter. Travel to
the exit door (CP + passage) ≤ 66 ft vs 250 ft (T1017.2). Rectilinear on this layout; walls, door hardware and fixtures ASSUMED → UNVERIFIED until the architect's layout.

## ACCESSIBILITY (ADA 2010 STANDARDS) — WHAT IS DRAWN

- 2 WC per room ASSUMED: 1 wheelchair compartment 60 x 60 in (≥ 60 x 59 floor-mounted, 604.8.1.1; WC centerline 18 in from the side wall, 604.2; door in the front partition at the far side, 604.8.1.2) + 1 ambulatory compartment 36 x 60 in (35-37 x ≥ 60, 604.8.2.1; not required below 6 compartments, 213.3.1, provided ASSUMED); 2 lavatories, 1 with forward-approach 30 x 48 in clear floor + knee / toe clearance, rim ≤ 34 in (606.2, 606.3); 60 in turning circle (304.3.1); no urinals (rooms serve either team / sex, ASSUMED)
- 4 showers per room ASSUMED: 1 standard roll-in 30 x 60 in inside with a 60 in entry and a 30 x 60 in clearance at the open face (608.2.2, 608.2.2.1) = the accessible shower (213.3.6); 3 stalls 36 x 36 in (transfer size, 608.2.1)
- freestanding team benches 18 in deep ASSUMED; one accessible bench per room: 24 x 48 in seat, 17-19 in high, affixed to a wall (back support), 30 x 48 in clear floor at its end parallel to its short axis (ADA 803.4, 903.2-903.5)
- 15 x 18 x 72 in single-tier lockers ASSUMED; at least 5 % (min. 1) accessible: storage within 15-48 in reach (ADA 225.2.1, 811, 308.2.1), 30 x 48 in clear floor (305.3)
- 36 in leaf ≈ 34 in clear ≥ 32 in (ADA 404.2.3; IBC 1010.1.1); swings INTO the room so the 8 ft exit passage stays clear — allowed below 50 occupants (IBC 1010.1.2.1) with a 30 x 48 in space beyond the swing (ADA 803.3); pull-side maneuvering 60 in perpendicular + 18 in beyond the latch (ADA Table 404.2.4.1)
- 36 in min clear width along the locker aisles and to every accessible element (ADA 403.5.1)
- Locker room itself: turning space 304 inside (803.2); door swing leaves 30 x 48 clear beyond the arc (803.3). Scoping: 5 % / min. 1 of each locker-room type (222.1) — all 4 rooms laid out the same way.

## NOTES

- Rooms: 3,600 SF total (4 x 900, D-060 settled), envelopes from P2-A-101 Rev G, unchanged. The 15 ft of each room nearest the arena lies under the upper tier: 7'-6" clear at the tier line rising away from it (D-061; 1'-6" structure ASSUMED, zero margin) — lockers 72 in and shower / toilet partitions fit.
- Wet zone on the inner wall (rooms 1-2) / inner end (rooms 3-4), away from the exterior wall; plumbing walls back onto equipment / mech rooms (ASSUMED). No urinals: rooms serve either team (ASSUMED). Floor drains, finishes, ventilation: architect / MEP.
- Rooms 2 and 4 are mirror images of rooms 1 and 3 (doors face the shared exit passages).

## RESTROOM CORE — NOT IN THIS REVISION

L1 public restroom core NOT in this revision: waits on D-064 (OPEN: size for the worst case or limit the events). Drawn later on P2-A-401 once Shane decides.
Legend: A = accessible element · dashed box = ADA clear floor / clearance · dashed circle = 60 in turning space · X box = shower / accessible bench · red dashed = worst common path (dot = remote point).
Sources: params/phase2_enlarged.yaml; params/phase2_plan_rev_g.yaml; ADA 2010 Standards 213.3.1, 213.3.6, 222.1, 225.2.1, 304.3, 305.3, 308.2.1, 403.5.1, 404.2.3, 404.2.4.1, 604, 606, 608, 803, 811, 903 (www.ada.gov, retrieved 2026-10-04); IBC 2021 1006.2.1, 1010.1.1, 1010.1.2.1, T1004.5, T1017.2 (UpCodes); D-060, D-061, D-064; Shane 2026-10-04 11:24 AM CT.
