thebardchat/TrojanHorseAreana/concepts/P2-A-101_RevK_sheet.png

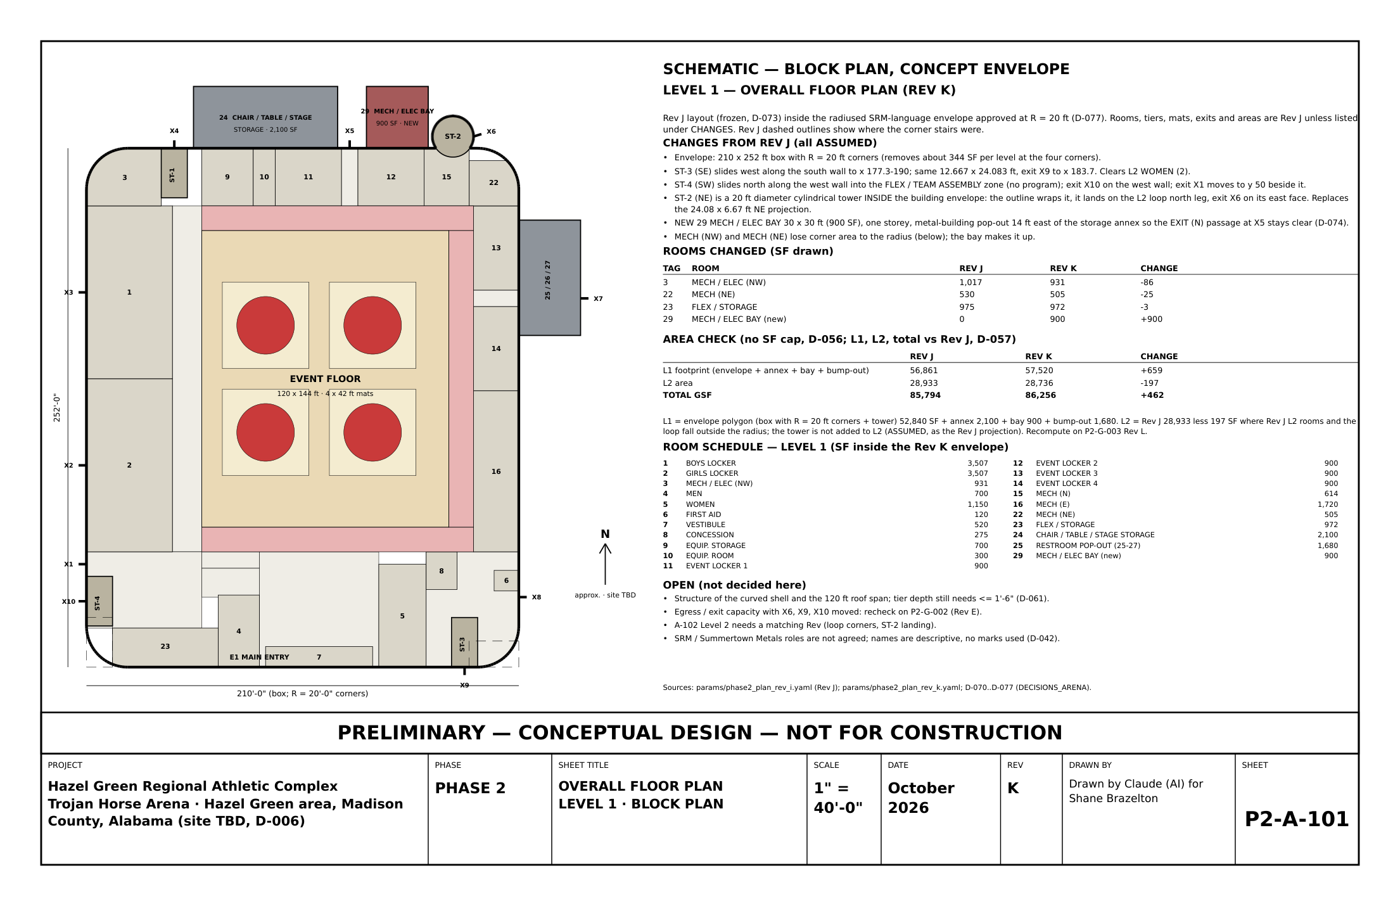
concepts/P2-A-101_RevK_sheet.png
