thebardchat/TrojanHorseAreana/concepts/P2-A-102_RevG_sheet.png

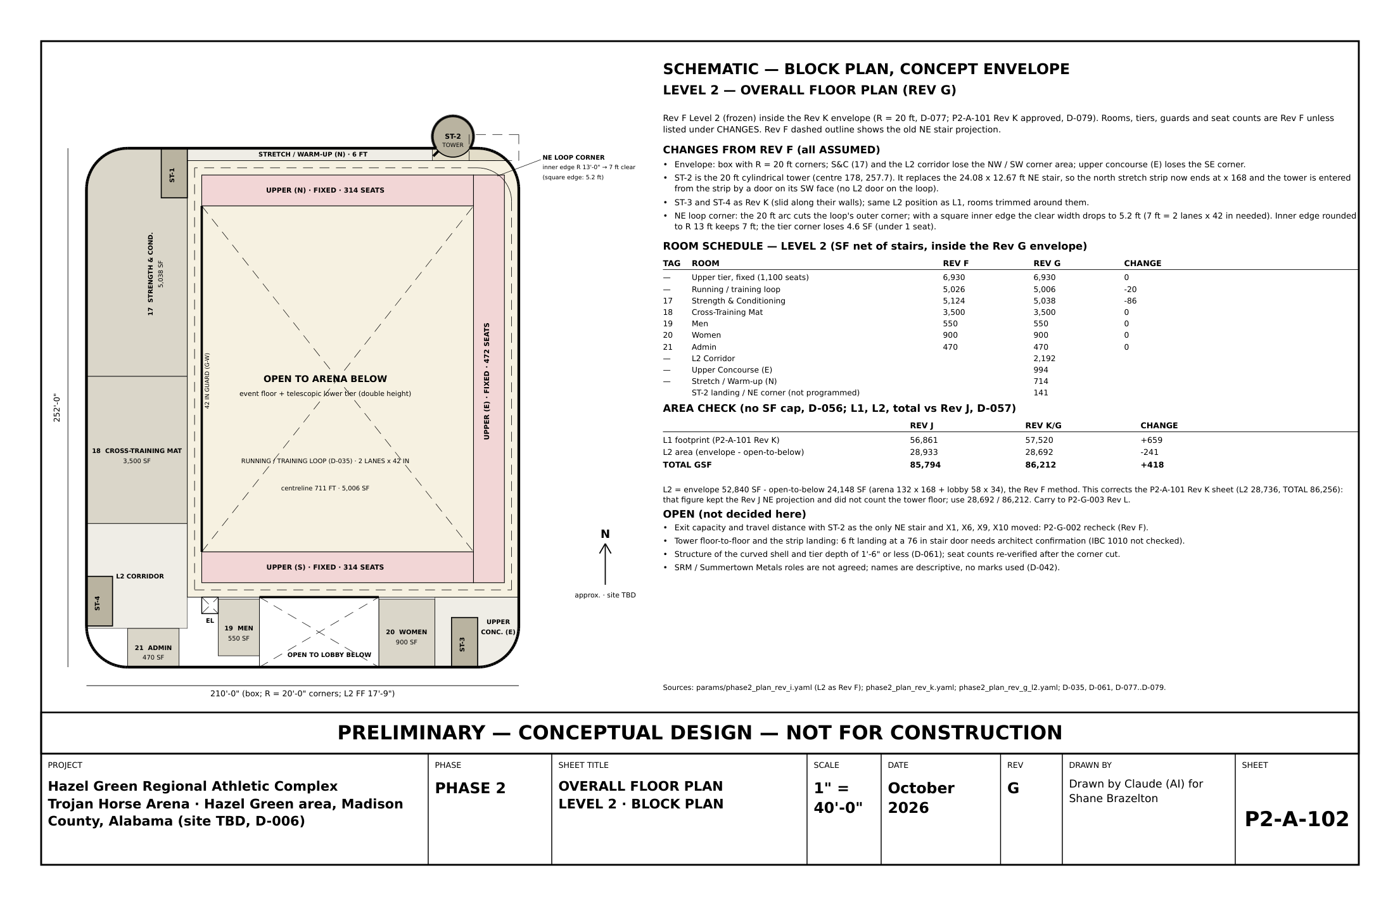
concepts/P2-A-102_RevG_sheet.png
