thebardchat/TrojanHorseAreana/concepts/render_revD_portal.png

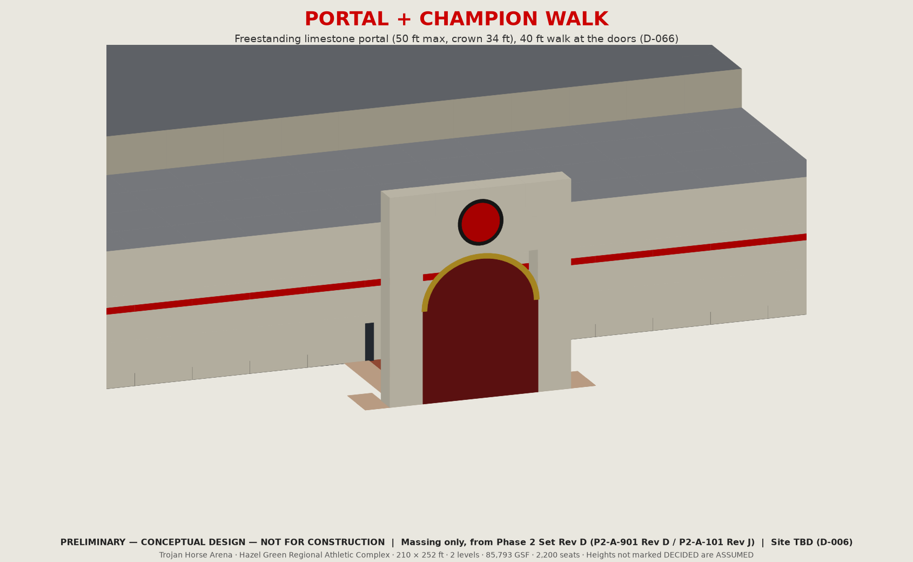
concepts/render_revD_portal.png
