thebardchat/TrojanHorseAreana/concepts/render_srm_concept_aerial_se.png

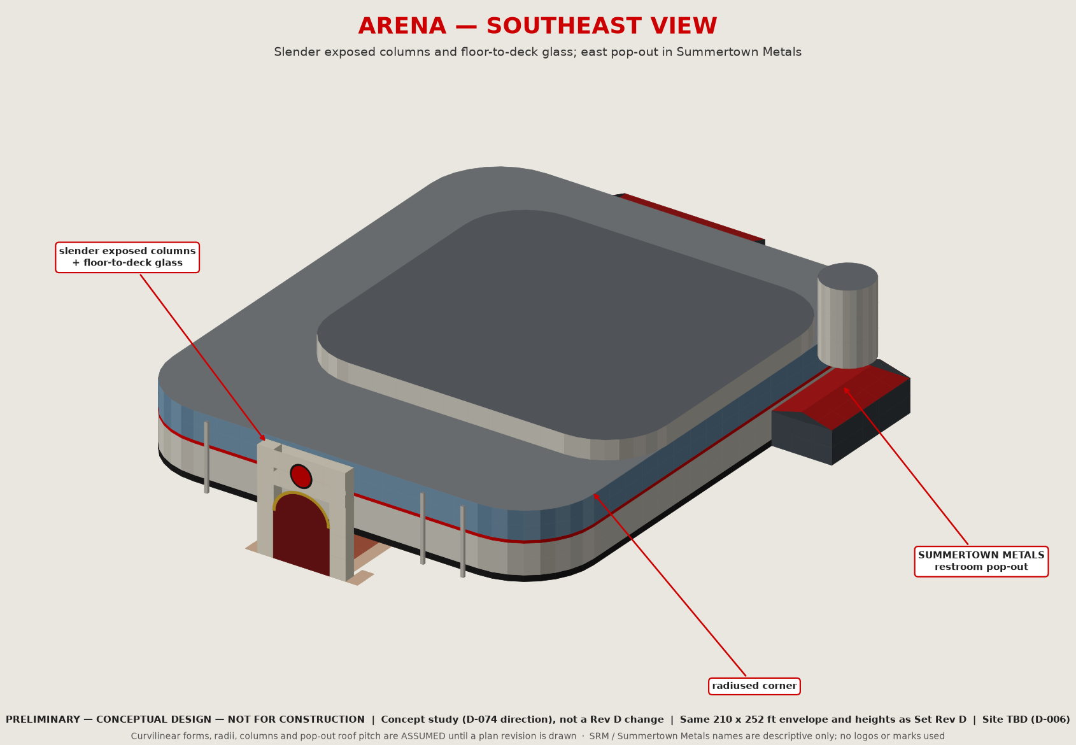
concepts/render_srm_concept_aerial_se.png
