thebardchat/TrojanHorseAreana/concepts/render_srm_concept_plan_revk_study.png

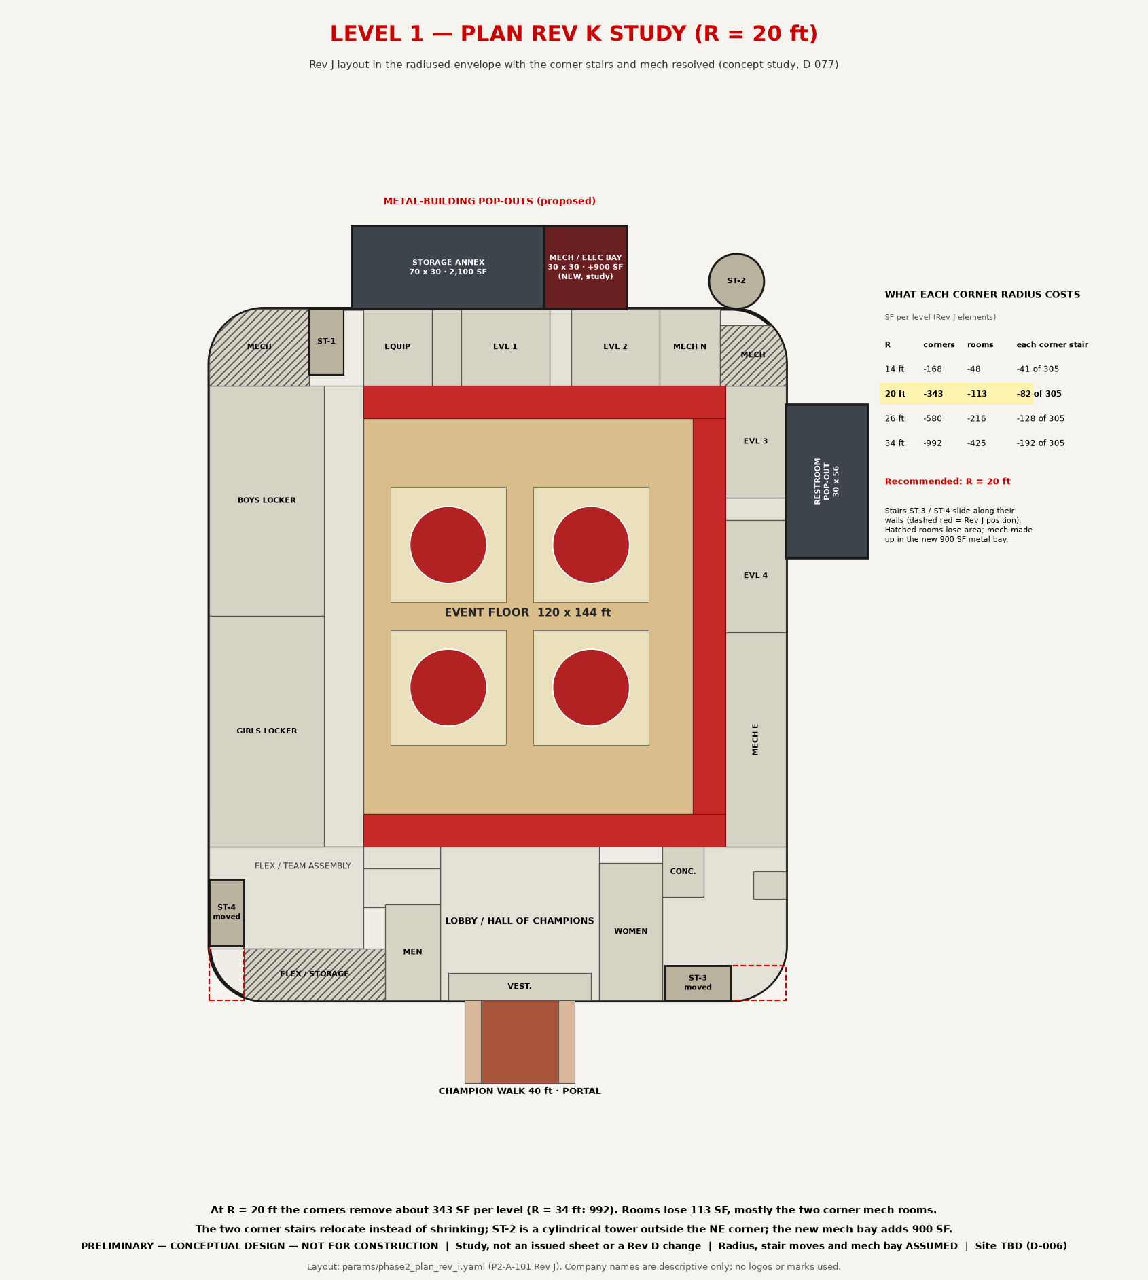
concepts/render_srm_concept_plan_revk_study.png
