thebardchat/TrojanHorseAreana/concepts/render_srm_concept_portal.png

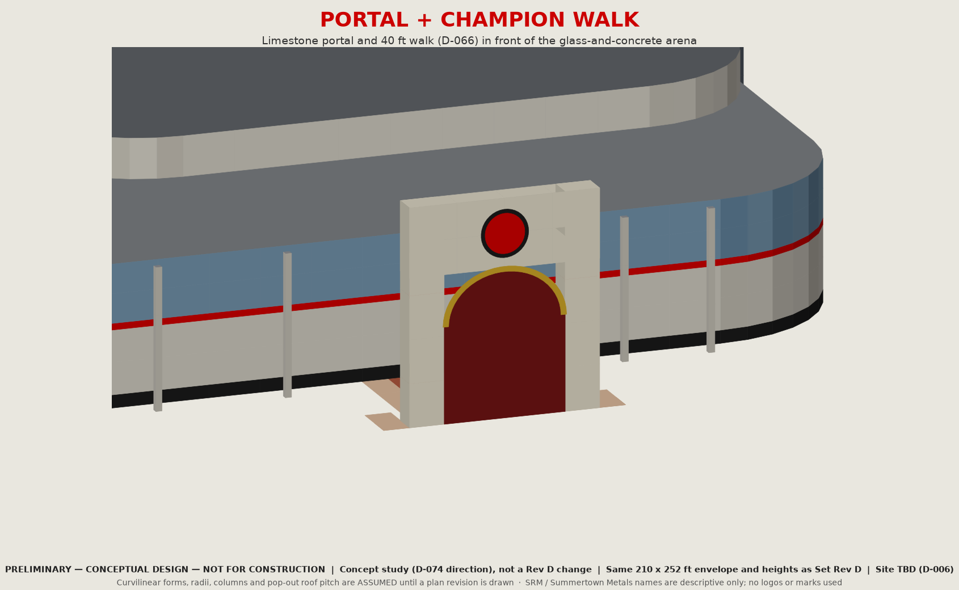
concepts/render_srm_concept_portal.png
