thebardchat/TrojanHorseAreana/render_aerial.png

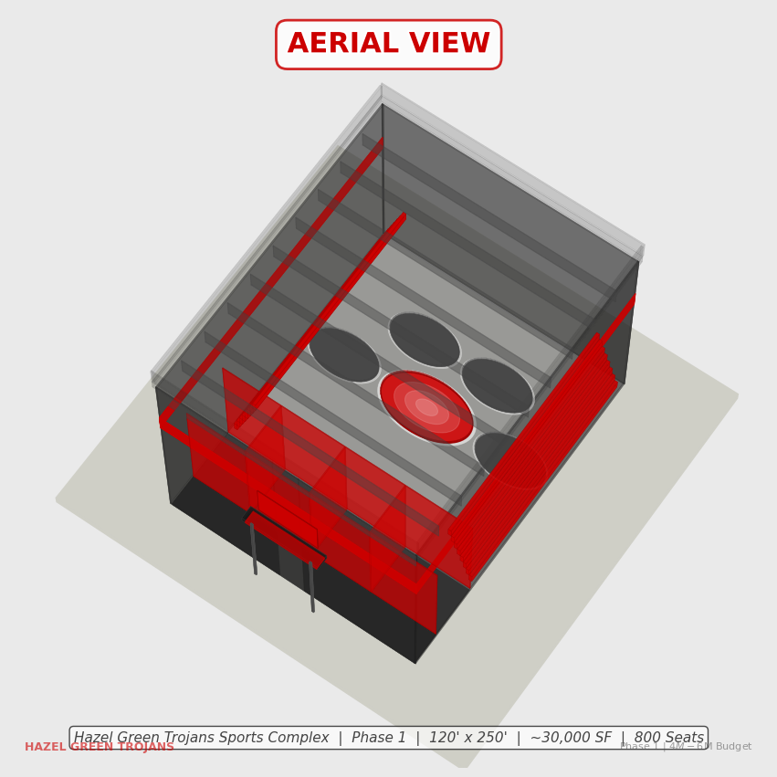
render_aerial.png
