thebardchat/TrojanHorseAreana/render_arena.png

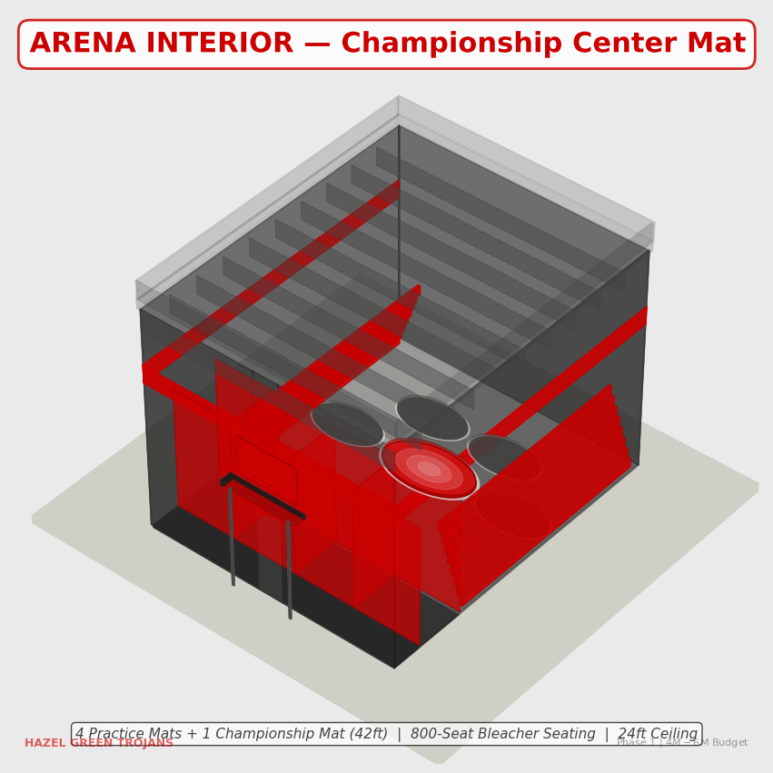
render_arena.png
