thebardchat/TrojanHorseAreana/render_entrance.png

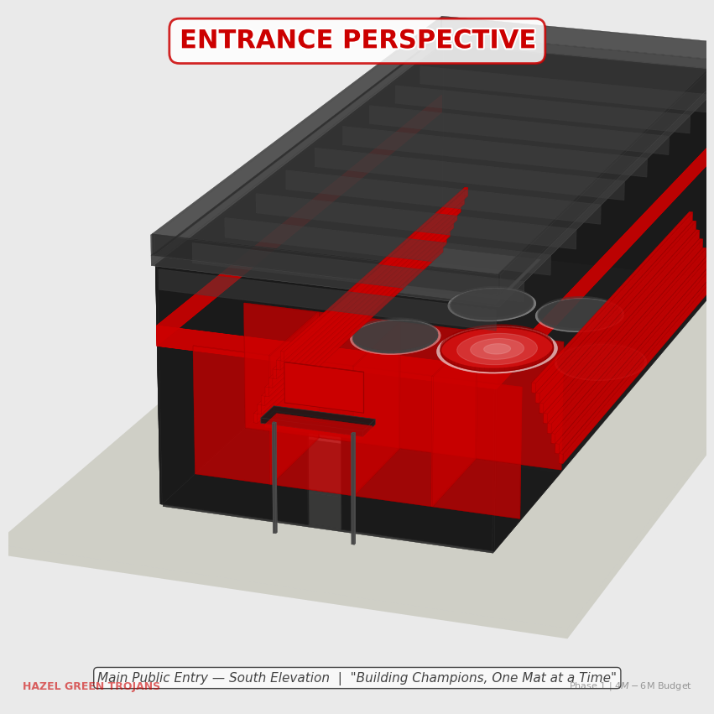
render_entrance.png
