thebardchat/TrojanHorseAreana/render_floorplan_2d.png

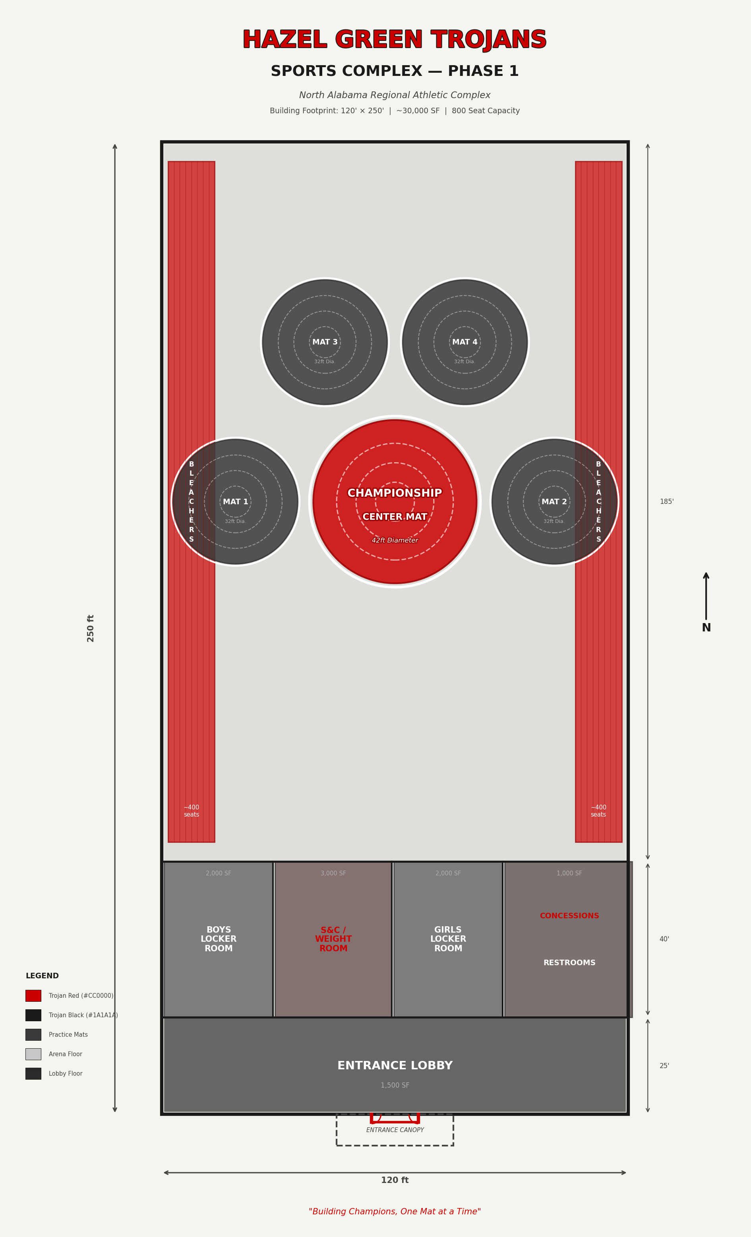
render_floorplan_2d.png
