thebardchat/TrojanHorseAreana/blueprints/phase2/handoff_2026-10-04/P2-G-002_RevD.dxf

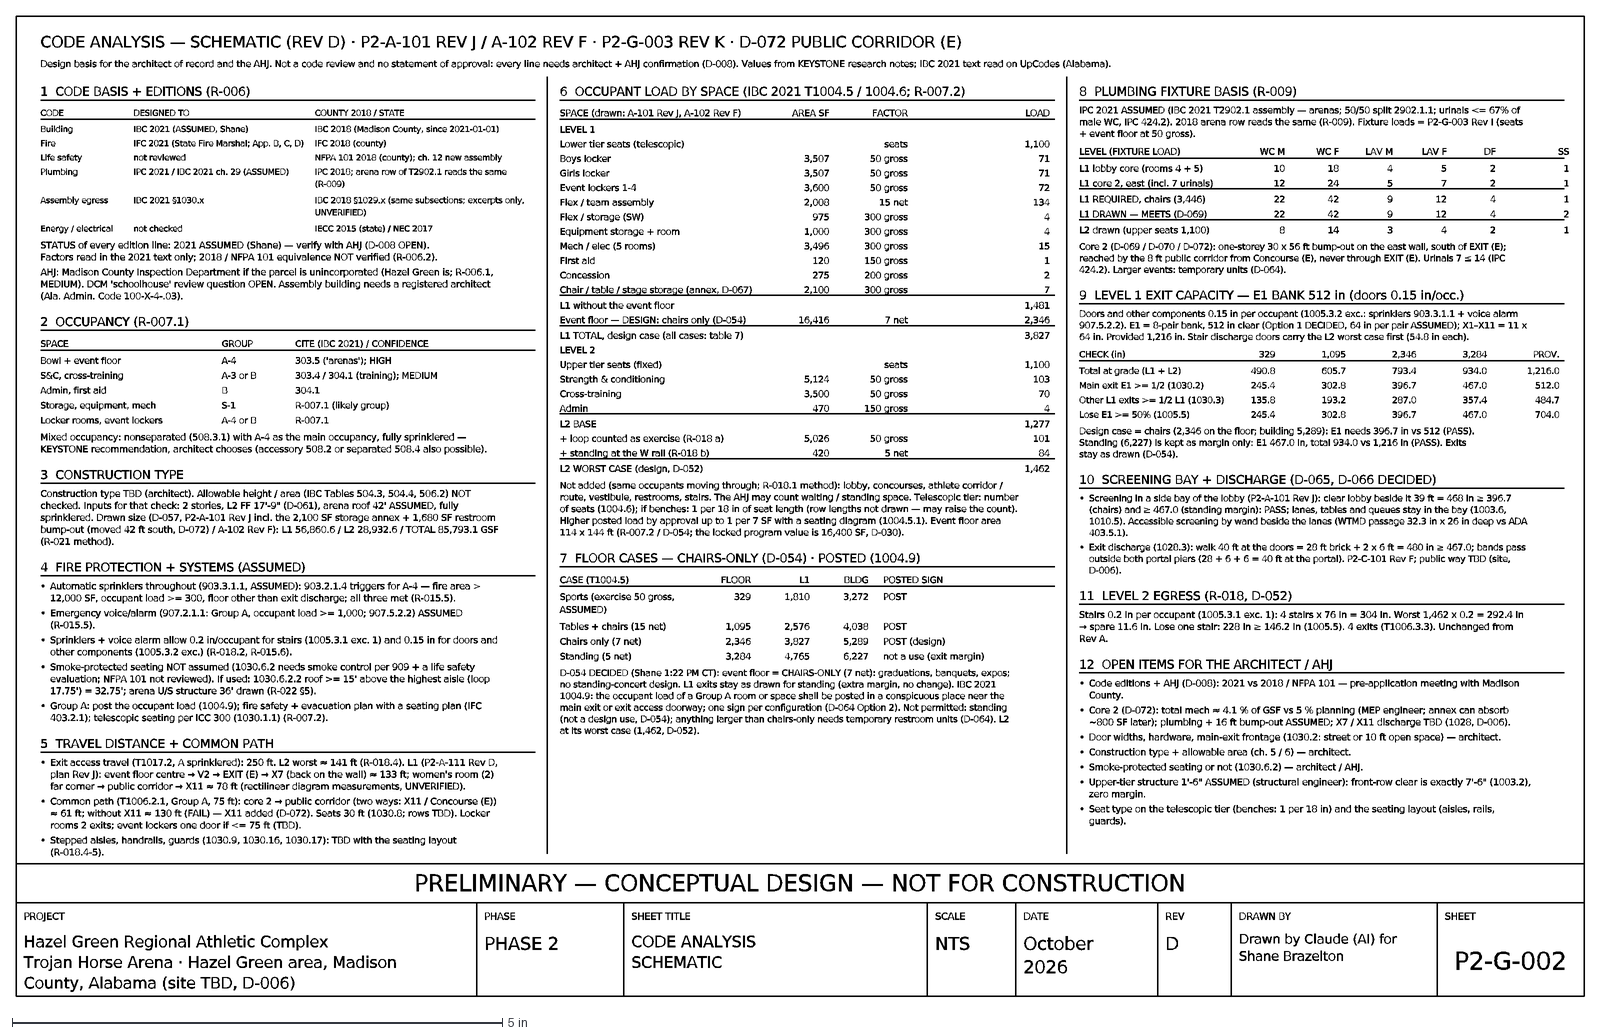
[picture p83: CAD file, 2026-10-05]
blueprints/phase2/handoff_2026-10-04/P2-G-002_RevD.dxf
PRELIMINARY — CONCEPTUAL DESIGN — NOT FOR CONSTRUCTION
PROJECT
Hazel Green Regional Athletic Complex
Trojan Horse Arena · Hazel Green area, Madison
County, Alabama (site TBD, D-006)
PHASE
PHASE 2
SHEET TITLE
CODE ANALYSIS
SCHEMATIC
SCALE
NTS
DATE
October
2026
REV
D
DRAWN BY
Drawn by Claude (AI) for
Shane Brazelton
SHEET
P2-G-002
CODE ANALYSIS — SCHEMATIC (REV D) · P2-A-101 REV J / A-102 REV F · P2-G-003 REV K · D-072 PUBLIC CORRIDOR (E)
Design basis for the architect of record and the AHJ. Not a code review and no statement of approval: every line needs architect + AHJ confirmation (D-008). Val
1 CODE BASIS + EDITIONS (R-006)
CODE
DESIGNED TO
COUNTY 2018 / STATE
Building
IBC 2021 (ASSUMED, Shane)
IBC 2018 (Madison County, since 2021-01-01)
Fire
IFC 2021 (State Fire Marshal; App. B, C, D)
IFC 2018 (county)
Life safety
not reviewed
NFPA 101 2018 (county); ch. 12 new assembly
Plumbing
IPC 2021 / IBC 2021 ch. 29 (ASSUMED)
IPC 2018; arena row of T2902.1 reads the same
(R-009)
Assembly egress
IBC 2021 §1030.x
IBC 2018 §1029.x (same subsections; excerpts only,
UNVERIFIED)
Energy / electrical
not checked
IECC 2015 (state) / NEC 2017
STATUS of every edition line: 2021 ASSUMED (Shane) — verify with AHJ (D-008 OPEN).
Factors read in the 2021 text only; 2018 / NFPA 101 equivalence NOT verified (R-006.2).
AHJ: Madison County Inspection Department if the parcel is unincorporated (Hazel Green is; R-006.1,
MEDIUM). DCM 'schoolhouse' review question OPEN. Assembly building needs a registered architect
(Ala. Admin. Code 100-X-4-.03).
2 OCCUPANCY (R-007.1)
SPACE
GROUP
CITE (IBC 2021) / CONFIDENCE
Bowl + event floor
A-4
303.5 ('arenas'); HIGH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
