thebardchat/TrojanHorseAreana/blueprints/phase2/out/dxf/P2-G-003_RevK.dxf

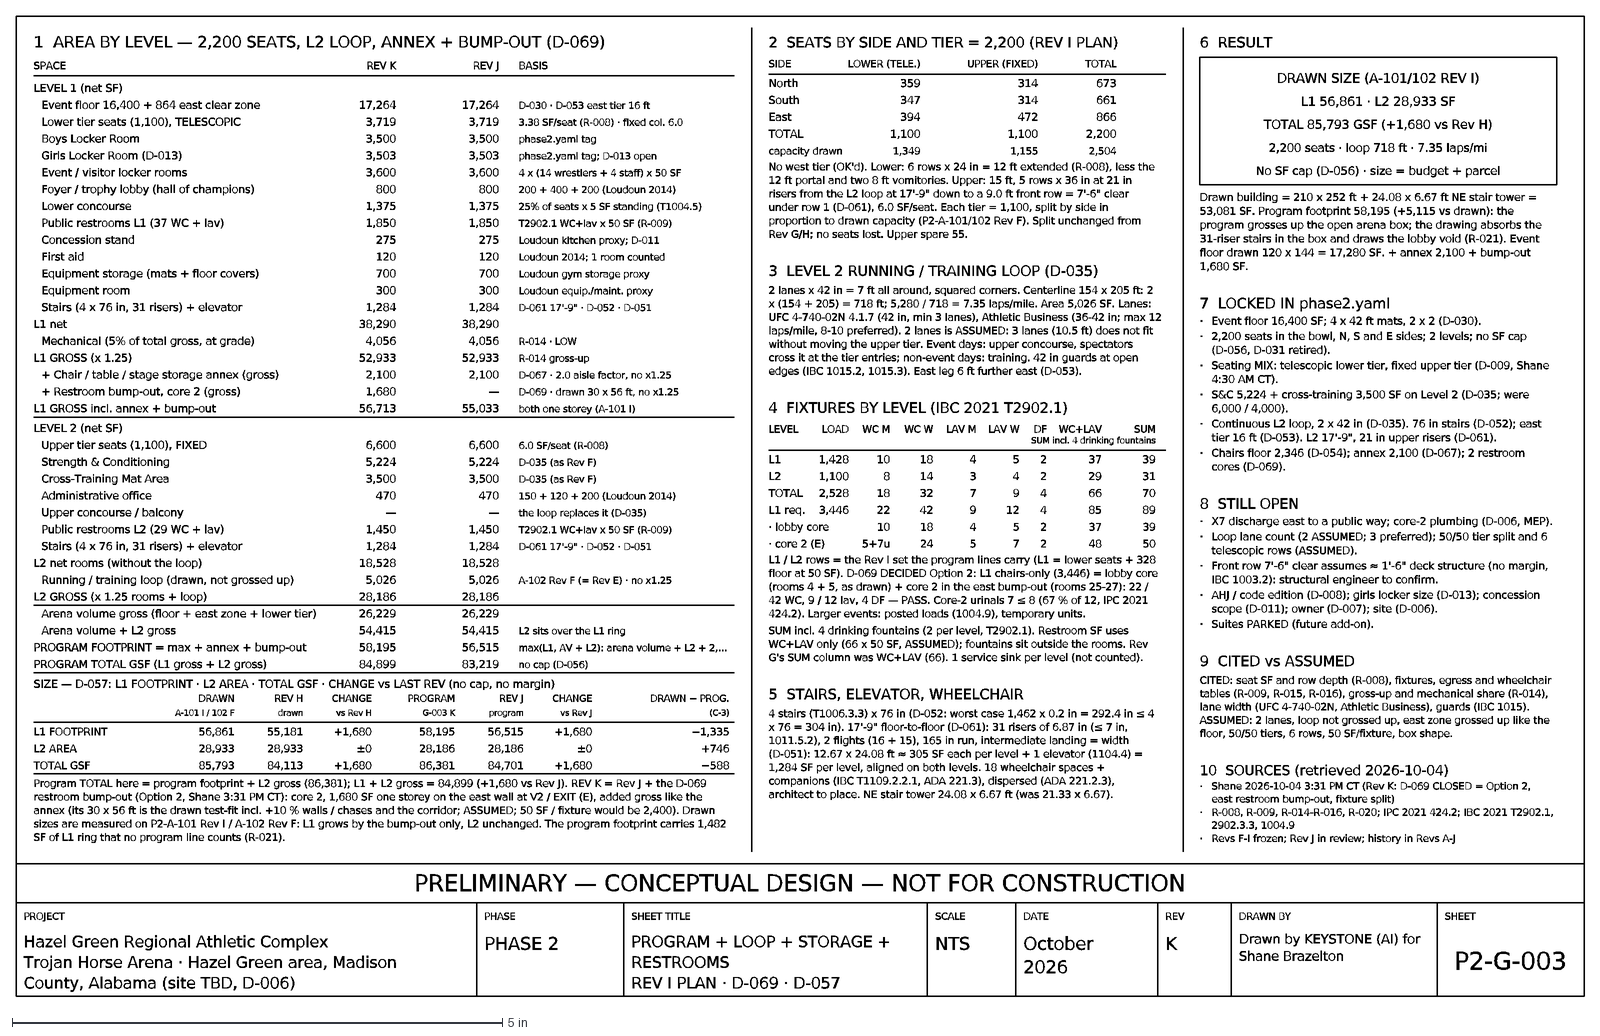
[picture p85: CAD file, 2026-10-05]
blueprints/phase2/out/dxf/P2-G-003_RevK.dxf
PRELIMINARY — CONCEPTUAL DESIGN — NOT FOR CONSTRUCTION
PROJECT
Hazel Green Regional Athletic Complex
Trojan Horse Arena · Hazel Green area, Madison
County, Alabama (site TBD, D-006)
PHASE
PHASE 2
SHEET TITLE
PROGRAM + LOOP + STORAGE +
RESTROOMS
REV I PLAN · D-069 · D-057
SCALE
NTS
DATE
October
2026
REV
K
DRAWN BY
Drawn by KEYSTONE (AI) for
Shane Brazelton
SHEET
P2-G-003
1 AREA BY LEVEL — 2,200 SEATS, L2 LOOP, ANNEX + BUMP-OUT (D-069)
SPACE
REV K
REV J
BASIS
LEVEL 1 (net SF)
Event floor 16,400 + 864 east clear zone
17,264
D-030 · D-053 east tier 16 ft
Lower tier seats (1,100), TELESCOPIC
3,719
3.38 SF/seat (R-008) · fixed col. 6.0
Boys Locker Room
3,500
phase2.yaml tag
Girls Locker Room (D-013)
3,503
phase2.yaml tag; D-013 open
Event / visitor locker rooms
3,600
4 x (14 wrestlers + 4 staff) x 50 SF
Foyer / trophy lobby (hall of champions)
800
200 + 400 + 200 (Loudoun 2014)
Lower concourse
1,375
25% of seats x 5 SF standing (T1004.5)
Public restrooms L1 (37 WC + lav)
1,850
T2902.1 WC+lav x 50 SF (R-009)
Concession stand
275
Loudoun kitchen proxy; D-011
First aid
120
Loudoun 2014; 1 room counted
Equipment storage (mats + floor covers)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
