thebardchat/TrojanHorseAreana/blueprints/phase2/out/dxf/P2-A-101_RevH.dxf

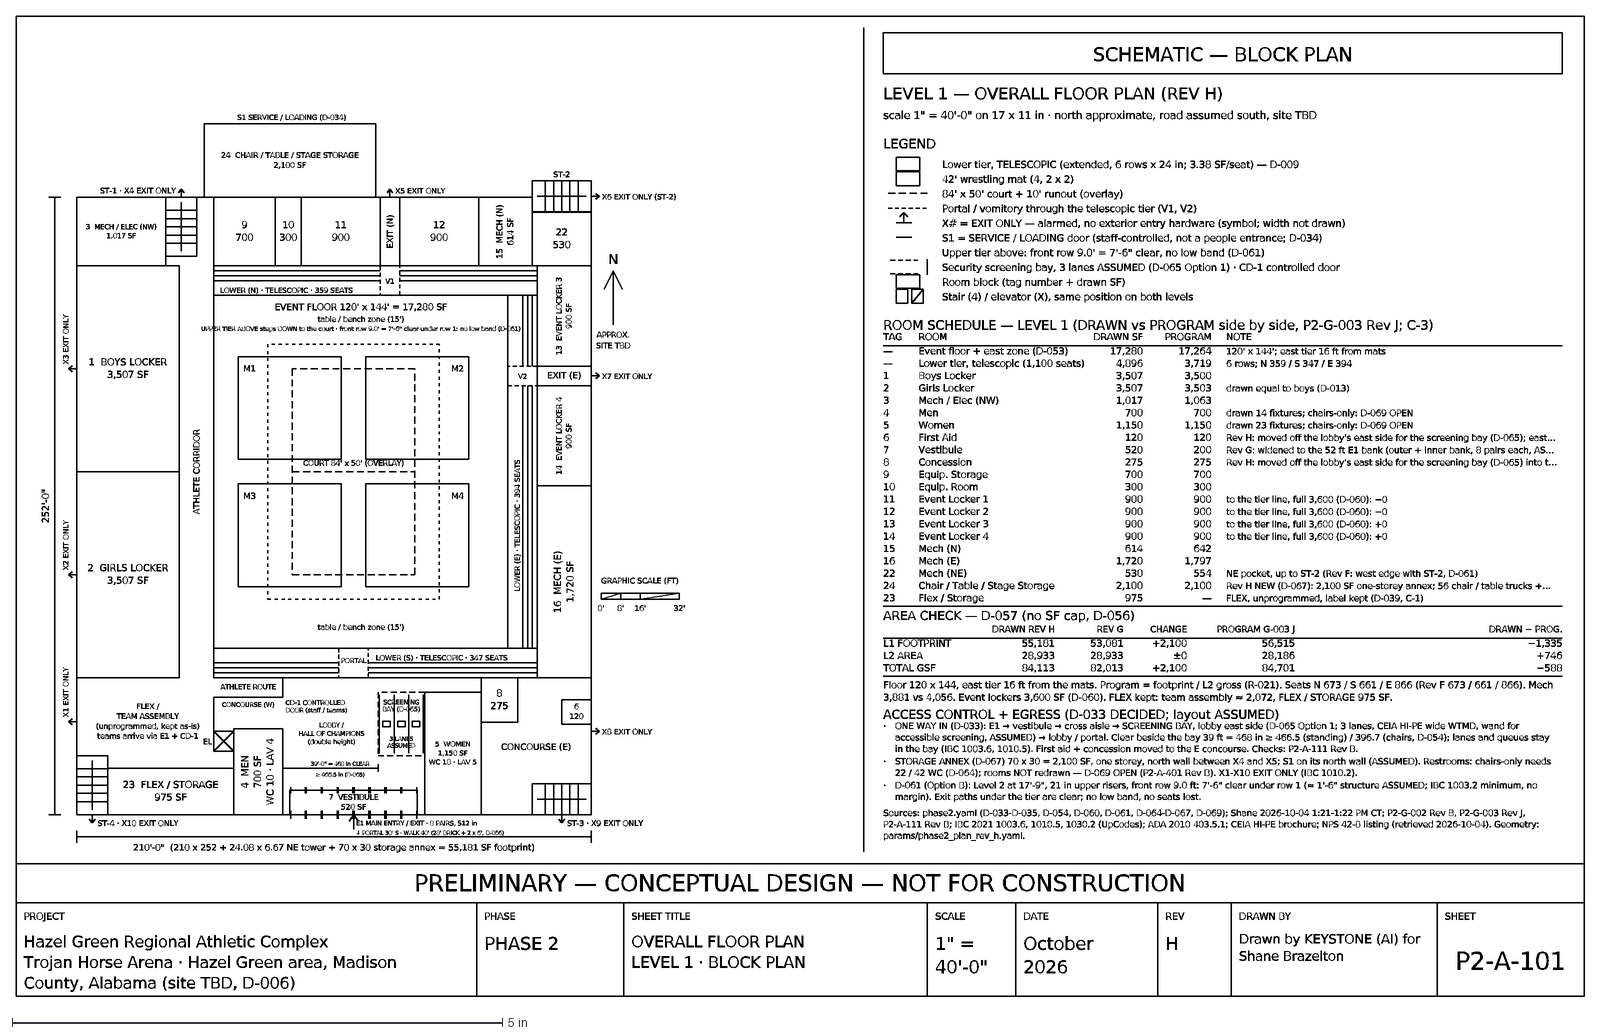
[picture p87: CAD file, 2026-10-05]
blueprints/phase2/out/dxf/P2-A-101_RevH.dxf
PRELIMINARY — CONCEPTUAL DESIGN — NOT FOR CONSTRUCTION
PROJECT
Hazel Green Regional Athletic Complex
Trojan Horse Arena · Hazel Green area, Madison
County, Alabama (site TBD, D-006)
PHASE
PHASE 2
SHEET TITLE
OVERALL FLOOR PLAN
LEVEL 1 · BLOCK PLAN
SCALE
1" =
40'-0"
DATE
October
2026
REV
H
DRAWN BY
Drawn by KEYSTONE (AI) for
Shane Brazelton
SHEET
P2-A-101
210'-0" (210 x 252 + 24.08 x 6.67 NE tower + 70 x 30 storage annex = 55,181 SF footprint)
252'-0"
LOWER (N) · TELESCOPIC · 359 SEATS
LOWER (S) · TELESCOPIC · 347 SEATS
LOWER (E) · TELESCOPIC · 394 SEATS
PORTAL
V1
V2
M1
M2
M3
M4
EVENT FLOOR 120' x 144' = 17,280 SF
table / bench zone (15')
COURT 84' x 50' (OVERLAY)
UPPER TIER ABOVE steps DOWN to the court · front row 9.0' = 7'-6" clear under row 1: no low band (D-061)
E1 MAIN ENTRY / EXIT · 8 PAIRS, 512 in
↓ PORTAL 30' S · WALK 40' (28' BRICK + 2 x 6', D-066)
SCREENING
BAY (D-065)
3 LANES
ASSUMED
39'-0" = 468 in CLEAR
≥ 466.5 in (D-065)
CD-1 CONTROLLED
DOOR (staff / teams)
X1 EXIT ONLY
X2 EXIT ONLY
X3 EXIT ONLY
X5 EXIT ONLY
X7 EXIT ONLY
X8 EXIT ONLY
S1 SERVICE / LOADING (D-034)
1 BOYS LOCKER
3,507 SF
2 GIRLS LOCKER
3 MECH / ELEC (NW)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
