thebardchat/TrojanHorseAreana/blueprints/phase2/out/pdf/P2-A-201_RevA.pdf

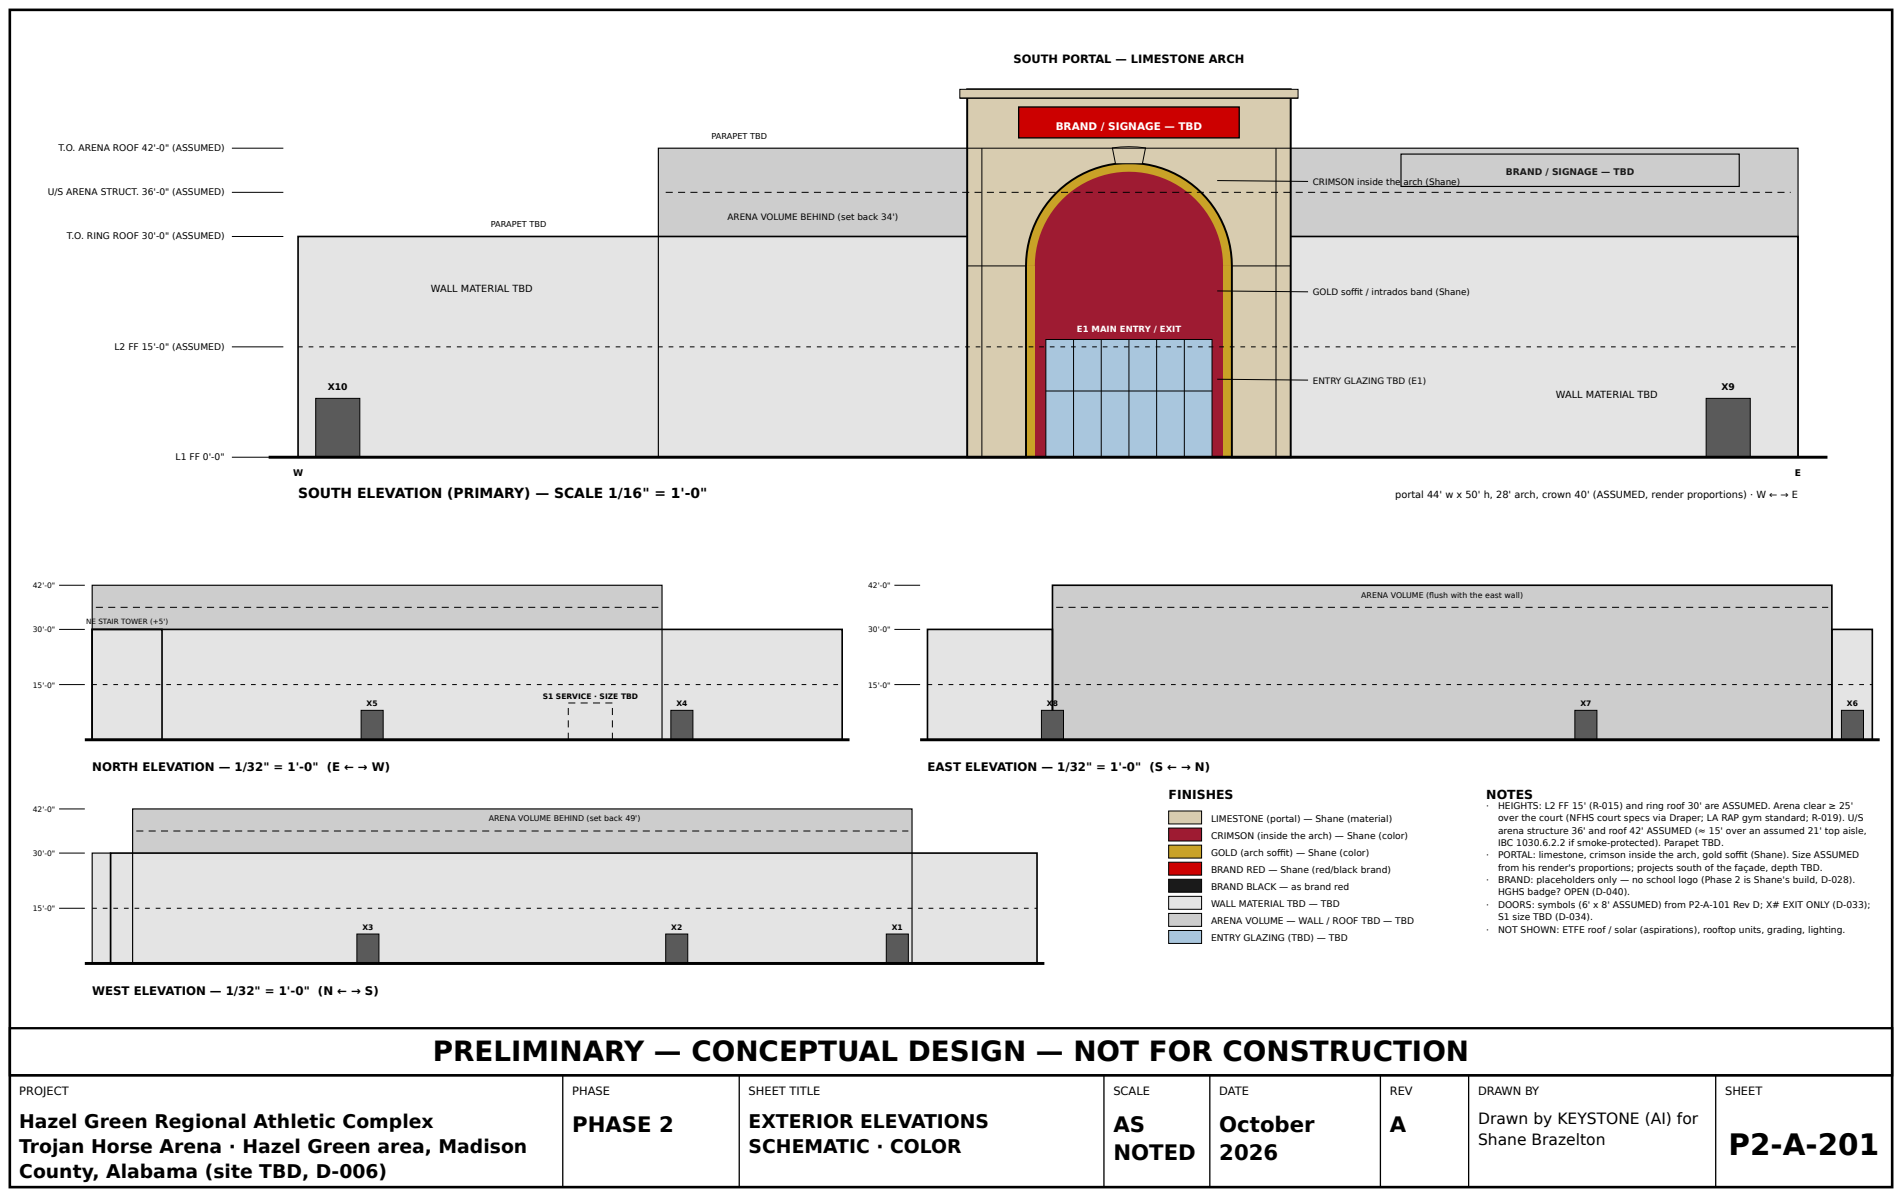
[picture p89: page 1]
PHASE PHASE 2; SHEET TITLE EXTERIOR ELEVATIONS SCHEMATIC · COLOR; SCALE AS NOTED; DATE October 2026; REV A; SHEET P2-A-201; L2 FF 15'-0" (ASSUMED); PARAPET TBD; SOUTH ELEVATION (PRIMARY) — SCALE 1/16" = 1'-0"; portal 44' w x 50' h, 28' arch, crown 40' (ASSUMED, render proportions) · W ← → E; NORTH ELEVATION — 1/32" = 1'-0" (E ← → W); EAST ELEVATION — 1/32" = 1'-0" (S ← → N); WEST ELEVATION — 1/32" = 1'-0" (N ← → S); FINISHES

SOUTH PORTAL — LIMESTONE ARCH

BRAND / SIGNAGE — TBD

T.O. ARENA ROOF 42'-0" (ASSUMED)

CRIMSON inside the arch (Shane)

U/S ARENA STRUCT. 36'-0" (ASSUMED)

ARENA VOLUME BEHIND (set back 34')

T.O. RING ROOF 30'-0" (ASSUMED)

WALL MATERIAL TBD

GOLD soffit / intrados band (Shane)

E1 MAIN ENTRY / EXIT

ENTRY GLAZING TBD (E1)

ARENA VOLUME (flush with the east wall)

NE STAIR TOWER (+5')

S1 SERVICE · SIZE TBD

NOTES
· HEIGHTS: L2 FF 15' (R-015) and ring roof 30' are ASSUMED. Arena clear ≥ 25'
over the court (NFHS court specs via Draper; LA RAP gym standard; R-019). U/S
arena structure 36' and roof 42' ASSUMED (≈ 15' over an assumed 21' top aisle,
IBC 1030.6.2.2 if smoke-protected). Parapet TBD.
· PORTAL: limestone, crimson inside the arch, gold soffit (Shane). Size ASSUMED
from his render's proportions; projects south of the façade, depth TBD.
· BRAND: placeholders only — no school logo (Phase 2 is Shane's build, D-028).
HGHS badge? OPEN (D-040).
· DOORS: symbols (6' x 8' ASSUMED) from P2-A-101 Rev D; X# EXIT ONLY (D-033);
S1 size TBD (D-034).
· NOT SHOWN: ETFE roof / solar (aspirations), rooftop units, grading, lighting.

ARENA VOLUME BEHIND (set back 49')

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

PRELIMINARY — CONCEPTUAL DESIGN — NOT FOR CONSTRUCTION

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

DRAWN BY
Drawn by KEYSTONE (AI) for
Shane Brazelton
